Cable89/tesla-driver/01_Documentation/Forenklet skjema/Spolerigg3_r.pdf

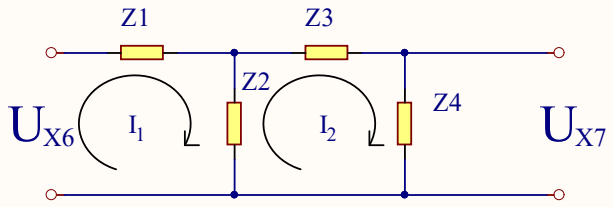
[picture p2: figure]
