Cable89/tesla-driver/01_Documentation/Figurer/IMG_20141220_205741.jpg

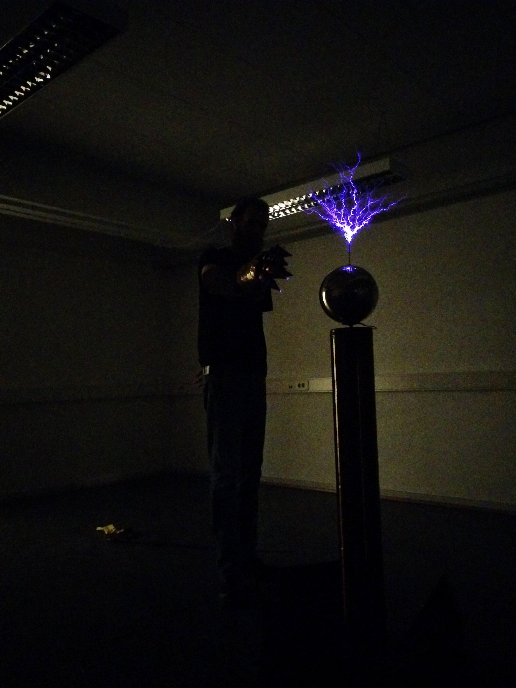
01_Documentation/Figurer/IMG_20141220_205741.jpg
