Cable89/tesla-driver/01_Documentation/Figurer/IMG_20170201_172204.jpg

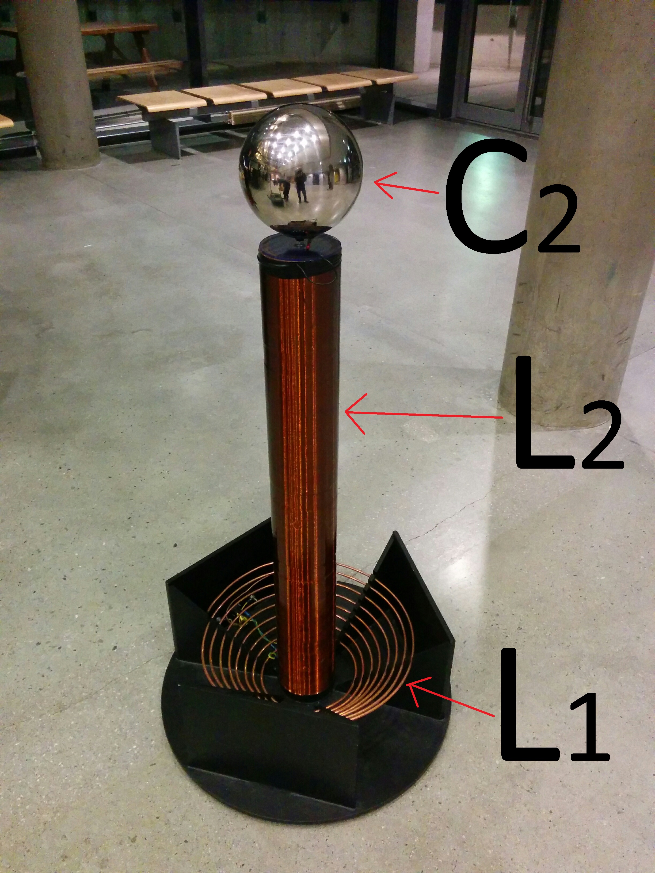
01_Documentation/Figurer/IMG_20170201_172204.jpg
