Cable89/tesla-driver/01_Documentation/Figurer/TK514_Interrupter.png

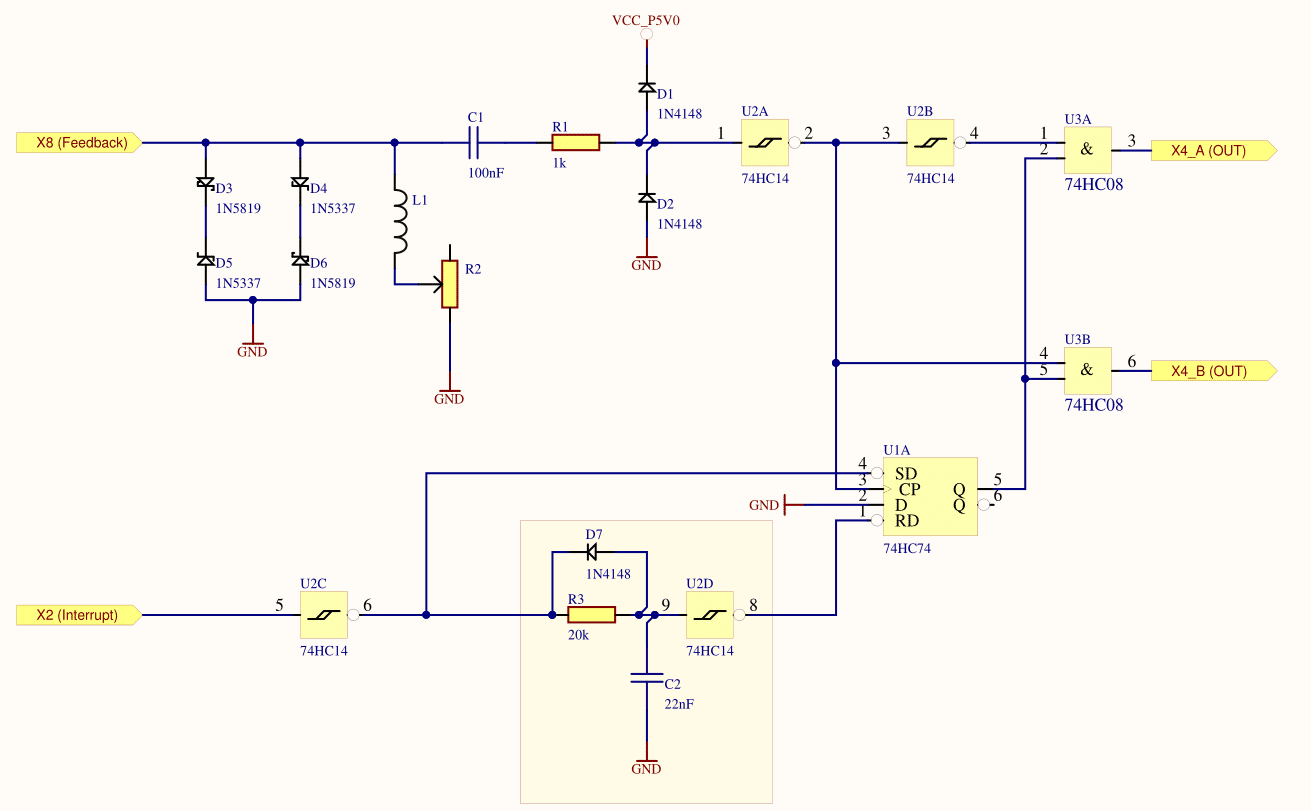
01_Documentation/Figurer/TK514_Interrupter.png
