Cable89/tesla-driver/01_Documentation/Målinger/IMG_20160618_142037.jpg

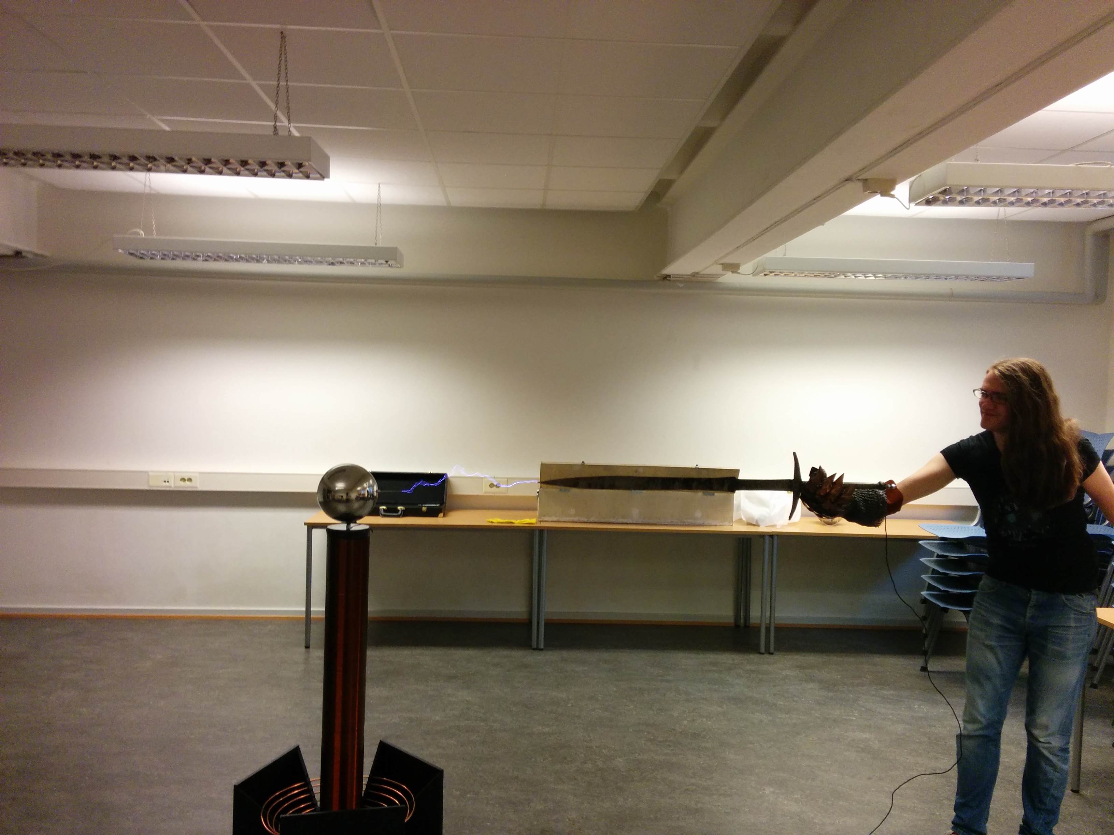
01_Documentation/Målinger/IMG_20160618_142037.jpg
