Cable89/tesla-driver/01_Documentation/Målinger/IMG_20160618_151454.jpg

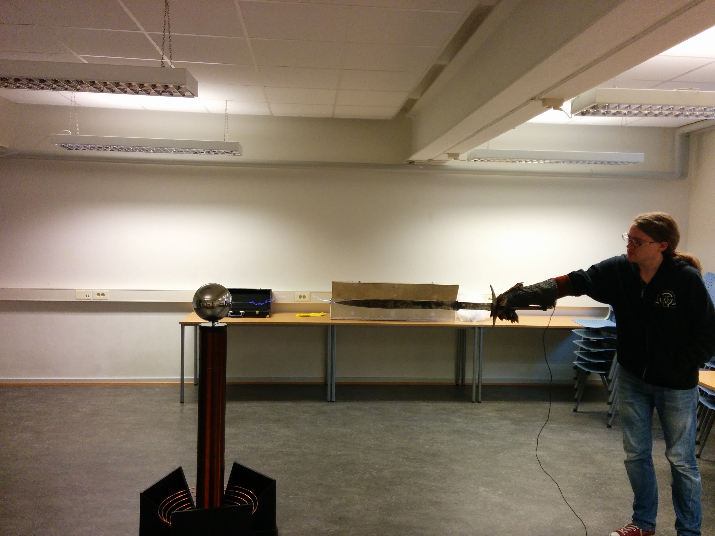
01_Documentation/Målinger/IMG_20160618_151454.jpg
