Cable89/tesla-driver/05_Hardware/TK500_Driver/TK500_Driver/Project Outputs/TK500_BOM.PDF

Line # | id | navn | Description | Designator | ModuleAssembly | Quantity | produsent | leverandor | leverandor_varenr | Manufacturer 1 | Manufacturer Part Number 1 | Manufacturer Lifecycle 1 | Supplier 1 | Supplier Part Number 1 | Supplier Unit Price 1 | Supplier Subtotal 1
| 4153 | 100nF | 2kV(kanskje) polypropylene film
| | | capacitor, D22, L50 | C1, C2, C3, C4 | TK532_Kondensatorkort.P
| | | | | cbDoc | | 4 Cornell
| | | | | | | Dubilier | Farnell | 2347676
5152 | 100nF | X7R 50V 5% | C1, C2, C3, C4, C5, C6, C7, C8, C9, C10, C11, C12, C53000 | TK513_Limiter.PcbDoc, TK514_Interrupter.PcbDoc , TK516_LINREG-PSU.PcbDoc, TK512_Optisk_Mottaker.P cbDoc, TK530_Kraftbakplan.PcbD oc | 22 Multicomp | Farnell | 1759122
3290 | 330uF | 25V elektrolytt | C1, C6 | TK516_LINREG-PSU.PcbDoc | 6 Rubycon | Farnell | 2346202
3687 | 1nF | X7R 50V 5% | C2, C3, C4 | TK513_Limiter.PcbDoc, TK512_Optisk_Mottaker.P cbDoc | 3 Multicomp | Farnell | 2310598
3316 | 220nF | X7R 25V 10% | C2, C8 | TK516_LINREG-PSU.PcbDoc | 6 Samsung | Farnell | 3013426
5154 | 1uF | X7R 50V | C2, C10, C11 | TK512_Optisk_Mottaker.P cbDoc, TK514_Interrupter.PcbDoc | 3 Multicomp | Farnell | 1759454
5155 | 47pF | NP0 50V 5% | C3 | TK512_Optisk_Mottaker.P cbDoc | 1 WALSIN | Farnell | 2496905
4164 | 4.7uF | X5R 10V 10% | C4 | TK516_LINREG-PSU.PcbDoc | 3 Samsung | Farnell | 3013462
3114 | 10uF | X5R 6.3V 10% | C5 | TK516_LINREG-PSU.PcbDoc | 3 | Farnell | 2320852
5303 | 1uF | X7R 50V 10% | C5 | TK512_Optisk_Mottaker.P cbDoc | 1 Murata | Farnell | 1735541
4858 | 100uF | 25V 2.5mm pitch | C6 | TK512_Optisk_Mottaker.P cbDoc, TK513_Limiter.PcbDoc | 2 Panasonic | Farnell | 1848439
4844 | 2200uF | 6.3V, Elektrolytt, 5mm lead spacing | C7 | TK516_LINREG-PSU.PcbDoc | 3 Multicomp | Farnell | 2627680
5192 | 22uF | 10V 10% Tantalum | C7 | TK512_Optisk_Mottaker.P cbDoc, TK513_Limiter.PcbDoc | 2 Kemet | Farnell | 1457420
5059 | 10uF | X5R 50V 10% | C13, C14 | TK514_Interrupter.PcbDoc | 2 Murata | Farnell | 2672214
3491 | 22nF | X7R 50V | C15 | TK514_Interrupter.PcbDoc | 1 Multicomp | Farnell | 1414682
3076 | MAL209636222E3 | CAP, ALUELEC, 2200UF, 400V | C52500 | dummy.PcbDoc | 1 Vishay | Farnell | 2342176 | Vishay BCcomponents | MAL209636222E3 | Volume Production | Farnell | 2342176 | 59.86 | 59.86
4891 | 15ETX06 | DIODE, HYPERFAST, 15A, 600V | D1, D2 | TK531_Utgangstrinn.PcbD oc | 4 Vishay | Farnell | 8656991 | Vishay Semiconductors | 15ETX06 | Obsolete
5238 | 1N5819 | Schottkydiode, 1A, 40V | D1, D2, D3, D4, D6 | TK513_Limiter.PcbDoc, TK514_Interrupter.PcbDoc | 6 Multicomp | Farnell | 7429304, 1336533 | Multicomp | 1N5819 | Volume Production
4485 | 1N4148 SMD | SMD signaldiode | D1, D2, D7 | TK514_Interrupter.PcbDoc , TK512_Optisk_Mottaker.P cbDoc | 4 Taiwan Semiconduct or | Farnell | 8150206
5138 | Grønn LED 5mm | LED, Green, 5mm, 572 nm, 2.1 V, 20mA, 150mcd | D1, D3, D4, D6, D7, D9, D10, D12, D13, D15, D16, D18 | TK502_Frontpanel_LEDs.Pc bDoc | 12 Multicomp | Farnell | 2112108
5143 | SMD LED Red | SMD | D1, D3, D51000, D51001, D51002, D51003, D51004, D51005, D51006, D51007, D51008, D51009, D51010, D53000, D53001, D53002 | TK512_Optisk_Mottaker.P cbDoc, TK516_LINREG-PSU.PcbDoc, TK510_Signalbakplan.PcbD oc, TK530_Kraftbakplan.PcbD oc | 19 Avago | Farnell | 8554641
5305 | Rød LED 5mm | LED, Red, 5mm, 643 nm, 1.8 V, 20mA, 400 mcd | D2, D5, D8, D11, D14, D17 | TK502_Frontpanel_LEDs.Pc bDoc | 6 Multicomp | Farnell | 2112111
3261 | 1V5KE400A | TVS diode, 400V, 1500W | D3, D4 | TK531_Utgangstrinn.PcbD oc | 4 Fairchild | Farnell | 1017630 | ON Semiconductor / Fairchild | 1V5KE400A | Volume Production
3264 | 1N5337 | Zenerdiode 4.7V 5W | D4, D5 | TK514_Interrupter.PcbDoc | ON 2 Semiconduct or | Farnell | 9557946
4876 | 1N4744A | Zenerdiode 15V 1.3W | D5, D6, D7, D8 | TK531_Utgangstrinn.PcbD oc | 8 Vishay | Farnell | 1612369 | Vishay Semiconductors | 1N4744A | Volume Production | Farnell | 1612368 | 0.12722 | 1.02
3322 3117 5314 | GBJ2504 LED Rød SMBJ5.0A-TR | diodebro/Likeretterbro 400V 25A Farget LED, 5mm Transient Voltage Suppressor, TVS, Transil SMBJ Series, Unidirectional, 5 V, SMD, 2, 6.4 V | D52500 D52501 D53003 | dummy.PcbDoc dummy.PcbDoc TK530_Kraftbakplan.PcbD oc | 1 1 -1 ST Microelectron ics | Farnell Farnell | 1651042 9886311 | STMicroelectronic s | SMBJ5.0A-TR | Volume Production | Farnell | 9886311 | 0.52175 | 2.61
5311 2977 | MC36214 Automatsikring | FUSE, PTC RESET, SMD, 16V, 500MA 2-Pol | F53000, F53001 F1 | TK530_Kraftbakplan.PcbD dummy.PcbDoc oc | 1 ABB 2 Multicomp | Farnell Farnell | 2492800 1861181 | Multicomp | MC36214 | Volume Production
3037 | PCIeX1-GF-2D-1000-1K-O36 | PCI express PCB kortkankonnektor | J1 | TK511_Blindkort.PcbDoc, TK512_Optisk_Mottaker.P cbDoc, TK513_Limiter.PcbDoc, TK514_Interrupter.PcbDoc , TK516_LINREG-PSU.PcbDoc | 8 PCB feature
3221 | MPTC-02-16-02-01-03-L-RA-SD | SAMTEC Connector | J1 | TK531_Utgangstrinn.PcbD oc, TK532_Kondensatorkort.P cbDoc | 3 SAMTEC | Mouser | MPTC-02-16-02-01-03-L-RA-SD | Samtec | MPTC-02-16-02-01-03-L-RA-SD | | Mouser | 200-MPTC0216213LRASD | 8.62 | 25.86
4473 | B3B-XH-A (LF)(SN) | JST 3pin (pris pr. stk.) | J1, J2, J3, J4, J5, J6 | TK502_Frontpanel_LEDs.Pc bDoc | 6 JST | Farnell | 1516277 | JST | B3B-XH-A(LF)(SN) | Volume Production | RSCompone nts | 8201557 | 0.388 | 2.33
3259 | Header 2X17 Shrouded | Header | J2, J7, J51027 | TK511_Blindkort.PcbDoc, TK502_Frontpanel_LEDs.Pc bDoc, TK510_Signalbakplan.PcbD oc | 4 Amphenol | Farnell | 2215313
5095 3222 | Header 1x3 PCI_Express-36P | 2,54mm pitch PCI_Express-36P | J3, J4, J5, J6, J7 J51000, J51001, J51002, J51003, J51004, J51005, J51007, J51008, J51028 | TK511_Blindkort.PcbDoc TK510_Signalbakplan.PcbD oc | 10 SAMTEC 9 FCI | Farnell Farnell | 3690124 1144435
4043 | B2B-XH-A (LF)(SN) | JST 2pin (pris pr. stk.) | J51006, J51012, J51013, J51014, J51015, J51016, J51017, J51021, J51022, J51023, J51024, J51025, J51026, J51029, J51030, J51031, J51032, J51033, J51034, J51035, J51036, J51037, J51038, J51039, J51040, J51041, J51042, J51043, J51044, J51045, J51046, J51047, J51048, J51049, J51050, J52001, J53006, J53008 | TK510_Signalbakplan.PcbD oc, TK520_GDT-Trafo.PcbDoc, TK530_Kraftbakplan.PcbD oc | 38 JST | Farnell | 1516276 | JST | B2B-XH-A(LF)(SN) | Volume Production | RSCompone nts | 8201554 | 0.204 | 7.75
3224 | Header 2X5 Shrouded | Header | J51009, J51010, J51011, J51018, J51019, J51020, J53007 | TK510_Signalbakplan.PcbD oc, TK530_Kraftbakplan.PcbD oc | 7 Amphenol | Farnell | 2215304
3046 | B4B-XH-A (LF)(SN) | JST 4pin (pris pr. stk.) | J52000, J52002, J53003, J53004, J53005 | TK520_GDT-Trafo.PcbDoc, TK530_Kraftbakplan.PcbD oc | 5 JST | Farnell | 1516278 | JST | B4B-XH-A -LF-SN
3220 | MPSC-02-16-02-7.70-03-L-V-LC | SAMTEC Connector | J53000, J53001, J53002 | TK530_Kraftbakplan.PcbD oc | 3 SAMTEC | Mouser | MPSC-02-16-02-7.70-03-L-V-LC | Samtec | MPSC-02-16-02-7.70-03-L-V-LC | | Mouser | 200-C02160277003LVLC | 9.91 | 29.73
3646 | 0R | 0.1W 1% Thick film resistor, Jumper | JP1, R3, R4, R13, R14, R23, R24 | TK516_LINREG-PSU.PcbDoc, TK502_Frontpanel_LEDs.Pc bDoc, TK512_Optisk_Mottaker.P cbDoc | 10 multicomp | Farnell | 2447060
3272 | DIN-Rele 5V | Coil: 5VDC, Contact: 250VAC 6A, DIN mount | K1, K52501 | dummy.PcbDoc | 2 ABB | Farnell | 1895933
2948 6201 | Kontaktor Spole 15H | Industriellt rele Wirewound Inductor, 15 µH, 2.8 ohm, 20 MHz, 130mA | K2 L1 | dummy.PcbDoc TK512_Optisk_Mottaker.P cbDoc, TK514_Interrupter.PcbDoc | 1 IMO 2 TDK | Farnell Farnell | 9940480 2747875
3842 4718 | Skilletrafo 2:1 SK-454-75-SA | Skilletrafo Ringkjerne Heatsink | L52501 M1 | dummy.PcbDoc TK531_Utgangstrinn.PcbD oc | 1 Hammond 2 FischerElektr onik | Farnell Farnell | 2546942 1850030
3273 | Lask til 2.5mm2 Rekkeklemme 10way | Jumper (Busbar), Cross Jumper, DIN Rail Screw Clamp Terminal Blocks, 10 Ways | M1, M2 | dummy.PcbDoc | 2 Multicomp | Farnell | 2061384
6258 | Automasjonsbryter holder | Assembly Hardware, Siemens 3-Way Modules, Holder, SIRIUS ACT 3SU Series | M3, M4, M5, M6, M7 | dummy.PcbDoc | 5 Siemens | Farnell | 2695729
3242 | KortStøtte 84mm | Støtter kort i bakplan | M51000, M51001, M51002, M51003, M51004, M51005, M51006, M51007, M51008, M51009, M51010, M51011, M51012, M51013, M51014, M51015, M51016, M51017 | TK510_Signalbakplan.PcbD oc | 18
4028 | KortStøtte 50mm | Støtter kort i bakplan | M53000, M53001, M53002, M53003, M53004, M53005 | TK530_Kraftbakplan.PcbD oc | 6
4877 | G4PC50W | IGBT, 600V, 55A | Q1, Q2 | TK531_Utgangstrinn.PcbD oc | 4 International Rectifier | Farnell | 8650632 | International Rectifier | G4PC50W
3085 | BSH201 | P-Channel MOSFET 300mA | Q1, Q2, Q3, Q5, Q51003, Q51004, Q51005, Q51009, Q51010, Q51011, Q51016, Q51017, Q51018, Q51020, Q51021, Q53003, Q53004, Q53005 | TK514_Interrupter.PcbDoc , TK513_Limiter.PcbDoc, TK512_Optisk_Mottaker.P cbDoc, TK510_Signalbakplan.PcbD oc, TK530_Kraftbakplan.PcbD oc | NXP 19 Semiconduct ors | Farnell | 1758073 | NXP Semiconductors | BSH201
3075 | 2N7002 | N-Channel MOSFET 300mA | Q1, Q4, Q51000, Q51001, Q51002, Q51006, Q51007, Q51008, Q51012, Q51013, Q51014, Q51015, Q51019, Q53000, Q53001, Q53002 | TK513_Limiter.PcbDoc, TK512_Optisk_Mottaker.P cbDoc, TK510_Signalbakplan.PcbD oc, TK530_Kraftbakplan.PcbD oc | 16 Nexperia, [NoParam] | Farnell | 1829184 | NXP Semiconductors | 2N7002
5228 | 560R | 0.1W 1% Thick film resistor | R1 | TK516_LINREG-PSU.PcbDoc | 3 Multicomp | Farnell | 2447397
3890 | 10 | 0.25W 1% Generic resistor | R1, R2 | TK531_Utgangstrinn.PcbD oc | 4 Multicomp | Farnell | 9341145
6251 | 100R | 100Ohm, 100W Resistor, Solder Lug, Wirewound +-5% 1.9kV | R1, R2 | dummy.PcbDoc | 2 TT electronics | Farnell | 1768214
5264 | 10k | 0.1W 1% Thick film resistor | R1, R2, R11, R12, R21, R22, R51000, R51001, R51002, R51003, R51004, R51005, R51006, R51010, R51011, R51012, R51013, R51014, R51015, R51016, R51017, R51021, R51022, R51023, R51024, R51025, R51026, R51027, R51028, R51029, R51030, R51031, R51032, R51033, R51034, R51035, R51036, R51037, R51038, R51039, R51040, R51041, R51042, R51043, R53000, R53001, R53002, R53006 | TK502_Frontpanel_LEDs.Pc bDoc, TK512_Optisk_Mottaker.P cbDoc, TK510_Signalbakplan.PcbD oc, TK530_Kraftbakplan.PcbD oc | 49 Multicomp | Farnell | 2447230
5339 | 1k | 0.1W 1% Thick film resistor | R1, R3 | TK513_Limiter.PcbDoc, TK514_Interrupter.PcbDoc | 3 Multicomp | Farnell | 2447272
5040 | 10R | 0.1W 1% Thick film resistor | R2 | TK514_Interrupter.PcbDoc | 1 Multicomp | Farnell | 2447556
5657 5343 | 10R 330R | 0.1W 1% Thick film resistor 0.1W 1% Thick film resistor | R2 R2, R5, R6, R7, R8, R9, R10, R15, R16, R17, R18, R19, R20, R25, R26, R27, R28, R29, R30, R51007, R51008, R51009, R51018, R51019, R51020, R51044, R51045, R51046, R51047, R51048, R51049 | TK513_Limiter.PcbDoc TK512_Optisk_Mottaker.P cbDoc, TK502_Frontpanel_LEDs.Pc bDoc, TK510_Signalbakplan.PcbD oc | 1 Multicomp 32 Multicomp | Farnell Farnell | 2447233 2447339
5336 | 910R | 0.1W 1% Thick film resistor | R3 | TK512_Optisk_Mottaker.P cbDoc | 1 Multicomp | Farnell | 2447448
5340 | 1M | 0.1W 1% Thick film resistor | R3, R4, R6, R7, R8, R9 | TK531_Utgangstrinn.PcbD oc, TK514_Interrupter.PcbDoc | 8 Multicomp | Farnell | 2073358
5357 | 20k | 0.1W 1% Thick film resistor | R3, R6 | TK514_Interrupter.PcbDoc , TK512_Optisk_Mottaker.P cbDoc | 2 Multicomp | Farnell | 2447293
3823 3778 | Trimmepot 100ohm 100k | 15 turn, horizontal 0.1W 1% Thick film resistor | R4, R5 R4 | TK514_Interrupter.PcbDoc TK513_Limiter.PcbDoc , TK513_Limiter.PcbDoc | 1 Multicomp 2 Bourns | Farnell Farnell | 2447226 9352279
5347 | 15k | 0.1W 1% Thick film resistor | R5 | TK512_Optisk_Mottaker.P cbDoc | 1 Multicomp | Farnell | 2447226
3759 4889 | 16k 47R | 0.25W 1% Generic resistor 0.1W 1% Thick film resistor | R52502 R53003, R53004, R53005 | dummy.PcbDoc TK530_Kraftbakplan.PcbD oc | 1 3 Multicomp | Farnell | 2447378
6252 | Automasjonsvelger Grønn | Switch Actuator, Siemens 22mm Pushbutton Switches | S1, S3 | dummy.PcbDoc | 2 Siemens | Farnell | 2695623
6257 | Automasjonsbryter NO | Contact Block, SPST-NO, 10 A, 500 V, 1 Pole, 3SU Series, Screw | S1, S3, S3B, S3C | dummy.PcbDoc | 4 Siemens | Farnell | 2695771
6253 | Automasjonsvelger Rød | Switch Actuator, Siemens 22mm Pushbutton Switches | S2 | dummy.PcbDoc | 1 Siemens | Farnell | 2695622
6256 | Automasjonsbryter NC | Contact Block, SPST-NC, 10 A, 500 V, 1 Pole, 3SU Series, Screw | S2, S3B, S4, S4B, S5, S5B | dummy.PcbDoc | 6 Siemens | Farnell | 2695772
6255 | Automasjonsvelger Nødstopp | Switch Actuator, Siemens 22mm Emergency Stop Mushroom Pushbutton Switches | S4 | dummy.PcbDoc | 1 Siemens | Farnell | 2695631
6254 | Automasjonsvelger Vrider bistabil | Switch Actuator, Siemens 22mm Selector Switches | S5 | dummy.PcbDoc | 1 Siemens | Farnell | 2695653
3215 5093 | SD250-3 Header 1x1 | Dual gate drive transformer 2,54mm pitch | T52000, T52001 TP1, TP2, TP3, TP4, TP5, TP6, TP7, TP8 | TK520_GDT-Trafo.PcbDoc TK512_Optisk_Mottaker.P cbDoc, TK513_Limiter.PcbDoc, TK514_Interrupter.PcbDoc | 2 Coilcraft 19 | | | Coilcraft | SD250-3
3211 | 74HC74 | Dual D flip flop | U1 | TK513_Limiter.PcbDoc, TK514_Interrupter.PcbDoc | 2 Texas Instruments | Farnell | 9591680 | Texas Instruments | 74HC74
4338 | LM7812 | Voltage Regulator | U1 | TK516_LINREG-PSU.PcbDoc | 3 Fairchild | Farnell | 1467365
4400 | 74HC14 | Hex Schmitt trigger | U1, U2, U7 | TK512_Optisk_Mottaker.P cbDoc, TK514_Interrupter.PcbDoc | ON 3 Semiconduct or | Farnell | 1607772
3241 | LM311 | Comparator, High Speed | U2 | TK513_Limiter.PcbDoc | 1 Texas Instruments | Farnell | 2293183 | Texas Instruments | LM311 | Volume Production
3342 | LM78L05 | Voltage Regulator | U2 | TK516_LINREG-PSU.PcbDoc | 3 Onsemi | Farnell | 9666095
3665 | 74HCT1G125GW-Q100H | Buffer/ Line Driver, 74HCT1G125, 4.5 V to 5.5 V, TSSOP-5 | U2, U3 | TK512_Optisk_Mottaker.P cbDoc | NXP 2 Semiconduct ors | Farnell | 1105927 | Nexperia | 74HCT1G125GW-Q100H | | Mouser | 77174HCT1G125GWQ100 H | 0.47 | 0.94
6202 | DBLS207G RDG | Bridge Rectifier, Dual-In-Line, Single Phase, 1 kV, 2 A | U3 | TK516_LINREG-PSU.PcbDoc | Taiwan 3 Semiconduct or | Farnell | 3519283 | Taiwan Semiconductor | DBLS207G RDG | | Farnell | 3519283 | 1.09 | 3.27
3238 | 74HC08 | Quad And Gate | U3, U4 | TK514_Interrupter.PcbDoc | 2 Toshiba | Farnell | 9590986 | Toshiba | 74HC08
3223 | MIC4422YM | Mosfet Driver | U5, U6 | TK514_Interrupter.PcbDoc | 2 Microchip | Farnell | 2510119 | Microchip | MIC4422YM | Volume Production | RSCompone nts | 1770411 | 1.96 | 186.58
3444 | MOCD207R2M | Dual Optocoupler | U51000 | TK510_Signalbakplan.PcbD oc | 1 Fairchild | Farnell | 1086672 | ON Semiconductor / Fairchild | MOCD207R2M | Volume Production
3304 | Rekkeklemme 2.5mm2 | DIN Rail mount terminal block | X1.1, X1.10, X1.11, X1.12, X1.13, X1.14, X1.15, X1.16, X1.17, X1.18, X1.19, X1.2, X1.20, X1.21, X1.22, X1.26, X1.27, X1.3, X1.4, X1.5, X1.6, X1.7, X1.8, X1.9 | dummy.PcbDoc | 24 Multicomp | Farnell | 2061376
