Cable89/tesla-driver/05_Hardware/TK500_Driver/TK500_Driver/Project Outputs/BOM/Bill of Materials-TK500_Driver_annotated_oysm.xlsx

Sheet: Bill of Materials-TK500_Driver
Line # | id | navn | Description | Designator | ModuleAssembly | Quantity | produsent | leverandor | leverandor_varenr | Manufacturer 1 | Manufacturer Part Number 1 | Manufacturer Lifecycle 1 | Supplier 1 | Supplier Part Number 1 | Supplier Unit Price 1 | Supplier Subtotal 1 | Lagt i bestillingsliste | Plukket fra OV
 | 4153 | 100nF | 2kV(kanskje) polypropylene film capacitor, D22, L50 | C1, C2, C3, C4 | TK532_Kondensatorkort.PcbDoc | 4 | Cornell Dubilier | Farnell | 2347676 |  |  |  |  |  |  |  | plukke fra Teslakom
 | 5152 | 100nF | X7R 50V 5% | C1, C2, C3, C4, C5, C6, C7, C8, C9, C12, C53000 | TK513_Limiter.PcbDoc, TK514_Interrupter.PcbDoc, TK516_LINREG-PSU.PcbDoc, TK530_Kraftbakplan.PcbDoc | 18 | Multicomp, Multikomp | Farnell | 1759122 |  |  |  |  |  |  |  | 100
 | 3290 | 330uF | 25V elektrolytt | C1, C6 | TK516_LINREG-PSU.PcbDoc | 6 | Rubycon | Farnell | 2346202 |  |  |  |  |  |  |  | 10
 | 5154 | 1uF |  | C2 | TK512_Optisk_Mottaker.PcbDoc | 3 | Multicomp | Farnell | 1759454 |  |  |  |  |  |  |  | 5
 | 3687 | 1nF | X7R 50V 5% | C2, C3 | TK513_Limiter.PcbDoc | 2 | Multicomp | Farnell | 2310598 |  |  |  |  |  |  |  | 10
 | 3316 | 220nF | X7R 25V 10% | C2, C8 | TK516_LINREG-PSU.PcbDoc | 6 | Samsung | Farnell | 3013426 |  |  |  |  |  |  |  | 10
 | 5155 | 47pF |  | C3 | TK512_Optisk_Mottaker.PcbDoc | 1 | WALSIN | Farnell | 2496905 |  |  |  |  |  |  |  | 10
 | 3687 | 1nF |  | C4 | TK512_Optisk_Mottaker.PcbDoc | 1 | Multicomp | Farnell | 2310598 |  |  |  |  |  |  |  | dupe
 | 4164 | 4.7uF | X5R 10V 10% | C4 | TK516_LINREG-PSU.PcbDoc | 3 | Samsung | Farnell | 3013462 |  |  |  |  |  |  |  | 5
 | 3114 | 10uF | X5R 6.3V 10% | C5 | TK516_LINREG-PSU.PcbDoc | 3 |  | Farnell | 3013454 |  |  |  |  |  |  |  | 10
 | 5303 | 1uF |  | C5 | TK512_Optisk_Mottaker.PcbDoc | 1 | Murata | Farnell | 2688485 |  |  |  |  |  |  |  | 10
 | 4858 | 100uF |  | C6 | TK512_Optisk_Mottaker.PcbDoc | 1 | Panasonic | Farnell | 1848439 |  |  |  |  |  |  |  | 5
 | 4858 | 100uF | 25V 2.5mm pitch | C6 | TK513_Limiter.PcbDoc | 1 | Panasonic | Farnell | 1848439 |  |  |  |  |  |  |  | dupe
 | 4844 | 2200uF | 6.3V, Elektrolytt, 5mm lead spacing | C7 | TK516_LINREG-PSU.PcbDoc | 3 | Multicomp | Farnell | 2627680 |  |  |  |  |  |  |  | 10
 | 5192 | 22uF |  | C7 | TK512_Optisk_Mottaker.PcbDoc | 1 | Kemet | Farnell | 1457420 |  |  |  |  |  |  |  | 5
 | 5192 | 22uF | 10V 10% Tantalum | C7 | TK513_Limiter.PcbDoc | 1 | Kemet | Farnell | 1457420 |  |  |  |  |  |  |  | plukke fra Teslakom
 | 5152 | 100nF |  | C8, C9, C10, C11 | TK512_Optisk_Mottaker.PcbDoc | 4 | Multicomp | Farnell | 1759122 |  |  |  |  |  |  |  | dupe
 | 5154 | 1uF | X7R 50V | C10, C11 | TK514_Interrupter.PcbDoc | 0 | Multikomp | Farnell | 1759454 |  |  |  |  |  |  |  | dupe
 | 5059 | 10uF | X5R 50V 10% | C13, C14 | TK514_Interrupter.PcbDoc | 2 | Murata | Farnell | 2672214 |  |  |  |  |  |  |  | 10
 | 3491 | 22nF | X7R 50V | C15 | TK514_Interrupter.PcbDoc | 1 | Multicomp | Farnell | 1414682 |  |  |  |  |  |  |  | 10
 | 4891 | 15ETX06 | DIODE, HYPERFAST, 15A, 600V | D1, D2 | TK531_Utgangstrinn.PcbDoc | 4 | Vishay | Farnell | 8656991 | Vishay Semiconductors | 15ETX06 | Obsolete |  |  |  |  | 4
 | 5238 | 1N5819 | Schottkydiode, 1A, 40V | D1, D2, D3, D4, D6 | TK513_Limiter.PcbDoc, TK514_Interrupter.PcbDoc | 6 | Multicomp, Multikomp | Farnell | 7429304 | Multicomp | 1N5819 | Volume Production |  |  |  |  | 6
 | 4485 | 1N4148 SMD | SMD signaldiode | D1, D2, D7 | TK514_Interrupter.PcbDoc | 4 | Taiwan Semiconductor | Farnell | 8150206 |  |  |  |  |  |  |  | 5
 | 5138 | Grønn LED 5mm | LED, Green, 5mm, 572 nm, 2.1 V, 20 mA, 150 mcd | D1, D3, D4, D6, D7, D9, D10, D12, D13, D15, D16, D18 | TK502_Frontpanel_LEDs.PcbDoc | 12 | Multicomp | Farnell | 2112108 |  |  |  |  |  |  |  | Plukke fra OV
 | 5143 | SMD LED Red |  | D1, D3, D51000, D51001, D51002, D51003, D51004, D51005, D51006, D51007, D51008, D51009, D51010 | TK512_Optisk_Mottaker.PcbDoc, TK510_Signalbakplan.PcbDoc | 19 | Avago | Farnell | 8554641 |  |  |  |  |  |  |  | 30
 | 5143 | SMD LED Red | SMD | D1, D53000, D53001, D53002 | TK516_LINREG-PSU.PcbDoc, TK530_Kraftbakplan.PcbDoc | 0 | Avago | Farnell | 8554641 |  |  |  |  |  |  |  | dupe
 | 4485 | 1N4148 SMD |  | D2 | TK512_Optisk_Mottaker.PcbDoc | 0 | Taiwan Semiconductor | Farnell | 8150206 |  |  |  |  |  |  |  | dupe
 | 5305 | Rød LED 5mm | LED, Red, 5mm, 643 nm, 1.8 V, 20 mA, 400 mcd | D2, D5, D8, D11, D14, D17 | TK502_Frontpanel_LEDs.PcbDoc | 6 | Multicomp | Farnell | 2112111 |  |  |  |  |  |  |  | Plukke fra OV
 | 3261 | 1V5KE400A | TVS diode, 400V, 1500W | D3, D4 | TK531_Utgangstrinn.PcbDoc | 4 | Fairchild | Farnell | 1017630 | ON Semiconductor / Fairchild | 1V5KE400A | Volume Production |  |  |  |  | 8
 | 3264 | 1N5337 | Zenerdiode 4.7V 5W | D4, D5 | TK514_Interrupter.PcbDoc | 2 | ON Semiconductor | Farnell | 9557946 |  |  |  |  |  |  |  | plukke fra Teslakom
 | 4876 | 1N4744A | Zenerdiode 15V 1.3W | D5, D6, D7, D8 | TK531_Utgangstrinn.PcbDoc | 8 | Vishay | Farnell | 1612369 | Vishay Semiconductors | 1N4744A | Volume Production | Farnell | 1612368 | 0.12722 | 1.02 | 20
 | 5314 | SMBJ5.0A-TR | Transient Voltage Suppressor, TVS, Transil SMBJ Series, Unidirectional, 5 V, SMD, 2, 6.4 V | D53003 | TK530_Kraftbakplan.PcbDoc | 1 | ST Microelectronics | Farnell | 9886311 | STMicroelectronics | SMBJ5.0A-TR | Volume Production | Farnell | 9886311 | 0.52175 | 2.61 | 5
 | 5311 | MC36214 | FUSE, PTC RESET, SMD, 16V, 500MA | F53000, F53001 | TK530_Kraftbakplan.PcbDoc | 2 | Multicomp | Farnell | 1861181 | Multicomp | MC36214 | Volume Production |  |  |  |  | plukke fra Teslakom
 | 3037 | PCIeX1-GF-2D-1000-1K-O36 |  | J1 | TK512_Optisk_Mottaker.PcbDoc | 1 | PCB feature |  |  |  |  |  |  |  |  |  | -
 | 3037 | PCIeX1-GF-2D-1000-1K-O36 | PCI express PCB kortkankonnektor | J1 | TK511_Blindkort.PcbDoc, TK513_Limiter.PcbDoc, TK514_Interrupter.PcbDoc, TK516_LINREG-PSU.PcbDoc | 7 | PCB feature, [NoParam] |  |  |  |  |  |  |  |  |  | -
 | 3221 | MPTC-02-16-02-01-03-L-RA-SD | SAMTEC Connector | J1 | TK531_Utgangstrinn.PcbDoc, TK532_Kondensatorkort.PcbDoc | 3 | SAMTEC | Mouser | MPTC-02-16-02-01-03-L-RA-SD | Samtec | MPTC-02-16-02-01-03-L-RA-SD |  | Mouser | 200-MPTC0216213LRASD | 8.62 | 25.86 | 2 | 1
 | 4473 | B3B-XH-A (LF)(SN) | JST 3pin (pris pr. stk.) | J1, J2, J3, J4, J5, J6 | TK502_Frontpanel_LEDs.PcbDoc | 6 | JST | Farnell | 1516277 | JST | B3B-XH-A(LF)(SN) | Volume Production | RSComponents | 8201557P | 0.541 | 3.25 | Plukke fra OV
 | 3259 | Header 2X17 Shrouded | Header | J2, J7 | TK511_Blindkort.PcbDoc, TK502_Frontpanel_LEDs.PcbDoc | 4 | Amphenol | Farnell | 2215313 |  |  |  |  |  |  |  | plukke fra Teslakom
 | 5095 | Header 1x3 | 2,54mm pitch | J3, J4, J5, J6, J7 | TK511_Blindkort.PcbDoc | 10 | SAMTEC | Farnell | 3690124 |  |  |  |  |  |  |  | Har
 | 3222 | PCI_Express-36P |  | J51000, J51001, J51002, J51003, J51004, J51005, J51007, J51008, J51028 | TK510_Signalbakplan.PcbDoc | 9 | FCI | Farnell | 1144435 |  |  |  |  |  |  |  | plukke fra Teslakom | 10
 | 4043 | B2B-XH-A (LF)(SN) |  | J51006, J51012, J51013, J51014, J51015, J51016, J51017, J51021, J51022, J51023, J51024, J51025, J51026, J51029, J51030, J51031, J51032, J51033, J51034, J51035, J51036, J51037, J51038, J51039, J51040, J51041, J51042, J51043, J51044, J51045, J51046, J51047, J51048, J51049, J51050 | TK510_Signalbakplan.PcbDoc | 35 | JST | Farnell | 1516276 | JST | B2B-XH-A(LF)(SN) | Volume Production | RSComponents | 8201554 | 0.204 | 7.14 | Plukke fra OV
 | 3224 | Header 2X5 Shrouded |  | J51009, J51010, J51011, J51018, J51019, J51020 | TK510_Signalbakplan.PcbDoc | 7 | Amphenol | Farnell | 2215304 |  |  |  |  |  |  |  | plukke fra Teslakom | 6
 | 3259 | Header 2X17 Shrouded |  | J51027 | TK510_Signalbakplan.PcbDoc | 0 | Amphenol | Farnell | 2215313 |  |  |  |  |  |  |  | dupe
 | 3046 | B4B-XH-A (LF)(SN) | JST 4pin (pris pr. stk.) | J52000, J52002, J53003, J53004, J53005 | TK520_GDT-Trafo.PcbDoc, TK530_Kraftbakplan.PcbDoc | 5 | JST | Farnell | 1516278 | JST | B4B-XH-A -LF-SN |  |  |  |  |  | Plukke fra OV
 | 4043 | B2B-XH-A (LF)(SN) | JST 2pin (pris pr. stk.) | J52001, J53006, J53008 | TK520_GDT-Trafo.PcbDoc, TK530_Kraftbakplan.PcbDoc | 3 | JST | Farnell | 1516276 | JST | B2B-XH-A(LF)(SN) | Volume Production | RSComponents | 8201554 | 0.284 | 1.42 | Plukke fra OV
 | 3220 | MPSC-02-16-02-7.70-03-L-V-LC | SAMTEC Connector | J53000, J53001, J53002 | TK530_Kraftbakplan.PcbDoc | 3 | SAMTEC | Mouser | MPSC-02-16-02-7.70-03-L-V-LC | Samtec | MPSC-02-16-02-7.70-03-L-V-LC |  | Mouser | 200-C02160277003LVLC | 9.91 | 29.73 | plukke fra Teslakom | 3
 | 3224 | Header 2X5 Shrouded | Header | J53007 | TK530_Kraftbakplan.PcbDoc | 0 | Amphenol | Farnell | 2215304 |  |  |  |  |  |  |  | dupe
 | 3646 | 0R | 0.1W 1% Thick film resistor, Jumper | JP1, R3, R4, R13, R14, R23, R24 | TK516_LINREG-PSU.PcbDoc, TK502_Frontpanel_LEDs.PcbDoc | 9 | multicomp | Farnell | 2447060 |  |  |  |  |  |  |  | 40
 | 6201 | Spole 15H |  | L1 | TK512_Optisk_Mottaker.PcbDoc | 2 | TDK | Farnell | 2747875 |  |  |  |  |  |  |  | 5
 | 6201 | Spole 15H | Wirewound Inductor, 15 µH, 2.8 ohm, 20 MHz, 130 mA | L1 | TK514_Interrupter.PcbDoc | 0 | TDK | Farnell | 2747875 |  |  |  |  |  |  |  | dupe
 | 4718 | SK-454-75-SA | Heatsink | M1 | TK531_Utgangstrinn.PcbDoc | 2 | FischerElektronik | Farnell | 1850030 |  |  |  |  |  |  |  | 2
 | 3242 | KortStøtte 84mm |  | M51000, M51001, M51002, M51003, M51004, M51005, M51006, M51007, M51008, M51009, M51010, M51011, M51012, M51013, M51014, M51015, M51016, M51017 | TK510_Signalbakplan.PcbDoc | 18 |  |  |  |  |  |  |  |  |  |  | plukke fra Teslakom | 18
 | 4028 | KortStøtte 50mm | Støtter kort i bakplan | M53000, M53001, M53002, M53003, M53004, M53005 | TK530_Kraftbakplan.PcbDoc | 6 |  |  |  |  |  |  |  |  |  |  | plukke fra Teslakom | 6
 | 4877 | G4PC50W | IGBT, 600V, 55A | Q1, Q2 | TK531_Utgangstrinn.PcbDoc | 4 | International Rectifier | Farnell | 8650632 | International Rectifier | G4PC50W |  |  |  |  |  | 4
 | 3085 | BSH201 | P-Channel MOSFET 300mA | Q1, Q2, Q3, Q53003, Q53004, Q53005 | TK514_Interrupter.PcbDoc, TK513_Limiter.PcbDoc, TK530_Kraftbakplan.PcbDoc | 19 | NXP Semiconductors | Farnell | 1758073 | NXP Semiconductors | BSH201 |  |  |  |  |  | Plukke fra OV (30)
 | 3075 | 2N7002 | N-Channel MOSFET 300mA | Q1, Q53000, Q53001, Q53002 | TK513_Limiter.PcbDoc, TK530_Kraftbakplan.PcbDoc | 16 | Nexperia, [NoParam] | Farnell | 3226401 | NXP Semiconductors | 2N7002 |  |  |  |  |  | 20
 | 3085 | BSH201 |  | Q3, Q5, Q51003, Q51004, Q51005, Q51009, Q51010, Q51011, Q51016, Q51017, Q51018, Q51020, Q51021 | TK512_Optisk_Mottaker.PcbDoc, TK510_Signalbakplan.PcbDoc | 0 | NXP Semiconductors | Farnell | 1758073 | NXP Semiconductors | BSH201 |  |  |  |  |  | dupe
 | 3075 | 2N7002 |  | Q4, Q51000, Q51001, Q51002, Q51006, Q51007, Q51008, Q51012, Q51013, Q51014, Q51015, Q51019 | TK512_Optisk_Mottaker.PcbDoc, TK510_Signalbakplan.PcbDoc | 0 | Nexperia, [NoParam] | Farnell | 1829184 | NXP Semiconductors | 2N7002 |  |  |  |  |  | dupe
 | 5228 | 560R | 0.1W 1% Thick film resistor | R1 | TK516_LINREG-PSU.PcbDoc | 3 | Multicomp | Farnell | 2447397 |  |  |  |  |  |  |  | 10
 | 3890 | 10 | 0.25W 1% Generic resistor | R1, R2 | TK531_Utgangstrinn.PcbDoc | 4 | Multicomp | Farnell | 9341145 |  |  |  |  |  |  |  | har
 | 5264 | 10k | 0.1W 1% Thick film resistor | R1, R2, R11, R12, R21, R22, R53000, R53001, R53002, R53006 | TK502_Frontpanel_LEDs.PcbDoc, TK530_Kraftbakplan.PcbDoc | 10 | Multicomp | Farnell | 2447230 |  |  |  |  |  |  |  | 30
 | 5339 | 1k | 0.1W 1% Thick film resistor | R1, R3 | TK513_Limiter.PcbDoc, TK514_Interrupter.PcbDoc | 3 | Multicomp, Multikomp | Farnell | 2447272 |  |  |  |  |  |  |  | 100
 | 5264 | 10k |  | R1, R51000, R51002, R51003, R51004, R51005, R51010, R51011, R51012, R51013, R51014, R51015, R51016, R51017, R51021, R51022, R51023, R51024, R51025, R51026, R51027, R51028, R51029, R51030, R51031, R51032, R51033, R51034, R51035, R51036, R51037, R51038, R51039, R51040, R51041, R51042, R51043 | TK512_Optisk_Mottaker.PcbDoc, TK510_Signalbakplan.PcbDoc | 37 | Multicomp | Farnell | 2447230 |  |  |  |  |  |  |  | 500
 | 5040 | 10R | 0.1W 1% Thick film resistor | R2 | TK514_Interrupter.PcbDoc | 1 | Multikomp |  |  |  |  |  |  |  |  |  | 10
 | 5657 | 10R | 0.1W 1% Thick film resistor | R2 | TK513_Limiter.PcbDoc | 1 | Multicomp | Farnell | 2447233 |  |  |  |  |  |  |  | 10
 | 5343 | 330R |  | R2, R7, R51007, R51008, R51009, R51018, R51019, R51020, R51044, R51045, R51046, R51047, R51048, R51049 | TK512_Optisk_Mottaker.PcbDoc, TK510_Signalbakplan.PcbDoc | 14 | Multicomp | Farnell | 2447339 |  |  |  |  |  |  |  | 500
 | 5336 | 910R |  | R3 | TK512_Optisk_Mottaker.PcbDoc | 1 | Multicomp | Farnell | 2447448 |  |  |  |  |  |  |  | 10
 | 5357 | 20k | 0.1W 1% Thick film resistor | R3 | TK514_Interrupter.PcbDoc | 2 |  |  |  |  |  |  |  |  |  |  | 10
 | 5340 | 1M | 0.1W 1% Thick film resistor | R3, R4, R6, R7, R8, R9 | TK531_Utgangstrinn.PcbDoc, TK514_Interrupter.PcbDoc | 8 | Multicomp, [NoParam] | Farnell, [NoParam] | 2073358, [NoParam] |  |  |  |  |  |  |  | 100
 | 3646 | 0R |  | R4 | TK512_Optisk_Mottaker.PcbDoc | 1 | multicomp | Farnell | 2447060 |  |  |  |  |  |  |  | dupe
 | 3778 | 100k | 0.1W 1% Thick film resistor | R4 | TK513_Limiter.PcbDoc | 1 | Multicomp | Farnell | 2447226 |  |  |  |  |  |  |  | 500
 | 3823 | Trimmepot 100ohm | 15 turn, horizontal | R4, R5 | TK514_Interrupter.PcbDoc, TK513_Limiter.PcbDoc | 2 | Bourns | Farnell | 9352279 |  |  |  |  |  |  |  | Plukke fra OV
 | 5347 | 15k |  | R5 | TK512_Optisk_Mottaker.PcbDoc | 1 | Multicomp | Farnell | 2447256 |  |  |  |  |  |  |  | 500
 | 5343 | 330R | 0.1W 1% Thick film resistor | R5, R6, R7, R8, R9, R10, R15, R16, R17, R18, R19, R20, R25, R26, R27, R28, R29, R30 | TK502_Frontpanel_LEDs.PcbDoc | 18 | Multicomp | Farnell | 2447339 |  |  |  |  |  |  |  | 500
 | 5357 | 20k |  | R6 | TK512_Optisk_Mottaker.PcbDoc | 0 | Multicomp | Farnell | 2447293 |  |  |  |  |  |  |  | dupe
 | 4889 | 47R | 0.1W 1% Thick film resistor | R53003, R53004, R53005 | TK530_Kraftbakplan.PcbDoc | 3 | Multicomp | Farnell | 2447378 |  |  |  |  |  |  |  | 10
 | 3215 | SD250-3 | Dual gate drive transformer | T52000, T52001 | TK520_GDT-Trafo.PcbDoc | 2 | Coilcraft |  |  | Coilcraft | SD250-3 |  |  |  |  |  | plukke fra Teslakom | 2
 | 5093 | Header 1x1 |  | TP1, TP2, TP3, TP4, TP5, TP6, TP7, TP8 | TK512_Optisk_Mottaker.PcbDoc | 8 |  |  |  |  |  |  |  |  |  |  | har
 | 5093 | Header 1x1 | 2,54mm pitch | TP1, TP2, TP3, TP4, TP5, TP6, TP7, TP8 | TK513_Limiter.PcbDoc, TK514_Interrupter.PcbDoc | 11 |  |  |  |  |  |  |  |  |  |  | har
 | 3211 | 74HC74 | Dual D flip flop | U1 | TK513_Limiter.PcbDoc, TK514_Interrupter.PcbDoc | 2 | Texas Instruments | Farnell | 9591680 | Texas Instruments | 74HC74 |  |  |  |  |  | 5
 | 4338 | LM7812 | Voltage Regulator | U1 | TK516_LINREG-PSU.PcbDoc | 3 | Fairchild | Farnell | 1467365 |  |  |  |  |  |  |  | 3
 | 4400 | 74HC14 |  | U1 | TK512_Optisk_Mottaker.PcbDoc | 3 | ON Semiconductor | Farnell | 1607772 |  |  |  |  |  |  |  | 4
 | 3241 | LM311 | Comparator, High Speed | U2 | TK513_Limiter.PcbDoc | 1 | Texas Instruments | Farnell | 2293183 | Texas Instruments | LM311 | Volume Production |  |  |  |  | 5
 | 3342 | LM78L05 | Voltage Regulator | U2 | TK516_LINREG-PSU.PcbDoc | 3 | Onsemi | Farnell | 9666095 |  |  |  |  |  |  |  | Plukke fra OV
 | 3665 | 74HCT1G125GW-Q100H |  | U2, U3 | TK512_Optisk_Mottaker.PcbDoc | 2 | NXP Semiconductors | Farnell | 3119389 | Nexperia | 74HCT1G125GW-Q100H |  | Mouser | 77174HCT1G125GWQ100H | 0.47 | 0.94 | 5
 | 4400 | 74HC14 | Hex Schmitt trigger | U2, U7 | TK514_Interrupter.PcbDoc | 0 | ON Semiconductor | Farnell | 1607772 |  |  |  |  |  |  |  | dupe
 | 6202 | DBLS207G RDG | Bridge Rectifier, Dual-In-Line, Single Phase, 1 kV, 2 A | U3 | TK516_LINREG-PSU.PcbDoc | 3 | Taiwan Semiconductor | Farnell | 3519283 | Taiwan Semiconductor | DBLS207G RDG |  | Farnell | 3519283 | 1.09 | 3.27 | 4
 | 3238 | 74HC08 | Quad And Gate | U3, U4 | TK514_Interrupter.PcbDoc | 2 | Toshiba | Farnell | 9590986 | Toshiba | 74HC08 |  |  |  |  |  | 3
 | 3223 | MIC4422YM | Mosfet Driver | U5, U6 | TK514_Interrupter.PcbDoc | 2 | Microchip | Farnell | 2510119 | Microchip | MIC4422YM | Volume Production |  |  |  |  | plukke fra Teslakom
 | 3444 | MOCD207R2M |  | U51000 | TK510_Signalbakplan.PcbDoc | 1 | Fairchild | Farnell | 1086672 | ON Semiconductor / Fairchild | MOCD207R2M | Volume Production | Farnell | 1086672 | 1.75 | 8.76 | 5
 |  |  | JST kabler |  |  |  |  |  |  |  |  |  |  |  |  |  | plukke fra Teslakom
 |  |  | Toslink receiver |  |  | 1 |  |  |  |  |  |  |  |  |  |  | plukke fra Teslakom
 |  |  | Toslink sender |  |  | 4 |  |  |  |  |  |  |  |  |  |  | plukke fra Teslakom

Sheet: BOM_TK525_Kraftforsyning
id | navn | Description | Designator | Quantity | produsent | leverandor | leverandor_varenr | Lagt i bestillingsliste | Plukket fra OV
3181 | Kontaktor | Industriellt rele | K2 | 1
3183 | Automatsikring | 2-Pol | F1 | 1
3184 | Lampe | Lampe | L52500, L52501 | 2
4058 | DIN-Rele 5V | Coil: 5VDC, Contact: 250VAC 6A, DIN mount | K1, K52501 | 2 | ABB | Farnell | 1895933 | 2
4060 | Lask til 2.5mm2 Rekkeklemme 10way | Jumper (Busbar), Cross Jumper, DIN Rail Screw Clamp Terminal Blocks, 10 Ways | M? | 2 | Multicomp | Farnell | 2061384 |  | 2
3182 | Automasjonsbryter | Kraftig | S1, S2, S3, S4, S5 | 5
4059 | Rekkeklemme 2.5mm2 | DIN Rail mount terminal block | X1.1, X1.11, X1.12, X1.13, X1.14, X1.15, X1.16, X1.17, X1.18, X1.2, X1.3, X1.4, X1.5, X1.6, X1.7, X1.8 | 16 | Multicomp | Farnell | 2061376 | Plukke fra OV

Sheet: BOM_TK525_Hovedstrom
id | navn | Description | Designator | Quantity | produsent | leverandor | leverandor_varenr | Lagt i bestillingsliste | Plukket fra OV
2783 | 100 | 0.25W 1% Generic resistor | R1 | 1
3181 | Kontaktor | Industriellt rele | K2 | 1 |  |  |  | har
3182 | Automasjonsbryter | Kraftig | S3 | 1
4059 | Rekkeklemme 2.5mm2 | DIN Rail mount terminal block | X1.10, X1.19, X1.20, X1.21, X1.22, X1.26, X1.27, X1.9 | 8 | Multicomp | Farnell | 2061376

Sheet: BOM_TK525_HVDC
id | navn | Description | Designator | Quantity | produsent | leverandor | leverandor_varenr | Lagt i bestillingsliste | Plukket fra OV
1629 | GBJ2504 | Likeretterbro | D52500 | 1 |  |  |  | Plukke fra OV
2209 | SMD LED Red |  | D52501 | 1 | Avago | Farnell | 8554641 | har
2783 | 100 | 0.25W 1% Generic resistor | R2 | 1
2836 | 16k | 0.25W 1% Generic resistor | R52502 | 1
3181 | Kontaktor | Industriellt rele | K2 | 1 |  |  |  | har
3182 | Automasjonsbryter | Kraftig | S3 | 1
3185 | MAL209636222E3 | CAP, ALU ELEC, 2200UF, 400V | C52500 | 1 | Vishay | Farnell | 2342176 | 1x 2729186
3643 | Skilletrafo 2:1 | Skilletrafo Ringkjerne | L52501 | 1 | Radiocrafts | Farnell | 2546942 | 1
