Cable89/tesla-driver/05_Hardware/TK100_Tonegenerator/TK104_Pulsbegrenser_Eurorack/TK104_Pulsbegrenser_Eurorack_frontpanel.DXF

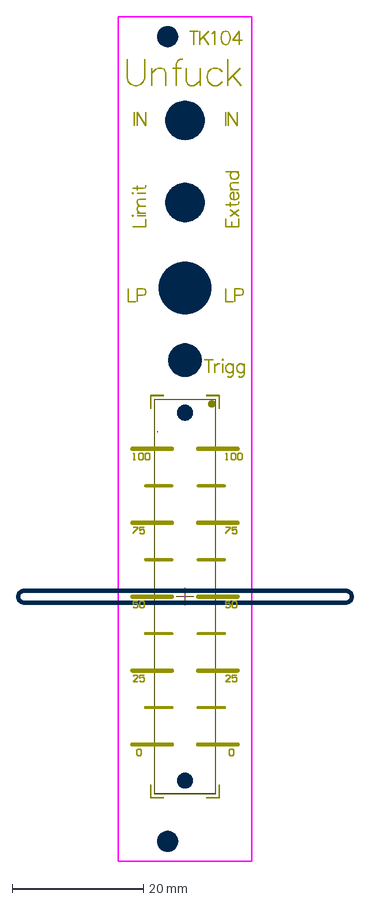
[picture p26: CAD file, 2019-02-26]
05_Hardware/TK100_Tonegenerator/TK104_Pulsbegrenser_Eurorack/TK104_Pulsbegrenser_Eurorack_frontpanel.DXF
51.4 x 128.6 mm
