Cable89/tesla-driver/06_Mechanical/TK500_Driver/ABB Circuit Breaker.SLDPRT

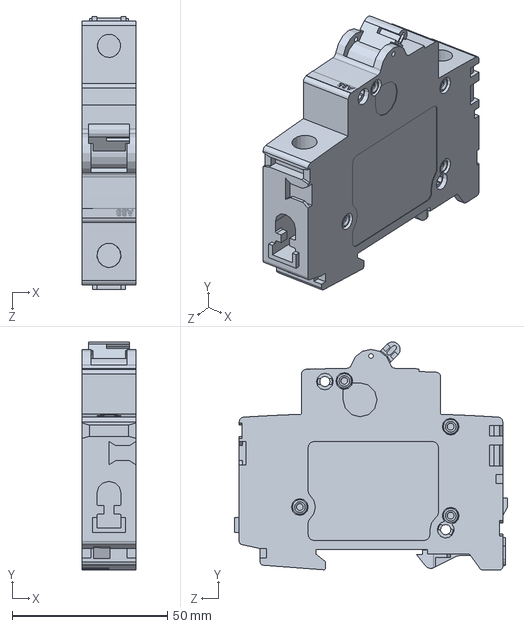
[picture p27: CAD file, 2022-05-03]
06_Mechanical/TK500_Driver/ABB Circuit Breaker.SLDPRT
17.4 x 73.4 x 87.9 mm
