Cable89/tesla-driver/06_Mechanical/TK500_Driver/Siemens/3SU1002-2BF60-0AA0.SLDPRT

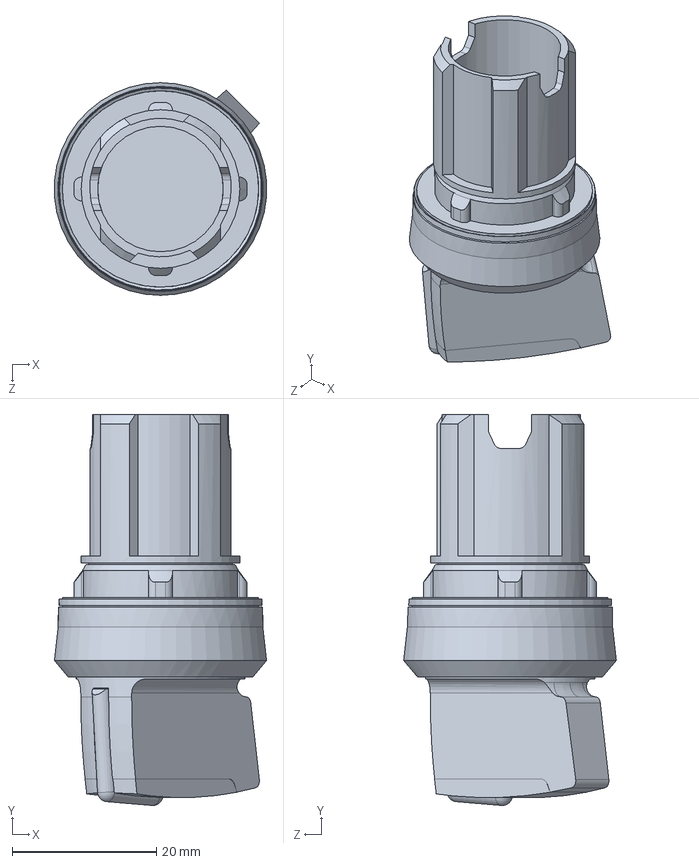
[picture p28: CAD file, 2022-05-03]
06_Mechanical/TK500_Driver/Siemens/3SU1002-2BF60-0AA0.SLDPRT
29.4 x 54.2 x 29.5 mm
