Cable89/tesla-driver/05_Hardware/TK100_Tonegenerator/TK104_Pulsbegrenser_Eurorack/PTA4543-PANEL.DXF

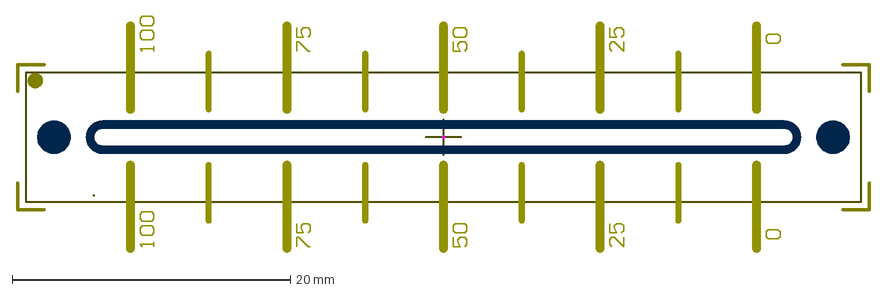
[picture p29: CAD file, 2019-02-26]
05_Hardware/TK100_Tonegenerator/TK104_Pulsbegrenser_Eurorack/PTA4543-PANEL.DXF
61.4 x 17.0 mm
