Cable89/tesla-driver/06_Mechanical/TK500_Driver/Siemens/G_NSB0_XX_90459V.stp

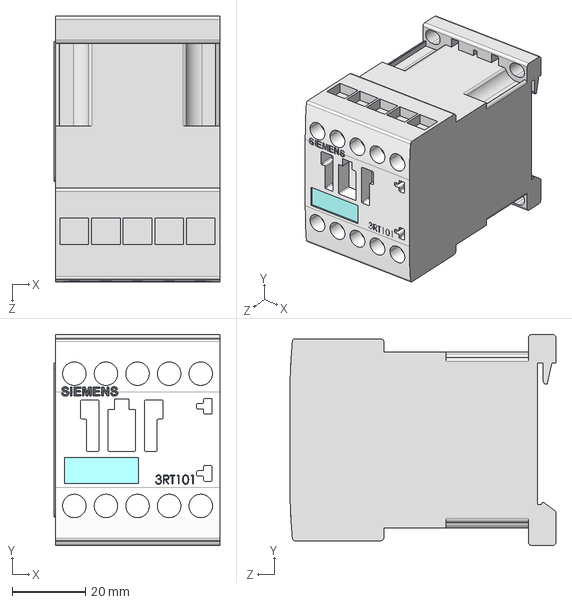
[picture p30: CAD file, 2018-04-08]
06_Mechanical/TK500_Driver/Siemens/G_NSB0_XX_90459V.stp
45.1 x 57.5 x 72.4 mm
