Cable89/tesla-driver/06_Mechanical/TK500_Driver/TK513_Limiter.SLDPRT

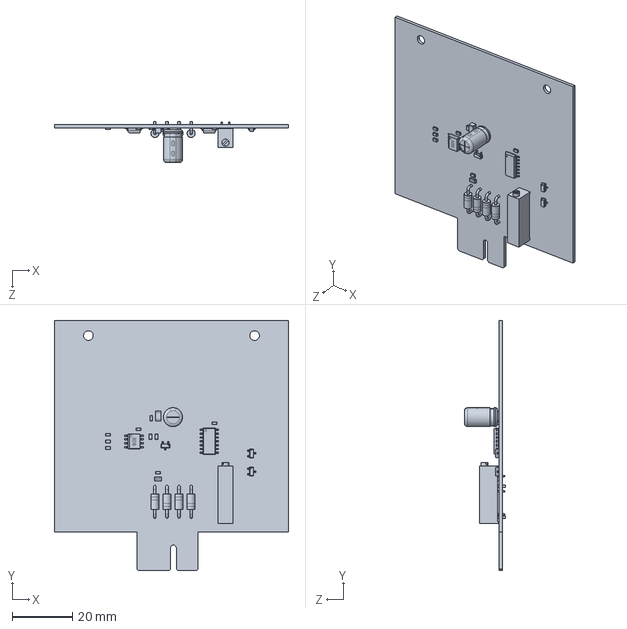
[picture p31: CAD file, 2022-05-03]
06_Mechanical/TK500_Driver/TK513_Limiter.SLDPRT
77.5 x 82.8 x 13.6 mm
