Cable89/tesla-driver/06_Mechanical/TK500_Driver/Innerbunn.SLDPRT

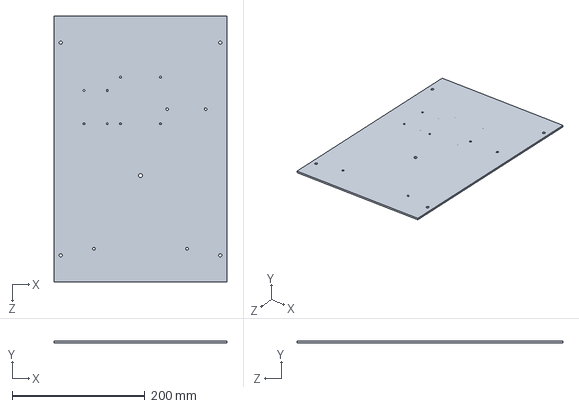
[picture p32: CAD file, 2022-05-03]
06_Mechanical/TK500_Driver/Innerbunn.SLDPRT
260.0 x 3.00 x 400.0 mm
