Cable89/tesla-driver/06_Mechanical/TK500_Driver/HFS5-2020-60.sldprt

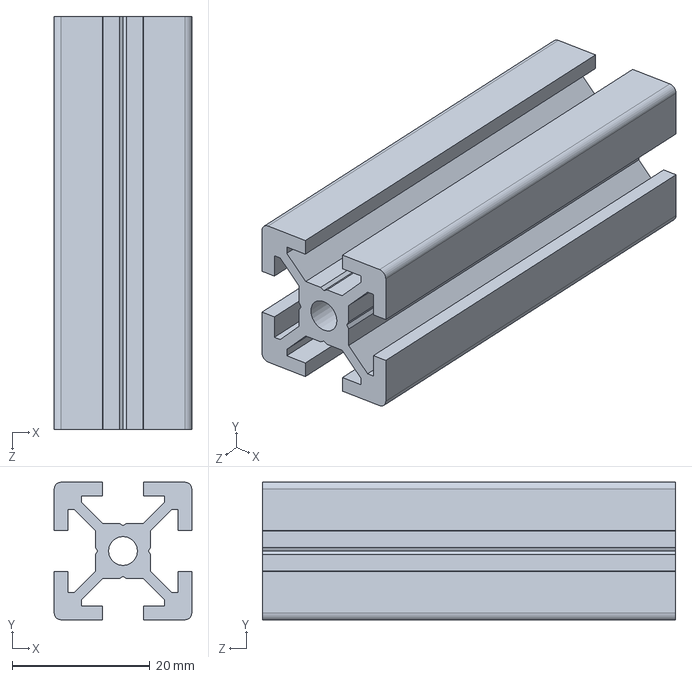
[picture p33: CAD file, 2022-05-03]
06_Mechanical/TK500_Driver/HFS5-2020-60.sldprt
20.0 x 20.0 x 60.0 mm
