Cable89/tesla-driver/06_Mechanical/TK500_Driver/HFS5-2020-400.sldprt

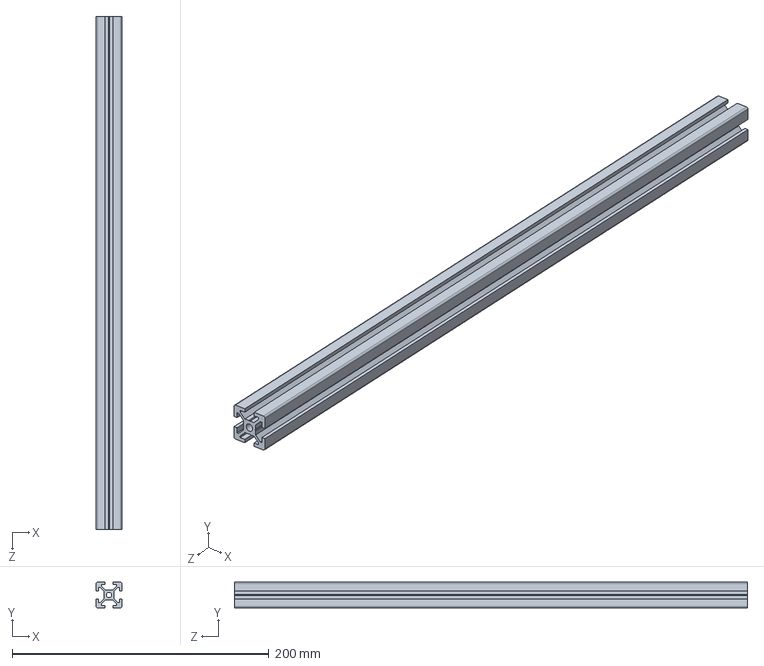
[picture p34: CAD file, 2022-05-03]
06_Mechanical/TK500_Driver/HFS5-2020-400.sldprt
20.0 x 20.0 x 400.0 mm
