Cable89/tesla-driver/06_Mechanical/TK500_Driver/Siemens/3SU1400-1AA10-1BA0.SLDPRT

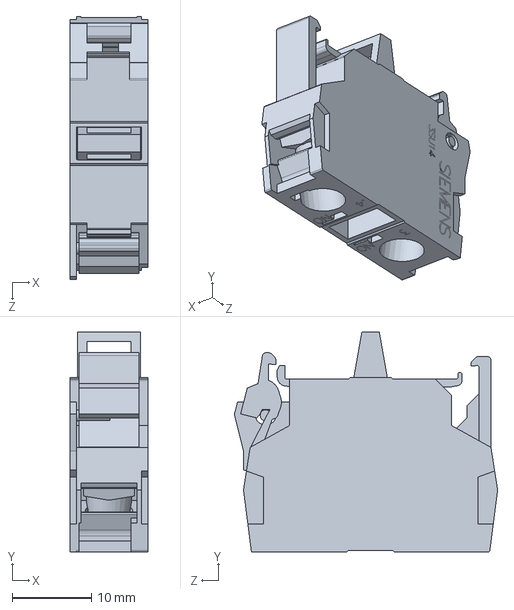
[picture p35: CAD file, 2017-03-23]
06_Mechanical/TK500_Driver/Siemens/3SU1400-1AA10-1BA0.SLDPRT
9.80 x 27.7 x 33.2 mm
