Cable89/tesla-driver/06_Mechanical/TK500_Driver/DIN-Rail_180mm.SLDPRT

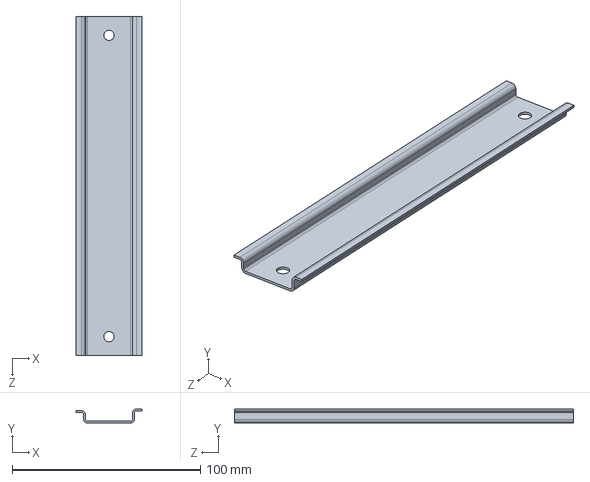
[picture p36: CAD file, 2022-05-03]
06_Mechanical/TK500_Driver/DIN-Rail_180mm.SLDPRT
35.0 x 7.50 x 180.0 mm
