Cable89/tesla-driver/06_Mechanical/TK500_Driver/Siemens/3SU1500-0AA10-0AA0.SLDPRT

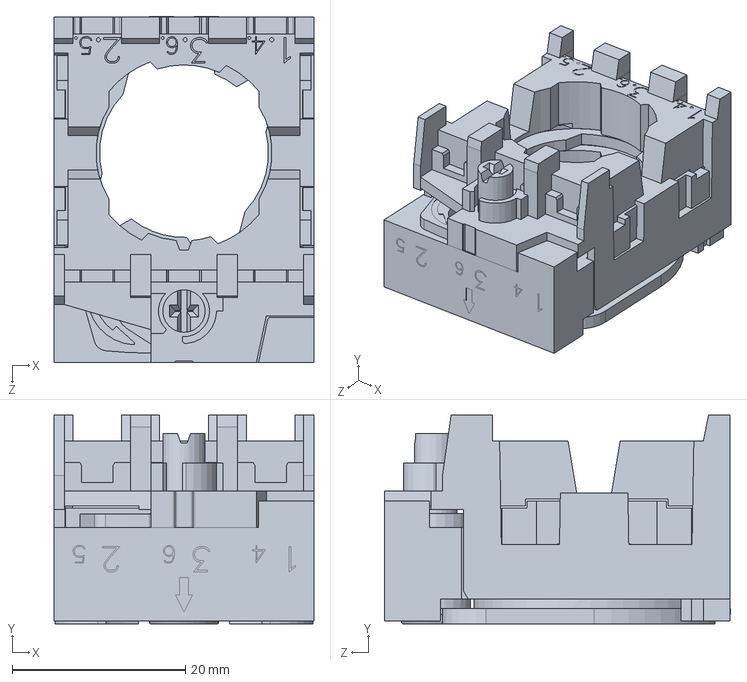
[picture p37: CAD file, 2017-03-23]
06_Mechanical/TK500_Driver/Siemens/3SU1500-0AA10-0AA0.SLDPRT
30.0 x 24.1 x 40.0 mm
