Cable89/tesla-driver/06_Mechanical/TK500_Driver/TK531_Utgangstrinn.SLDPRT

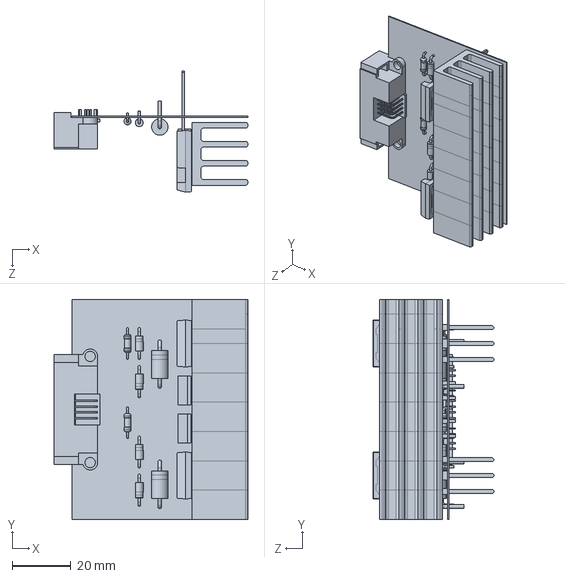
[picture p38: CAD file, 2022-05-03]
06_Mechanical/TK500_Driver/TK531_Utgangstrinn.SLDPRT
66.0 x 75.0 x 41.4 mm
