Cable89/tesla-driver/06_Mechanical/TK500_Driver/TK514_Interrupter.SLDPRT

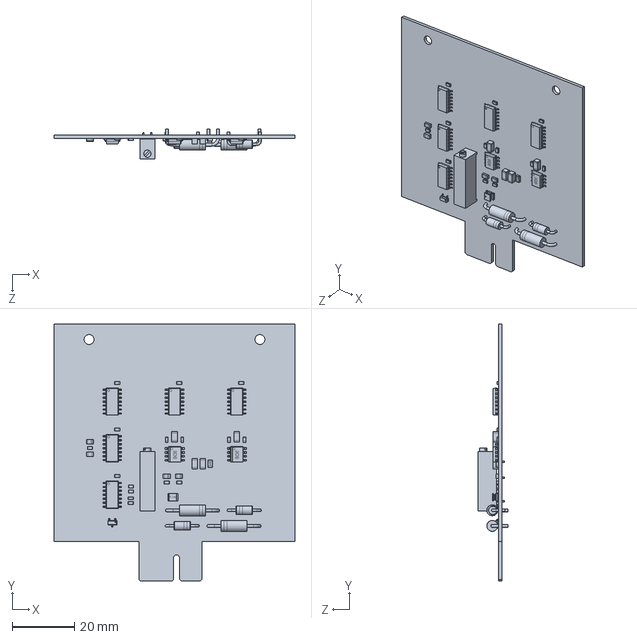
[picture p39: CAD file, 2022-05-03]
06_Mechanical/TK500_Driver/TK514_Interrupter.SLDPRT
77.5 x 82.8 x 9.55 mm
