Cable89/tesla-driver/06_Mechanical/TK100_Tonegenerator/Unfuckcase_flat_3_1.dxf

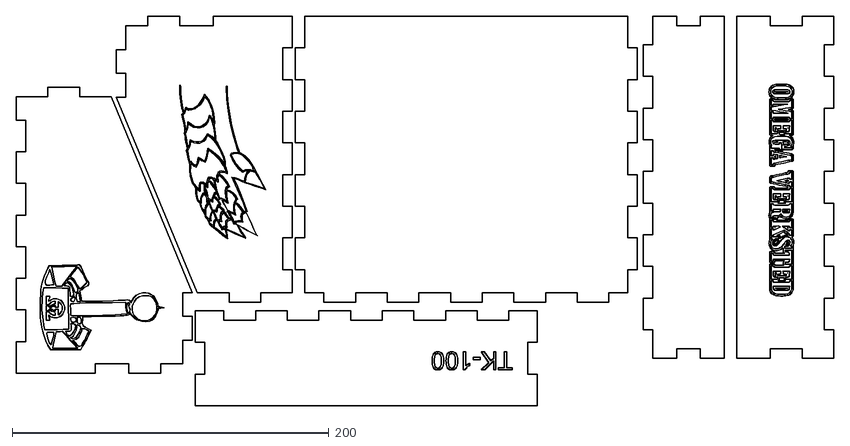
[picture p40: CAD file, 2019-02-26]
06_Mechanical/TK100_Tonegenerator/Unfuckcase_flat_3_1.dxf
516.5 x 246.0
