Cable89/tesla-driver/06_Mechanical/TK500_Driver/TK532_Kondensatorkort.SLDPRT

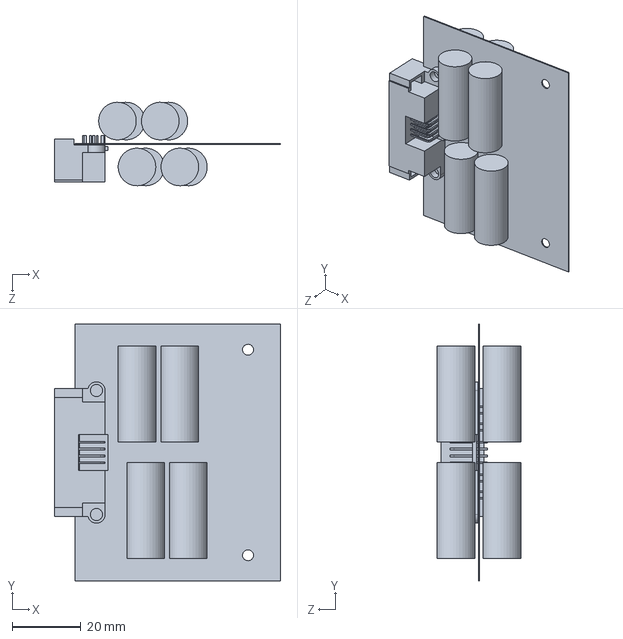
[picture p41: CAD file, 2022-05-03]
06_Mechanical/TK500_Driver/TK532_Kondensatorkort.SLDPRT
66.0 x 75.0 x 24.4 mm
