Cable89/tesla-driver/06_Mechanical/TK500_Driver/DIN-Rail_220mm.SLDPRT

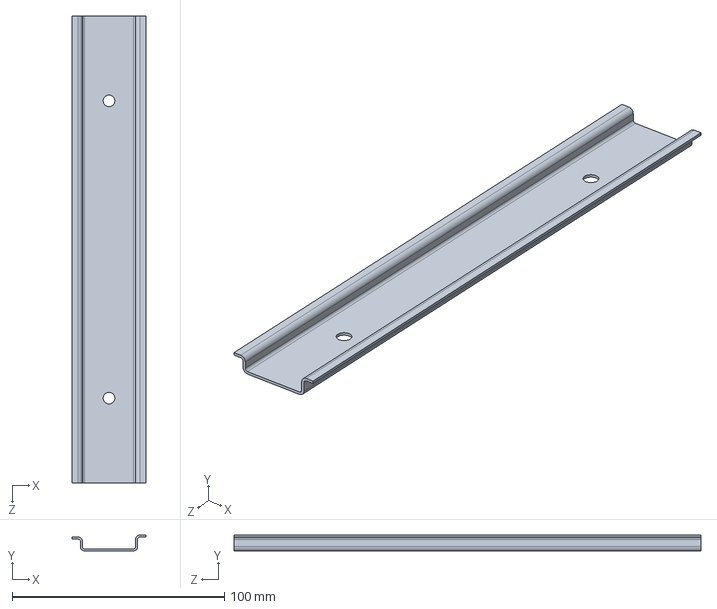
[picture p42: CAD file, 2022-05-03]
06_Mechanical/TK500_Driver/DIN-Rail_220mm.SLDPRT
35.0 x 7.50 x 220.0 mm
