Cable89/tesla-driver/06_Mechanical/TK500_Driver/WH100-100RJI.SLDPRT

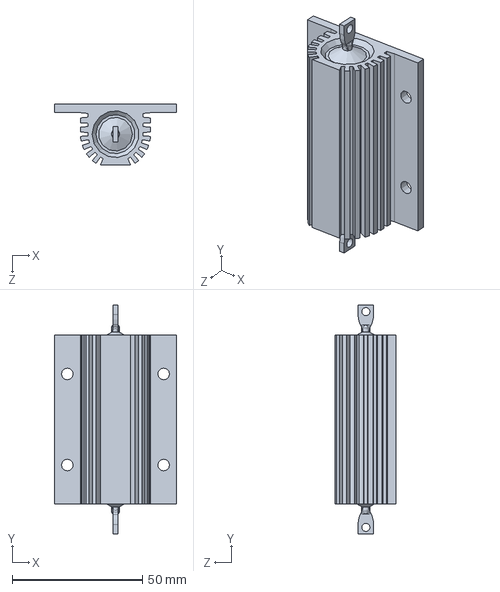
[picture p43: CAD file, 2022-05-03]
06_Mechanical/TK500_Driver/WH100-100RJI.SLDPRT
47.0 x 88.0 x 23.2 mm
