Cable89/tesla-driver/06_Mechanical/TK500_Driver/TK521_Optisk-plugg.SLDPRT

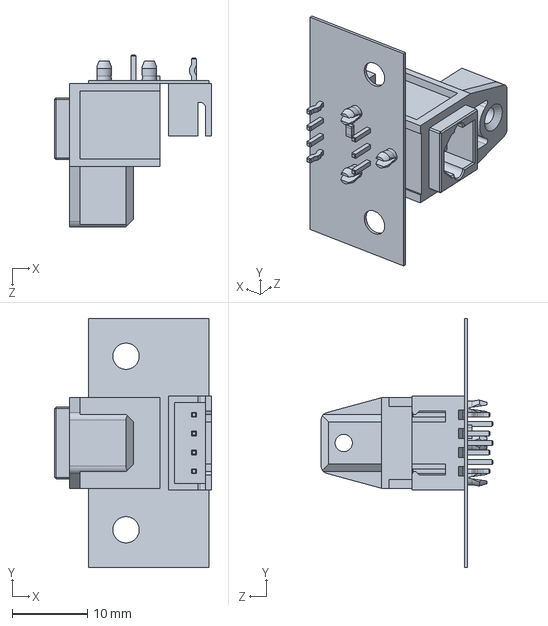
[picture p44: CAD file, 2022-05-03]
06_Mechanical/TK500_Driver/TK521_Optisk-plugg.SLDPRT
20.8 x 33.0 x 22.8 mm
