Cable89/tesla-driver/06_Mechanical/TK500_Driver/DIN-Rele.SLDPRT

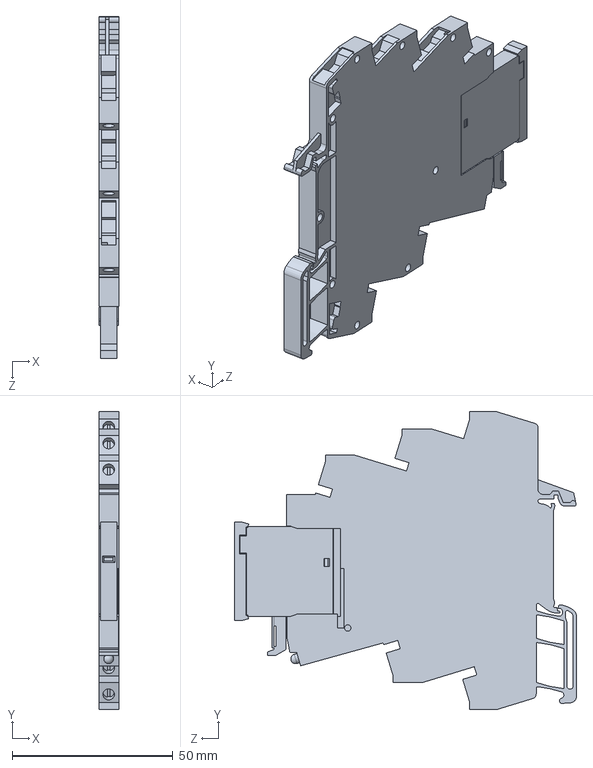
[picture p45: CAD file, 2022-05-03]
06_Mechanical/TK500_Driver/DIN-Rele.SLDPRT
6.20 x 92.7 x 106.3 mm
