Cable89/tesla-driver/06_Mechanical/TK500_Driver/TK530_Kraftbakplan.SLDPRT

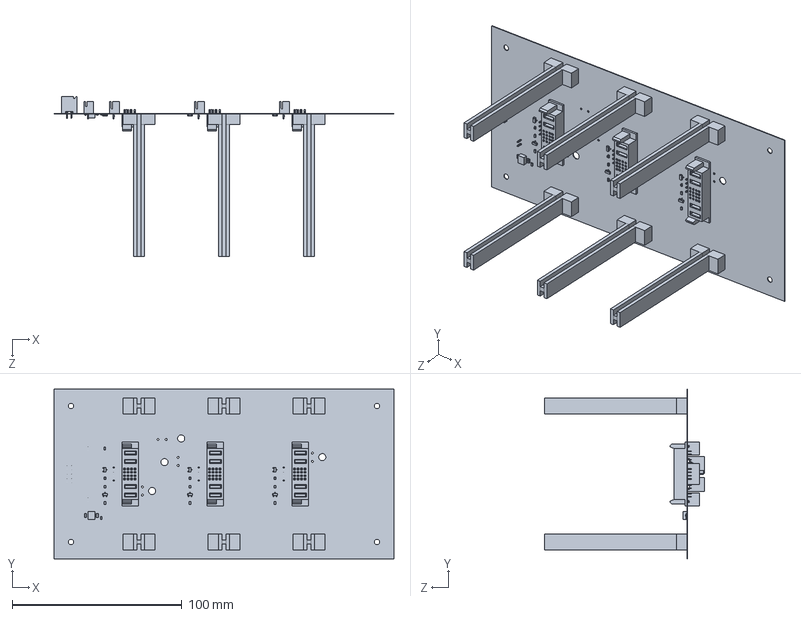
[picture p46: CAD file, 2022-05-03]
06_Mechanical/TK500_Driver/TK530_Kraftbakplan.SLDPRT
200.0 x 100.0 x 94.1 mm
