Cable89/tesla-driver/06_Mechanical/TK500_Driver/IEC-C14.SLDPRT

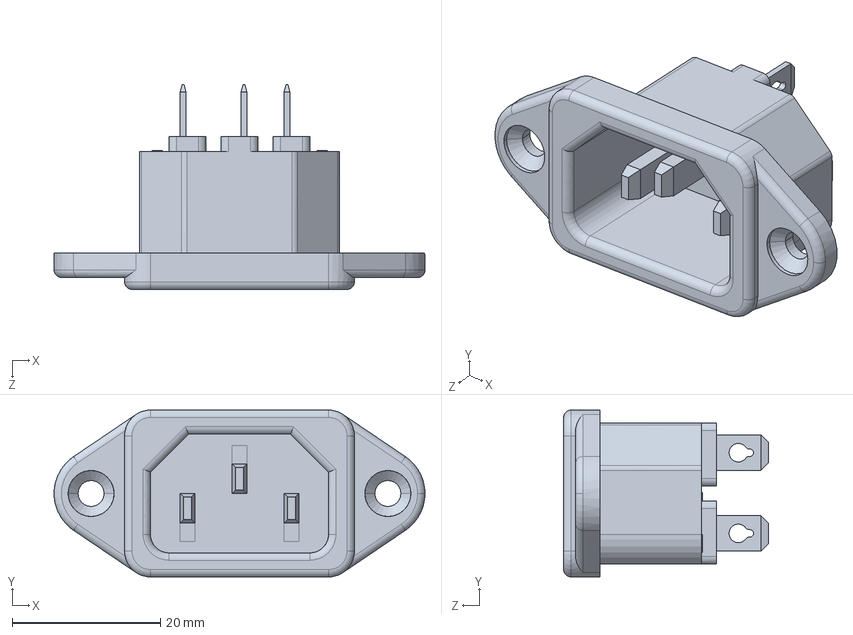
[picture p47: CAD file, 2022-05-03]
06_Mechanical/TK500_Driver/IEC-C14.SLDPRT
50.0 x 22.5 x 27.6 mm
