Cable89/tesla-driver/06_Mechanical/TK500_Driver/HFS5-2020-135.sldprt

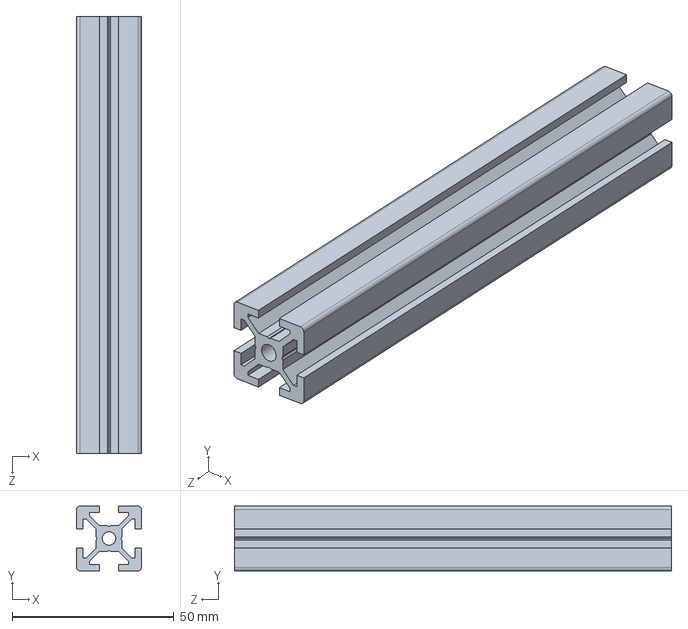
[picture p48: CAD file, 2022-05-03]
06_Mechanical/TK500_Driver/HFS5-2020-135.sldprt
20.0 x 20.0 x 135.0 mm
