Cable89/tesla-driver/06_Mechanical/TK100_Tonegenerator/Unfuckcase_flat_3.stl

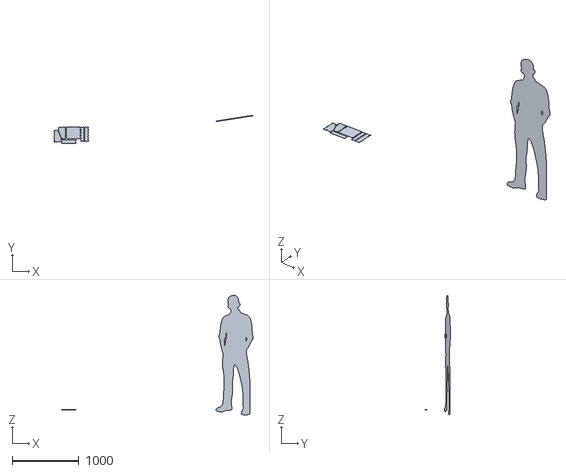
[picture p49: CAD file, 2019-02-26]
06_Mechanical/TK100_Tonegenerator/Unfuckcase_flat_3.stl
2984.6 x 418.2 x 1796.4
