Cable89/tesla-driver/06_Mechanical/TK500_Driver/TK511_Blindkort.SLDPRT

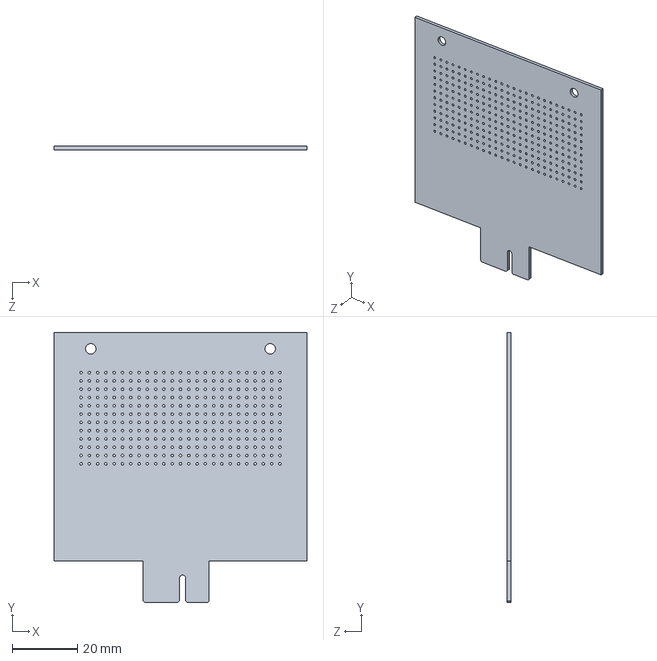
[picture p50: CAD file, 2022-05-03]
06_Mechanical/TK500_Driver/TK511_Blindkort.SLDPRT
77.5 x 82.8 x 1.09 mm
