Cable89/tesla-driver/06_Mechanical/TK500_Driver/HBLFSNF5_b.sldprt

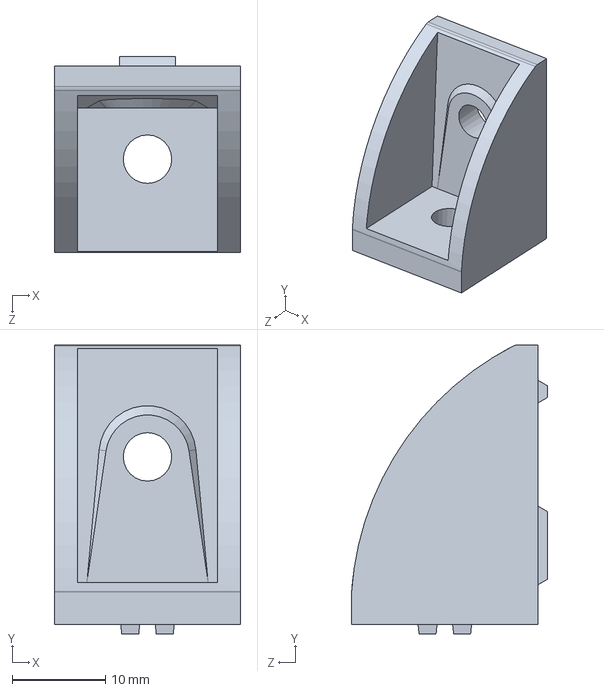
[picture p51: CAD file, 2022-05-03]
06_Mechanical/TK500_Driver/HBLFSNF5_b.sldprt
20.0 x 31.0 x 21.0 mm
