Cable89/tesla-driver/06_Mechanical/TK500_Driver/NAC3MPB-1.SLDPRT

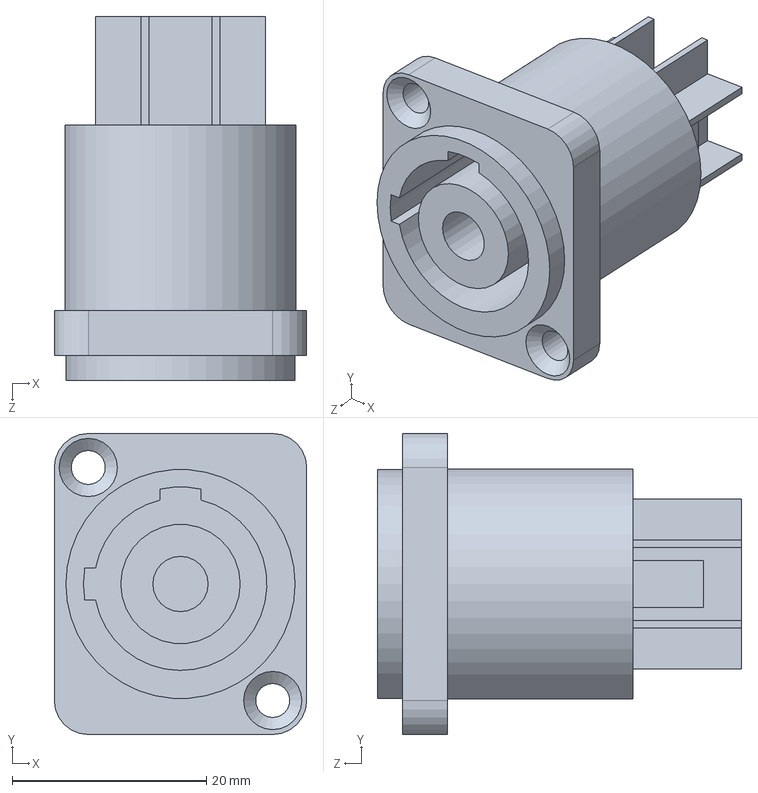
[picture p52: CAD file, 2022-05-03]
06_Mechanical/TK500_Driver/NAC3MPB-1.SLDPRT
26.0 x 31.0 x 37.5 mm
