Cable89/tesla-driver/06_Mechanical/TK500_Driver/TK520_GDT-Trafo.SLDPRT

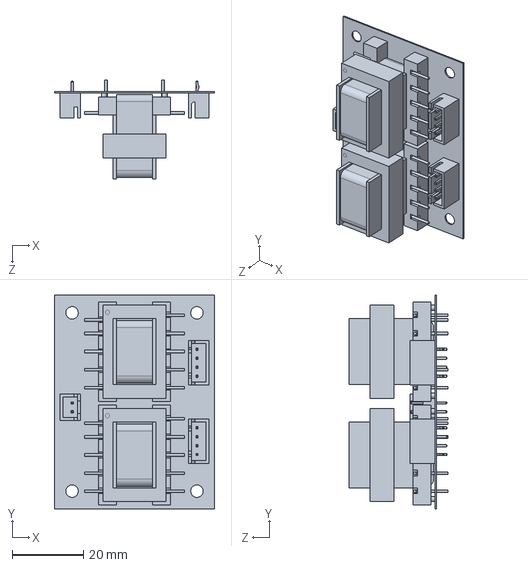
[picture p53: CAD file, 2022-05-03]
06_Mechanical/TK500_Driver/TK520_GDT-Trafo.SLDPRT
45.0 x 60.0 x 27.9 mm
