Cable89/tesla-driver/06_Mechanical/TK500_Driver/3590P-1-103L.SLDPRT

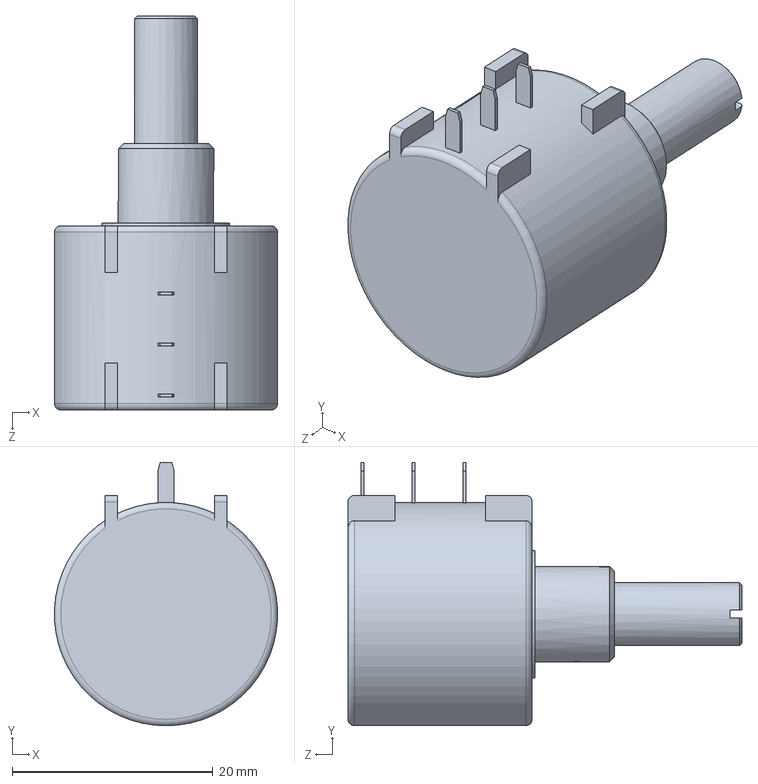
[picture p54: CAD file, 2022-05-03]
06_Mechanical/TK500_Driver/3590P-1-103L.SLDPRT
22.2 x 26.2 x 39.2 mm
