Cable89/tesla-driver/06_Mechanical/TK500_Driver/22S-2D.SLDPRT

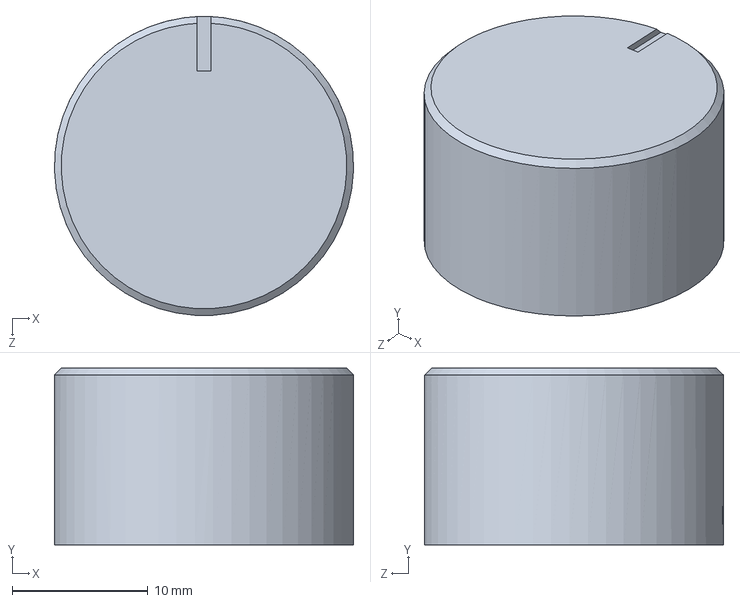
[picture p55: CAD file, 2022-05-03]
06_Mechanical/TK500_Driver/22S-2D.SLDPRT
22.0 x 13.0 x 22.0 mm
