Cable89/tesla-driver/06_Mechanical/TK500_Driver/Bakside.SLDPRT

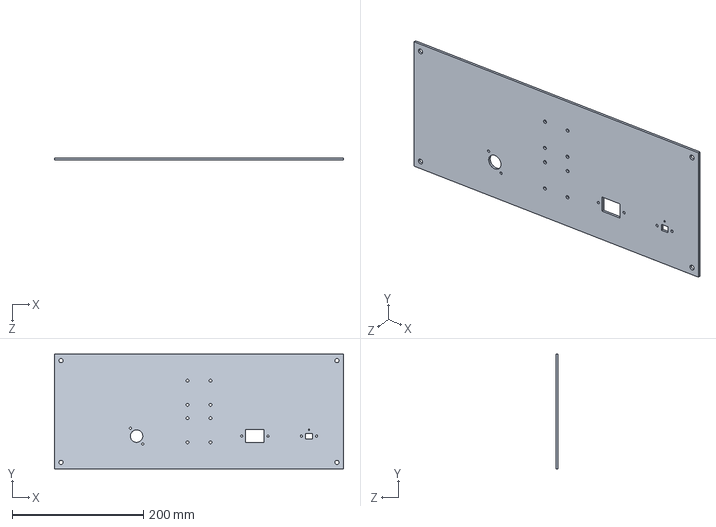
[picture p56: CAD file, 2022-05-03]
06_Mechanical/TK500_Driver/Bakside.SLDPRT
440.0 x 175.0 x 3.00 mm
