Cable89/tesla-driver/06_Mechanical/TK500_Driver/19mm_vandal_alu.SLDPRT

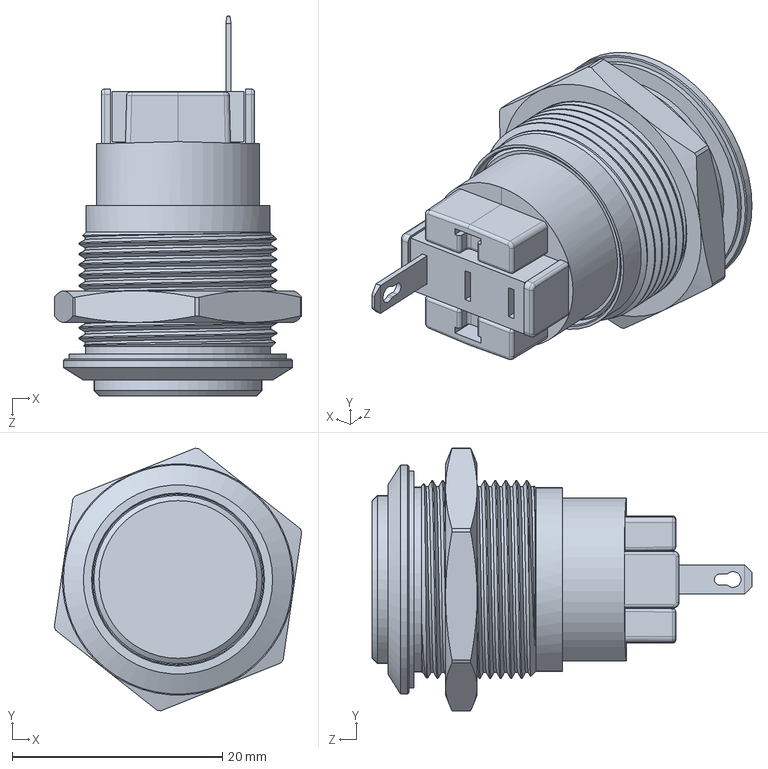
[picture p57: CAD file, 2022-05-03]
06_Mechanical/TK500_Driver/19mm_vandal_alu.SLDPRT
23.5 x 25.0 x 36.2 mm
