Cable89/tesla-driver/06_Mechanical/TK500_Driver/TK512_Optisk_Mottaker.SLDPRT

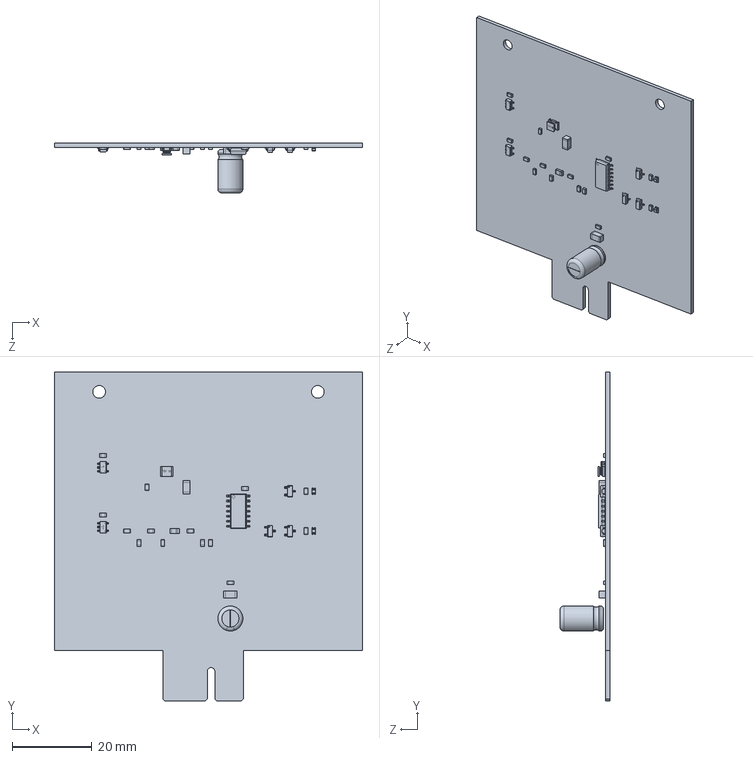
[picture p58: CAD file, 2022-05-03]
06_Mechanical/TK500_Driver/TK512_Optisk_Mottaker.SLDPRT
77.5 x 82.8 x 12.6 mm
