Cable89/tesla-driver/06_Mechanical/TK500_Driver/Bottom.SLDPRT

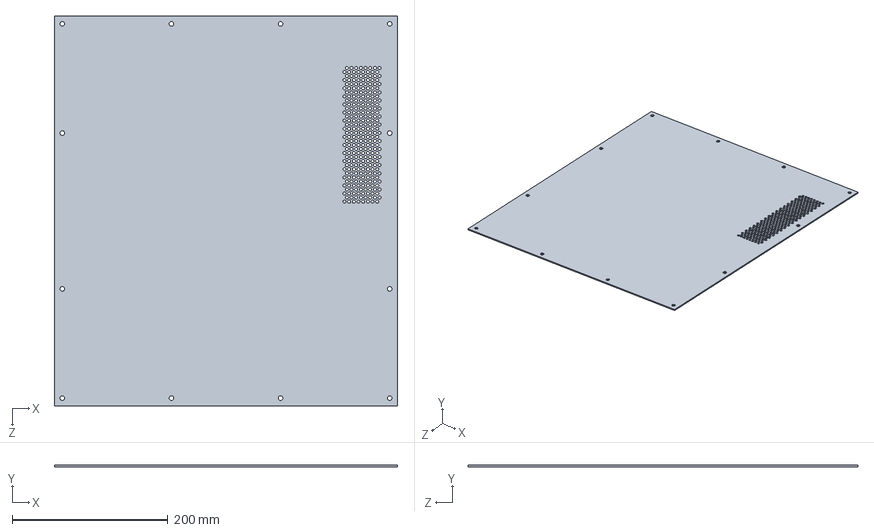
[picture p59: CAD file, 2022-05-03]
06_Mechanical/TK500_Driver/Bottom.SLDPRT
440.0 x 2.00 x 500.0 mm
