Cable89/tesla-driver/06_Mechanical/TK500_Driver/TK502_Frontpanel_LEDs.SLDPRT

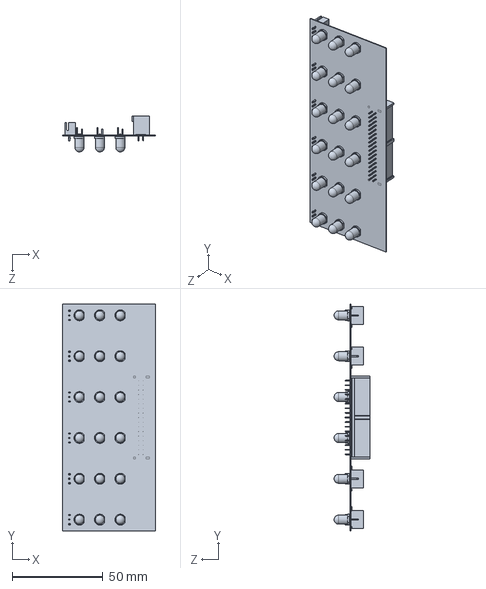
[picture p60: CAD file, 2022-05-03]
06_Mechanical/TK500_Driver/TK502_Frontpanel_LEDs.SLDPRT
51.0 x 125.0 x 19.8 mm
