Cable89/tesla-driver/06_Mechanical/TK500_Driver/Optical_bracket.SLDPRT

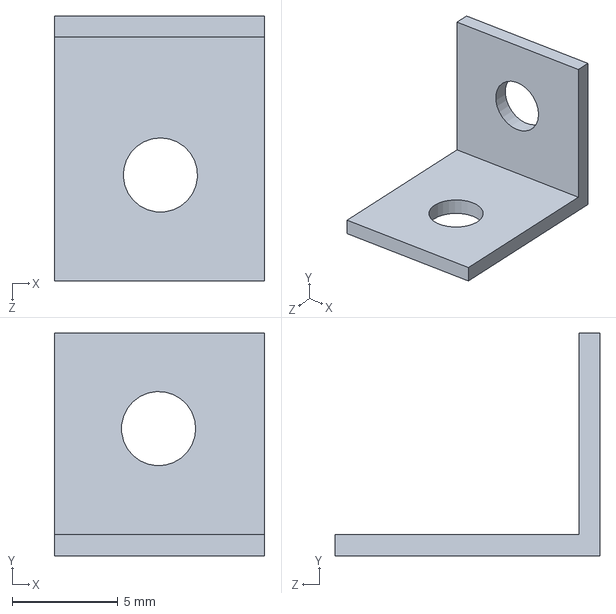
[picture p61: CAD file, 2022-05-03]
06_Mechanical/TK500_Driver/Optical_bracket.SLDPRT
9.91 x 10.5 x 12.5 mm
