Cable89/tesla-driver/06_Mechanical/TK500_Driver/Front.SLDPRT

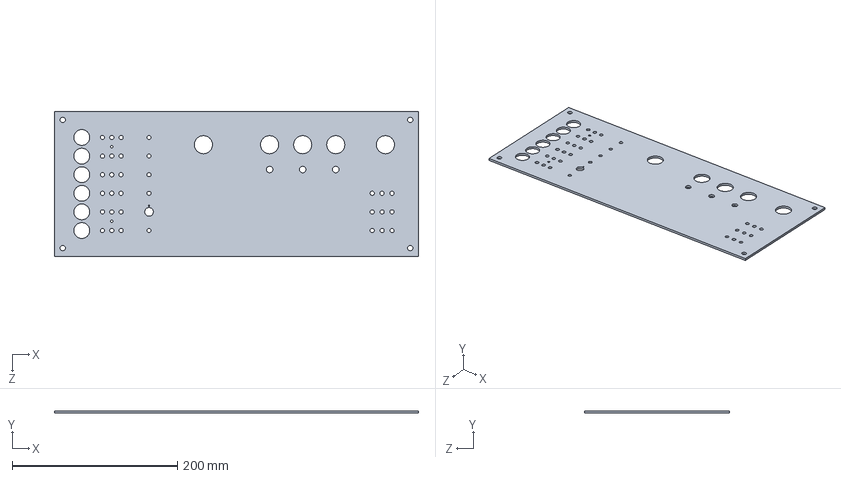
[picture p62: CAD file, 2022-05-03]
06_Mechanical/TK500_Driver/Front.SLDPRT
440.0 x 3.00 x 175.0 mm
