Cable89/tesla-driver/06_Mechanical/TK500_Driver/Kortstotte_84mm.SLDPRT

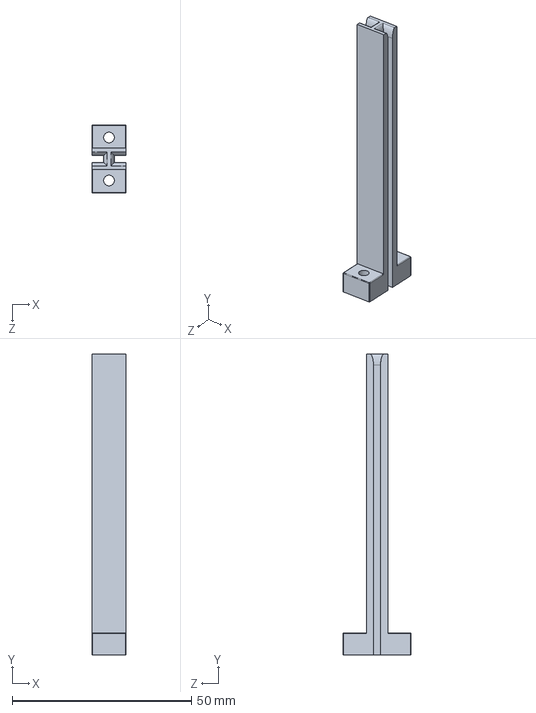
[picture p63: CAD file, 2017-03-25]
06_Mechanical/TK500_Driver/Kortstotte_84mm.SLDPRT
9.50 x 84.0 x 19.0 mm
