Cable89/tesla-driver/06_Mechanical/TK500_Driver/SK-454-75-SA.SLDPRT

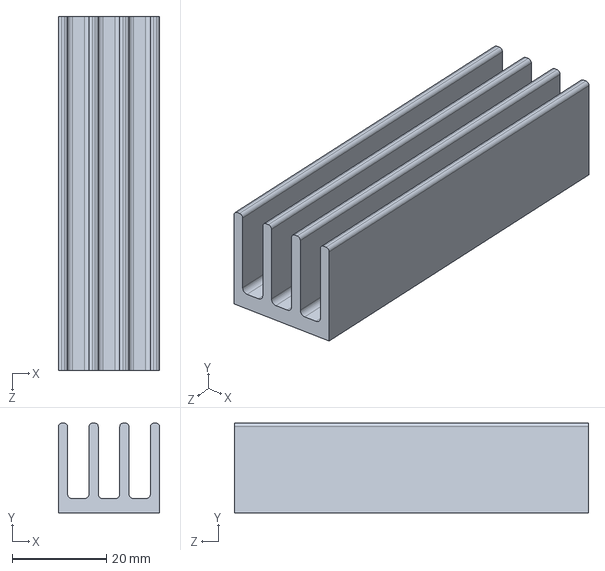
[picture p64: CAD file, 2017-03-25]
06_Mechanical/TK500_Driver/SK-454-75-SA.SLDPRT
21.4 x 19.0 x 75.0 mm
