Cable89/tesla-driver/06_Mechanical/TK500_Driver/Kortstotte_50mm.SLDPRT

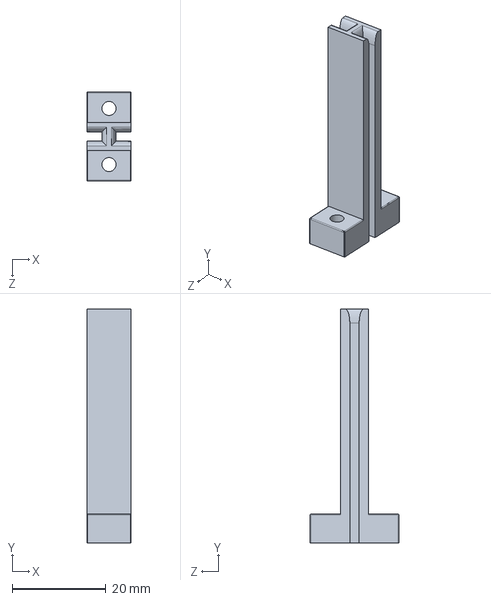
[picture p65: CAD file, 2017-03-25]
06_Mechanical/TK500_Driver/Kortstotte_50mm.SLDPRT
9.50 x 50.0 x 19.0 mm
