Cable89/tesla-driver/05_Hardware/TK100_Tonegenerator/TK192_Optisk_Ut/Project Outputs/Optisk_ut.PDF

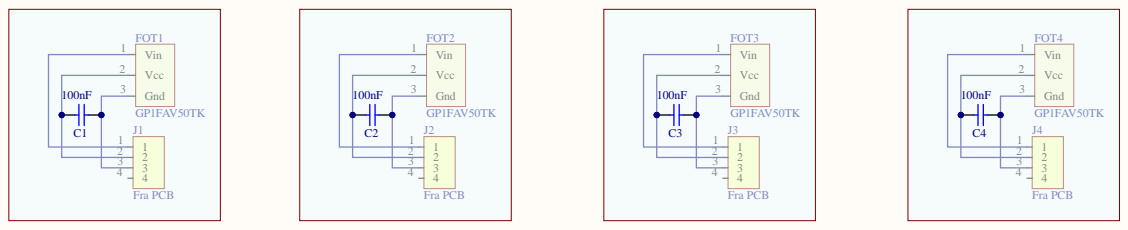
[picture p113: page 1]

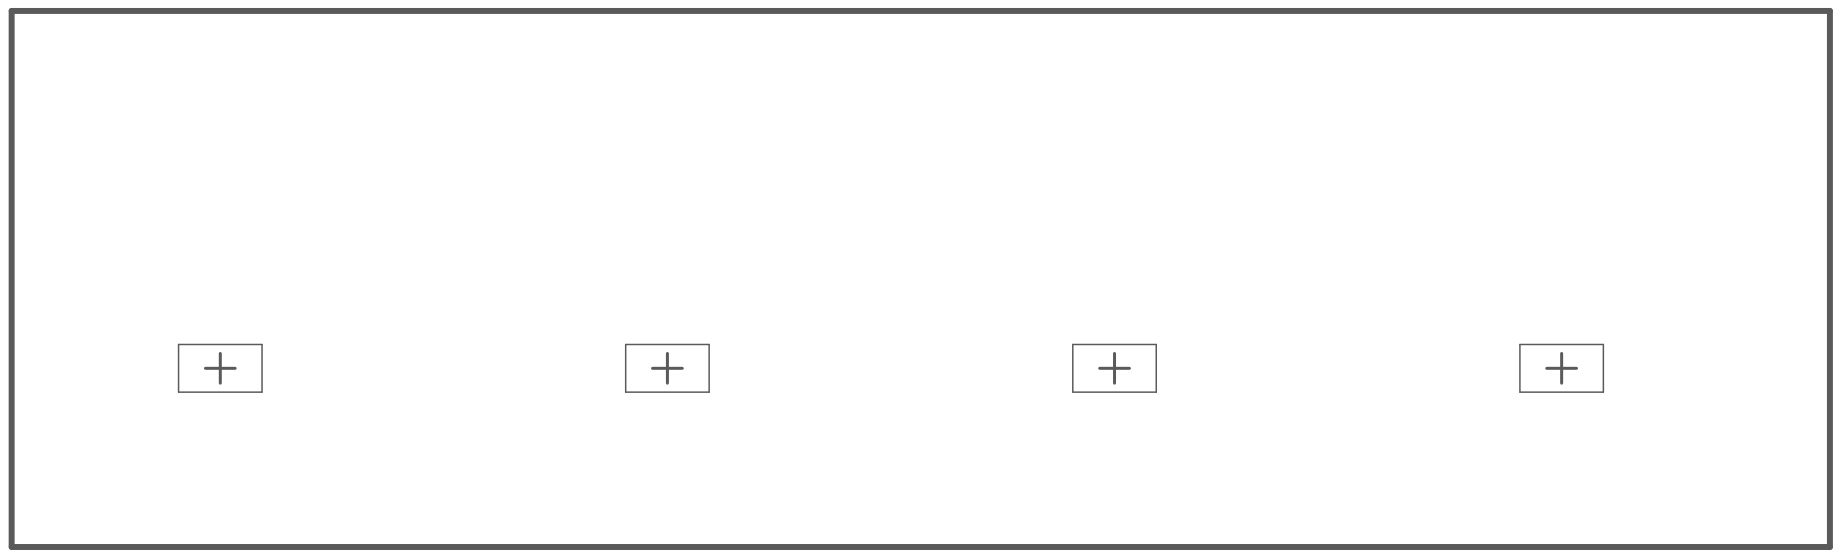
[picture p114: page 2]

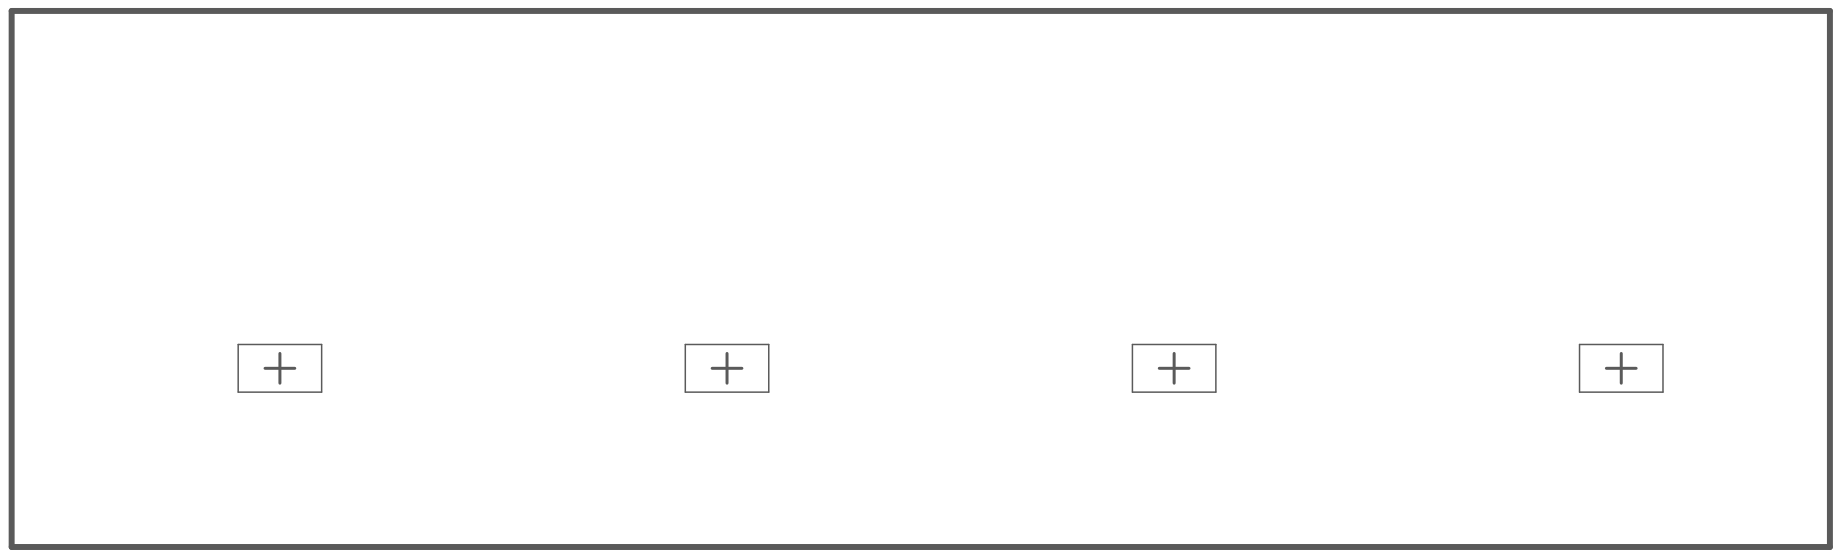
[picture p115: page 3]

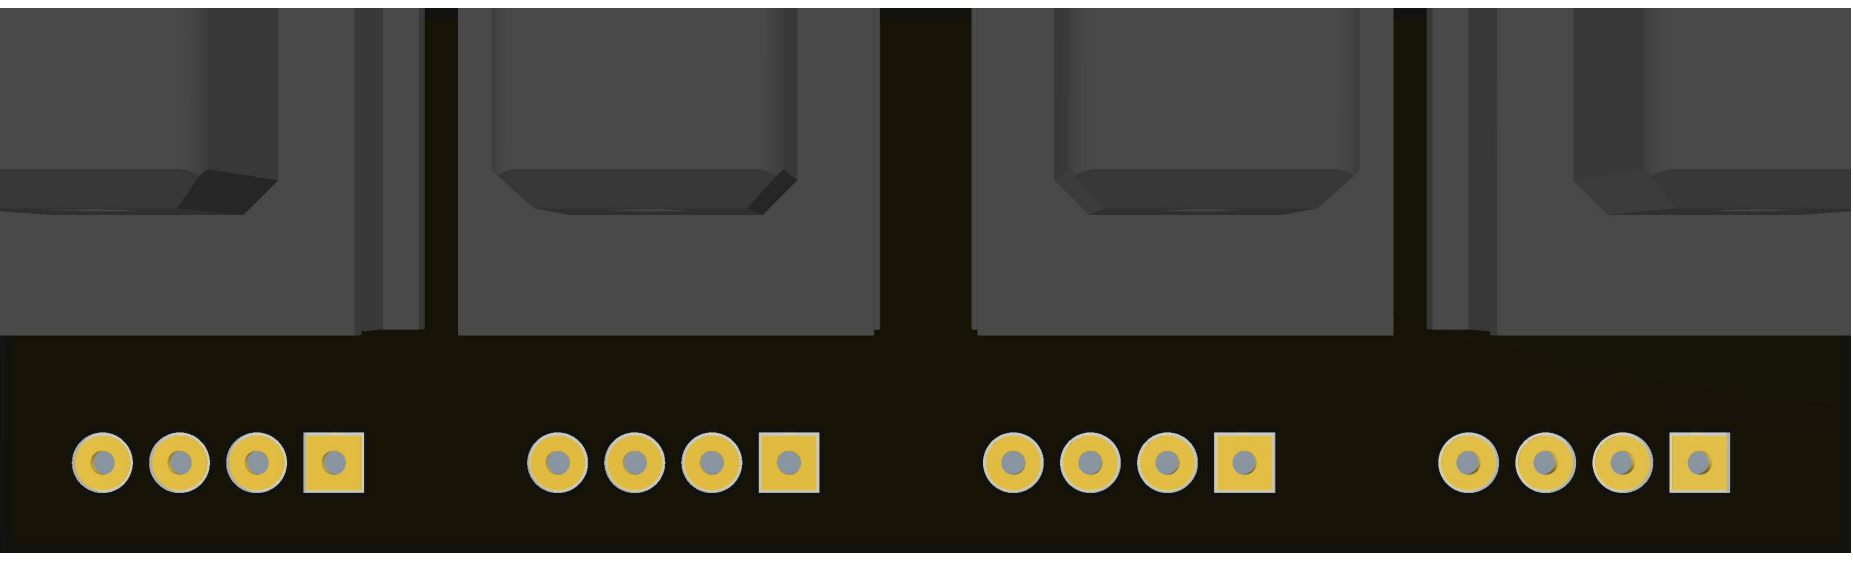
[picture p116: page 4]

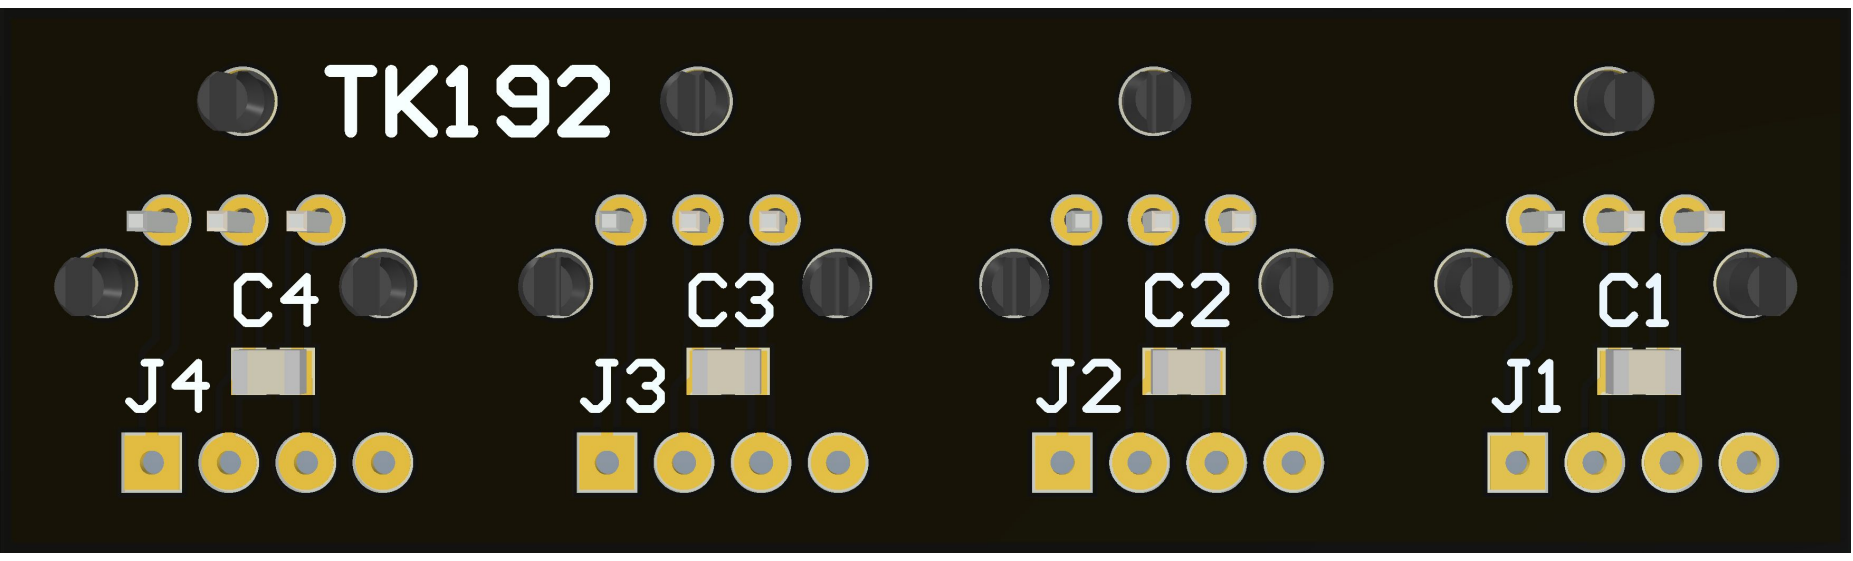
[picture p117: page 5]

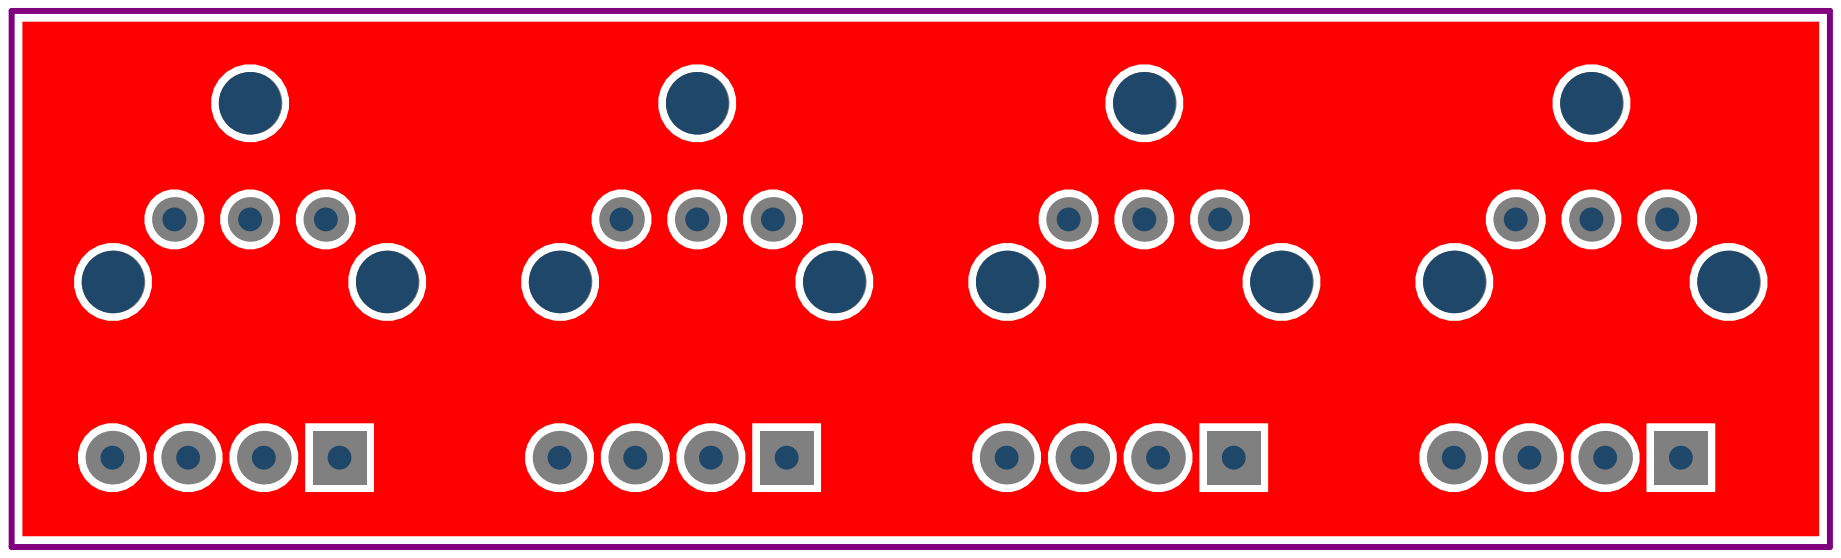
[picture p118: page 6]

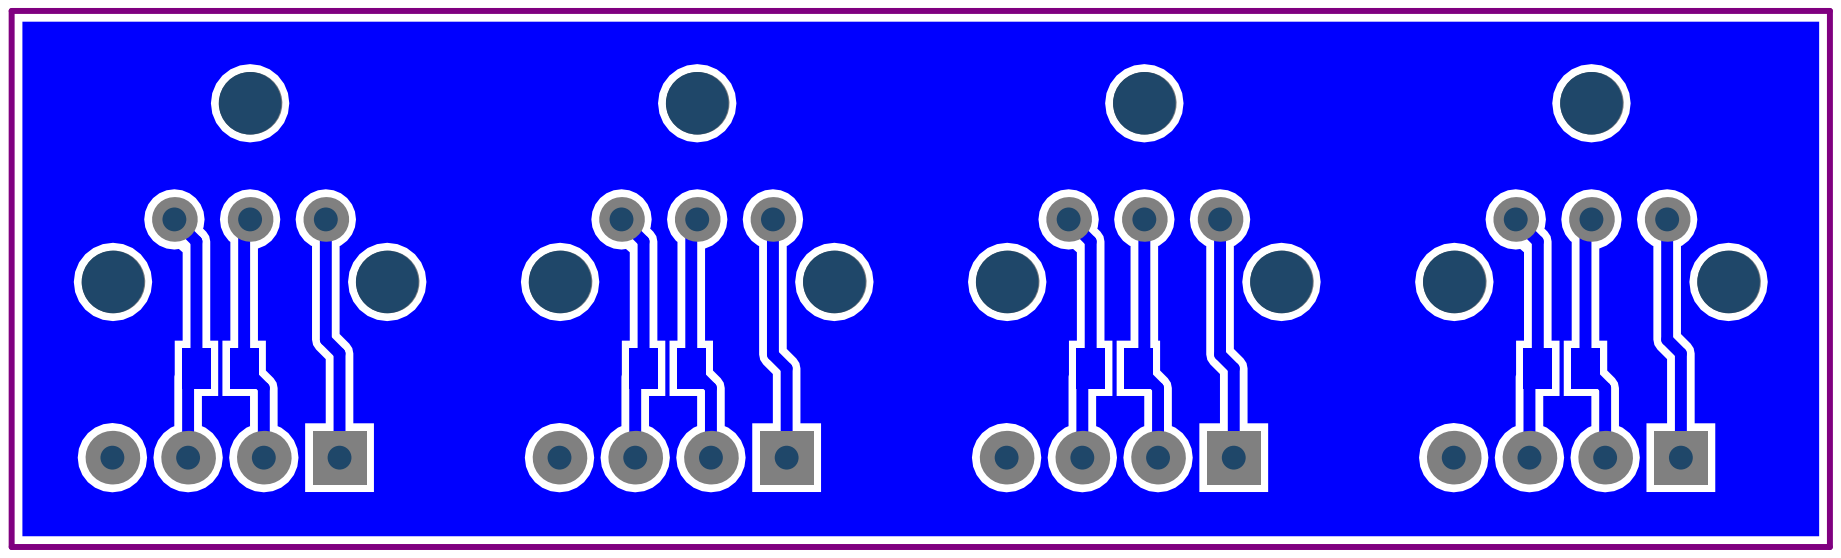
[picture p119: page 7]

Designator | Quantit y | navn | Description | leverandor | leverandor_varenr | antall

C1, C2, C3, C4, FOT1, FOT2, FOT3, FOT4, J1, J2, J3, J4 | 12 | | CAP 100nF 50V ±5% 0805 (2012 Metric) Thickness 1mm SMD, [NoValue]
