Cable89/tesla-driver/05_Hardware/TK500_Driver/TK510_Signalbakplan/Project Outputs/TK510_Signalbakplan.PDF

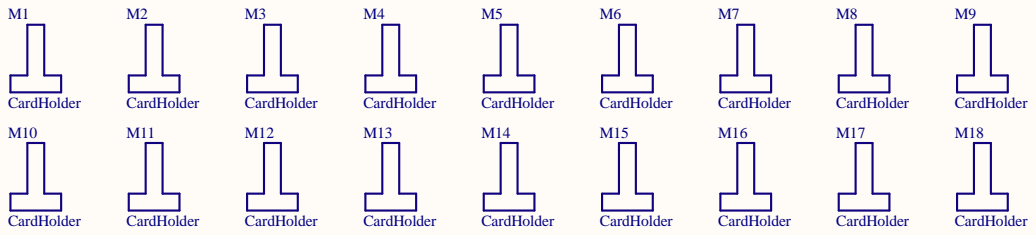
[picture p120: page 1]

C:\Git\tesla-driver\05_Hardware\TK500_Driver\TK510_Signalbakplan\TK510_Mekanisk.SchDoc

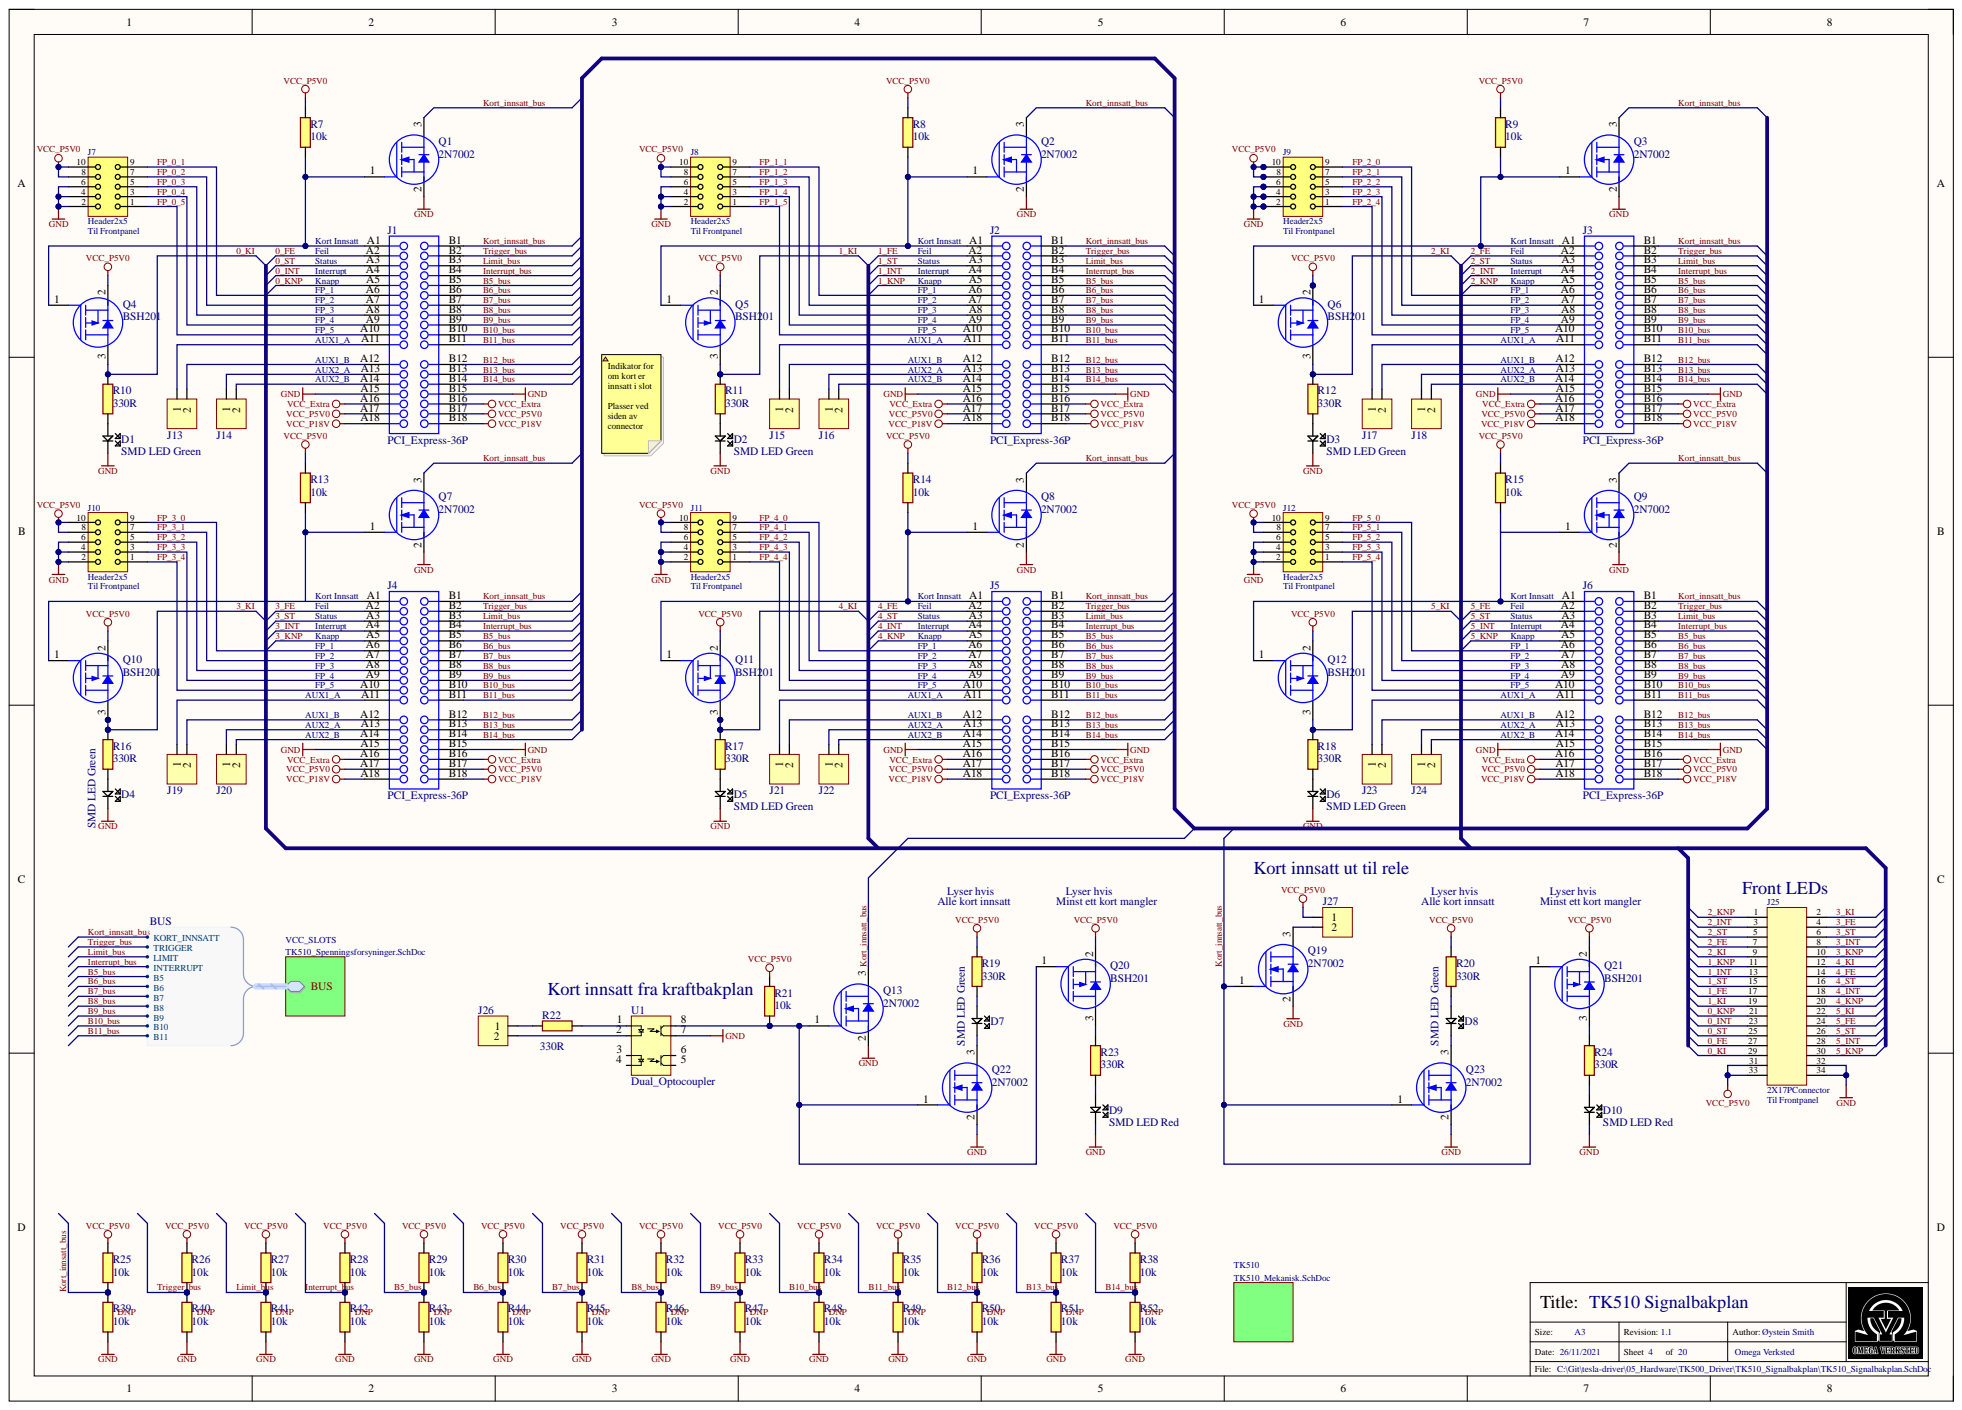
[picture p121: page 2]

Kort innsatt ut til rele

Kort innsatt fra kraftbakplan

C:\Git\tesla-driver\05_Hardware\TK500_Driver\TK510_Signalbakplan\TK510_Signalbakplan.SchDoc

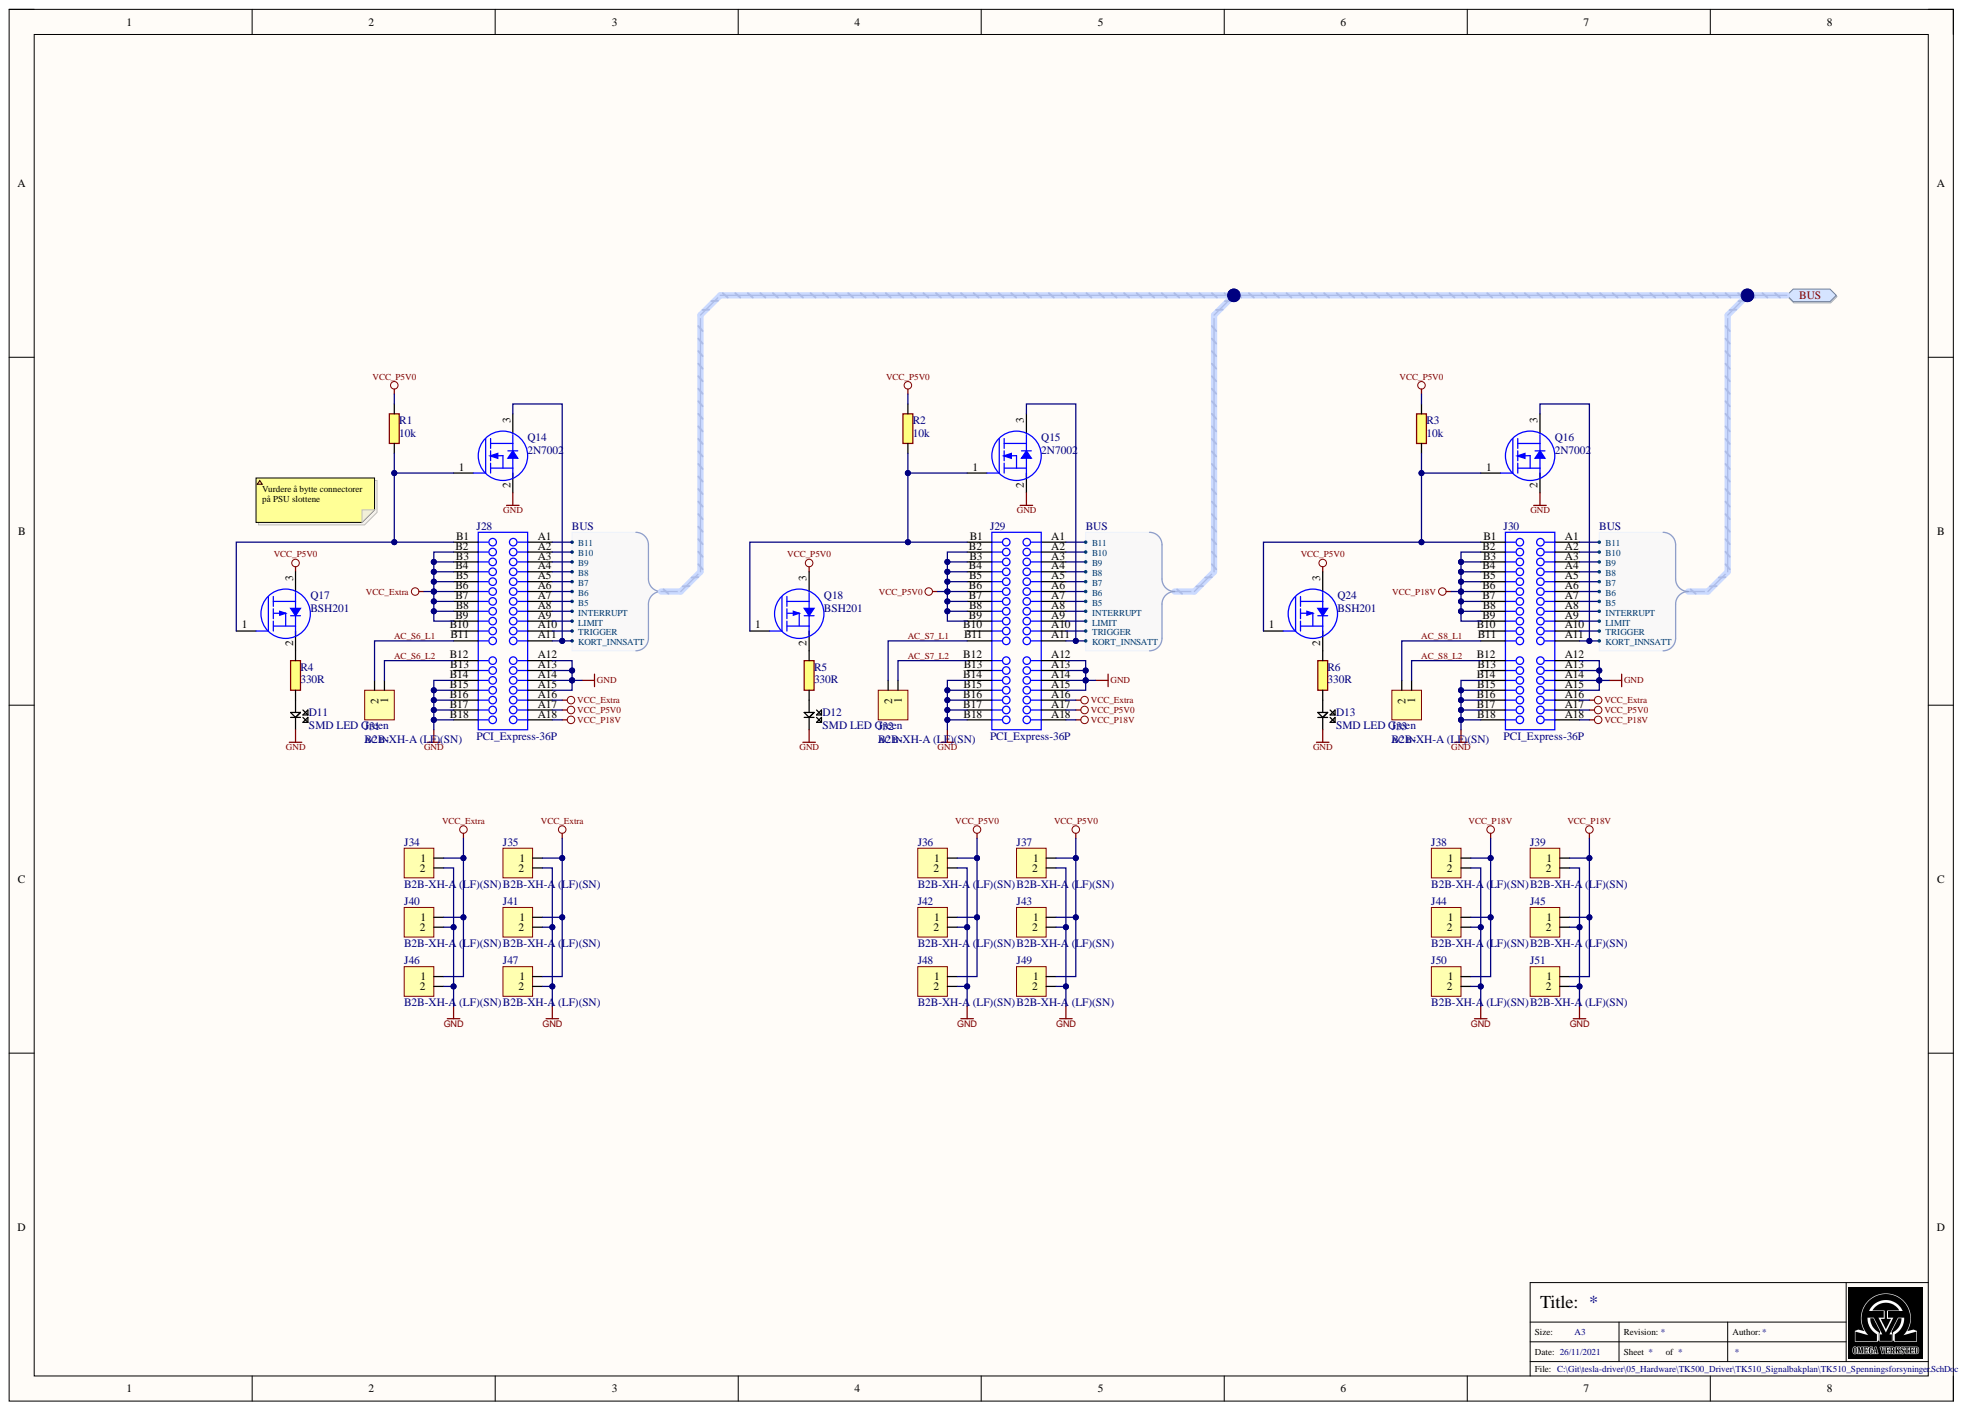
[picture p122: page 3]

C:\Git\tesla-driver\05_Hardware\TK500_Driver\TK510_Signalbakplan\TK510_Spenningsforsyninger.SchDoc

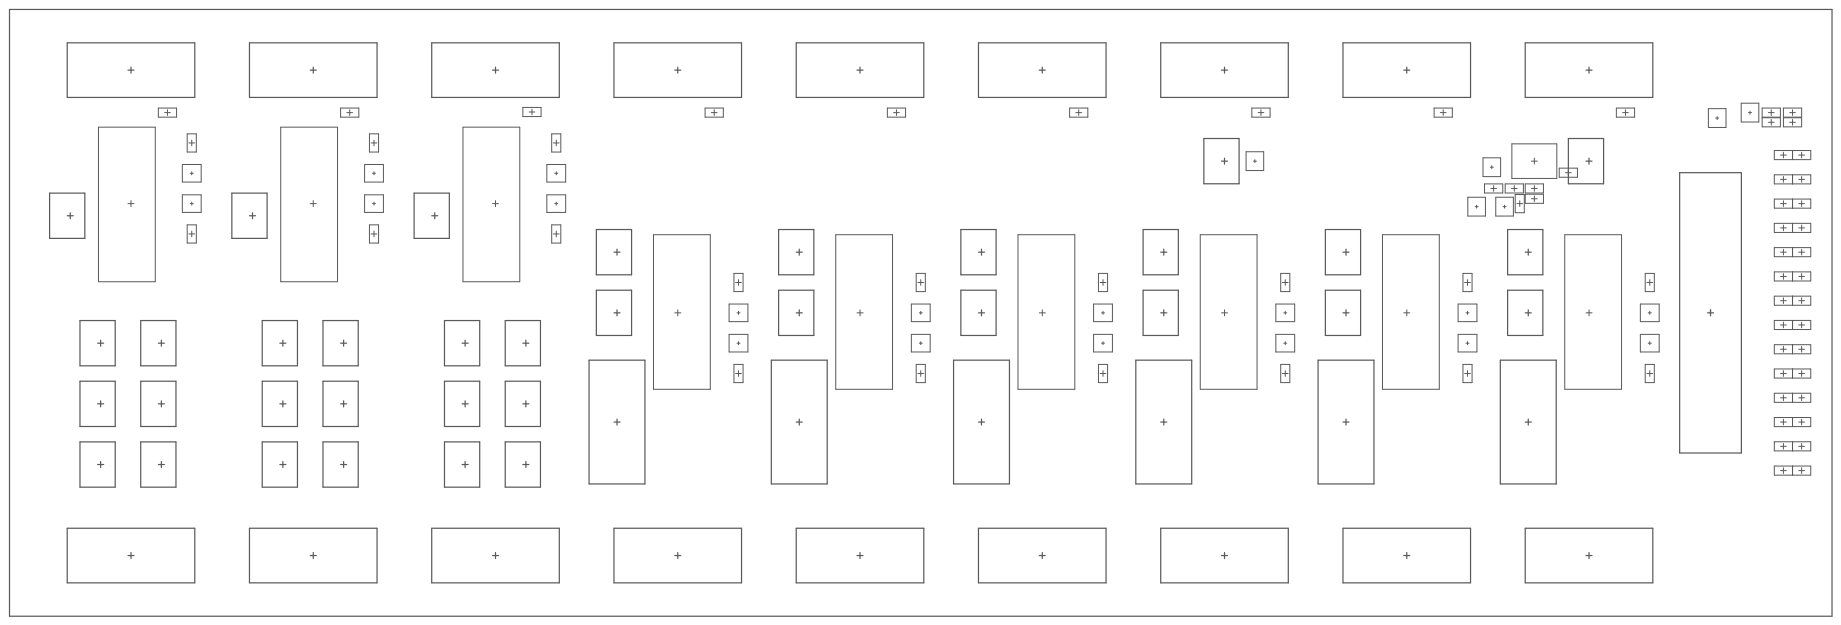
[picture p123: page 4]

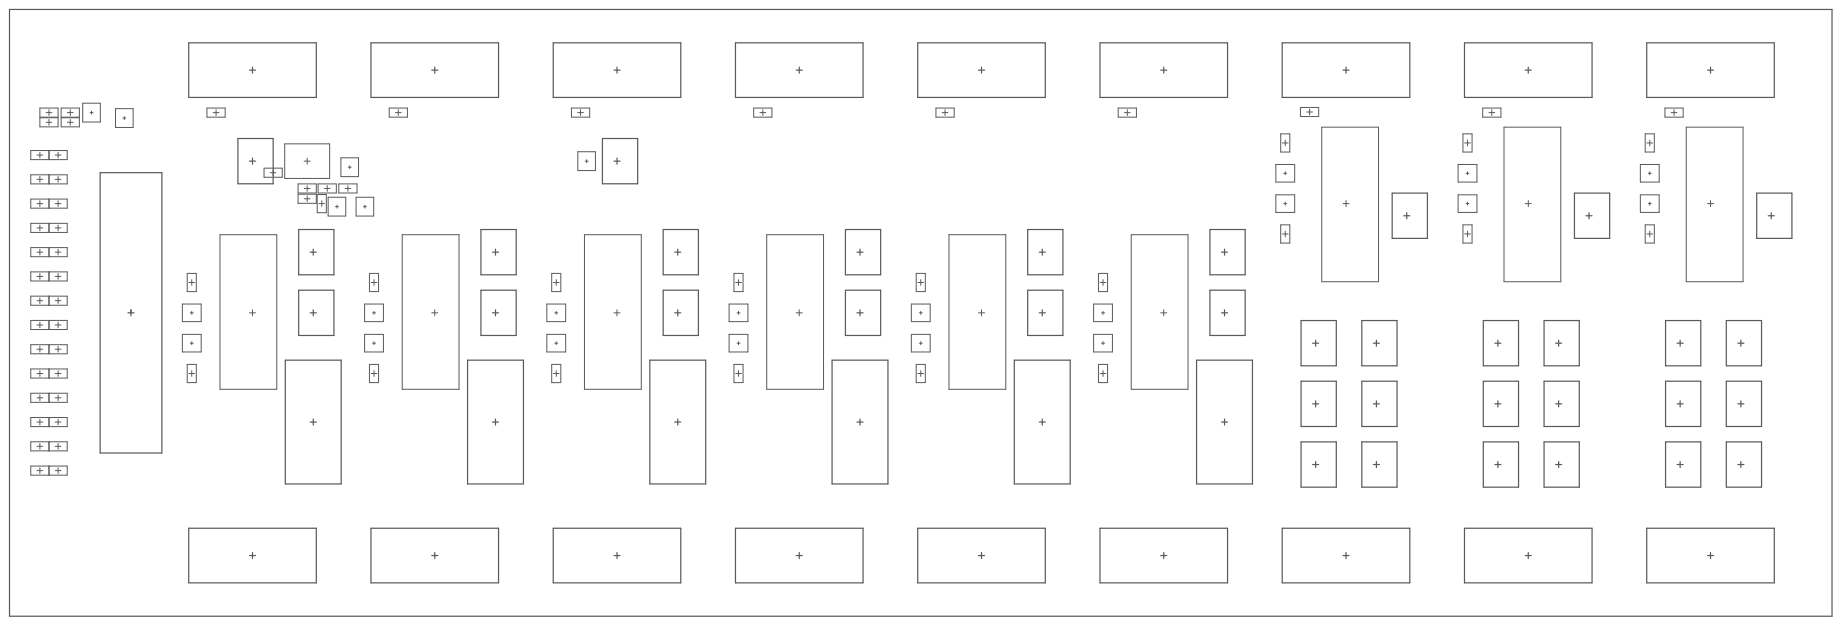
[picture p124: page 5]

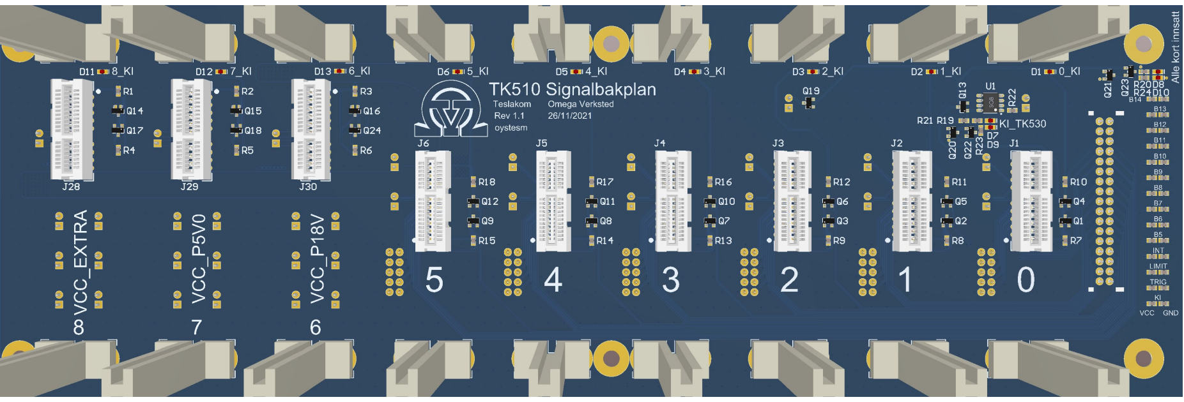
[picture p125: page 6]

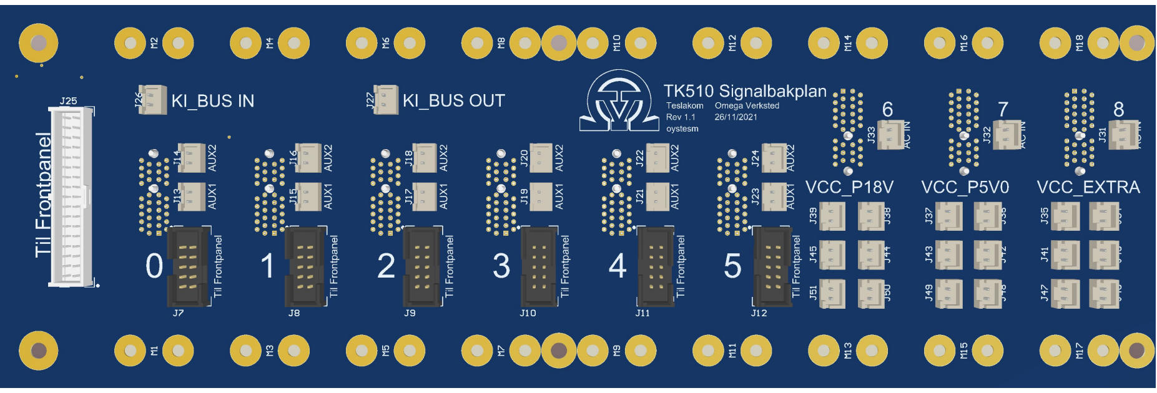
[picture p126: page 7]

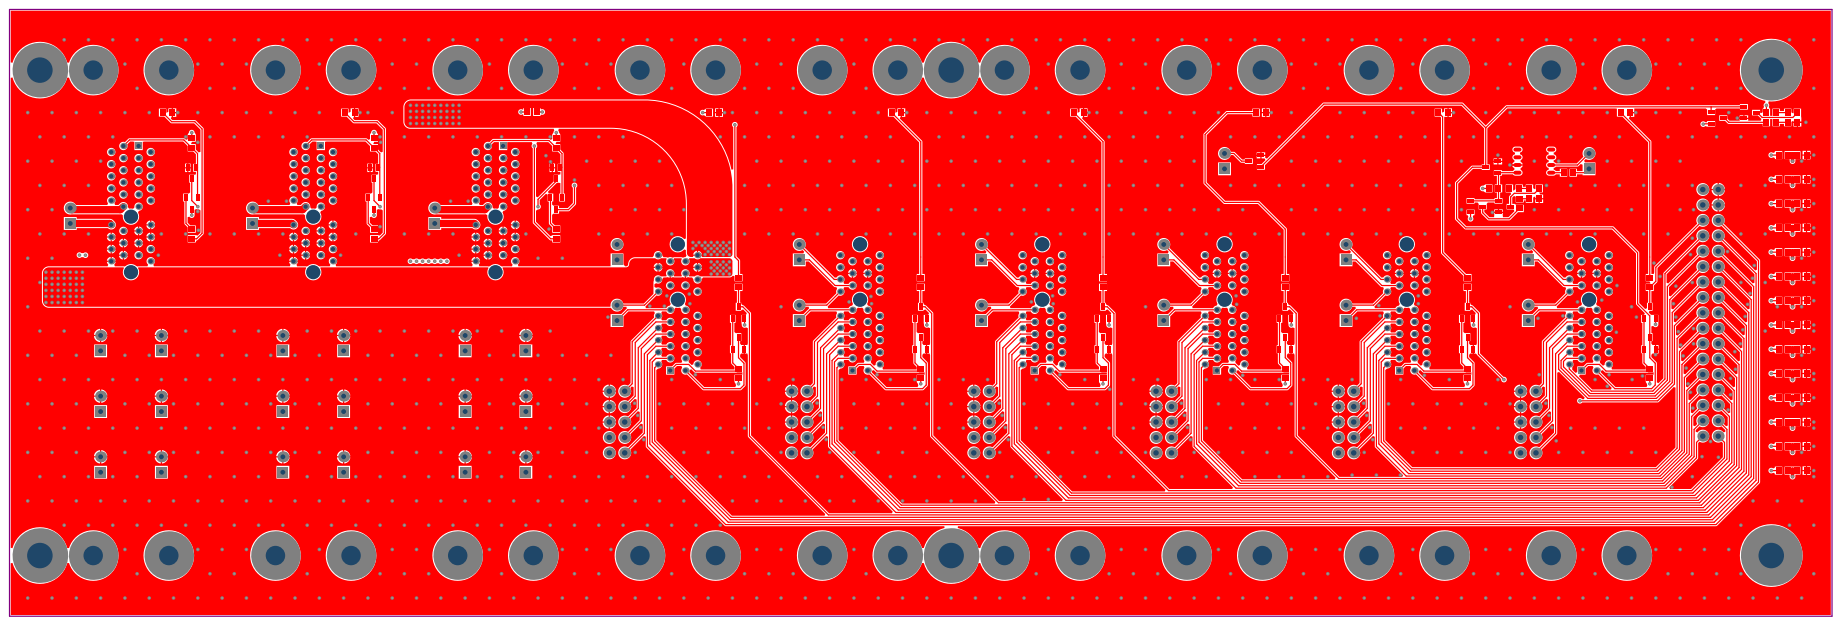
[picture p127: page 8]

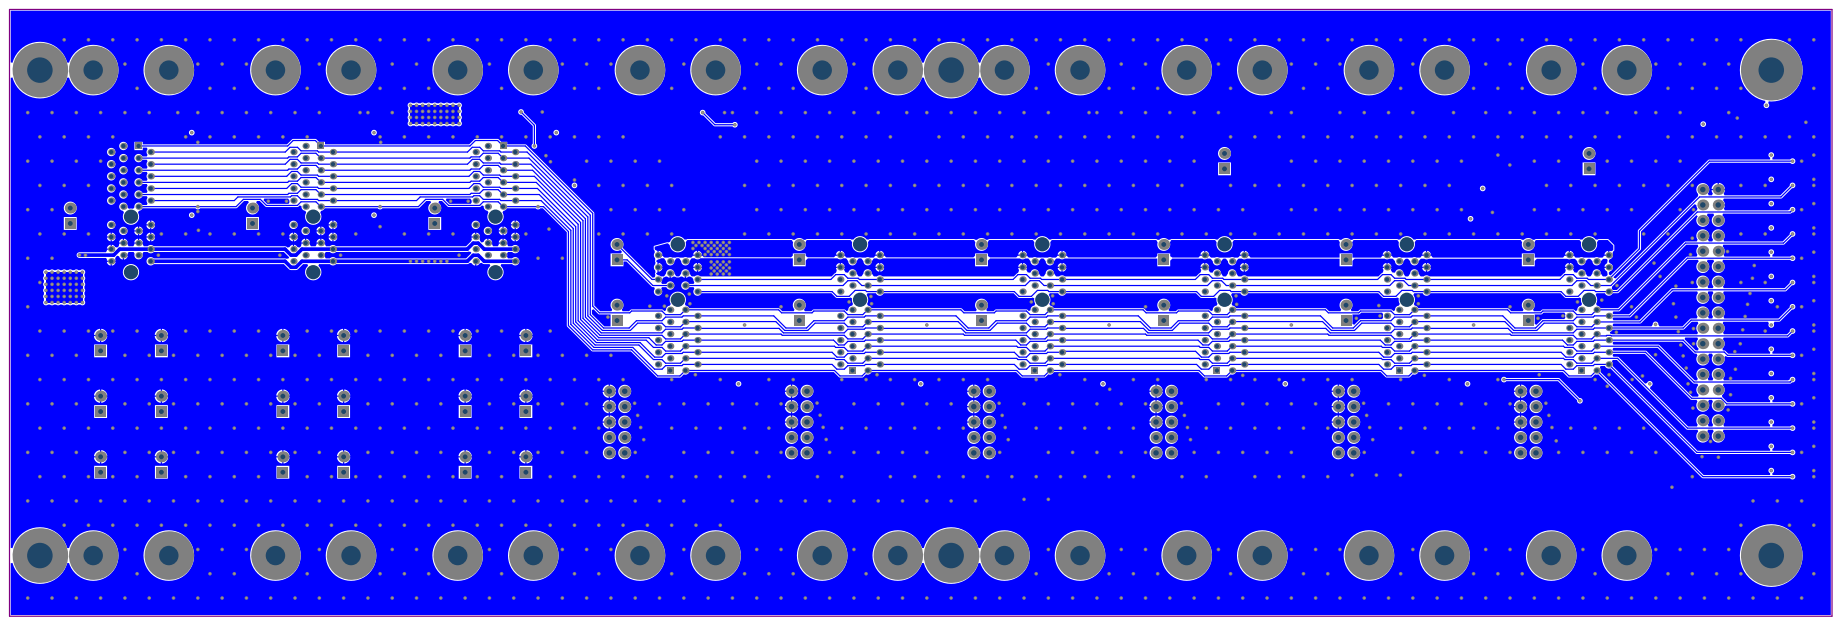
[picture p128: page 9]

Quantity | Designator | navn | pakketype | leverandor | leverandor_varenr | pris | hylle | rad | kolonne | dybde | antall
13 Q1, Q2, Q3, Q7, Q8, Q9, Q13, Q14, Q15, Q16, Q19, | Q22, Q23 | 2N7002 | SOT-323 | Farnell | 3226401, 1829184 | 1 | 3 | 2 | | 0 | 810
11 Q4, Q5, Q6, Q10, Q11, Q12, Q17, Q18, Q20, Q21, Q24 BSH201 | | | SOT | Farnell | 1758073 | 3 | 3 | 3 | | 0 | 51
9 J1, J2, J3, J4, J5, J6, J28, J29, J30 | | PCI_Express-36P | TH | Farnell | 1144435 | 16
6 J7, J8, J9, J10, J11, J12 | | Header 2X5 Shrouded | TH | Farnell | 2215304 | 5
18 M1, M2, M3, M4, M5, M6, M7, M8, M9, M10, M11, | M12, M13, M14, M15, M16, M17, M18 | KortStøtte 84mm | TH | | | 5 | 6 | 5 | | 0 | 20
1 J25 | | Header 2X17 Shrouded | TH | Farnell | 2215313 | 10
1 U1 | | MOCD207R2M | SOIC | Farnell | 1086672 | 4
11 D1, D2, D3, D4, D5, D6, D7, D8, D11, D12, D13 | | SMD LED Green | 0603 | | | 1 | 6 | 0 | | 0 | 1500
35 | J13, J14, J15, J16, J17, J18, J19, J20, J21, J22, J23, J24, J26, J27, J31, J32, J33, J34, J35, J36, J37, J38, J39, J40, J41, J42, J43, J44, J45, J46, J47, J48, J49, J50, J51 | B2B-XH-A (LF)(SN) | TH | Farnell | 1516276 | 2 | 6 | 3 | | 0 | 120
2 D9, D10 | | SMD LED Red | 0603 | Farnell | 8554641 | 1 | 6 | 0 | | 2 | 50
38 | R1, R2, R3, R7, R8, R9, R13, R14, R15, R21, R25, R26, R27, R28, R29, R30, R31, R32, R33, R34, R35, R36, R37, R38, R39, R40, R41, R42, R43, R44, R45, R46, R47, R48, R49, R50, R51, R52 | 10k | 0603 | Farnell | 2447230 | 0 | 2 | 0 | | 72 | 4
14 R4, R5, R6, R10, R11, R12, R16, R17, R18, R19, R20, | R22, R23, R24 | 330R | 0603 | Farnell | 2447339 | 0 | 2 | 0 | | 36 | 45
