Cable89/tesla-driver/05_Hardware/TK100_Tonegenerator/TK106_MIDI/Project Outputs/TK106_MIDI_Konnektorer.PDF

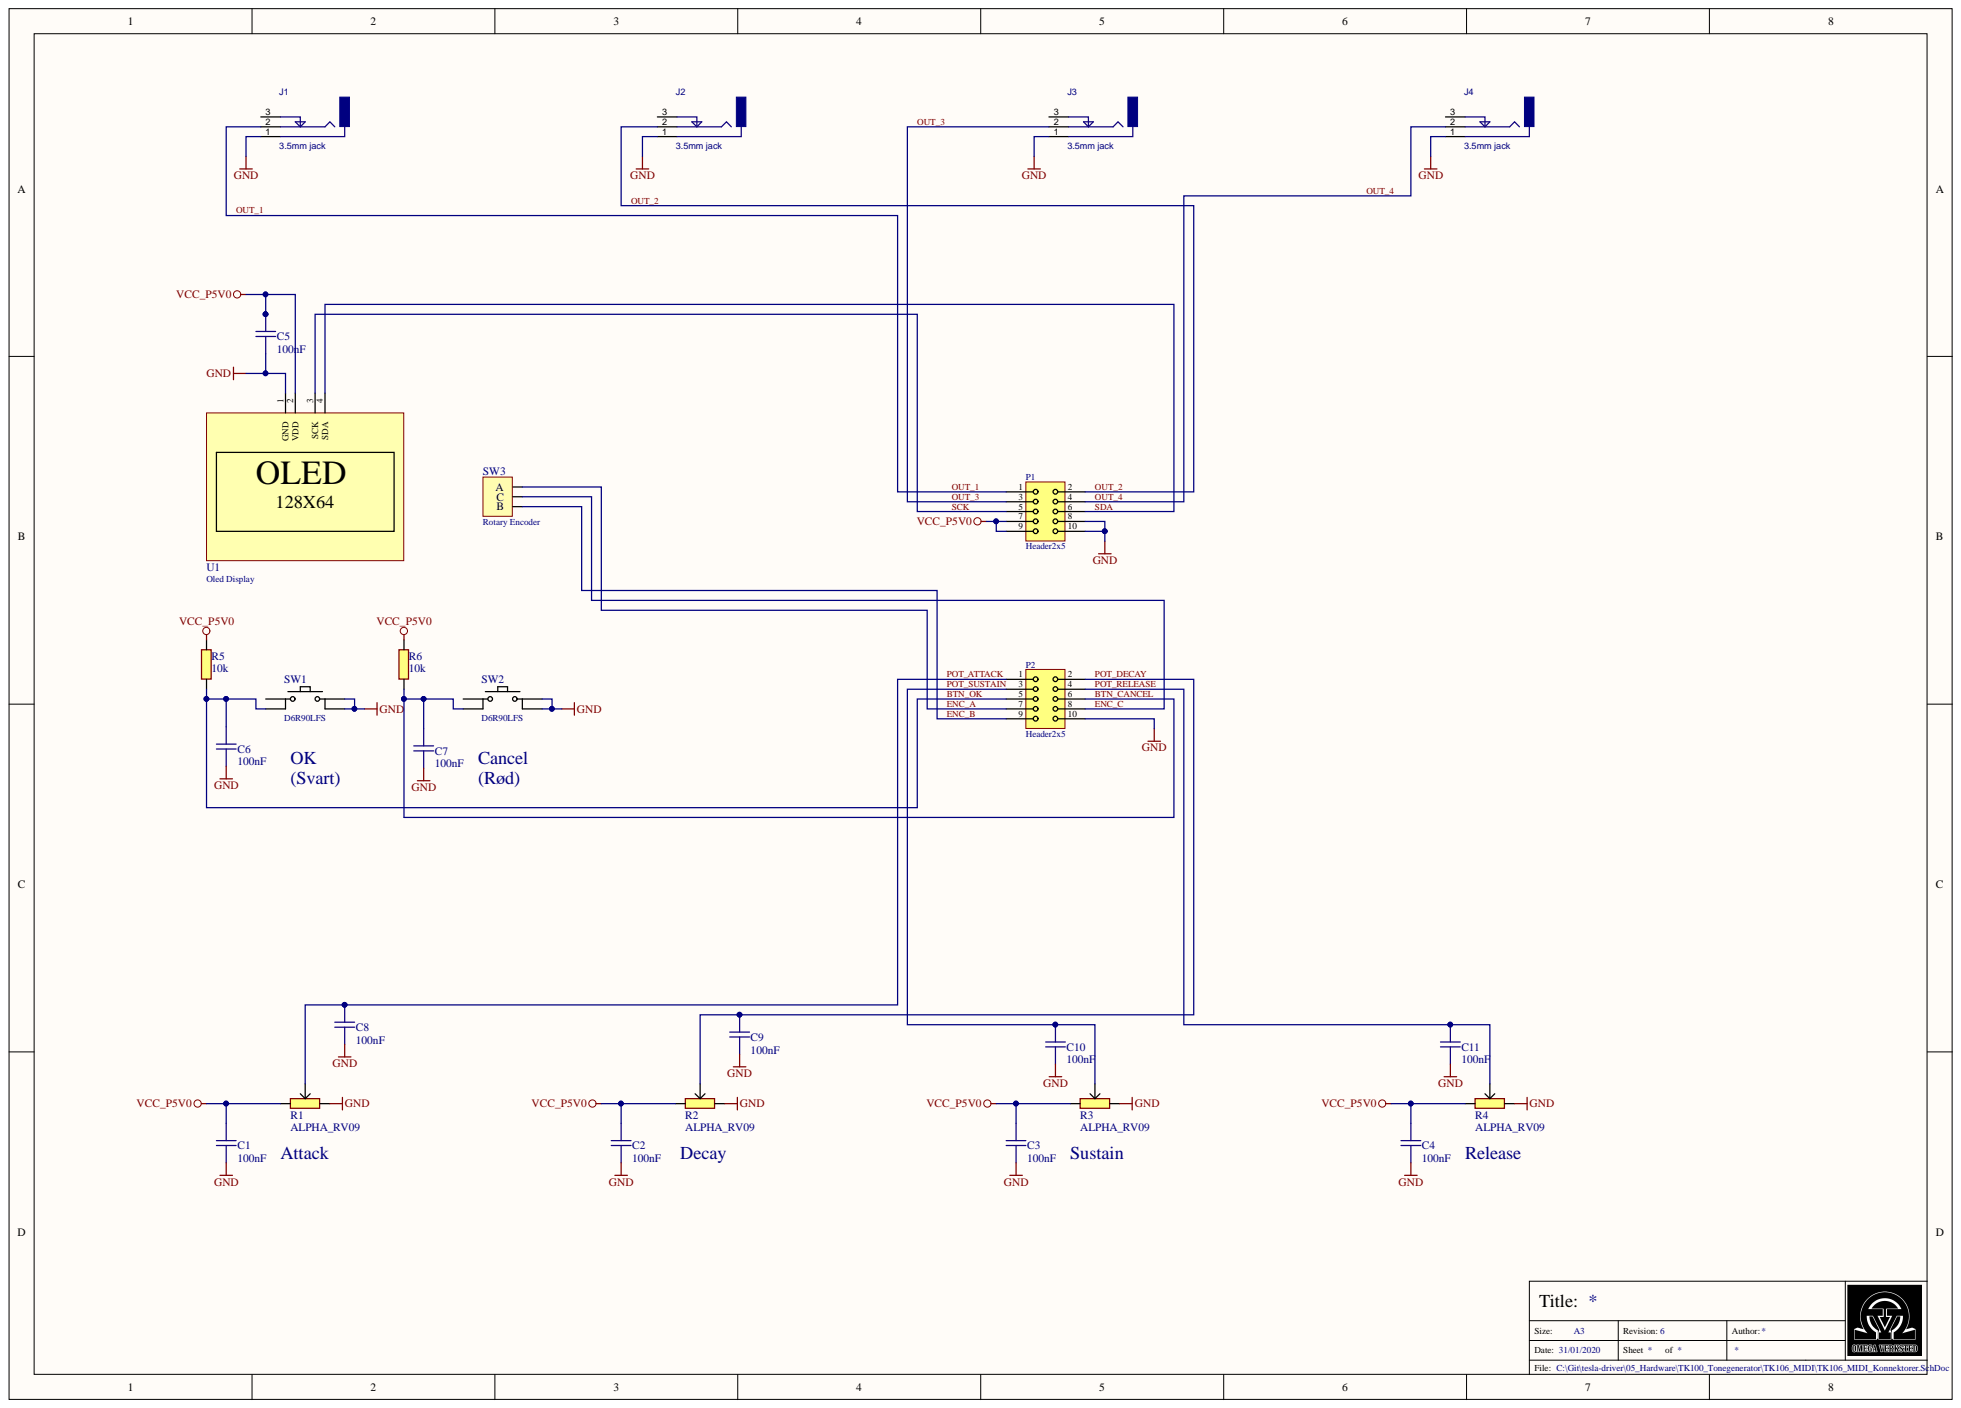
[picture p129: page 1]

OLED 128X64

POT_SUSTAIN | 3 | 4 POT_RELEASE
BTN_OK | 5 | | 6 | BTN_CANCEL
ENC_A | 7 | 8 | ENC_C
ENC_B | 9 | | 10

Title: *

Size: A3 | Revision: 6 | Author: *

Date: 31/01/2020 | Sheet * of * | *

C:\Git\tesla-driver\05_Hardware\TK100_Tonegenerator\TK106_MIDI\TK106_MIDI_Konnektorer.SchDoc

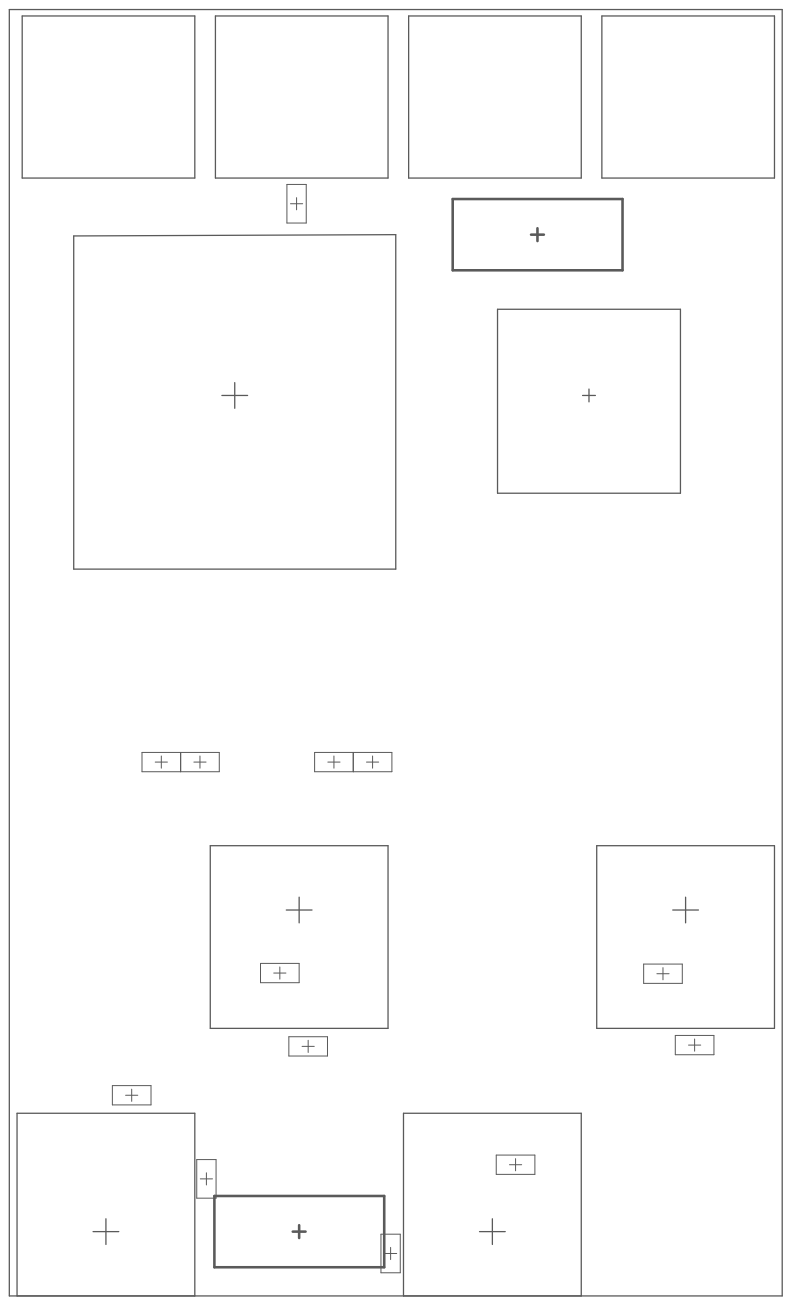
[picture p130: page 2]

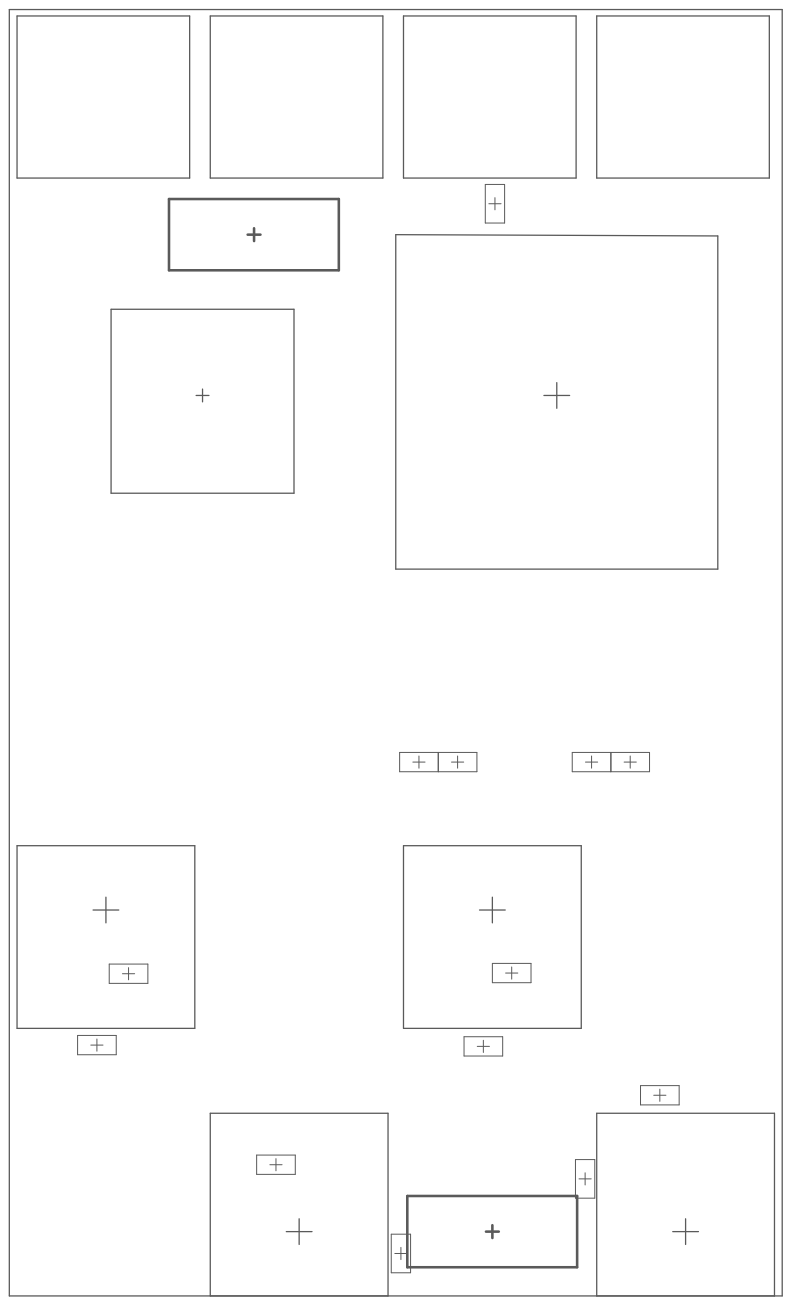
[picture p131: page 3]

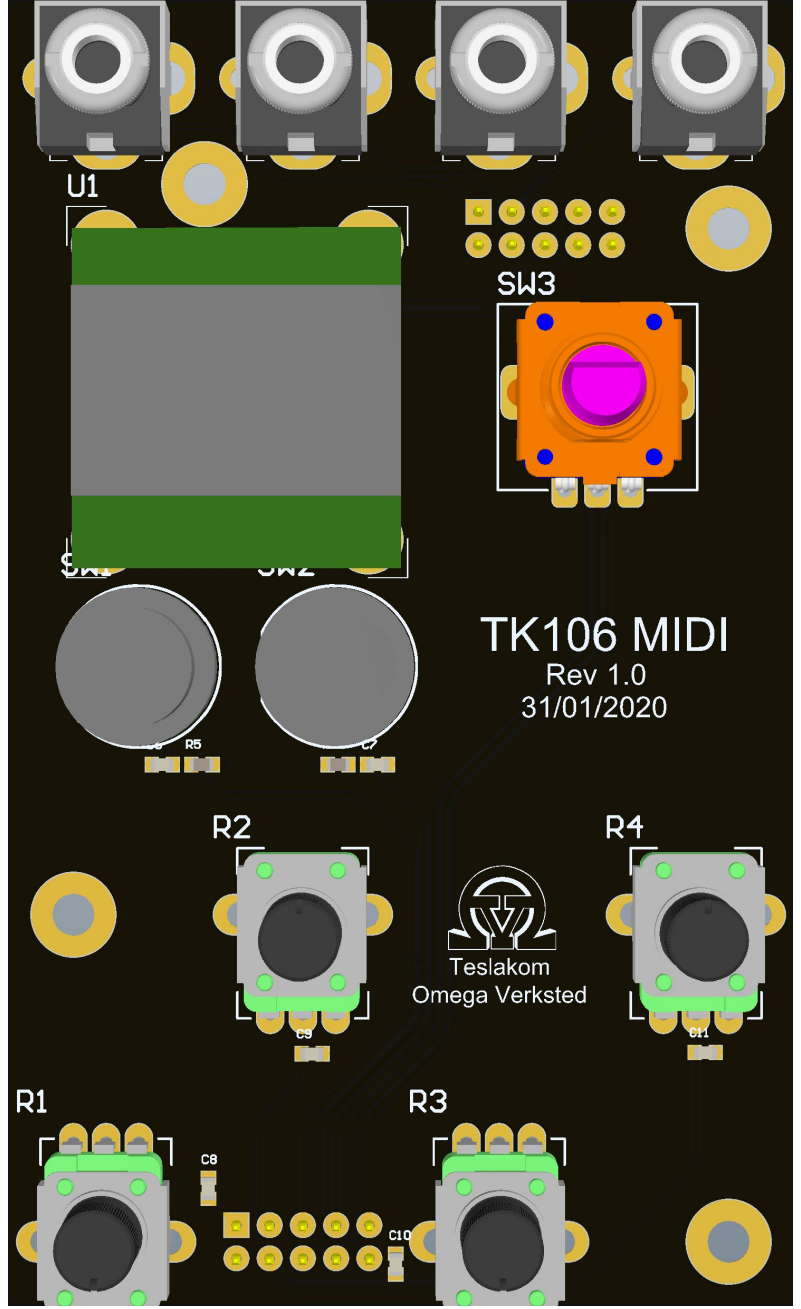
[picture p132: page 4]

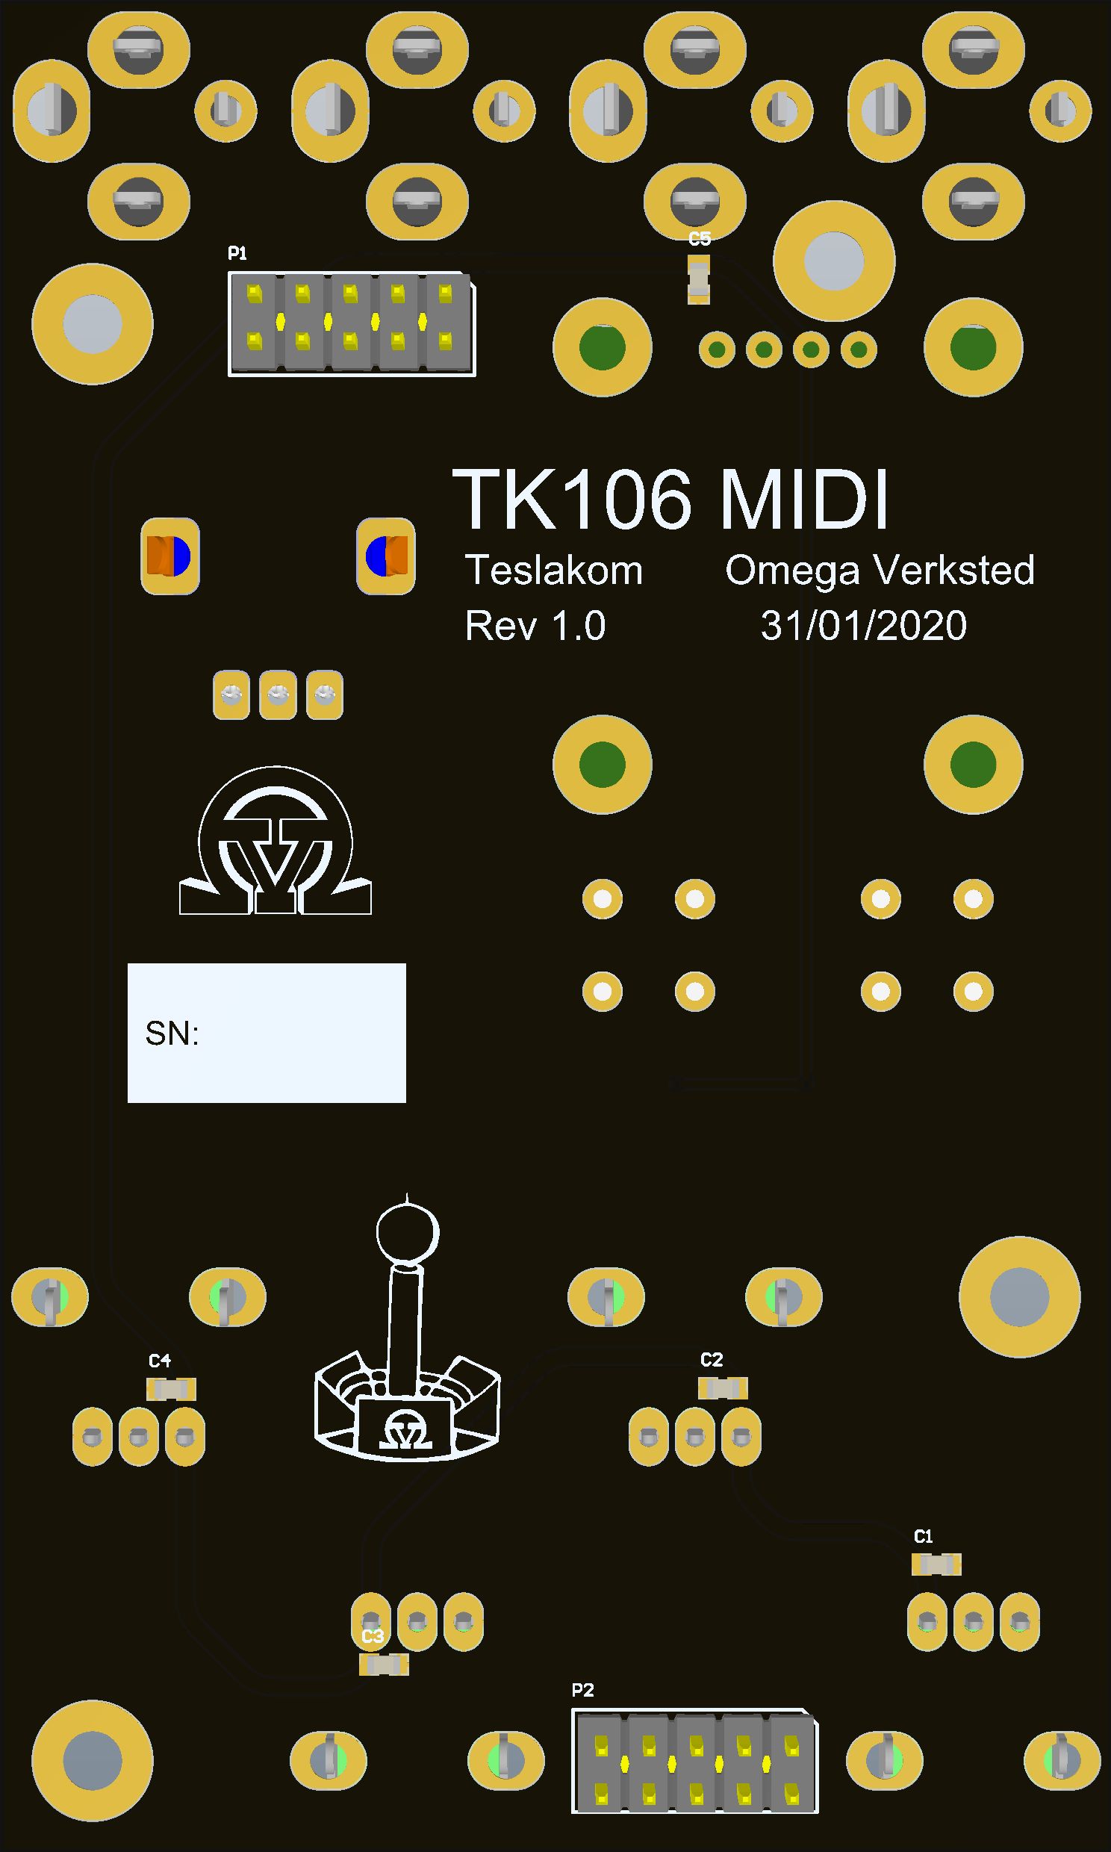
[picture p133: page 5]

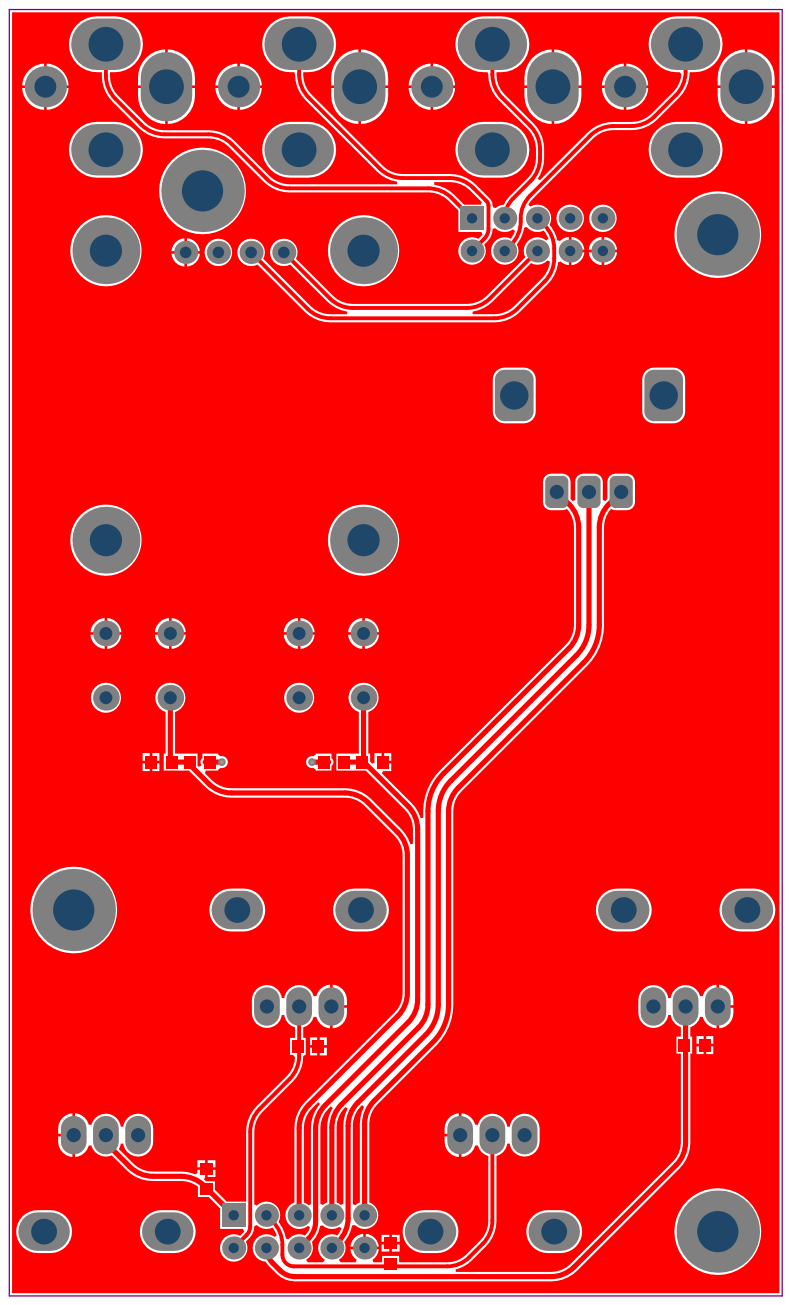
[picture p134: page 6]

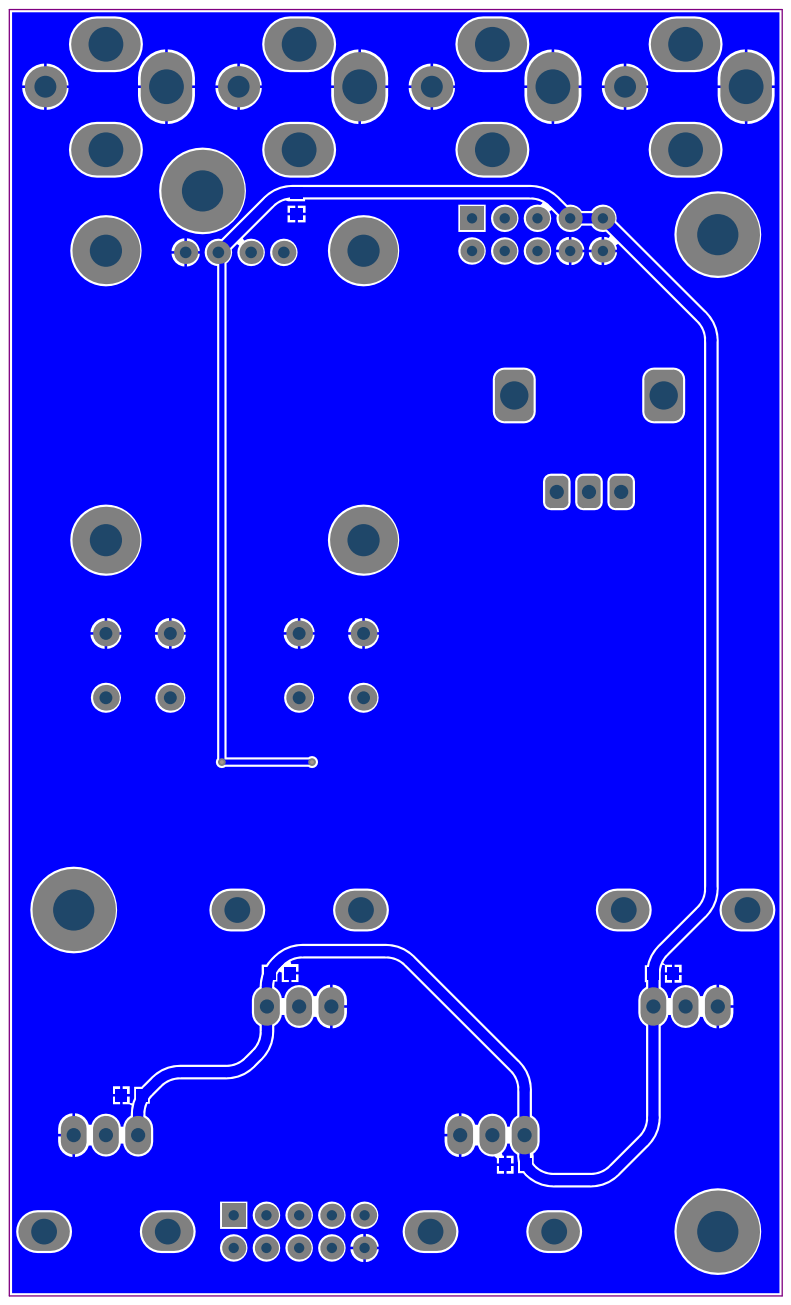
[picture p135: page 7]

Designato r | Qua ntit y | navn | beskrivelse | leverandor | leverandor_vare nr | antall
R5, R6 | 2 | 10k | | Farnell | 2447230 | 1200
C1, C2, C3, C4, C5, C6, C7, C8, C9, C10, C11 | 11 | 100nF | | Farnell | 1759122 | 1000
R1, R2, R3, R4 | 4 | ALPHA_RV09
SW1, SW2 | 2 | D6R90LFS | | Farnell | 1201375
P1, P2 | 2 | Header 2X5 | Header
U1 | 1 | Oled Display | | | | 16
J1, J2, J3, J4 | 4 | PJ301BM | 3.5mm Mono jack
SW3 | 1 | Rotary Encoder | | Farnell | 2065070
