Cable89/tesla-driver/05_Hardware/TK100_Tonegenerator/TK106_MIDI/Project Outputs/TK106_Frontpanel.PDF

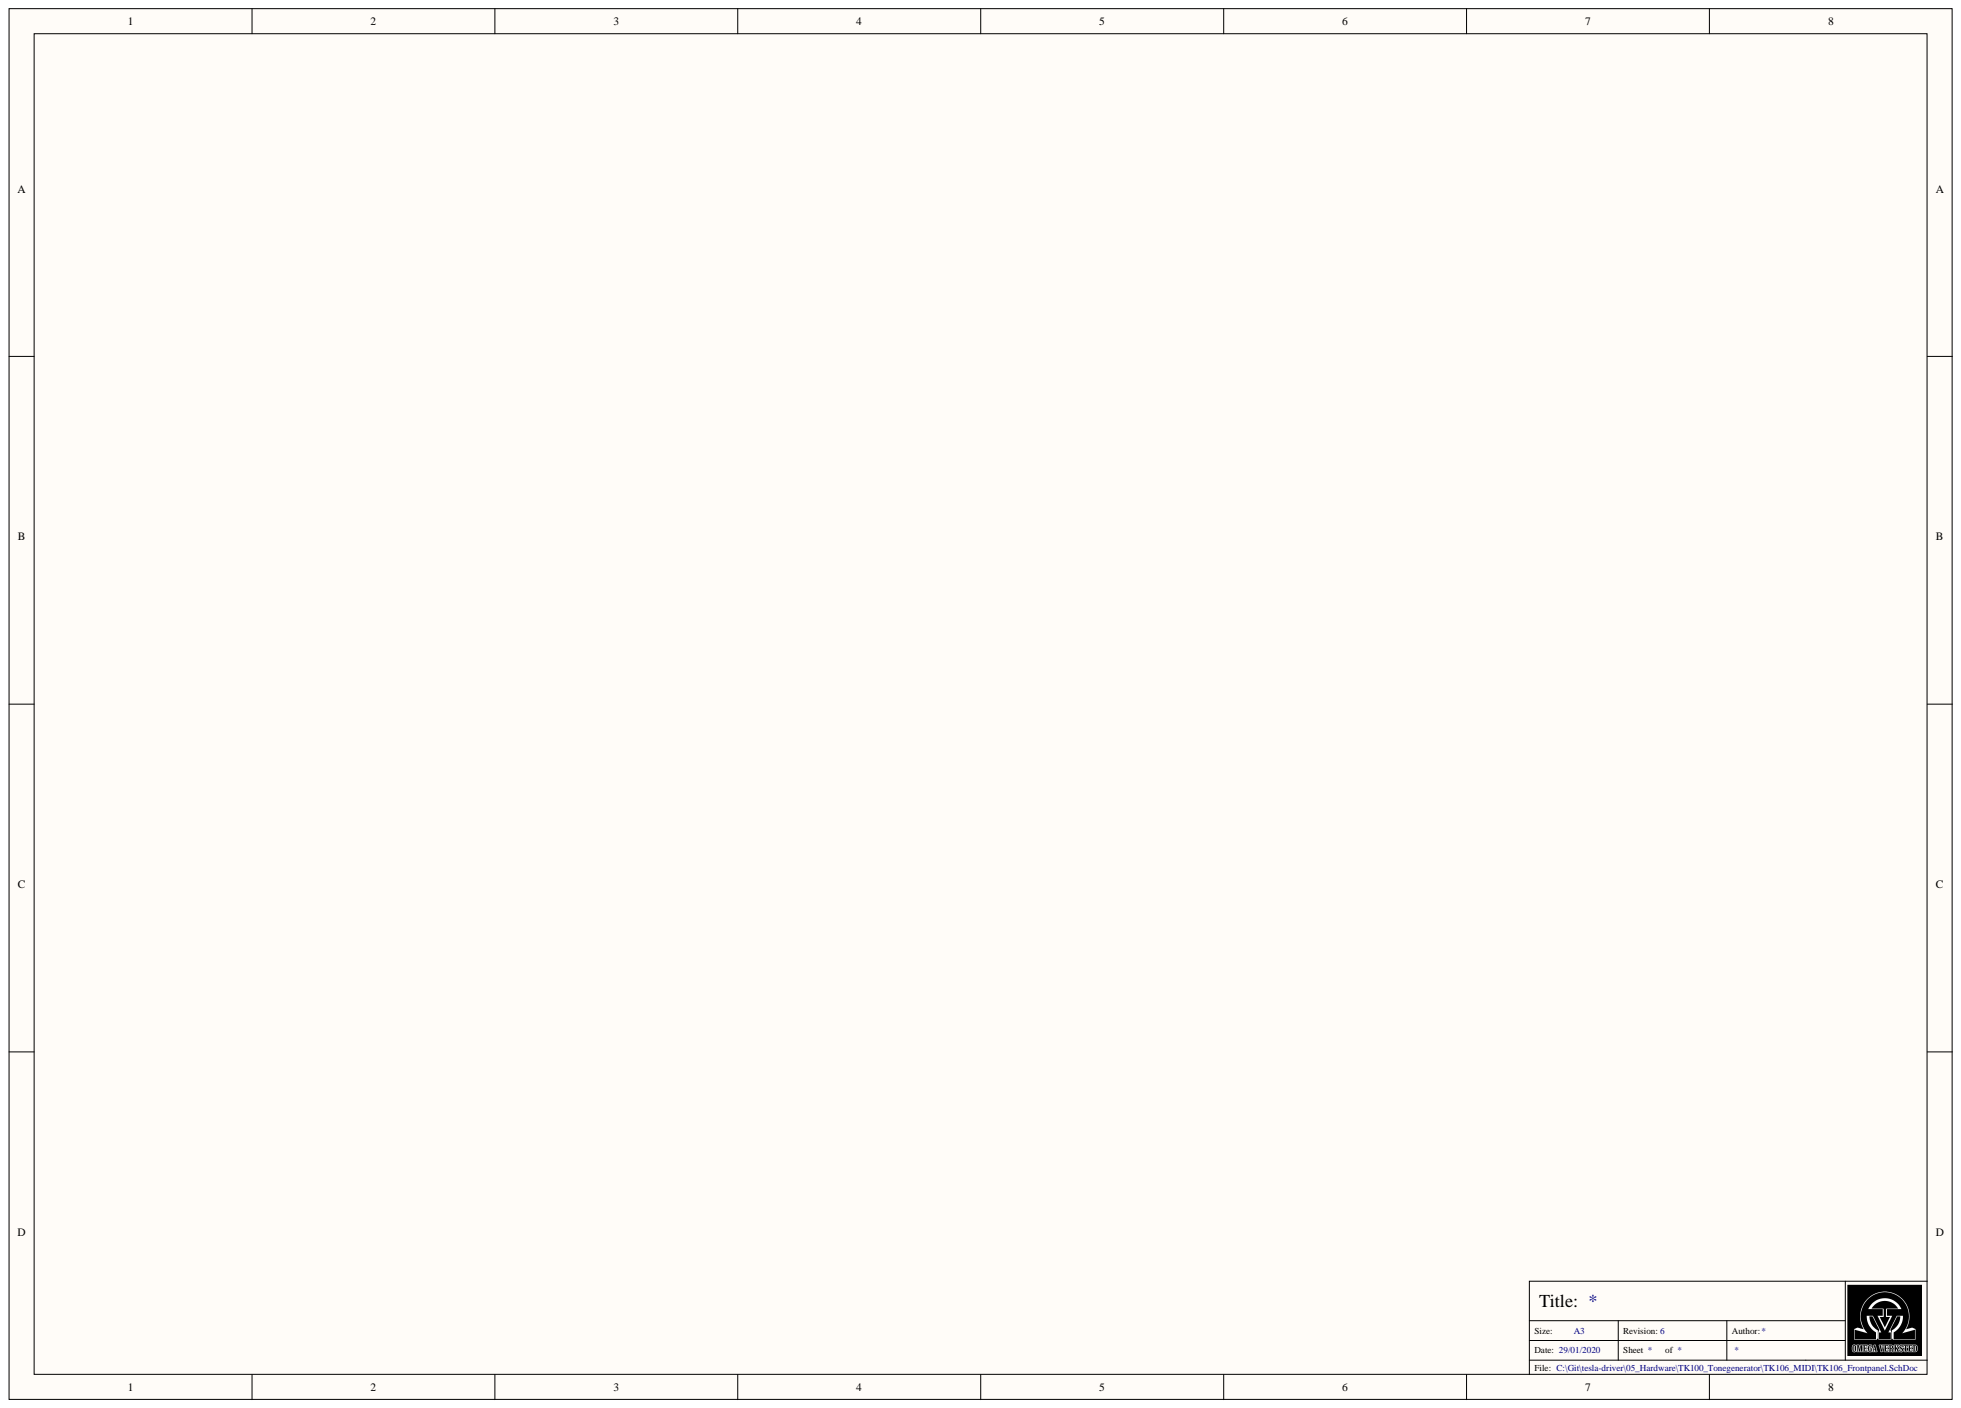
[picture p136: page 1]

Title: *

Size: A3 | Revision: 6 | Author: *

Date: 29/01/2020 | Sheet * of * | *

C:\Git\tesla-driver\05_Hardware\TK100_Tonegenerator\TK106_MIDI\TK106_Frontpanel.SchDoc

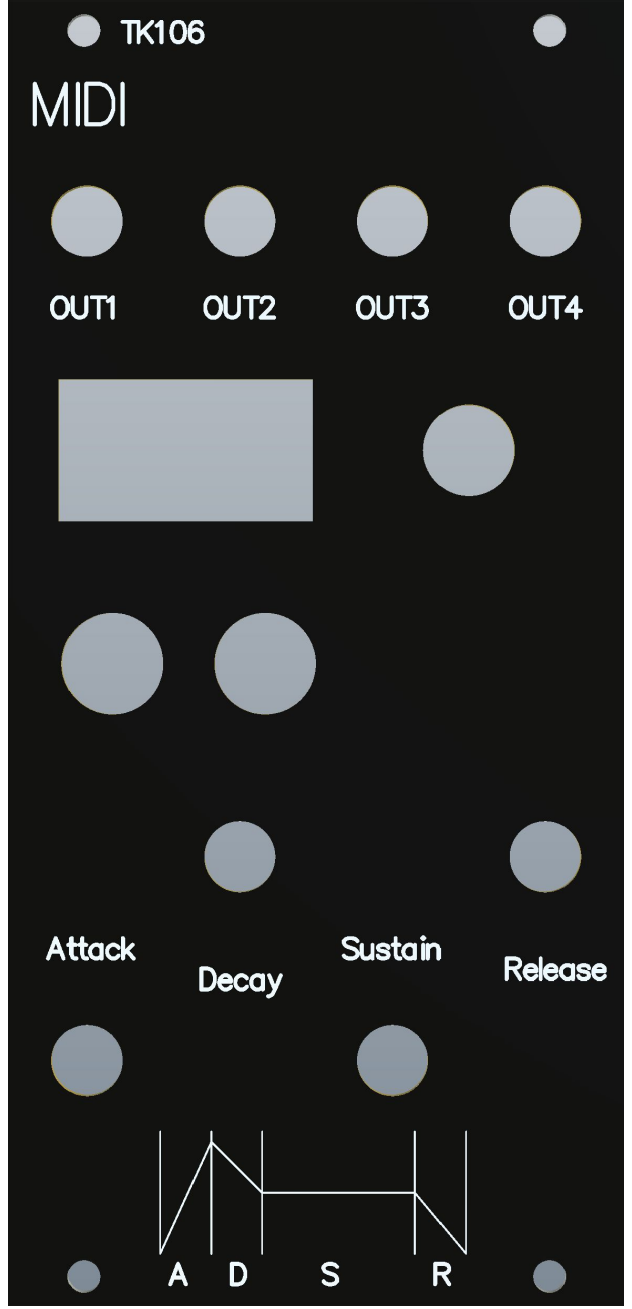
[picture p137: page 4]

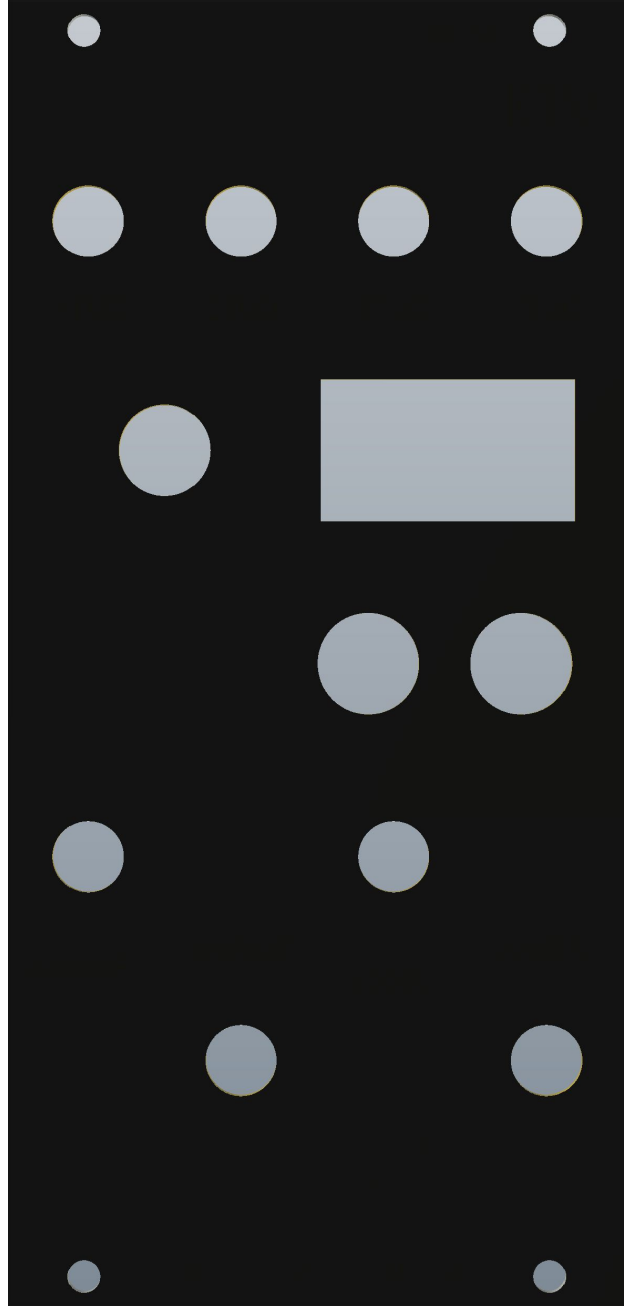
[picture p138: page 5]
