Cable89/tesla-driver/05_Hardware/TK100_Tonegenerator/TK106_MIDI/Project Outputs/TK106_MIDI.PDF

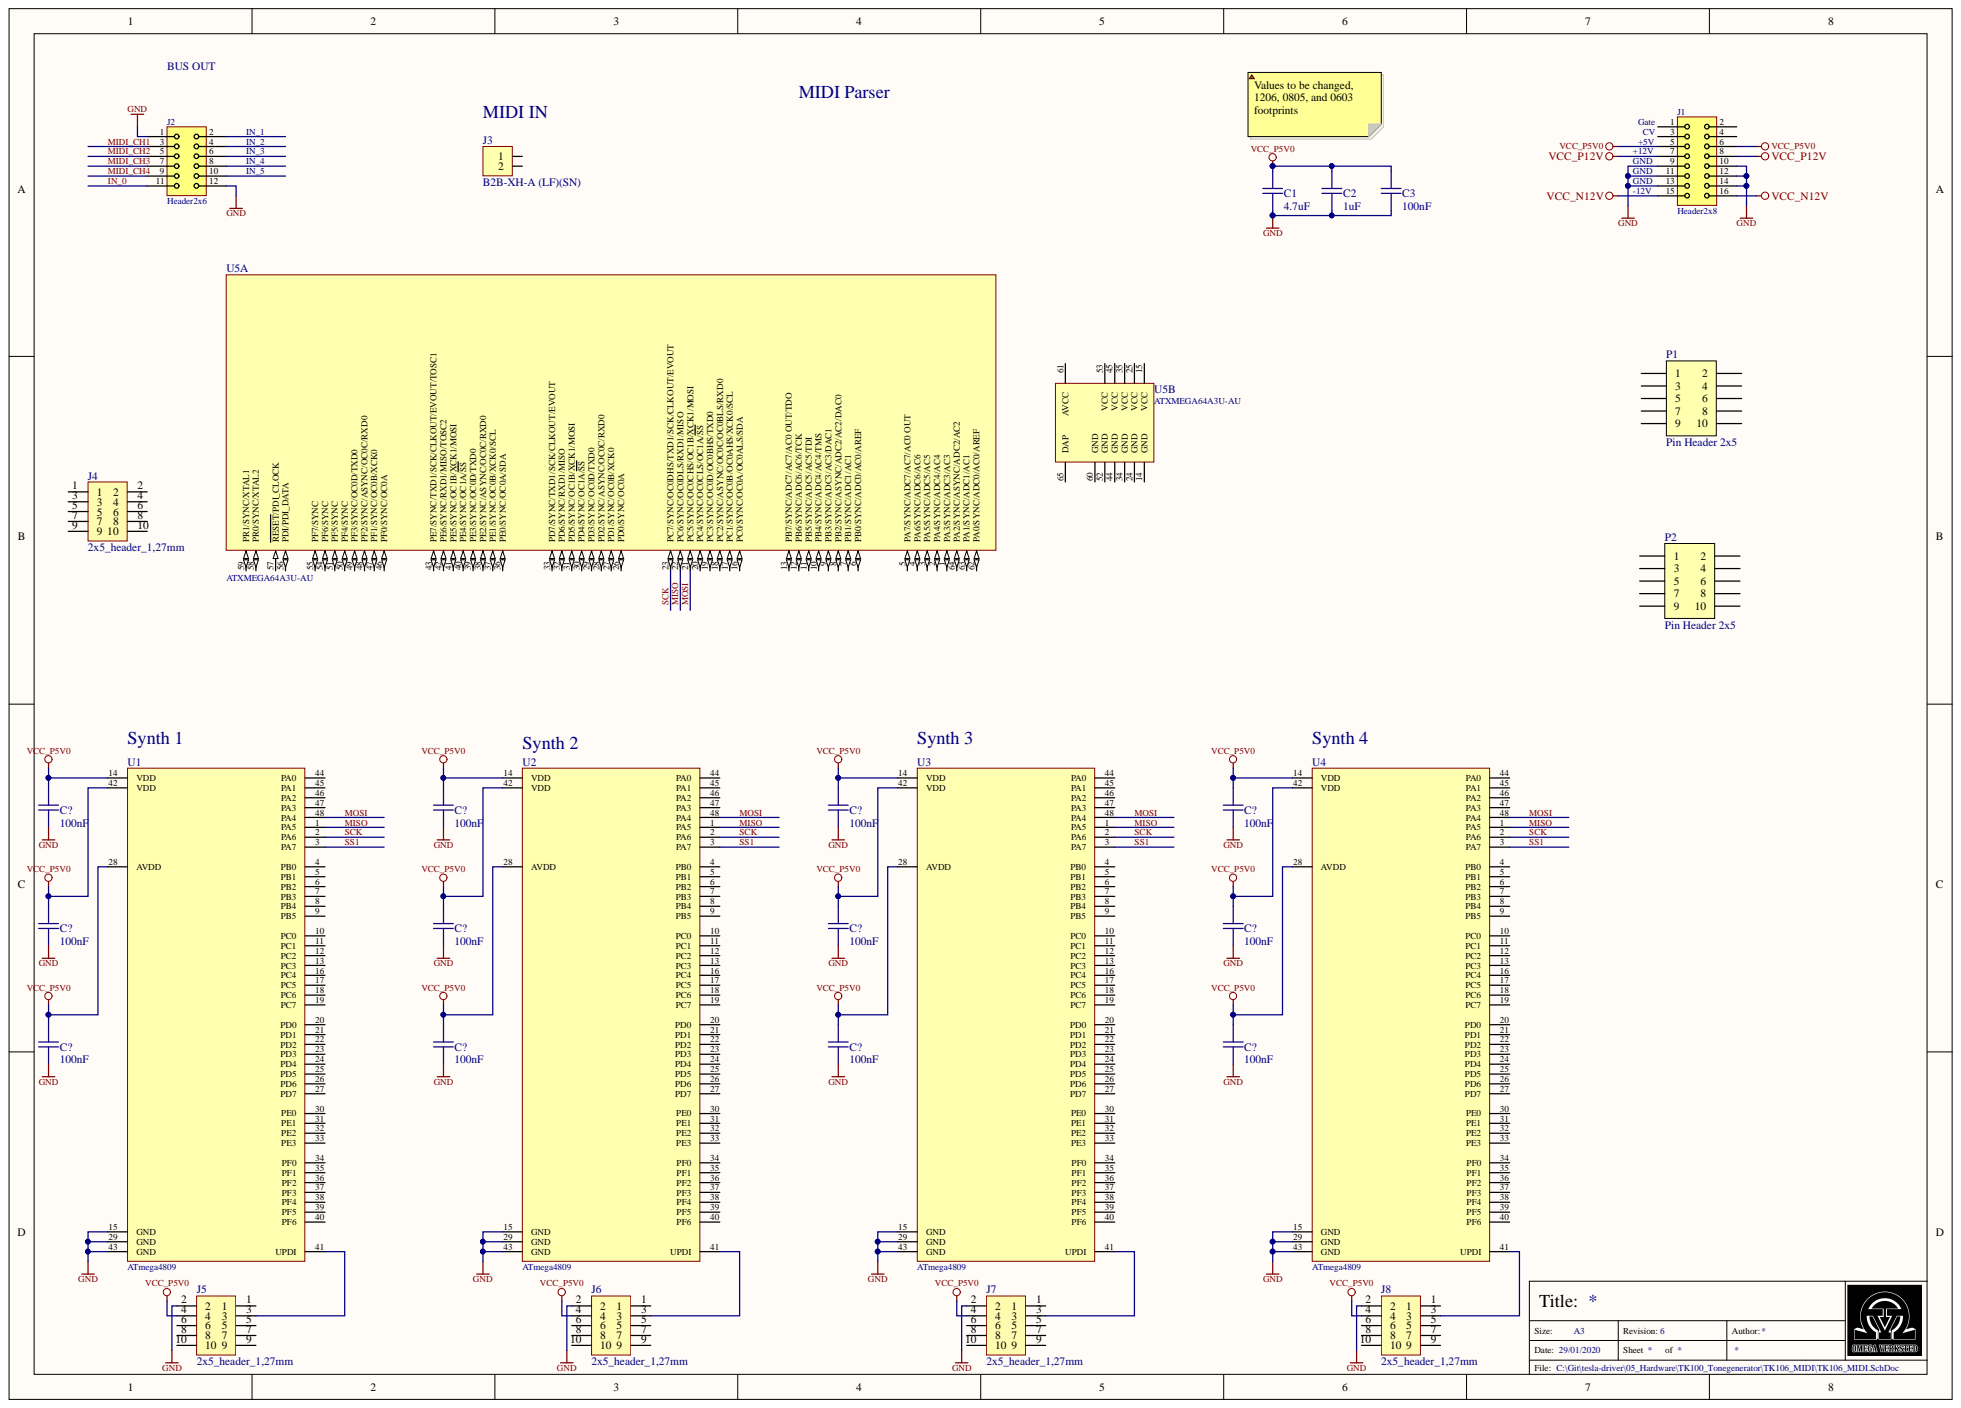
[picture p139: page 1]

Values to be changed,
1206, 0805, and 0603
footprints

GND | 13 | 14
-12V

PC7/SYNC/OC0DHS/TXD1/SCK/CLKOUT/EVOUT 23

PE7/SYNC/TXD1/SCK/CLKOUT/EVOUT/TOSC1 43

PD6/SYNC/RXD1/MISO 32 PD7/SYNC/TXD1/SCK/CLKOUT/EVOUT 33

PC3/SYNC/OC0D/OC0BHS/TXD0 19 PC4/SYNC/OC0CLS/OC1A/SS 20 PC5/SYNC/OC0CHS/OC1B/XCK1/MOSI 21 PC6/SYNC/OC0DLS/RXD1/MISO 22

PC0/SYNC/OC0A/OC0ALS/SDA 16 PC1/SYNC/OC0B/OC0AHS/XCK0/SCL 17 PC2/SYNC/ASYNC/OC0C/OC0BLS/RXD0 18

PE2/SYNC/ASYNC/OC0C/RXD0 38 PE3/SYNC/OC0D/TXD0 39 PE4/SYNC/OC1A/SS 40 PE5/SYNC/OC1B/XCK1/MOSI 41

PD0/SYNC/OC0A 26 PD1/SYNC/OC0B/XCK0 27 PD2/SYNC/ASYNC/OC0C/RXD0 28 PD3/SYNC/OC0D/TXD0 29 PD4/SYNC/OC1A/SS 30

PA0/SYNC/ADC0/AC0/AREF 62 PA1/SYNC/ADC1/AC1 63 PA2/SYNC/ASYNC/ADC2/AC2 64 PA3/SYNC/ADC3/AC3 1 PA4/SYNC/ADC4/AC4 2 PA5/SYNC/ADC5/AC5 3

Title: *

Size: A3 | Revision: 6 | Author: *

Date: 29/01/2020 | Sheet * of * | *

C:\Git\tesla-driver\05_Hardware\TK100_Tonegenerator\TK106_MIDI\TK106_MIDI.SchDoc

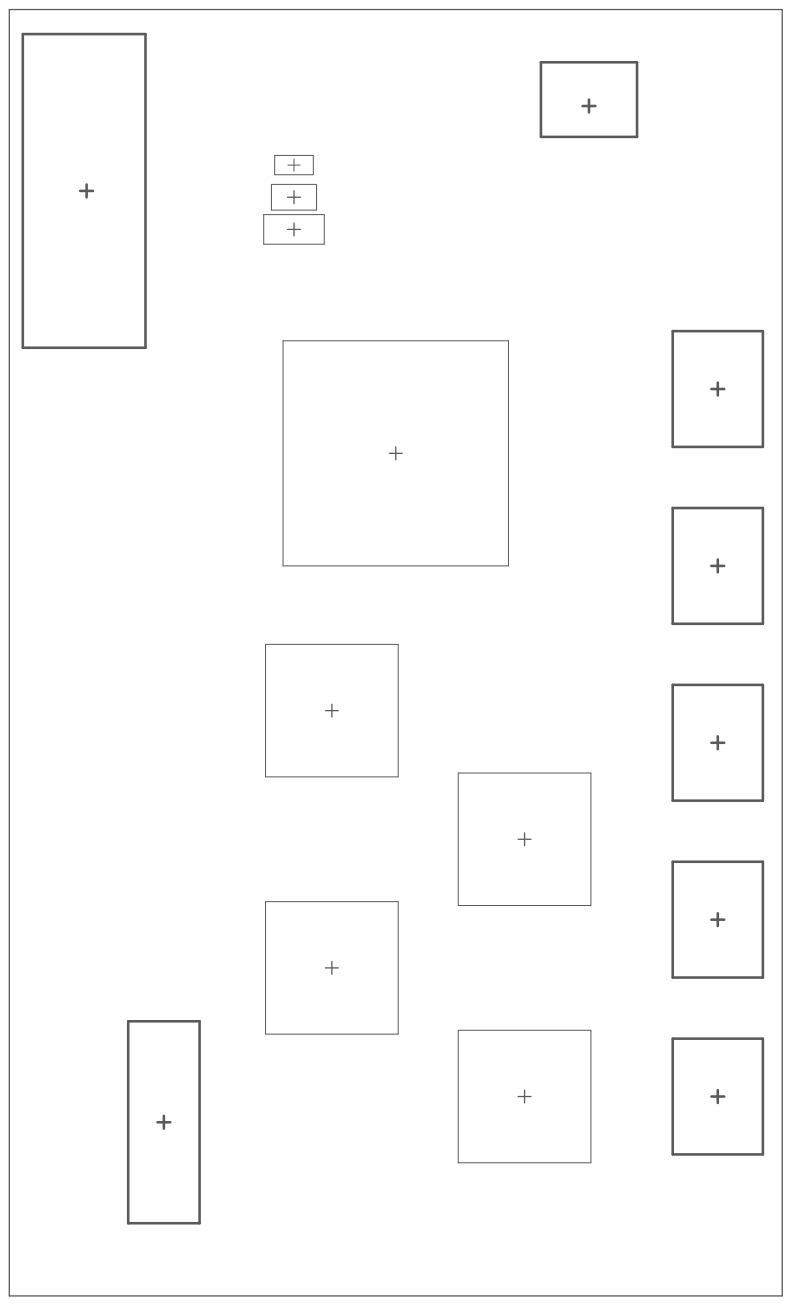
[picture p140: page 2]

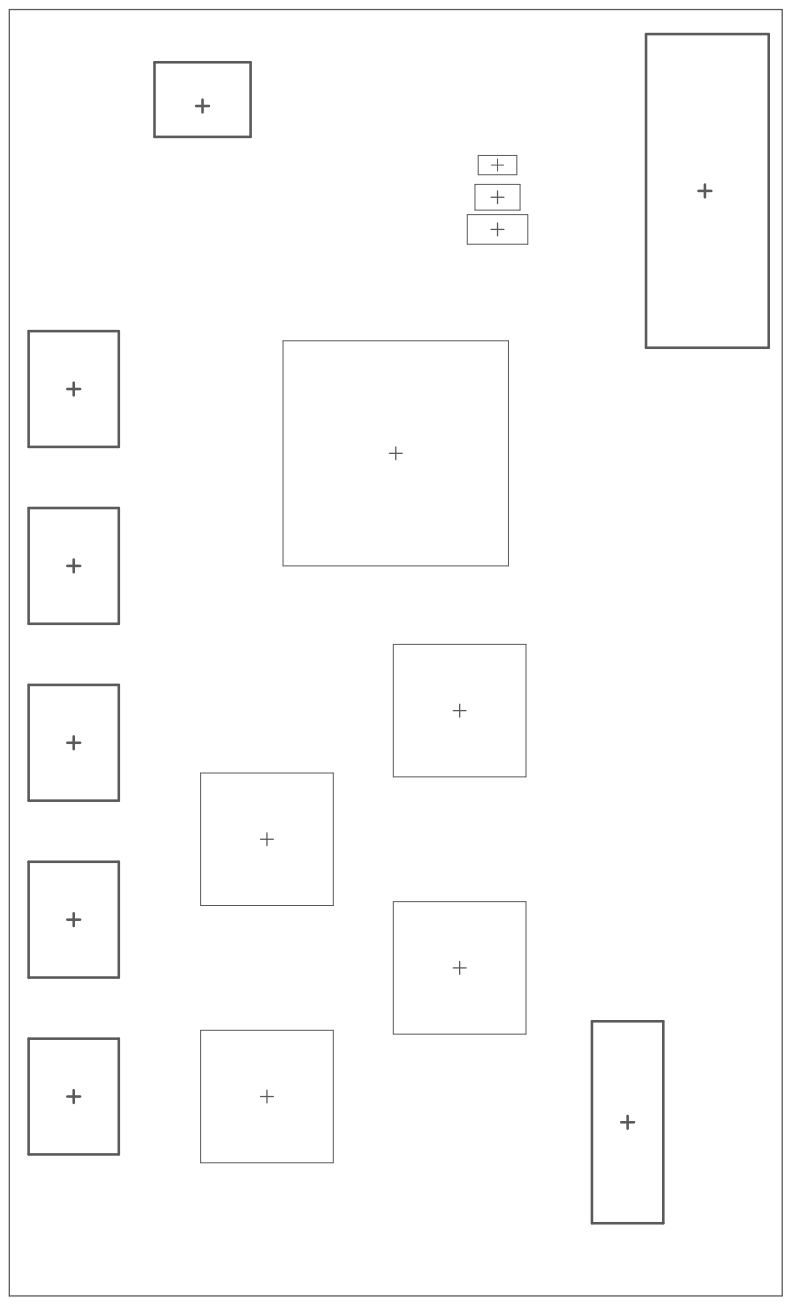
[picture p141: page 3]

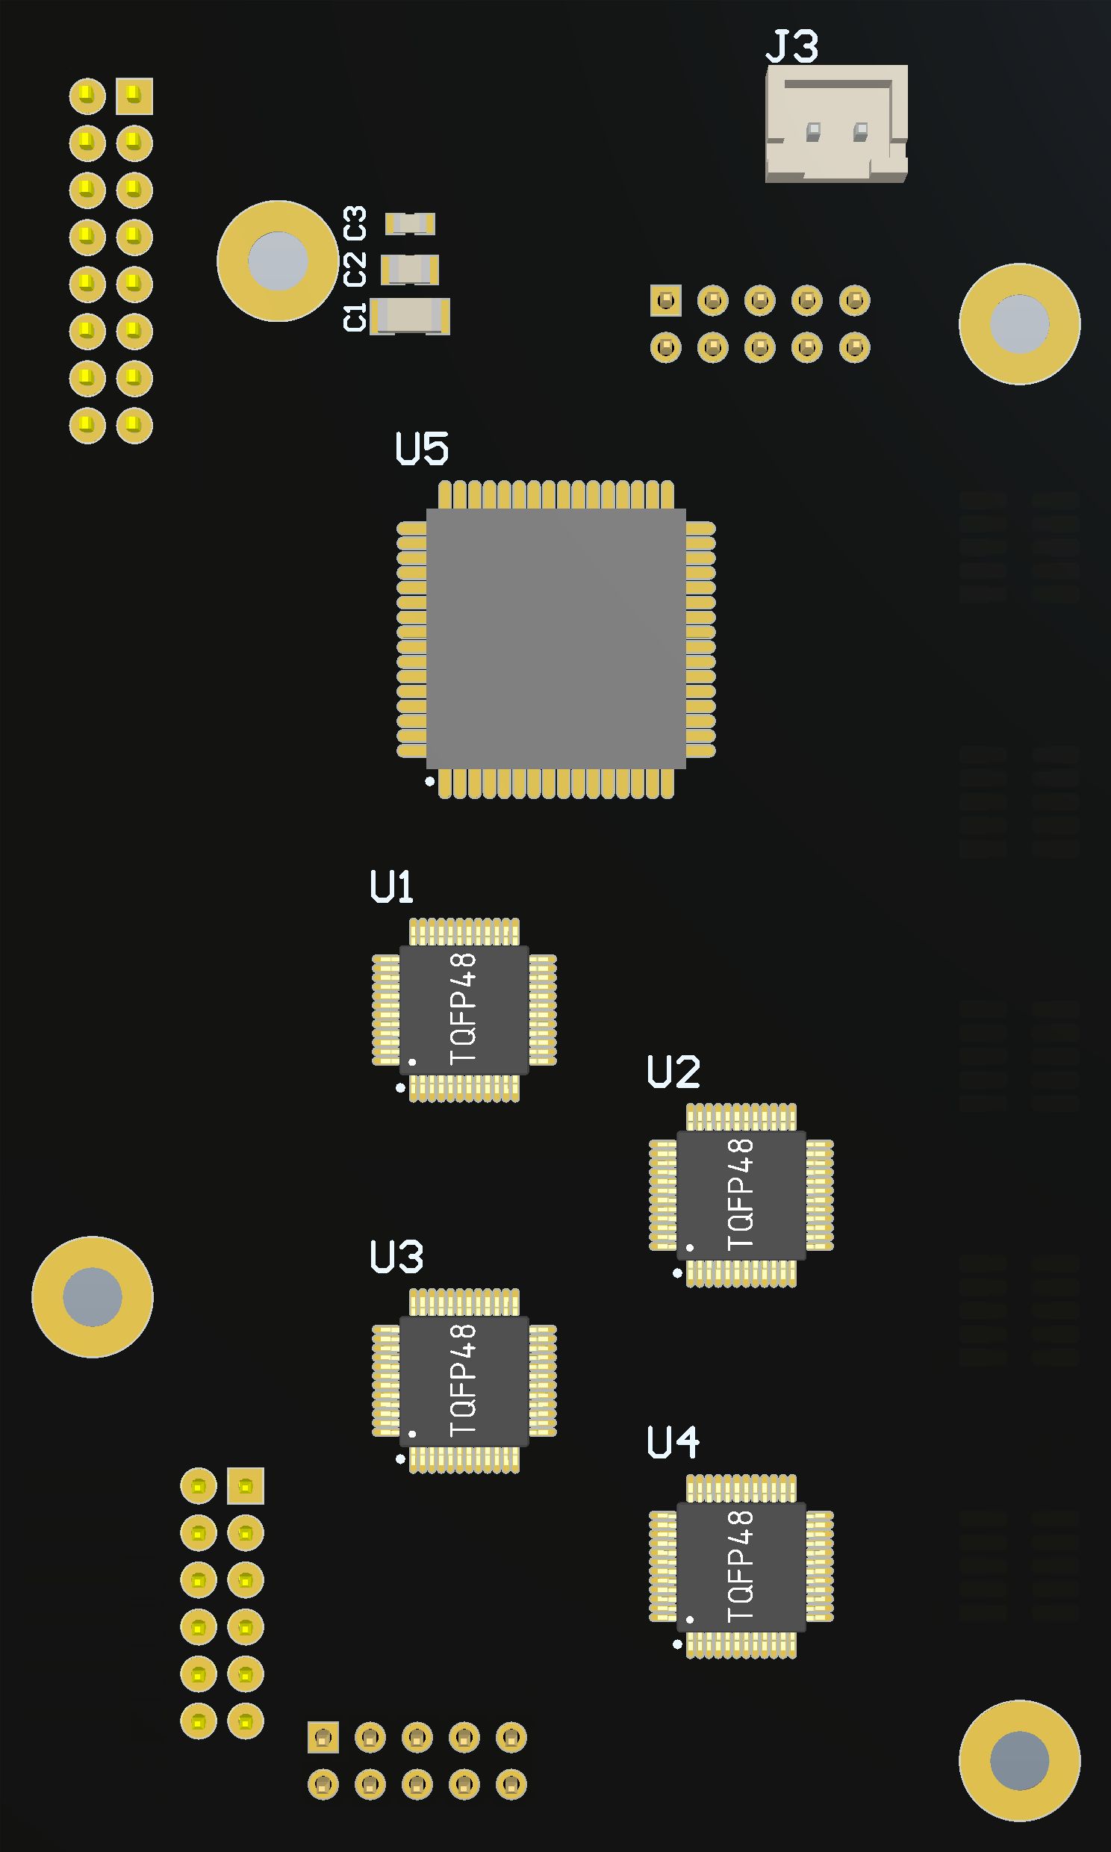
[picture p142: page 4]

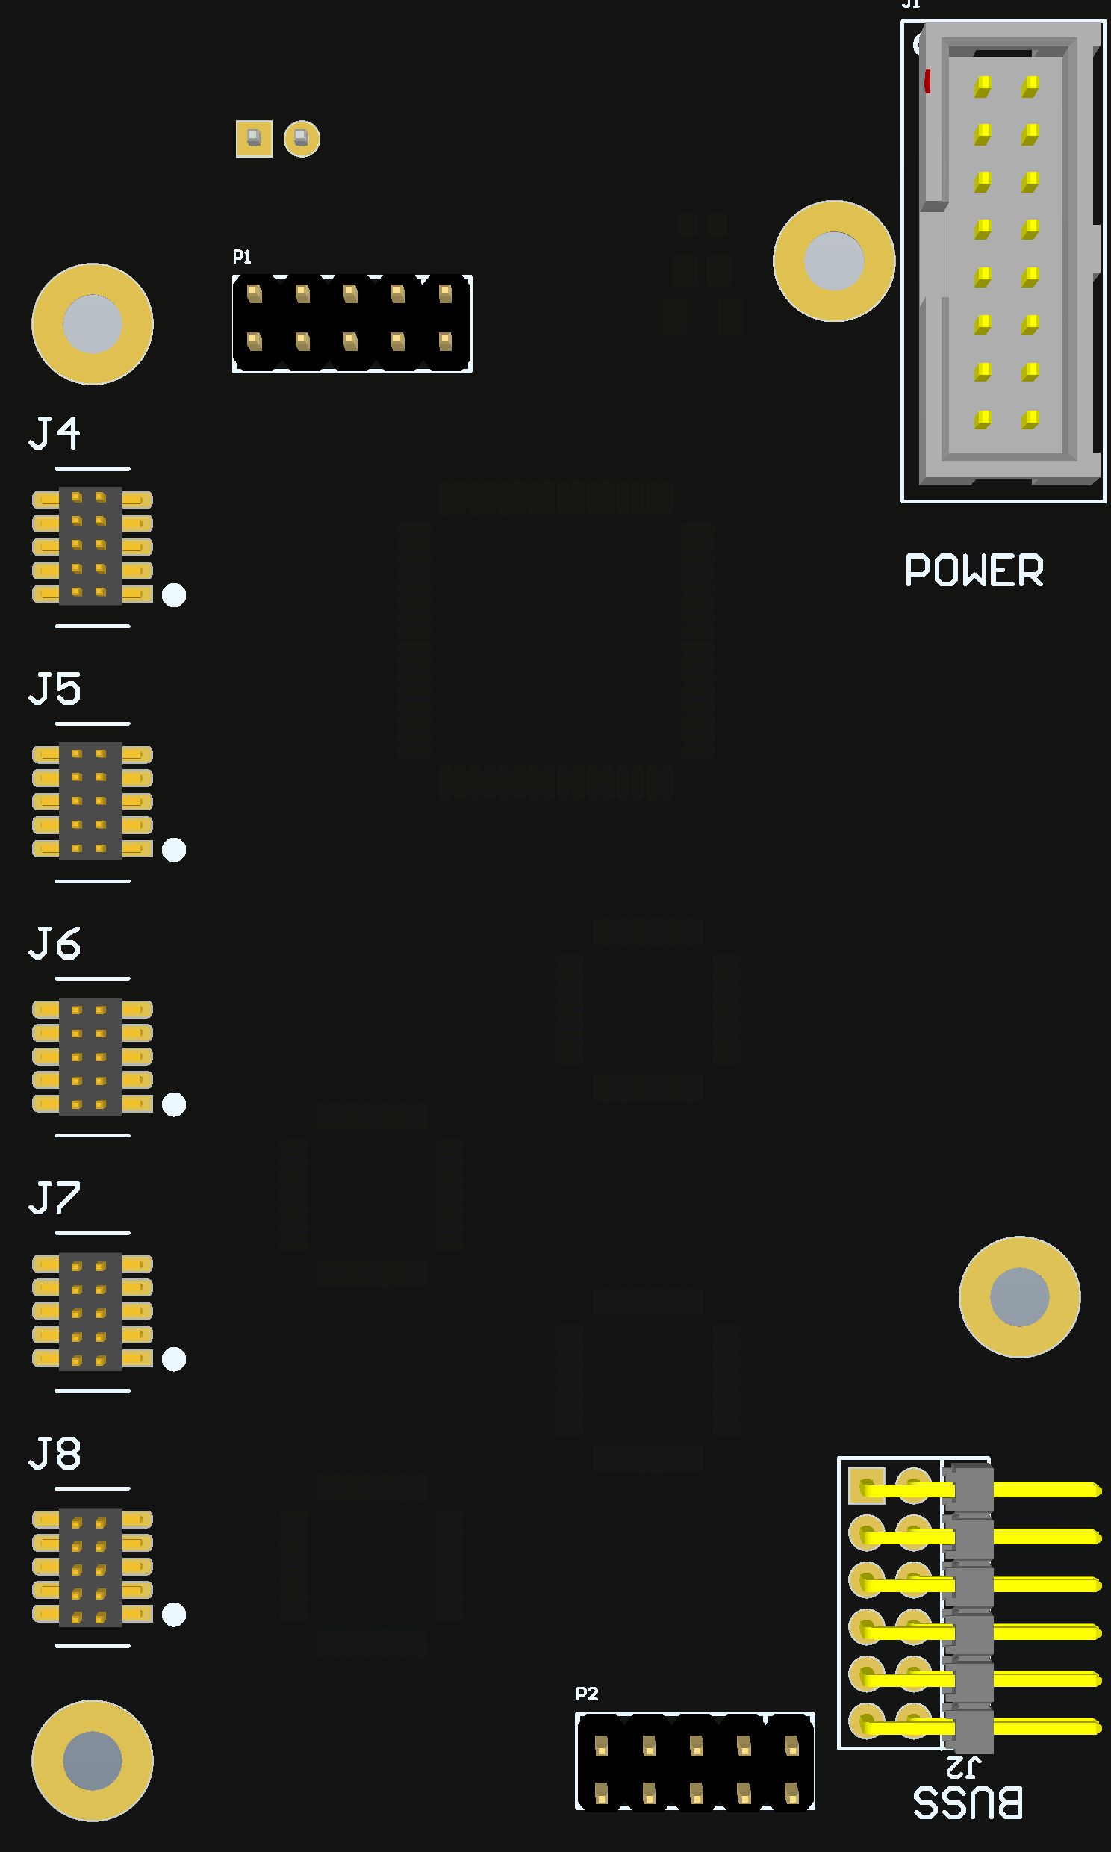
[picture p143: page 5]

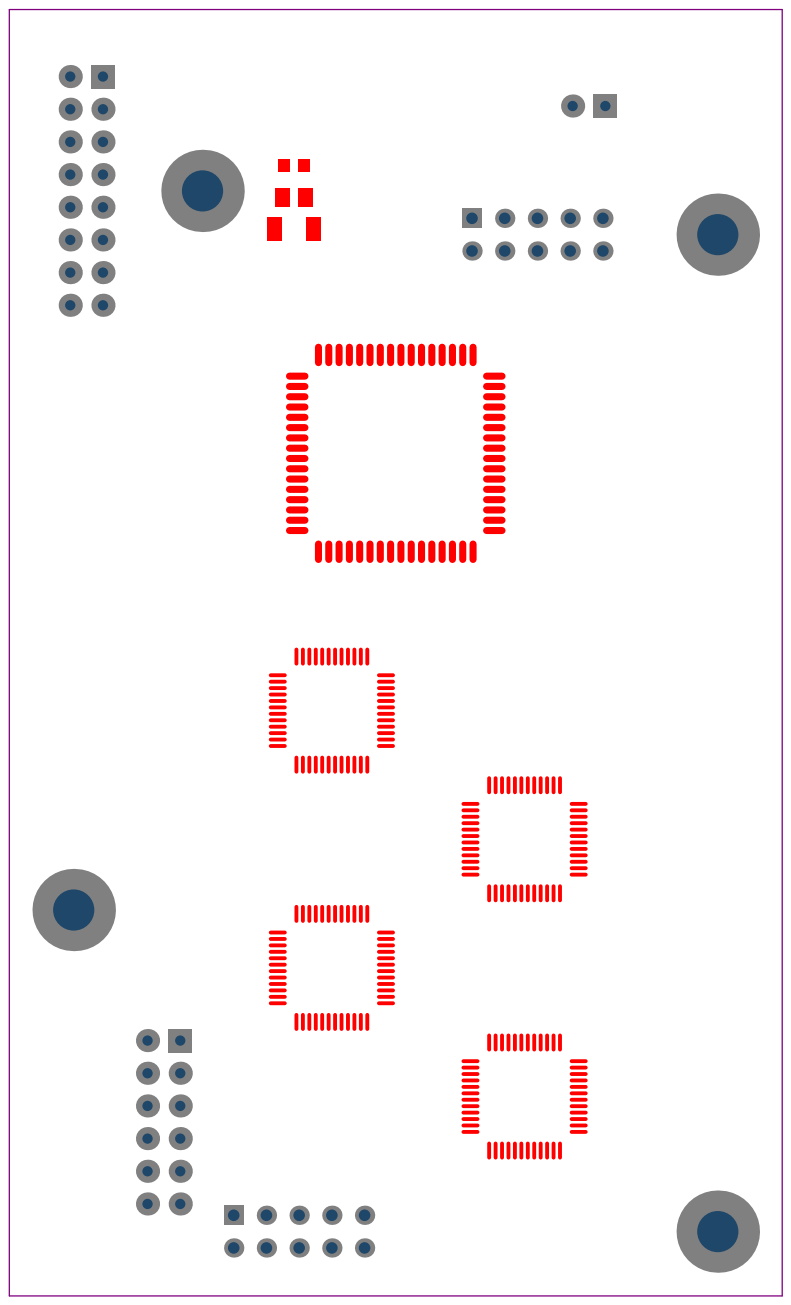
[picture p144: page 6]

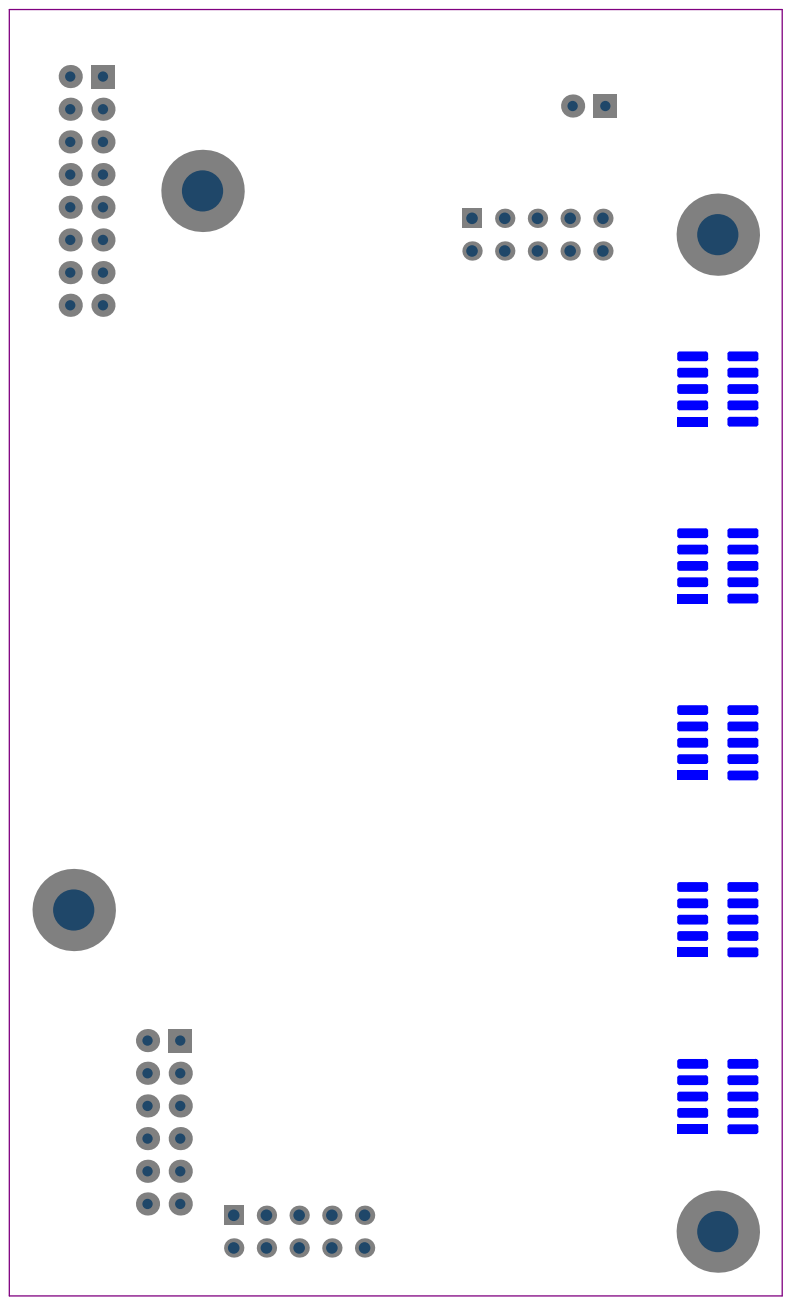
[picture p145: page 7]

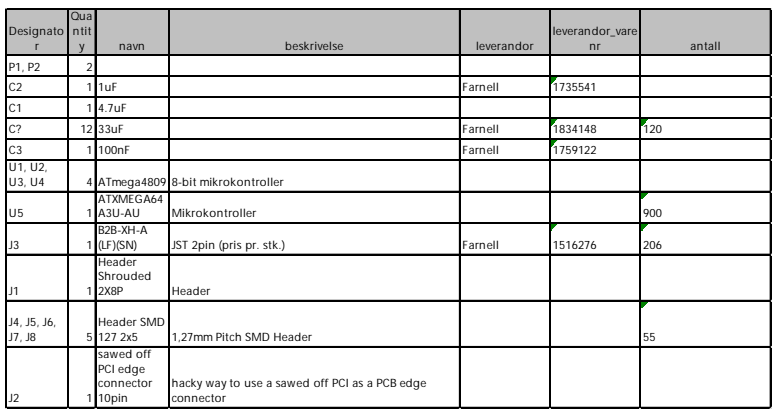
[picture p146: page 8]

Designato r | Qua ntit y | navn | beskrivelse | leverandor | leverandor_vare nr | antall

P1, P2 | 2
C2 | 1 | 1uF | | Farnell | 1735541
C1 | 1 | 4.7uF
C? | 12 | 33uF | | Farnell | 1834148 | 120
C3 | 1 | 100nF | | Farnell | 1759122
U1, U2, U3, U4 | 4 | ATmega4809 | 8-bit mikrokontroller

U5 | 1 | ATXMEGA64 A3U-AU | Mikrokontroller | | | 900

J3 | 1 | B2B-XH-A (LF)(SN) | JST 2pin (pris pr. stk.) | Farnell | 1516276 | 206

J1 | 1 | Header Shrouded 2X8P | Header

J4, J5, J6, J7, J8 | 5 | Header SMD 127 2x5 | 1,27mm Pitch SMD Header | | | 55

J2 | 1 | sawed off PCI edge connector 10pin | hacky way to use a sawed off PCI as a PCB edge connector
