Cable89/tesla-driver/05_Hardware/TK100_Tonegenerator/TK103_Multiplexer/Project Outputs/TK103_Multiplexer_frontpanel.PDF

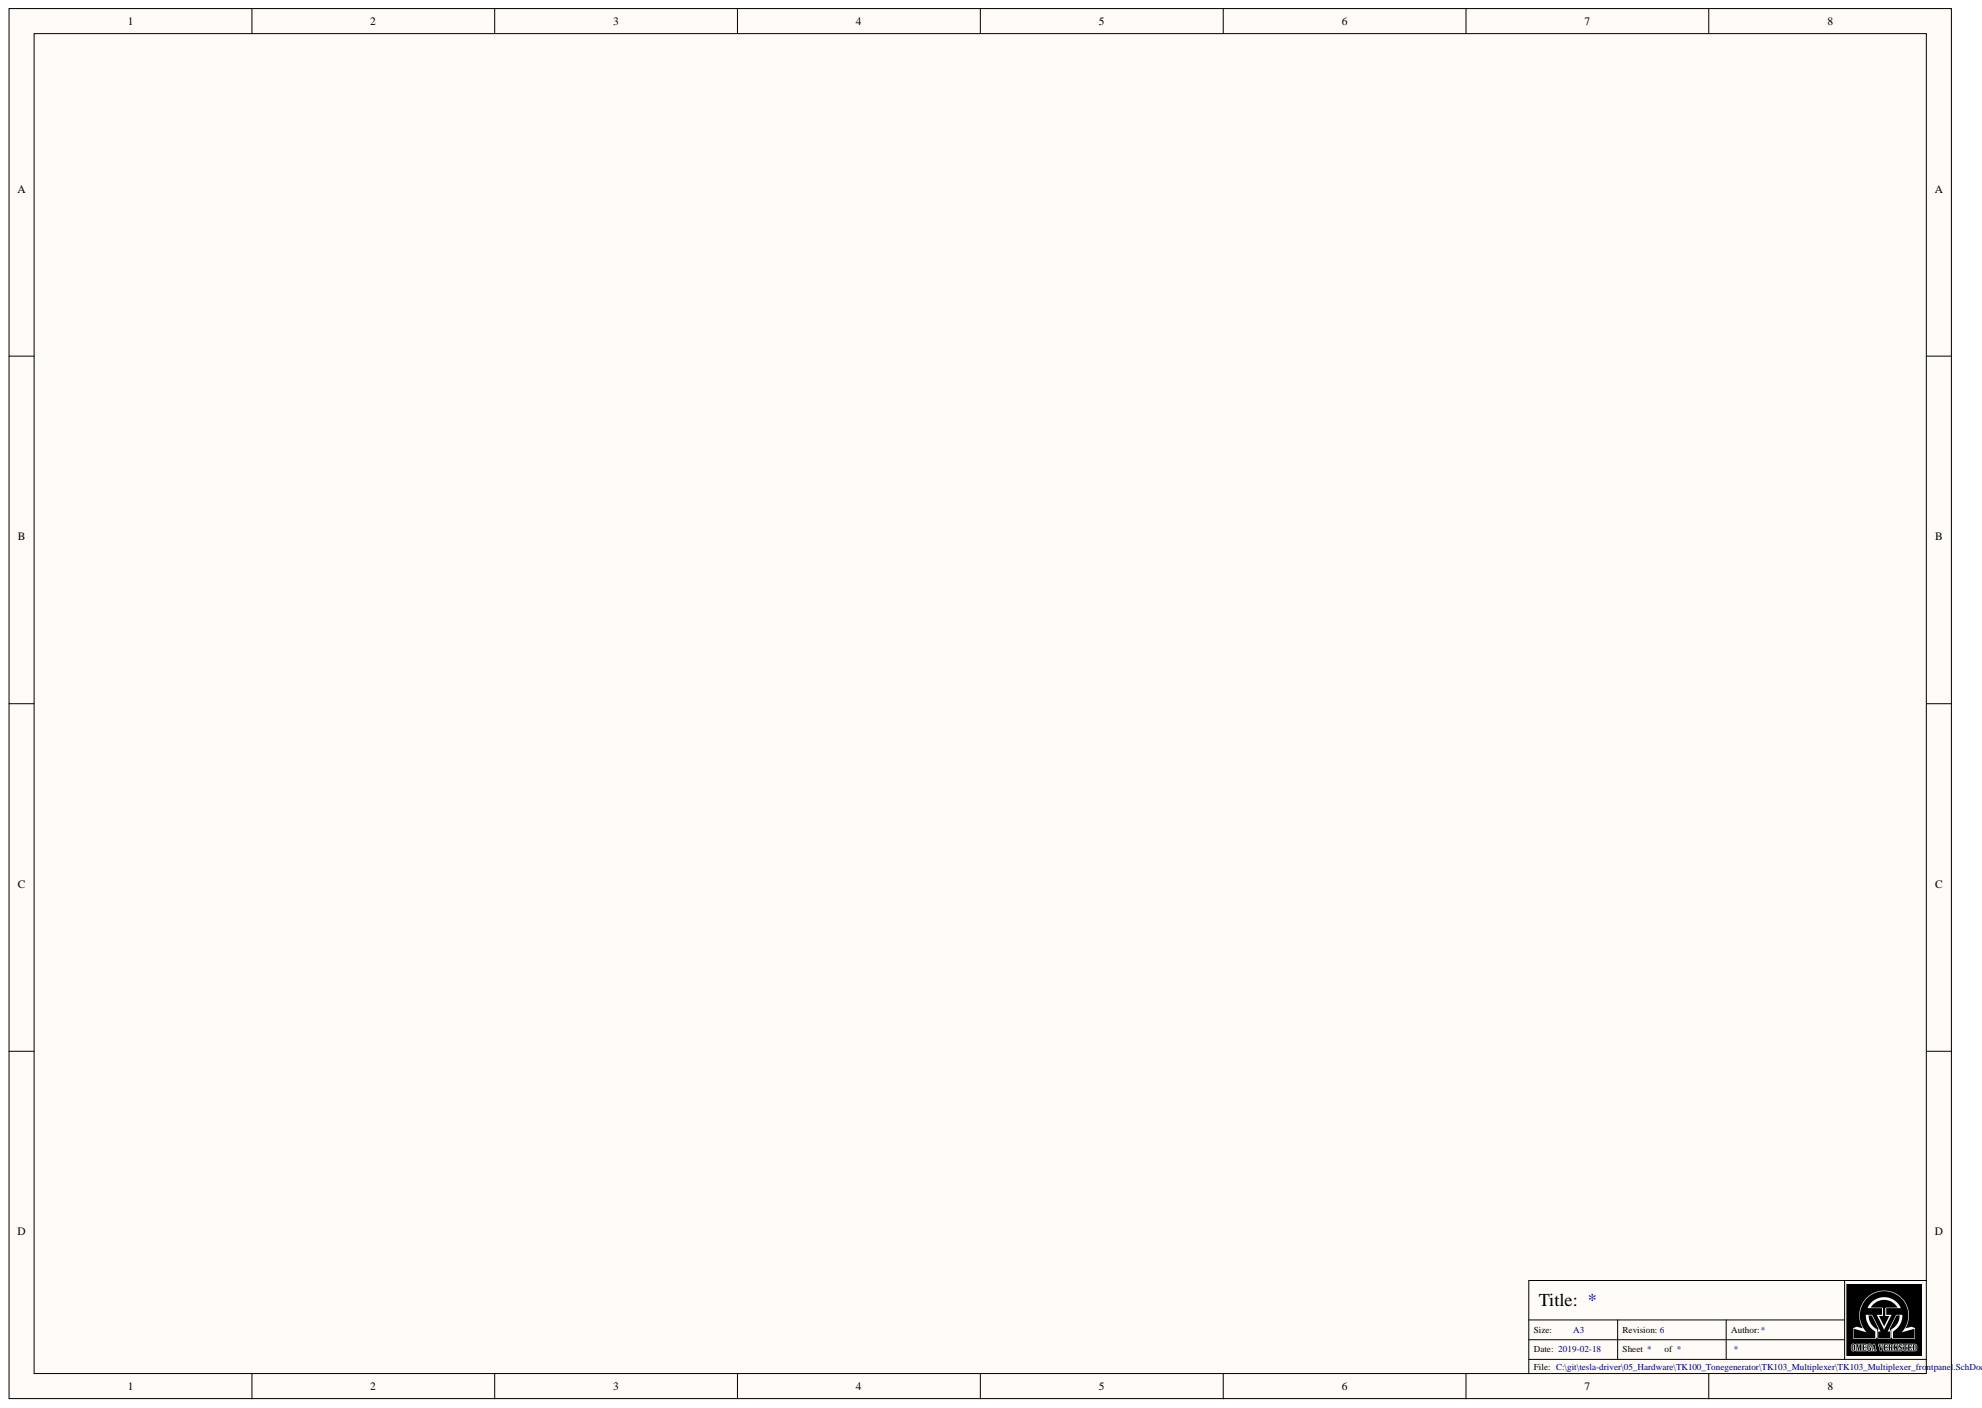
[picture p147: page 1]

Title: *

Size: A3 | Revision: 6 | Author: *

Date: 2019-02-18 | Sheet * of * | *

C:\git\tesla-driver\05_Hardware\TK100_Tonegenerator\TK103_Multiplexer\TK103_Multiplexer_frontpanel.SchDoc

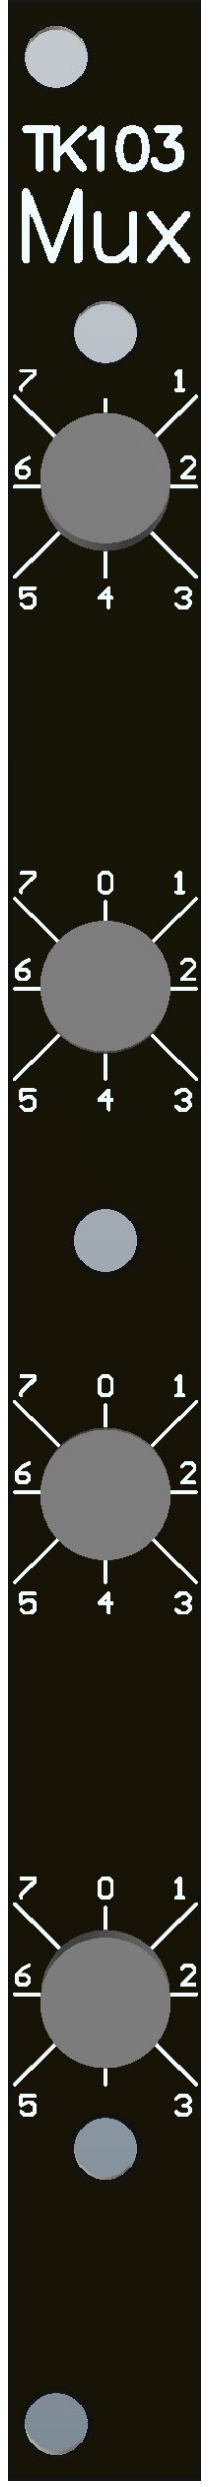
[picture p148: figure]

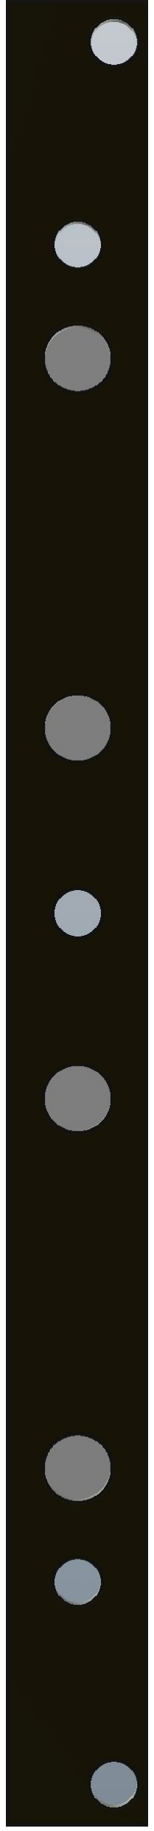
[picture p149: figure]
