Cable89/tesla-driver/05_Hardware/TK100_Tonegenerator/TK104_Pulsbegrenser_Eurorack/Project Outputs/TK104_Pulsbegrenser_Eurorack_faderboard.PDF

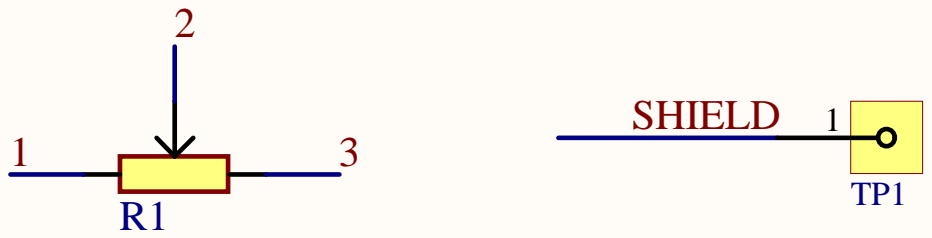
[picture p157: page 1]

Title: *

Size: A3 | Revision: 6 | Author : *

Date: | Sheet * of * | *

2019-02-17 C:\git\tesla-driver\05_Hardware\TK100_Tonegenerator\TK104_Pulsbegrenser_Eurorack\TK104_Pulsbegrenser_Eurorack_faderboard.SchDoc

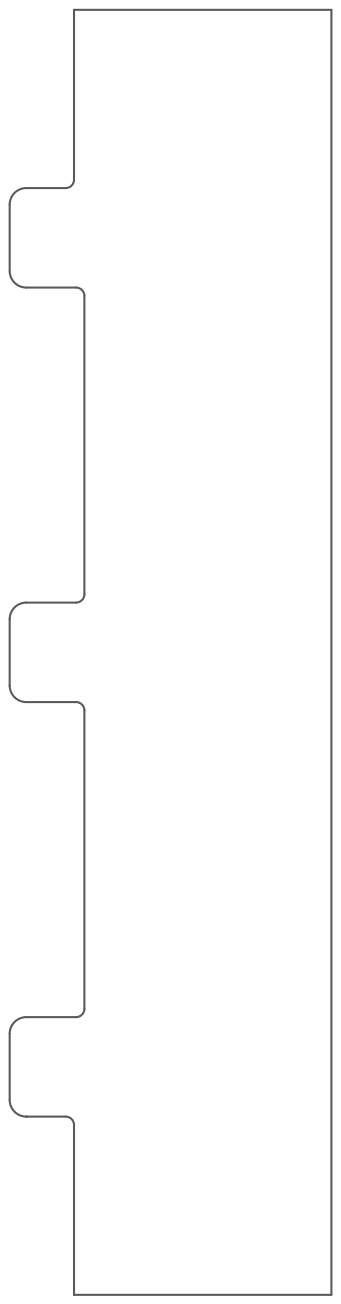
[picture p158: page 2]

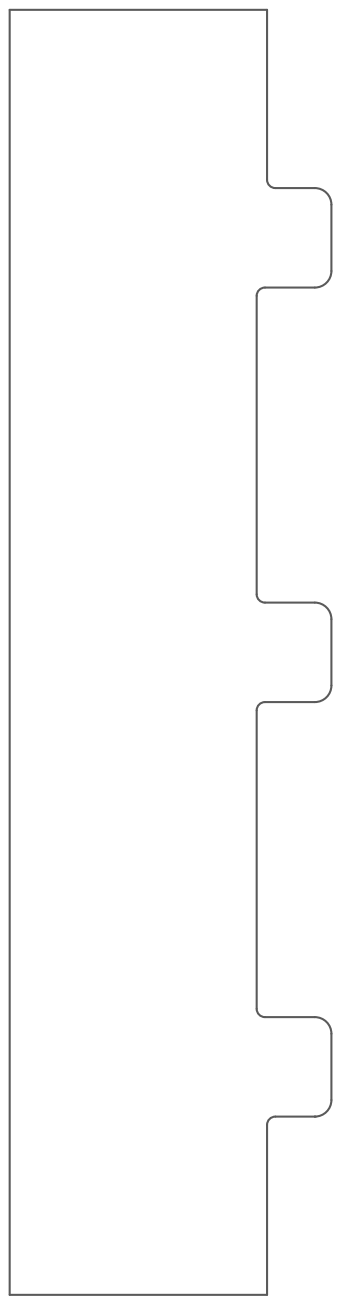
[picture p159: page 3]

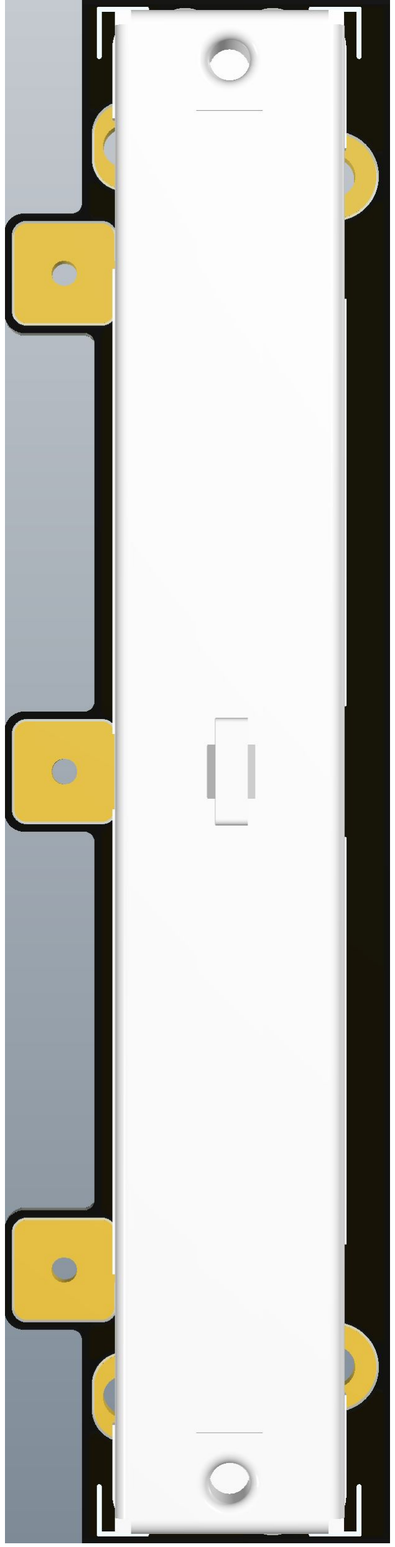
[picture p160: figure]

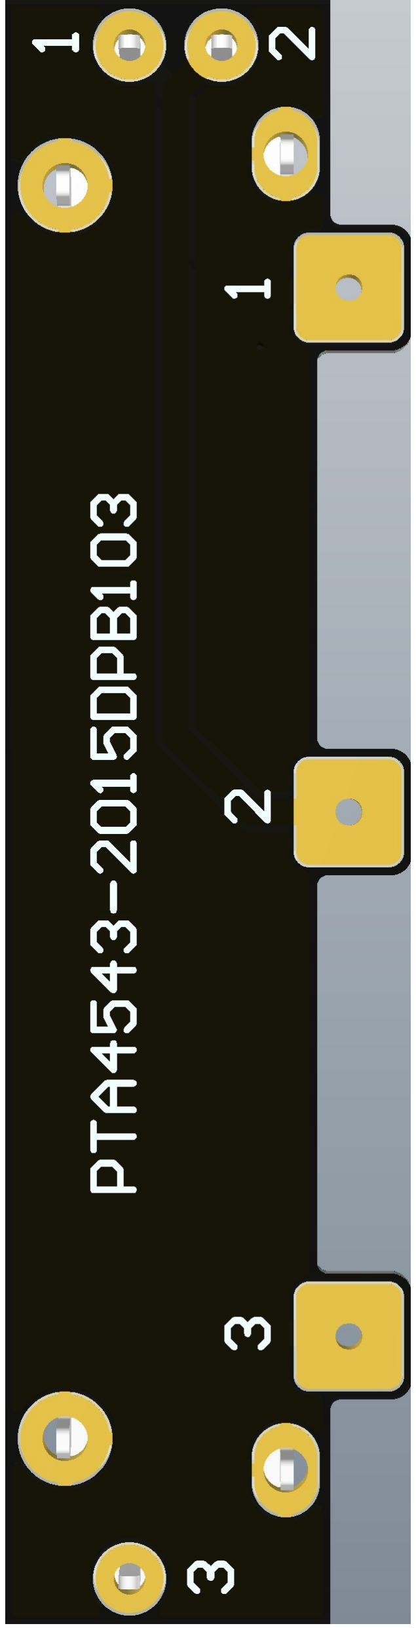
[picture p161: figure]
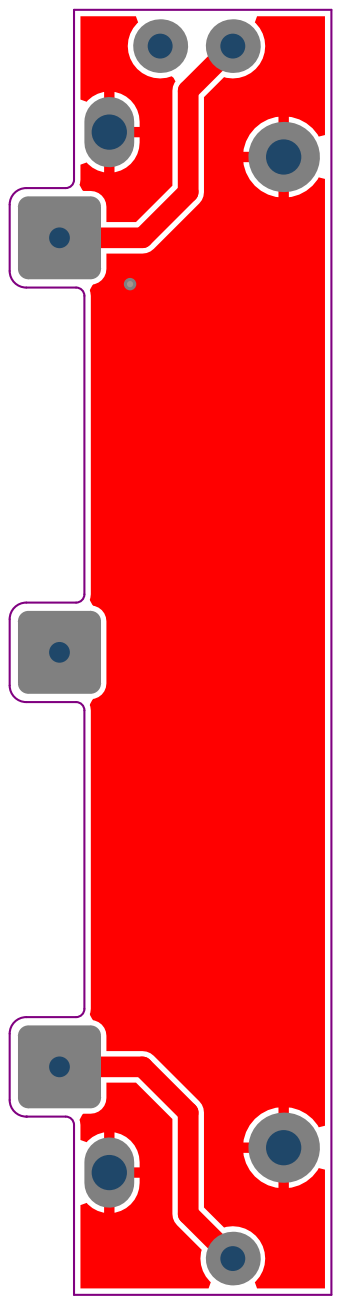
[picture p162: page 6]

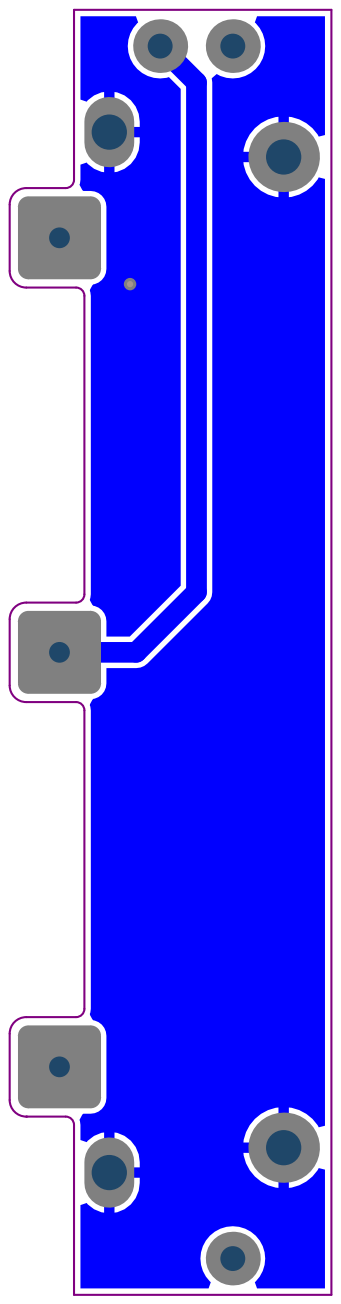
[picture p163: page 7]

Designator | Quantitynavn | | beskrivelse | leverandor | leverandor_varenr | antall
R1 | 1
TP1 | 1 | Header 1x1 | 2,54mm pitch
