Cable89/tesla-driver/05_Hardware/TK500_Driver/TK502_Frontpanel_LEDs/Project Outputs/TK502_Frontpanel_LEDs.PDF

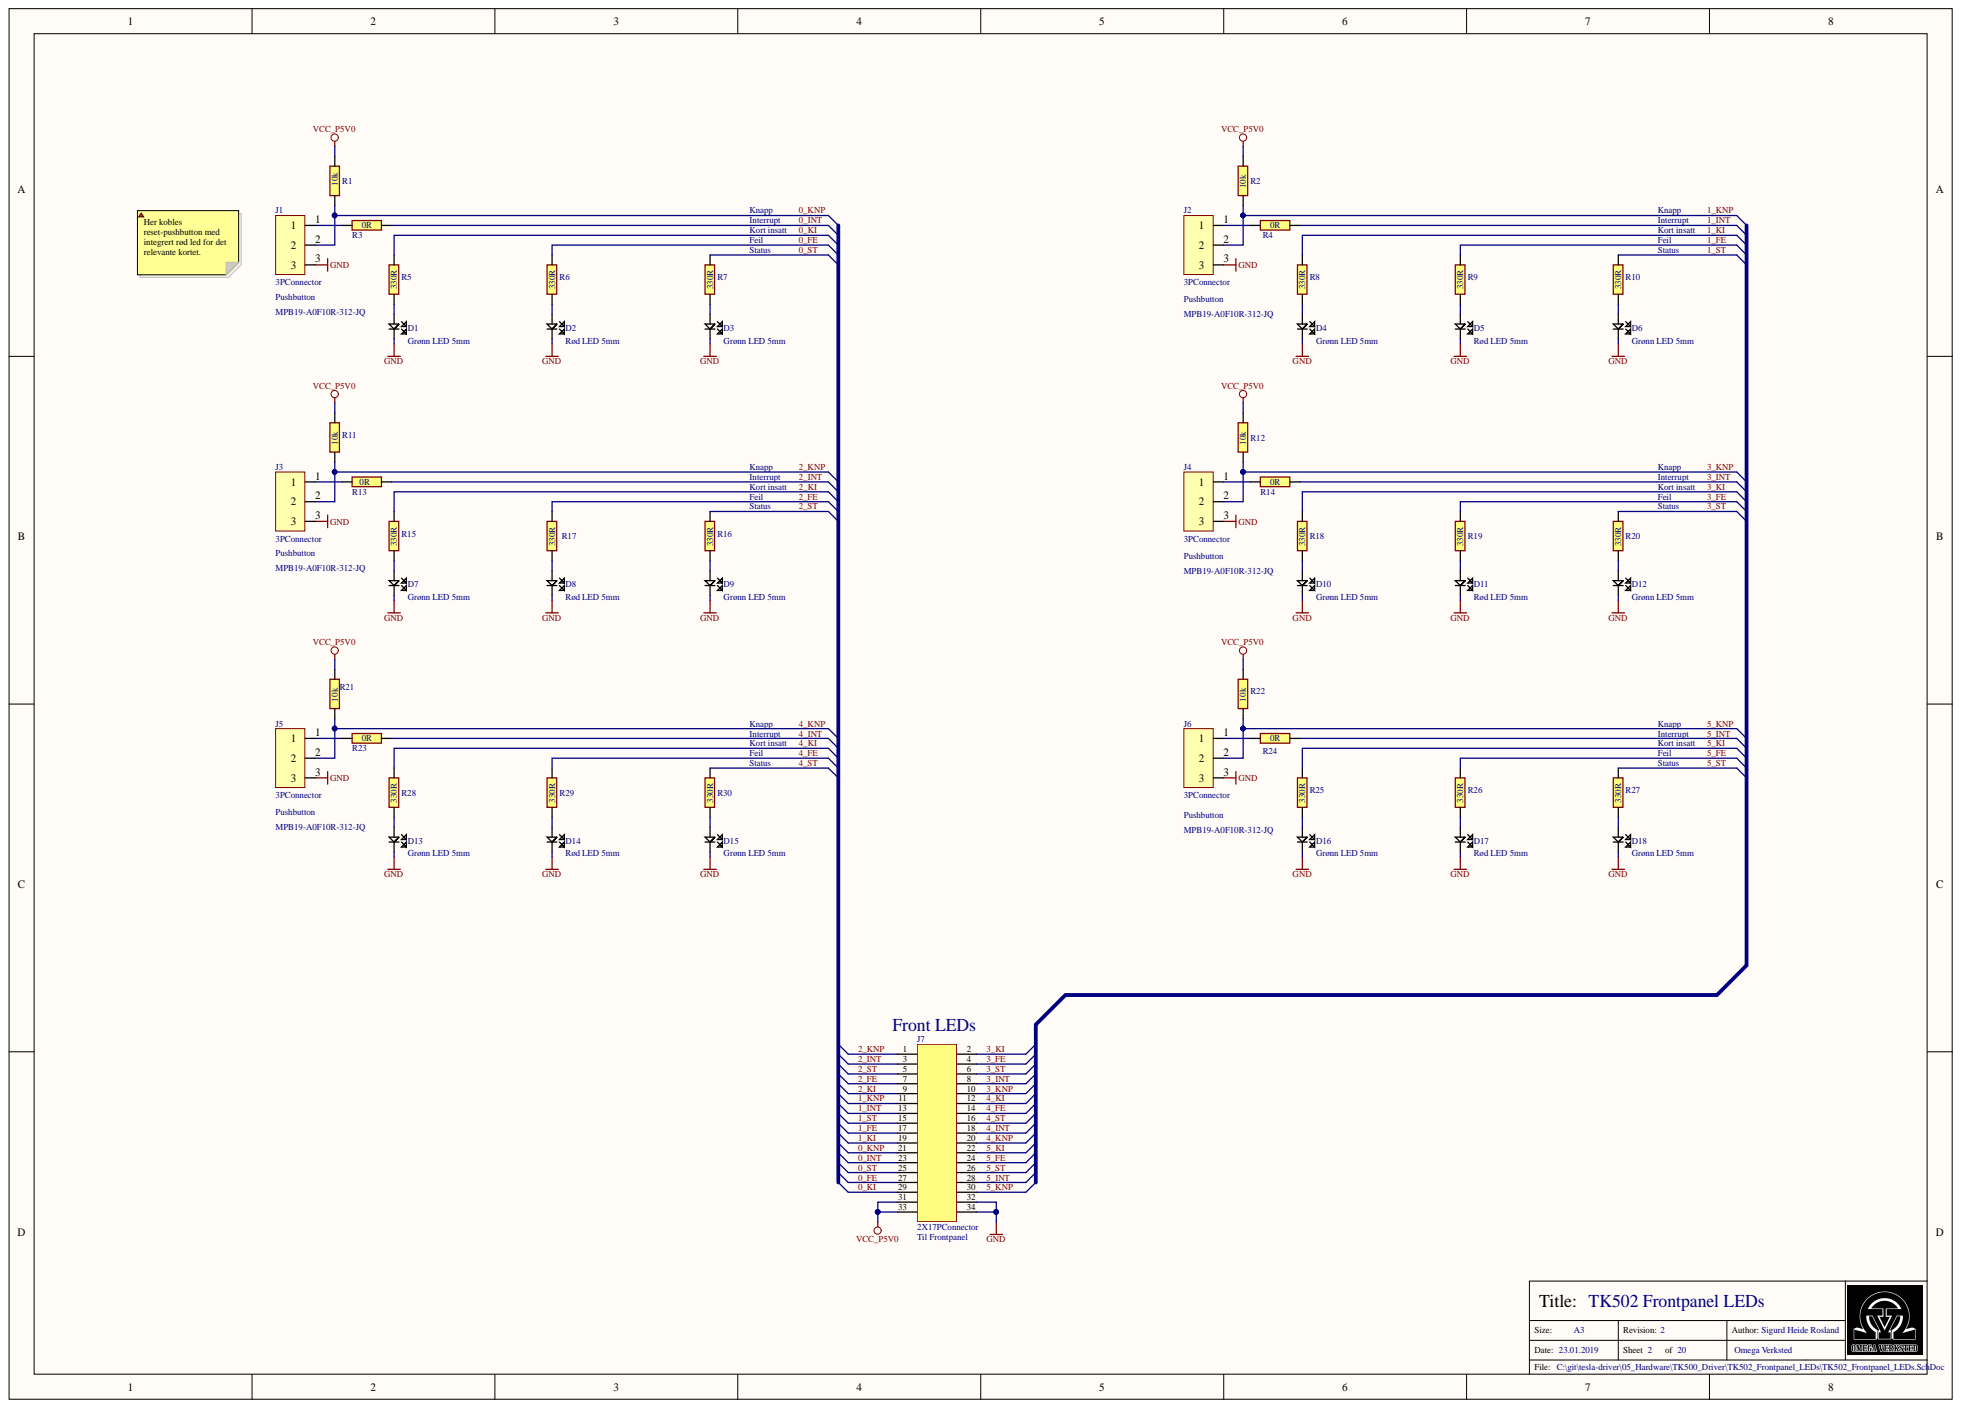
[picture p164: page 1]

Her kobles reset-pushbutton med

ød led for det

Title: TK502 Frontpanel LEDs

Size: A3 | Revision: 2 20 2 | Author : Sigurd Heide Rosland

Date: | Sheet of | Omega Verksted

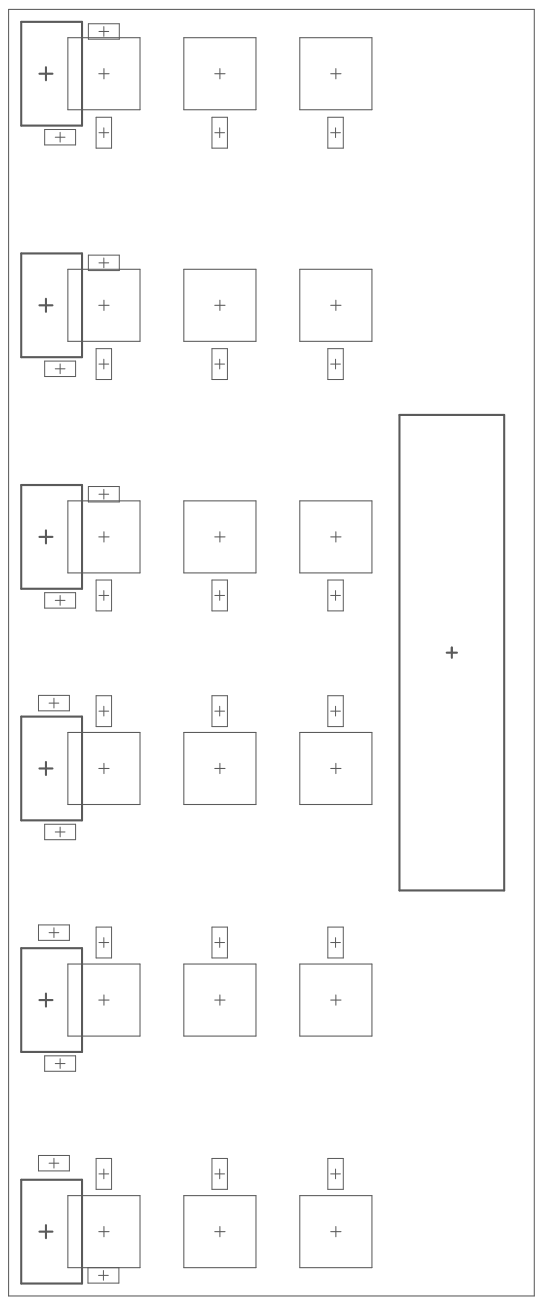
[picture p165: page 2]

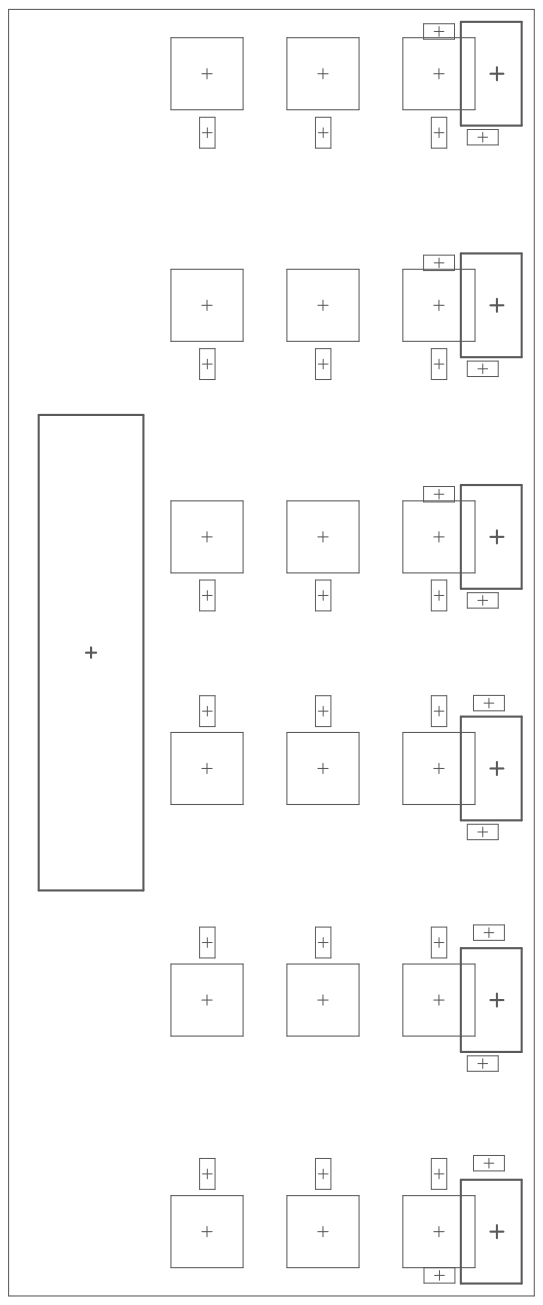
[picture p166: page 3]

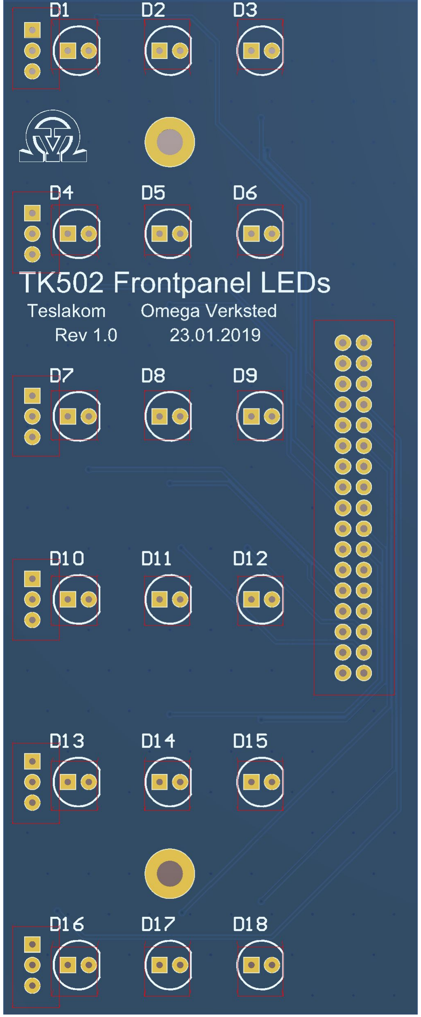
[picture p167: figure]

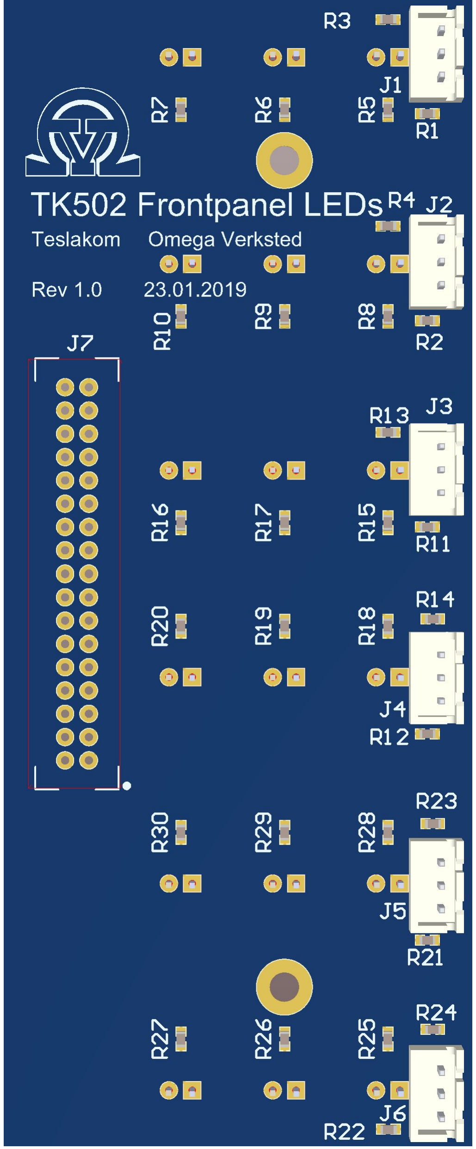
[picture p168: figure]
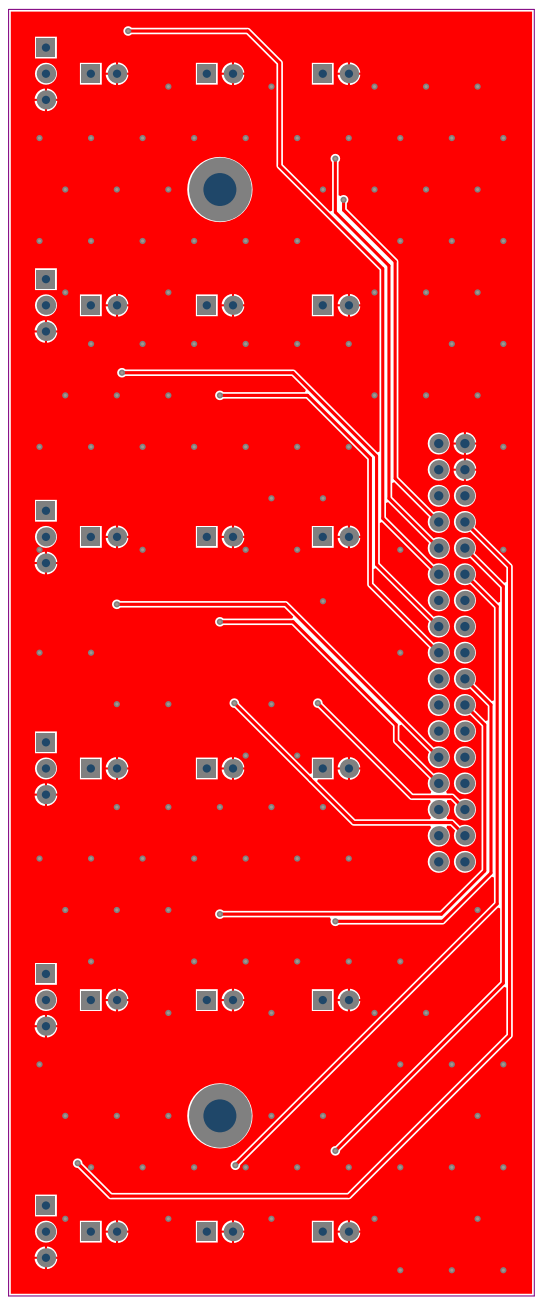
[picture p169: page 6]

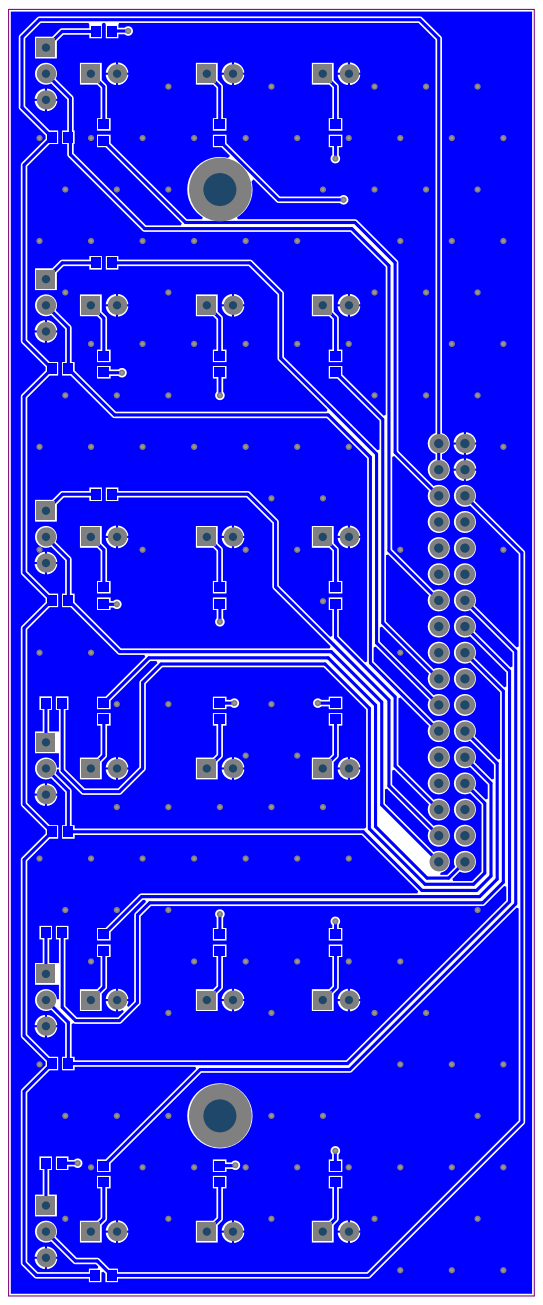
[picture p170: page 7]

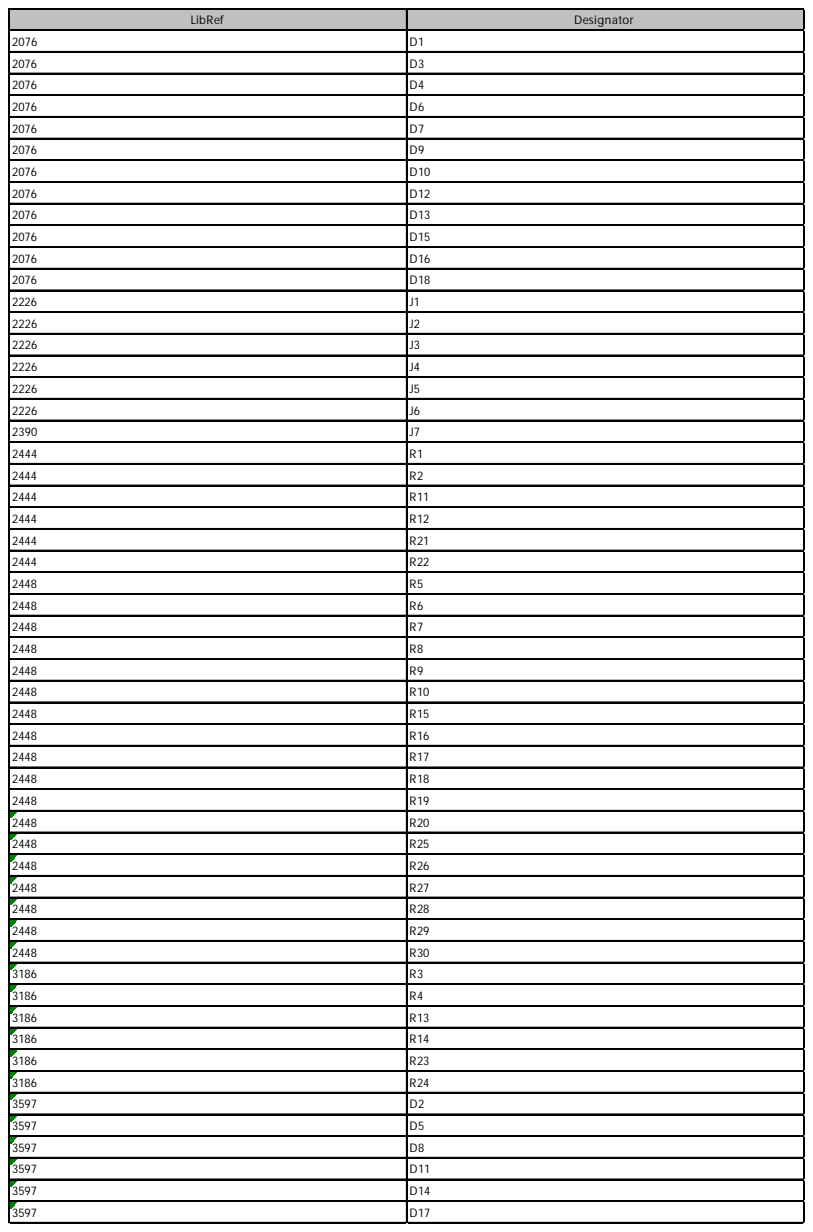
[picture p171: page 8]

LibRef | Designator
