Cable89/tesla-driver/05_Hardware/TK500_Driver/TK513_Limiter/Project Outputs/TK513_Limiter.PDF

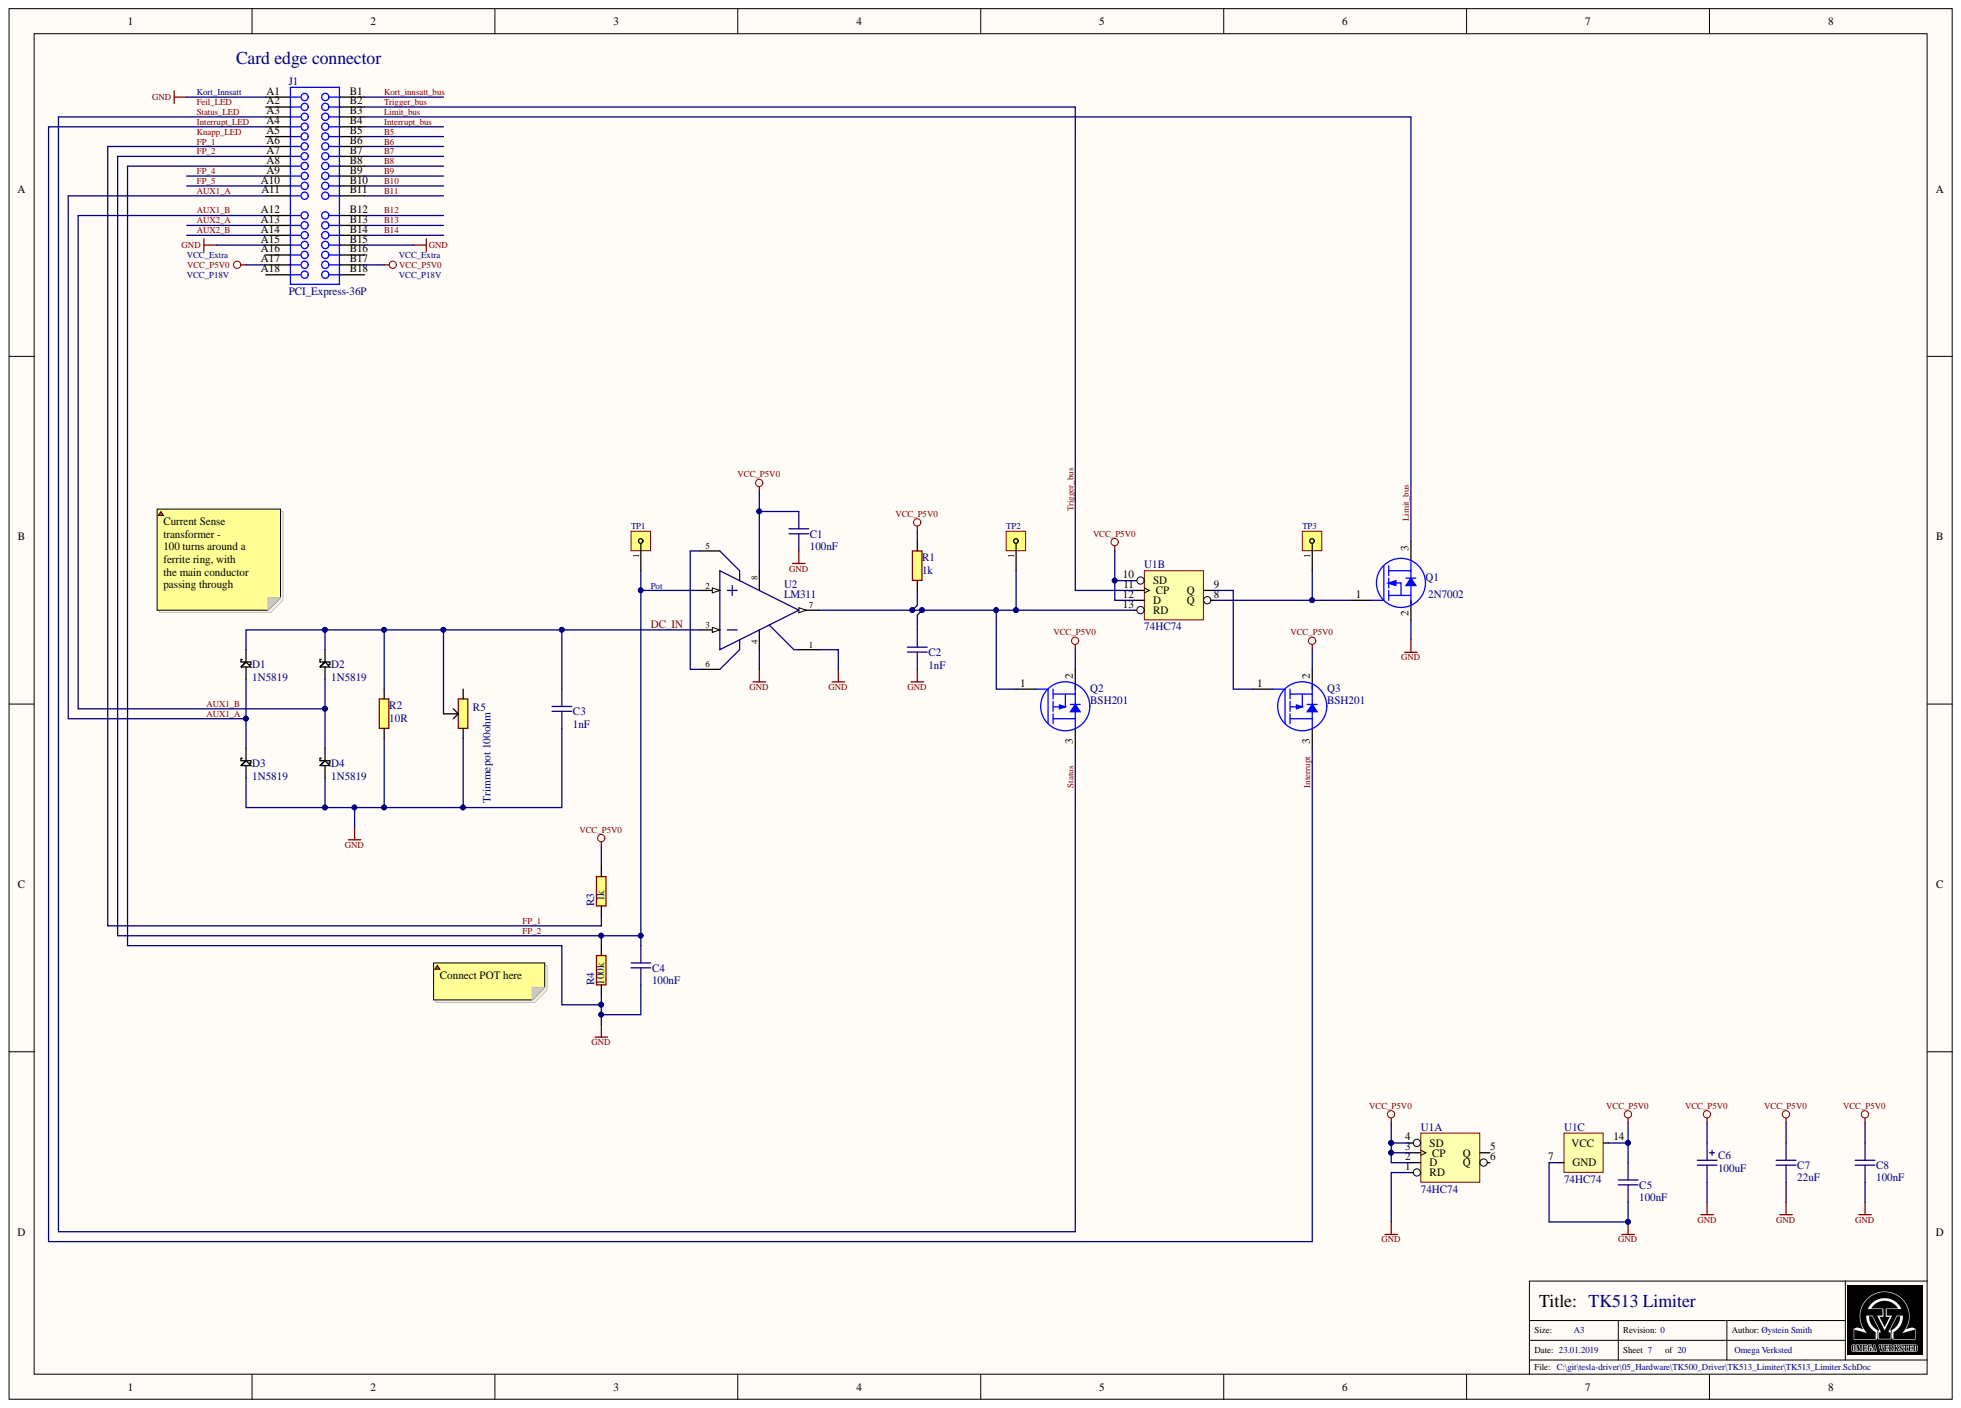
[picture p179: page 1]

B3 | Trigger_bus Interrupt_bus Limit_bus

Inter rupt_L E D A4 | | B4
Knapp_L E D A5 A6 FP_1 | | B5 | VC C_P5V0
FP_2 A7 | B7

B13
B14
B15 | | a
B16 | C_Extr C_P5V0 C_P18V
B17
B18

Title: TK513 Limiter

Size: A3 | Revision: 7 20 0 | Author : Øystein Smith

Date: 23.01.2019 C:\git\tesla-driver\05_Hardware\TK500_Driver\TK513_Limiter\TK513_Limiter.SchDoc | Sheet of | Omega Verksted

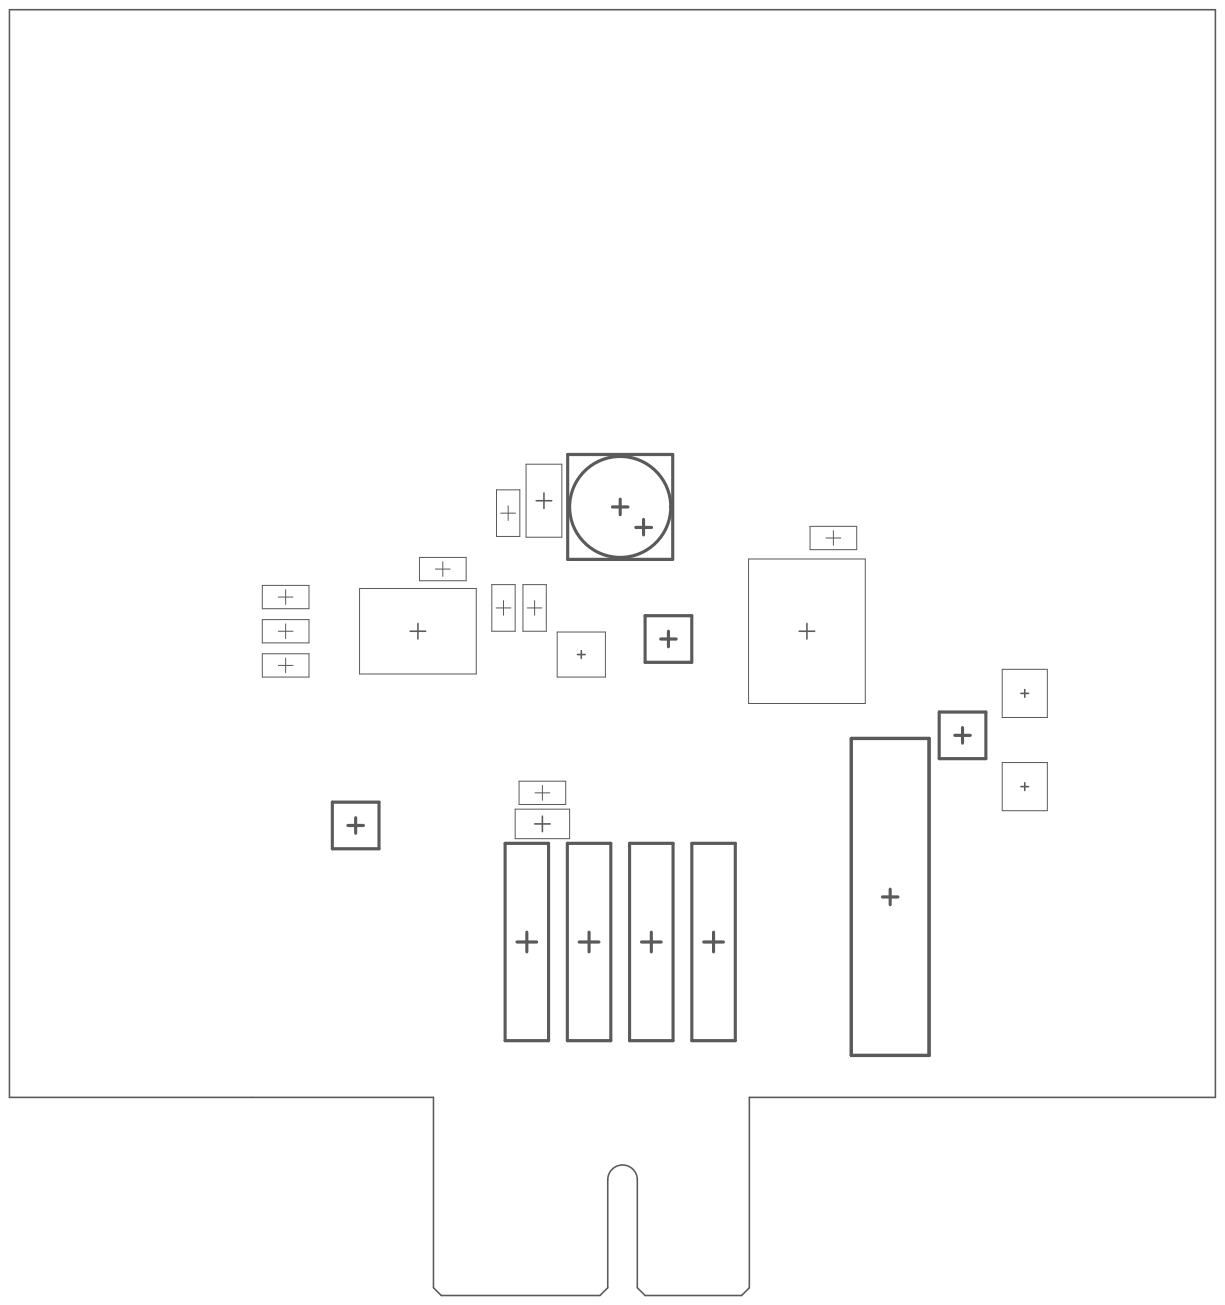
[picture p180: page 2]

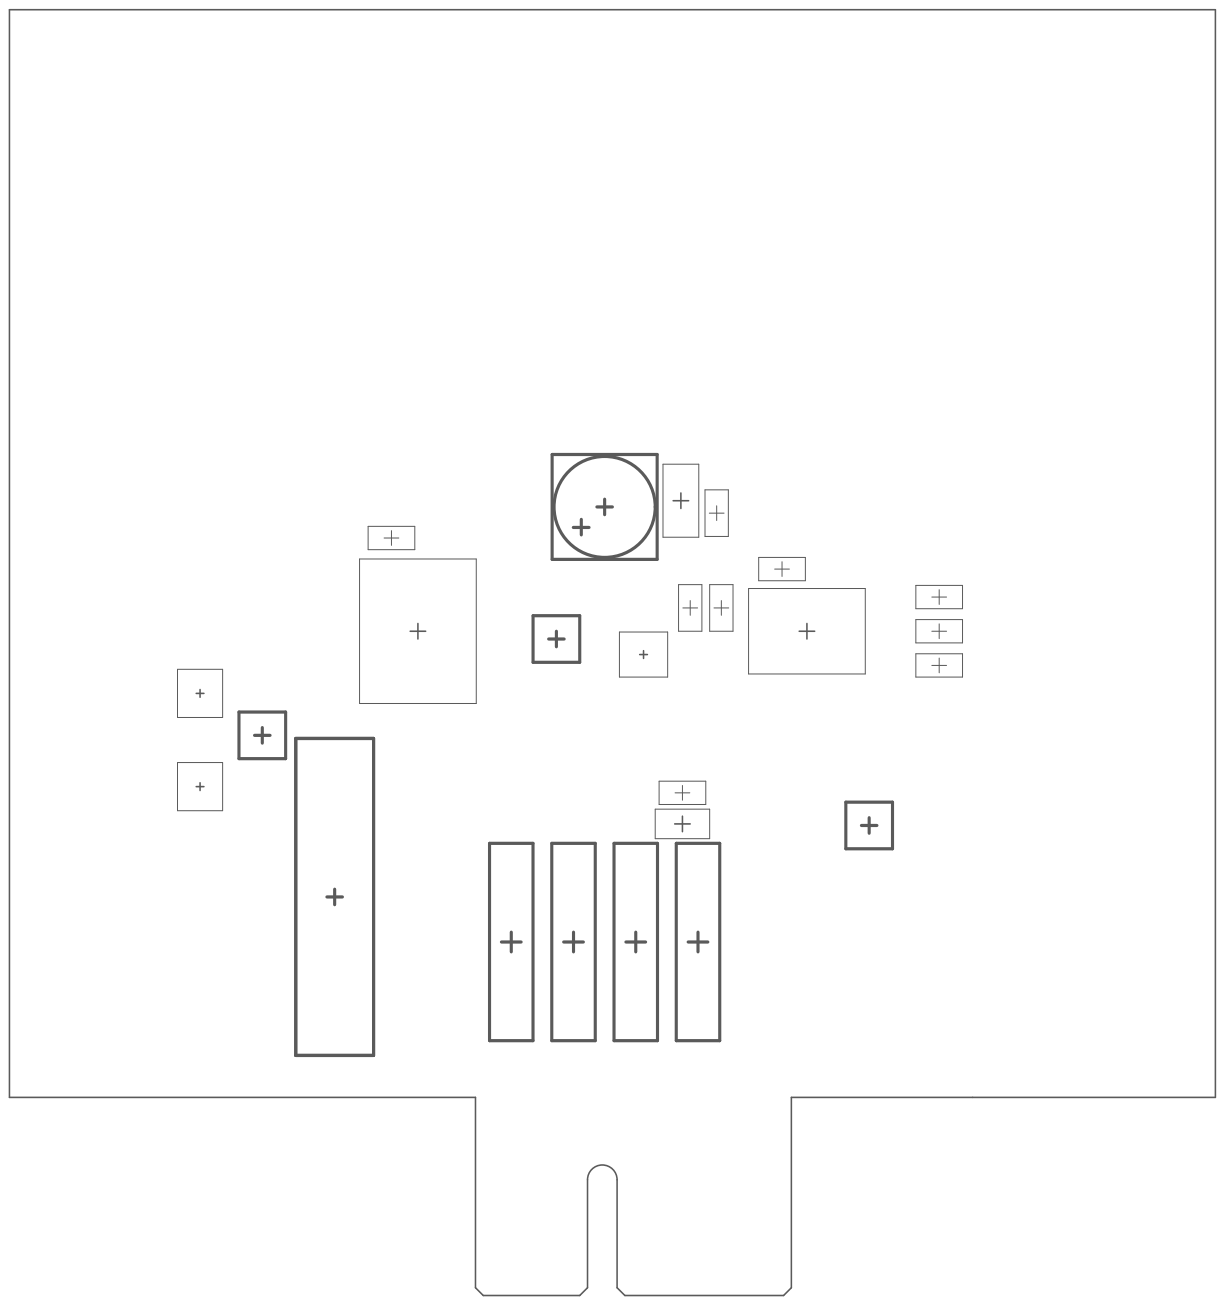
[picture p181: page 3]

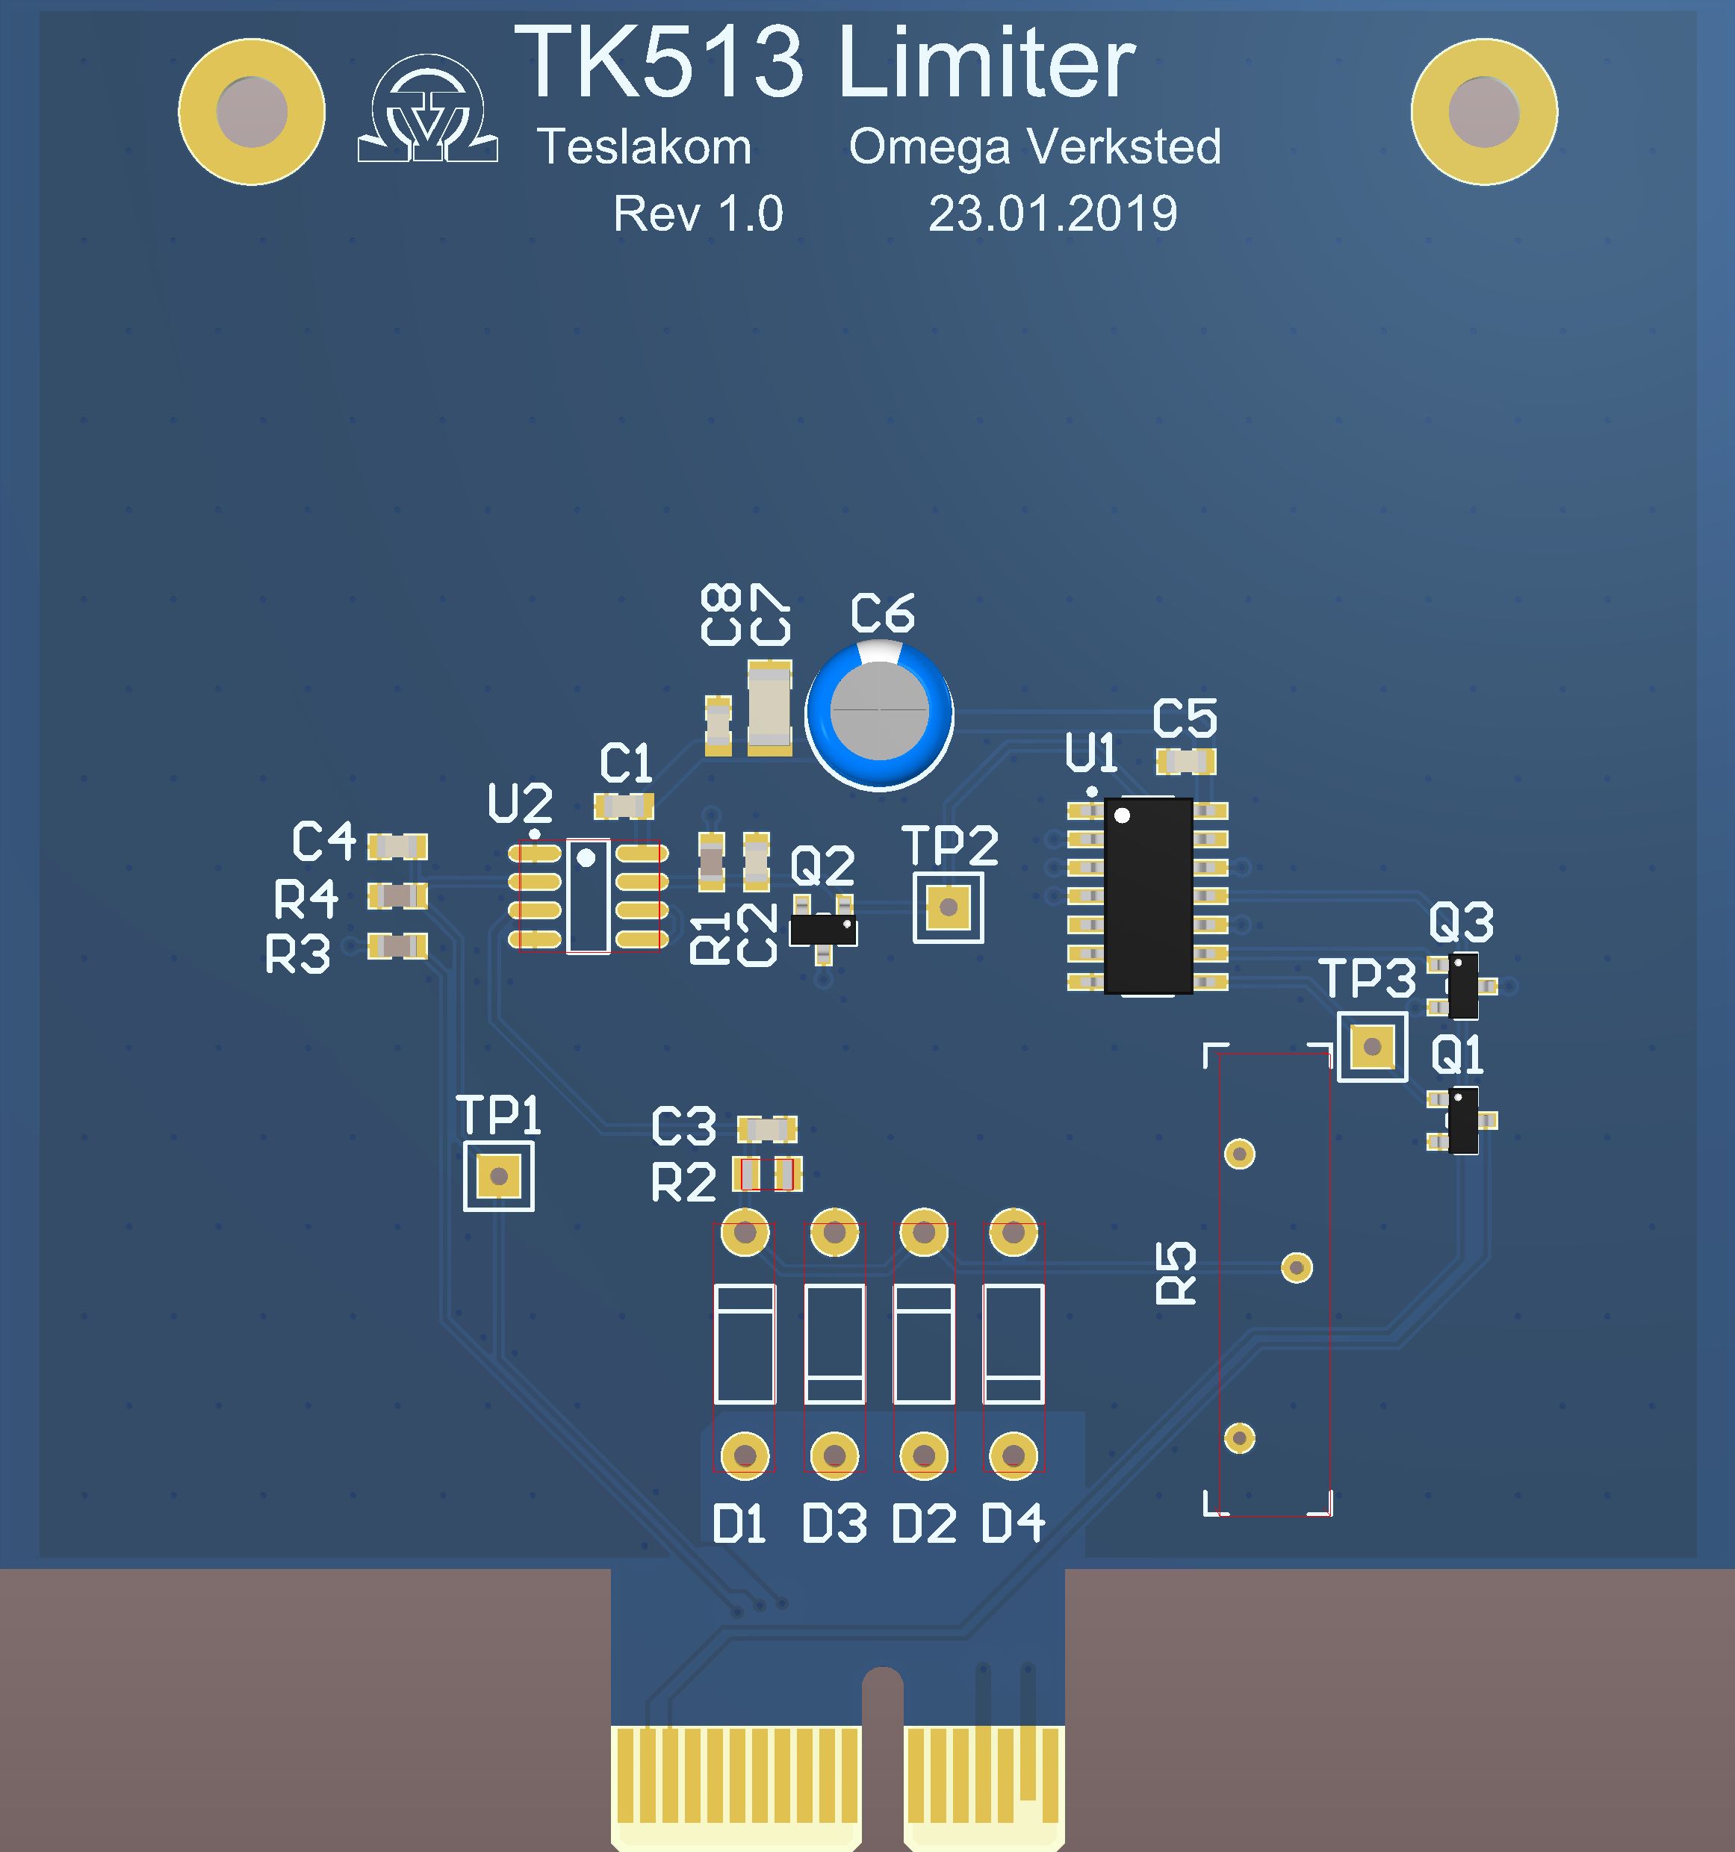
[picture p182: page 4]

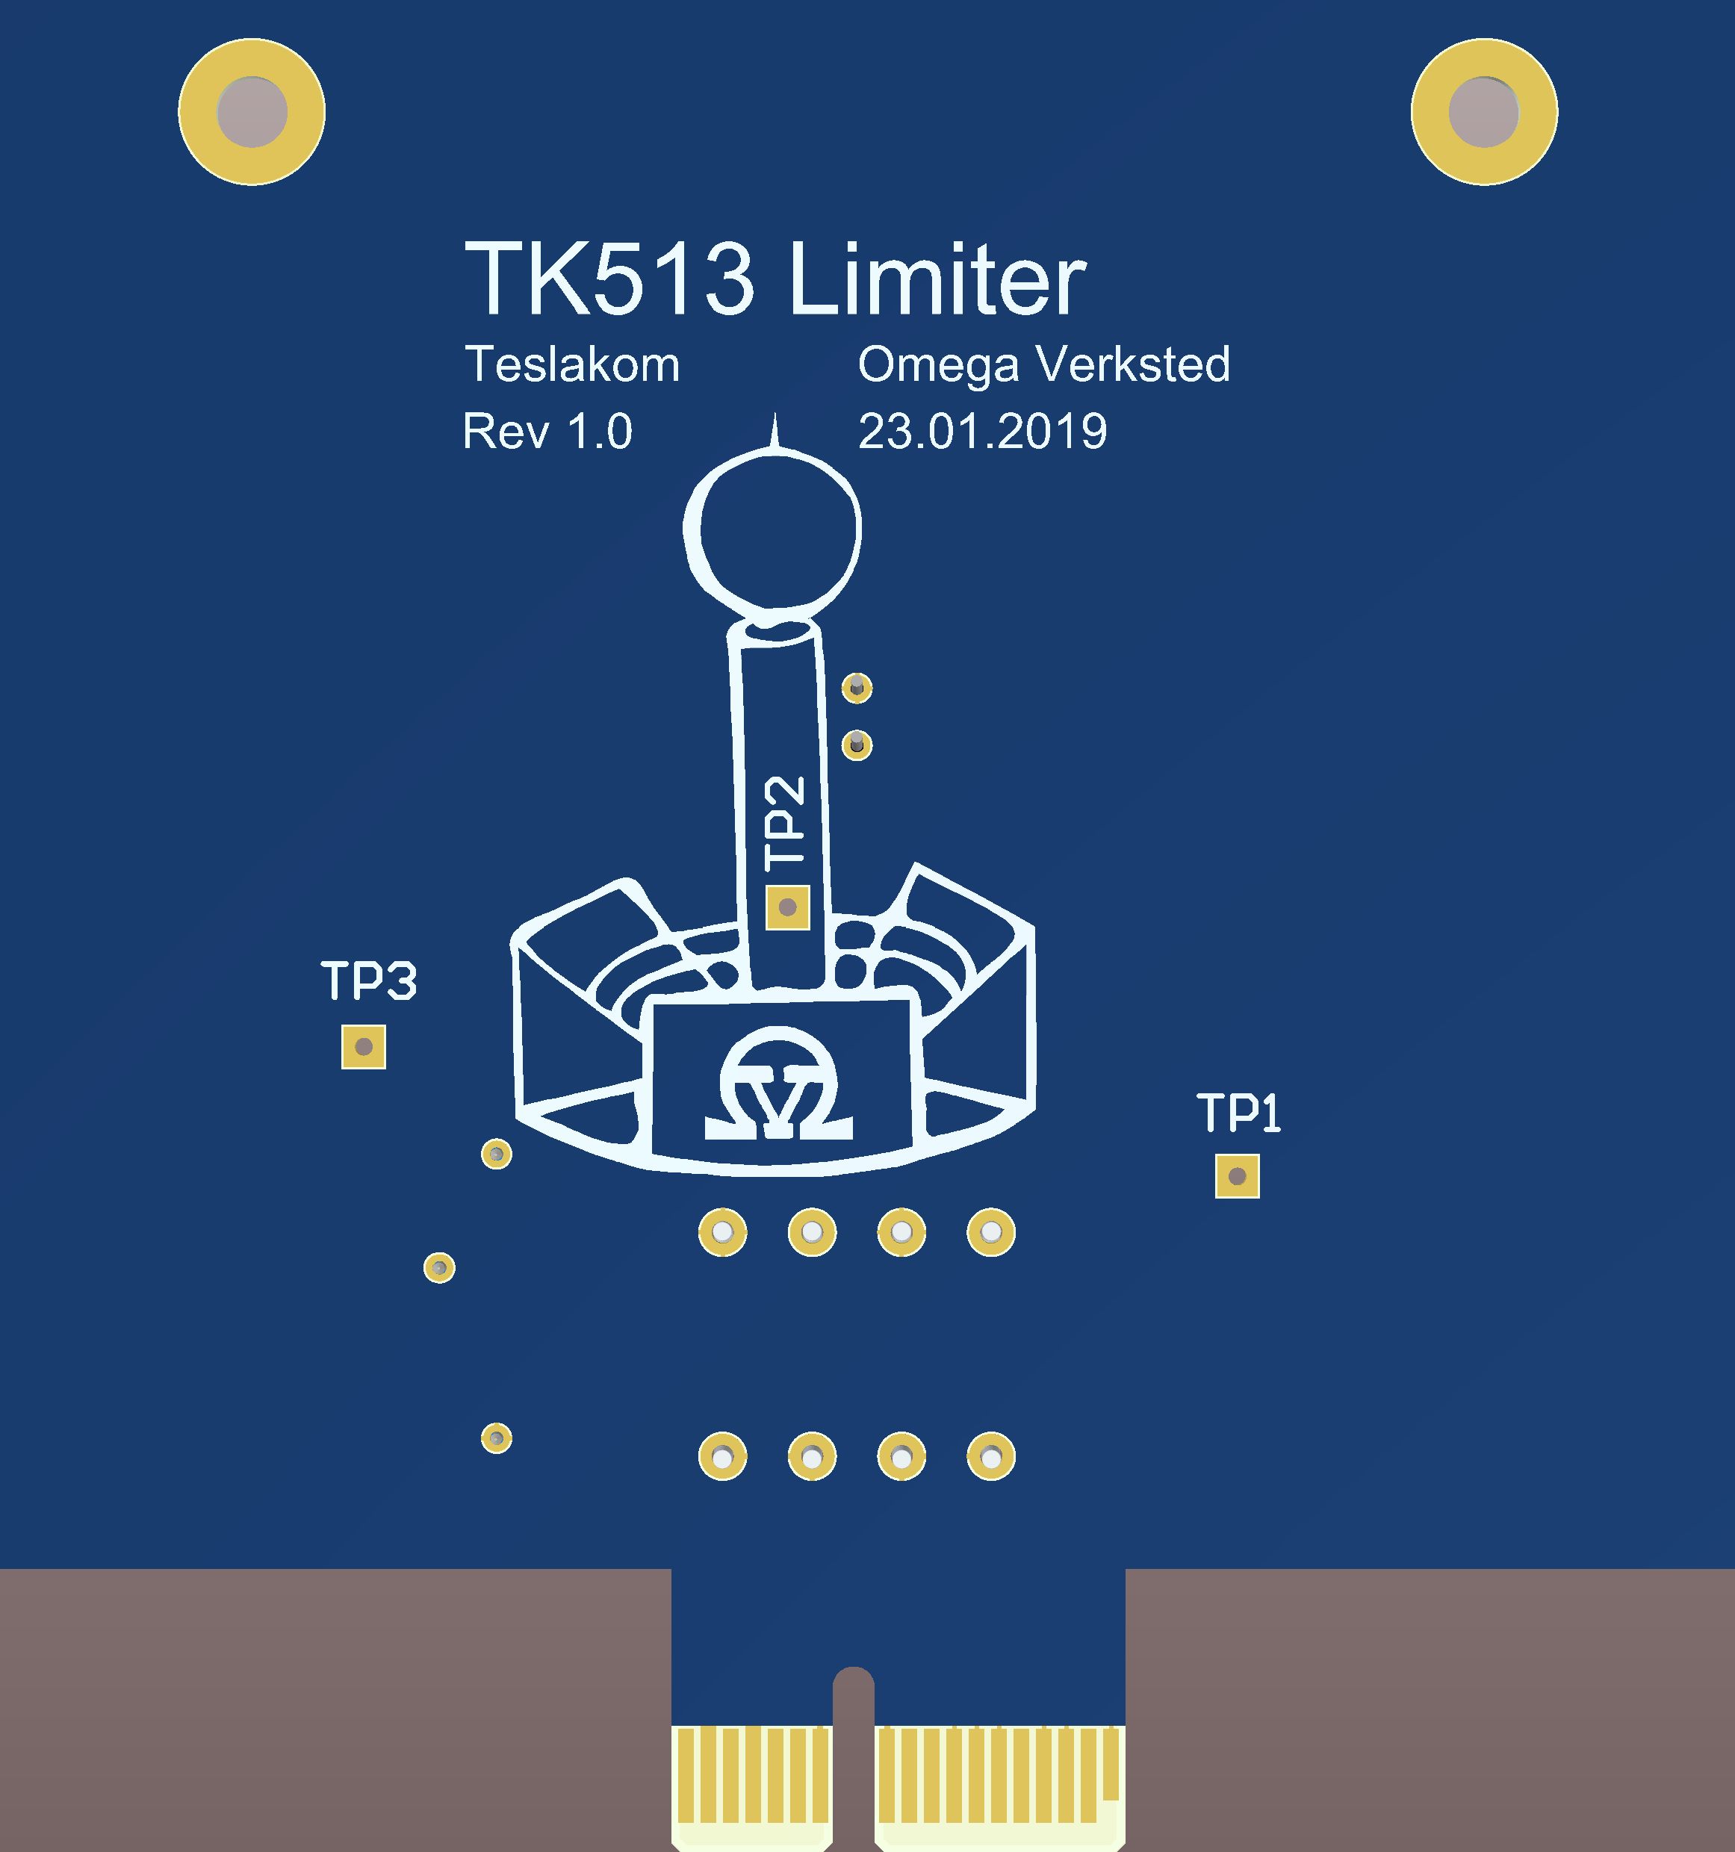
[picture p183: page 5]

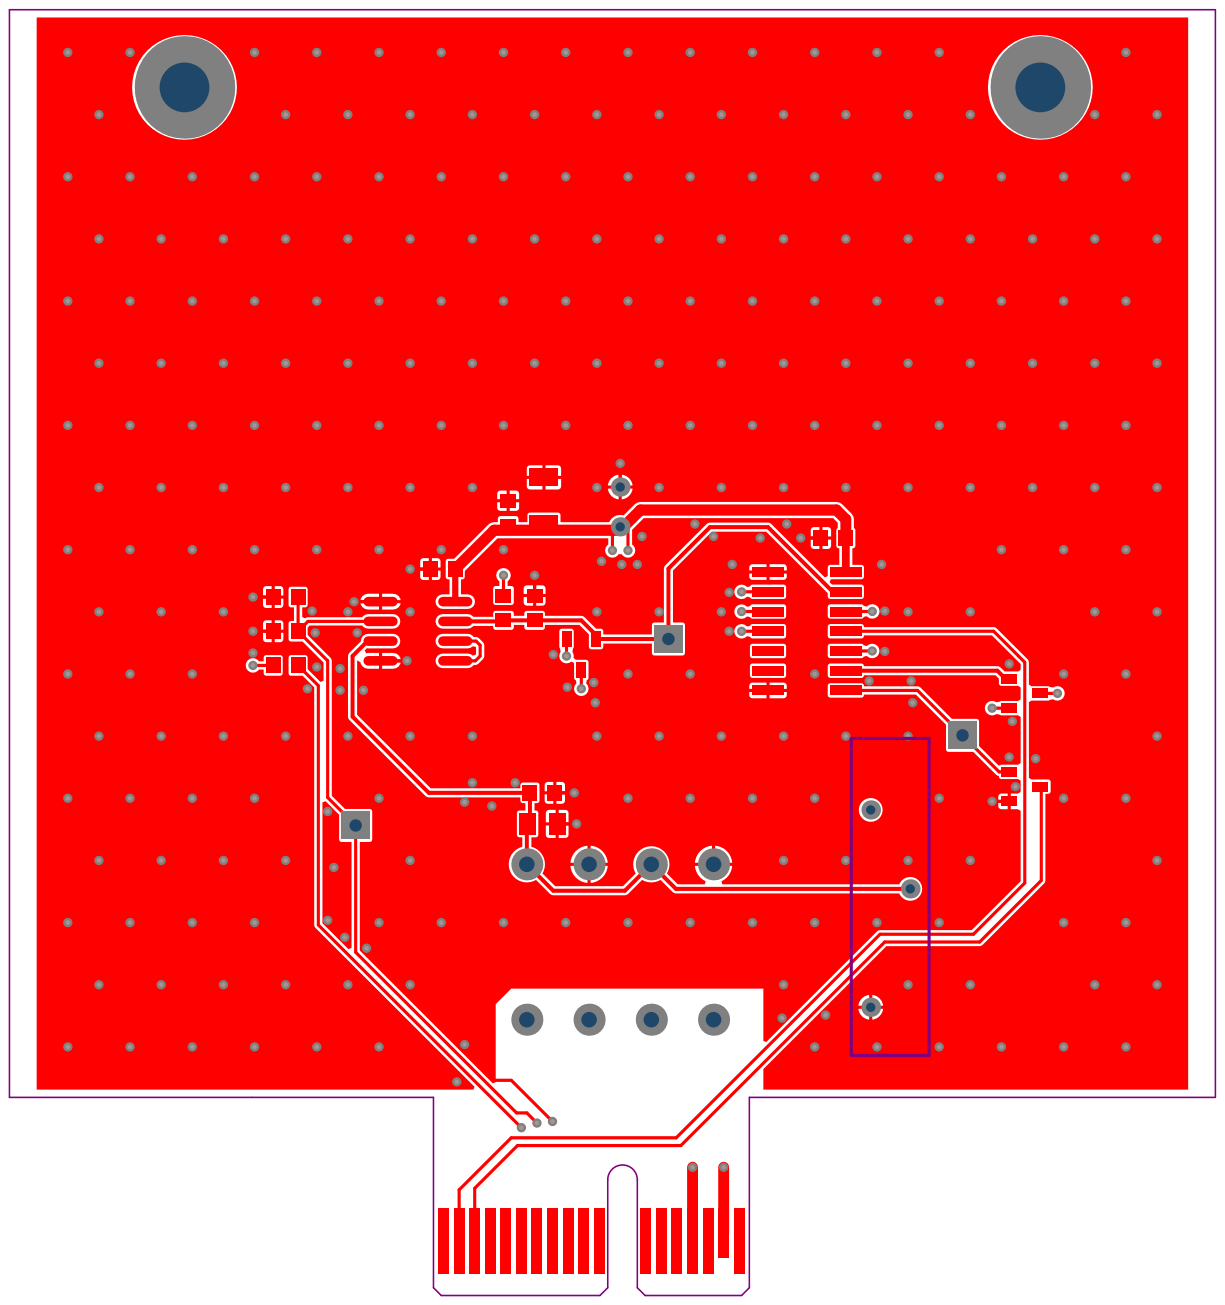
[picture p184: page 6]

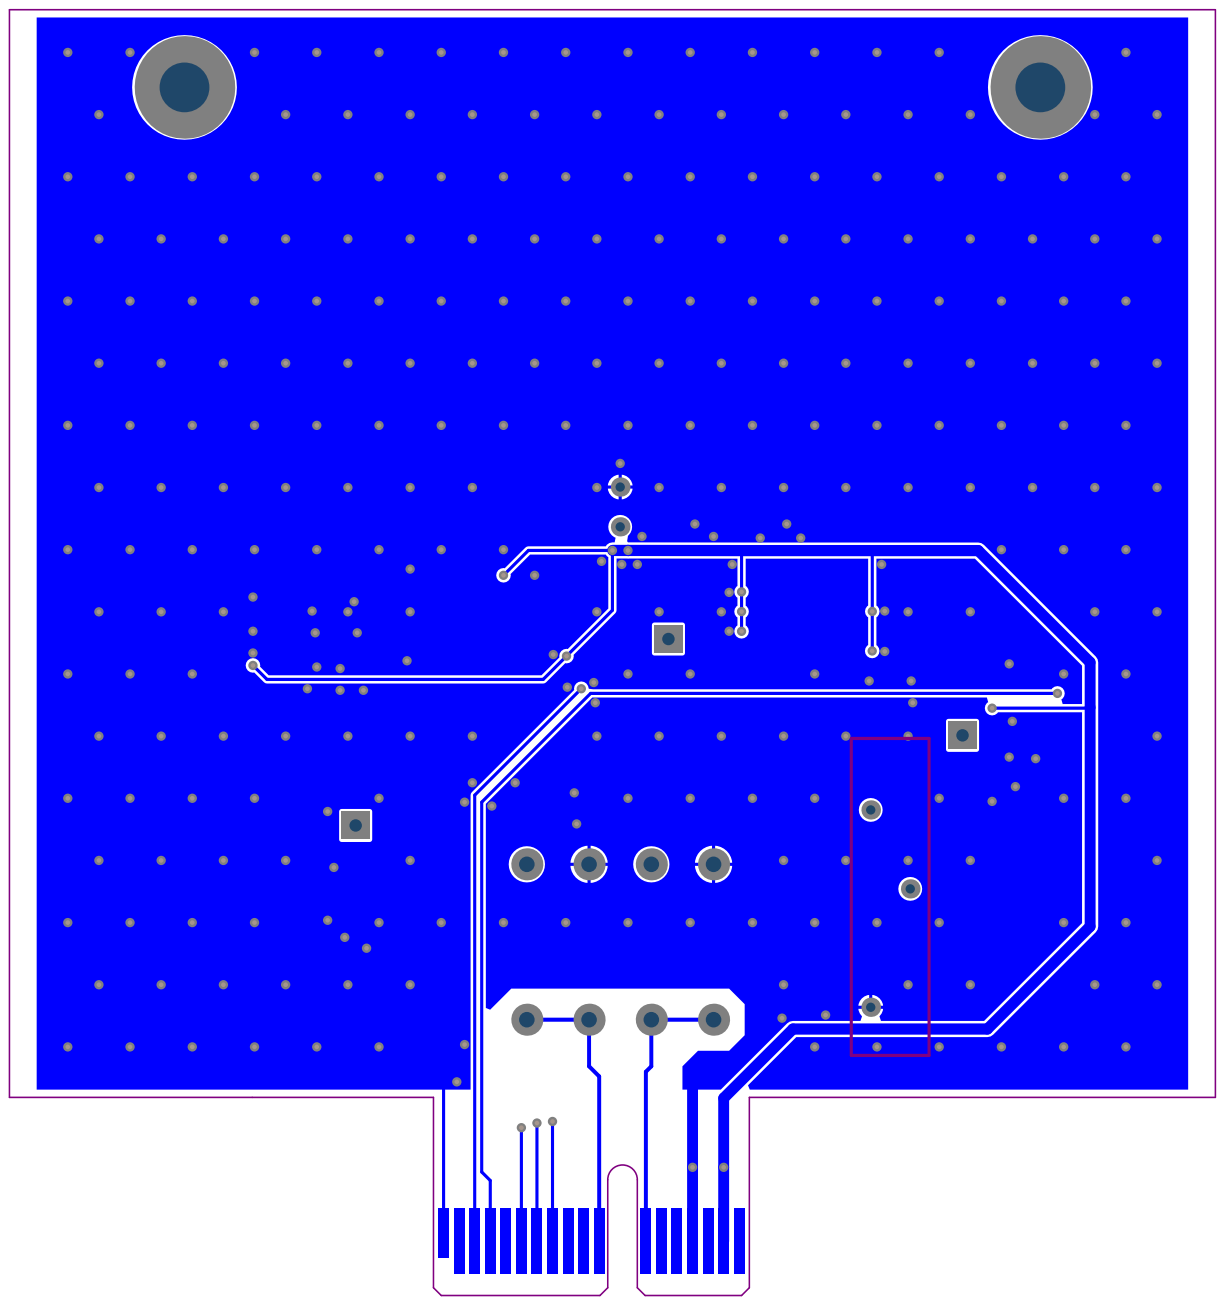
[picture p185: page 7]

Designator | navn | beskrivelse | hyll e | rad | kol on ne | dyb de | pris
C1, C4, C5, C8 | 100nF | | | | | | 1
C2, C3 | 1nF | | | | | | 1
C6 | 100uF | | 3 | 9 | 3 | 0 | 2
C7 | 22uF | | | | | | 3
D1, D2, D3, D4 | 1N5819 | Schottkydiode, 1A, 40V | 6 | 0 | 2 | 0 | 2
J1 | PCIeX1-GF-2D-1000-1K-O36 | | | | | | 0
Q1 | 2N7002 | | 4 | 2 | 3 | 0 | 2
Q2, Q3 | BSH201 | | | | | | 3
R1, R3 | 1k | | 6 | -1 | 0 | 48 | 0
R2 | 10R | | | | | | 0
R4 | 100k | | 6 | -1 | 0 | 96 | 0
R5 | Trimmepot 100ohm | | 7 | 1 | 1 | 0 | 15
TP1, TP2, TP3 | Header 1x1 | 2,54mm pitch | | | | | 1
U1 | 74HC74 | Dual D flip flop | | | | | 4
U2 | LM311 | | | | | | 2
