Cable89/tesla-driver/05_Hardware/TK500_Driver/TK521_Optisk-plugg/Project Outputs/TK521_Optisk-plugg.PDF

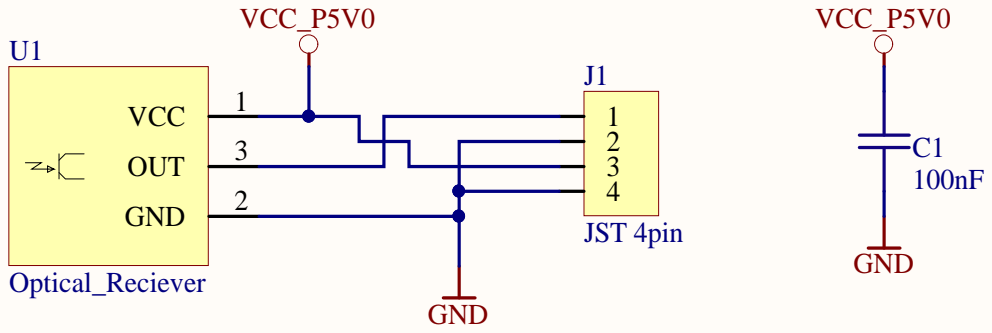
[picture p193: page 1]

Title: TK520 GDT-Trafo

Size: A3 | Revision: 13 20 1 | Author : Øystein Smith

Date: 23.01.2019 C:\git\tesla-driver\05_Hardware\TK500_Driver\TK521_Optisk-plugg\TK521_Optisk-plugg.SchDoc | Sheet of | Omega Verksted

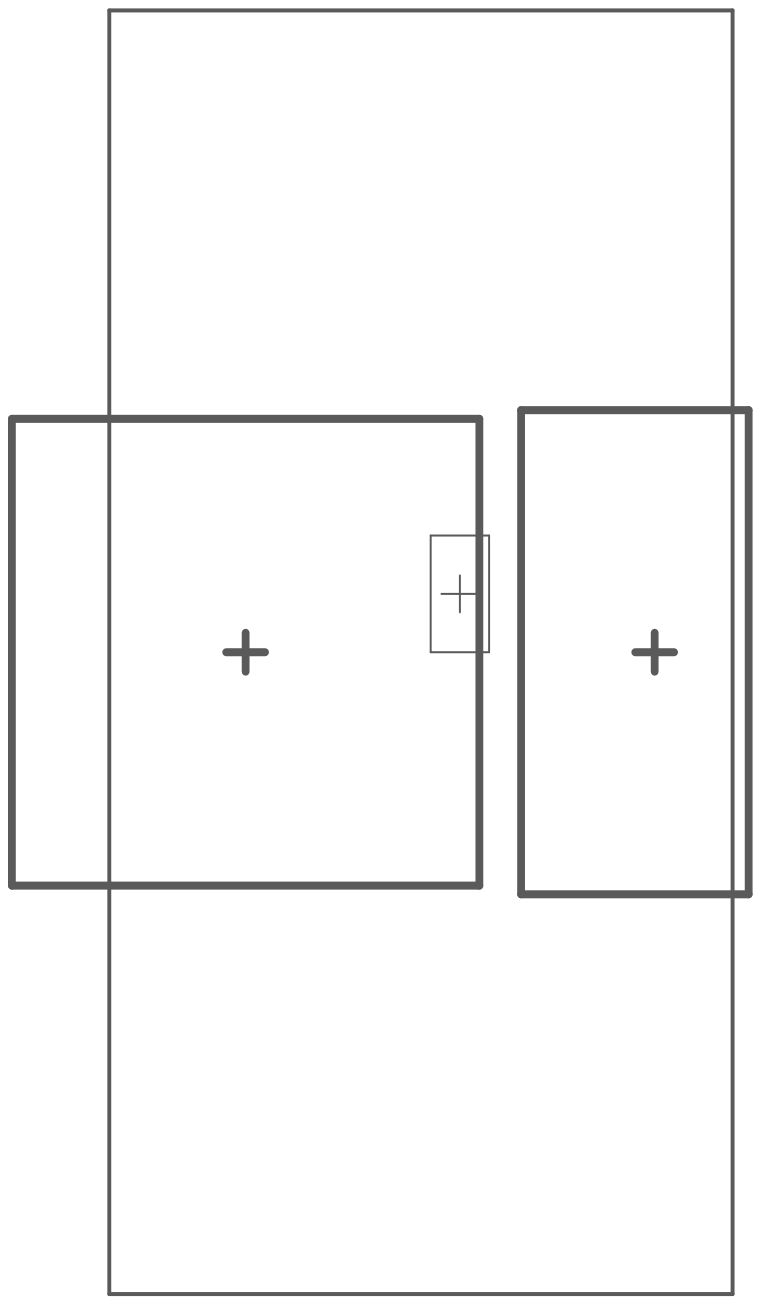
[picture p194: page 2]

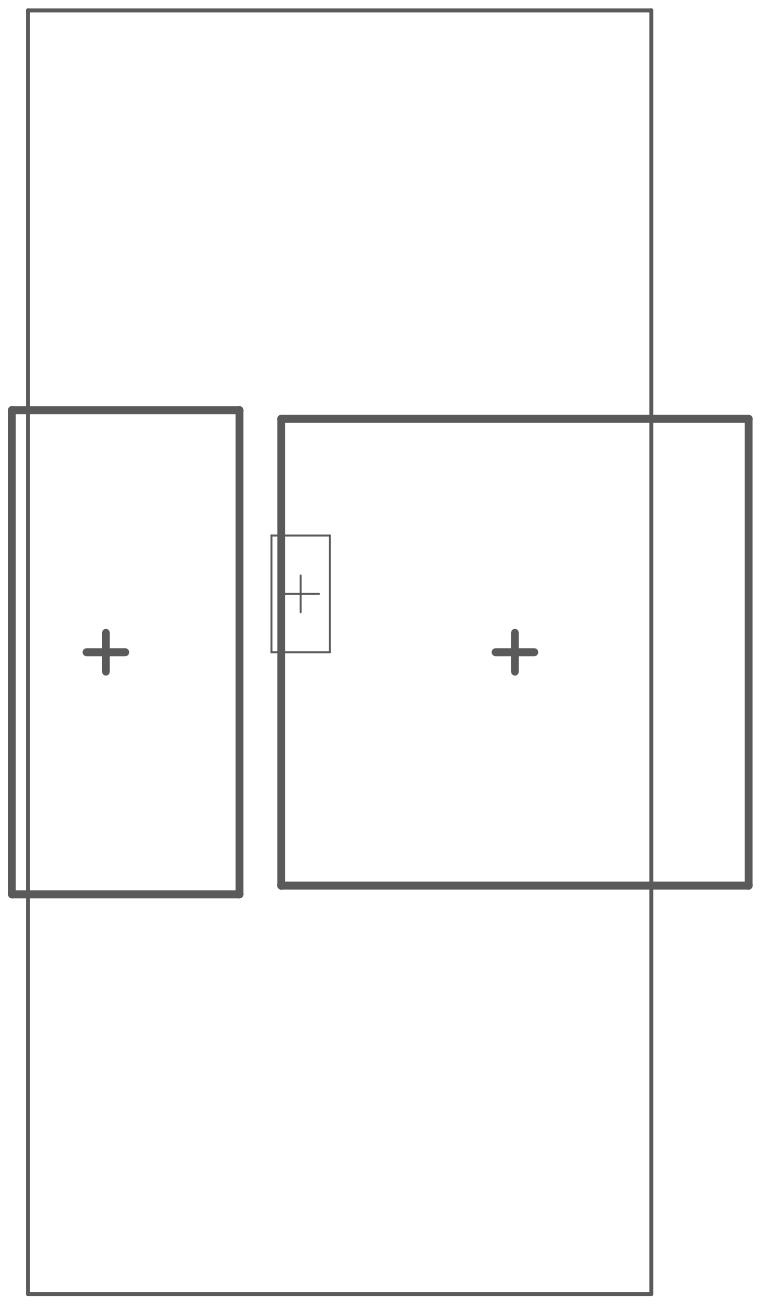
[picture p195: page 3]

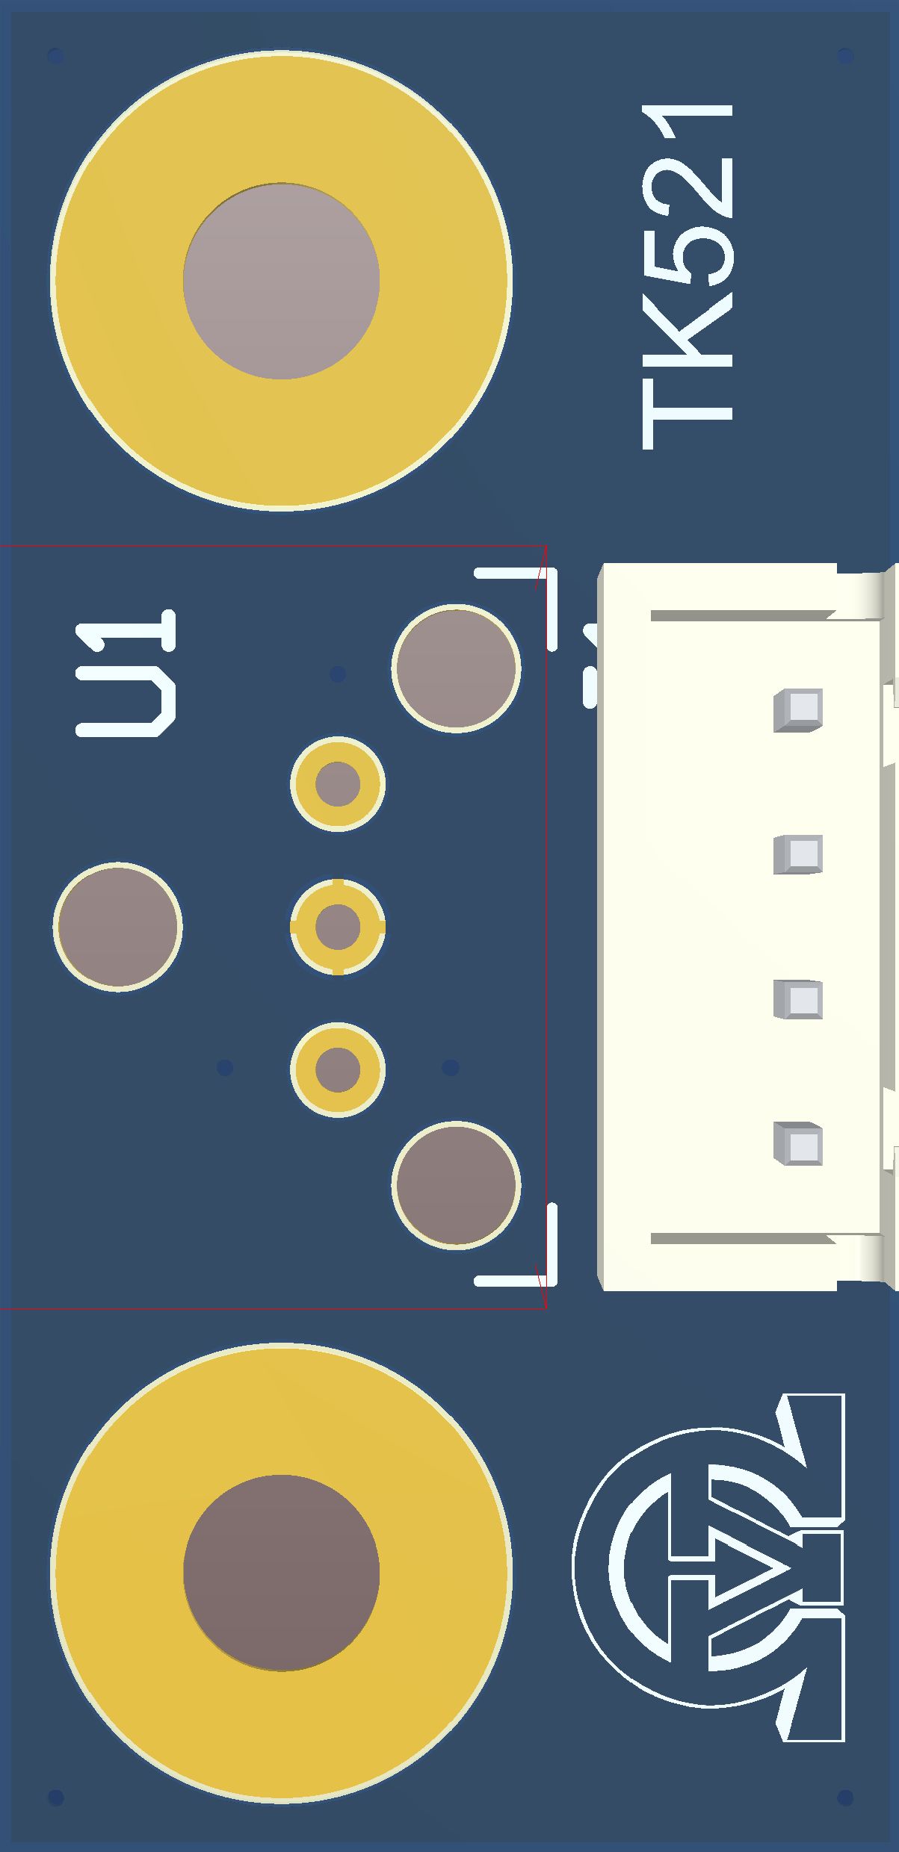
[picture p196: page 4]

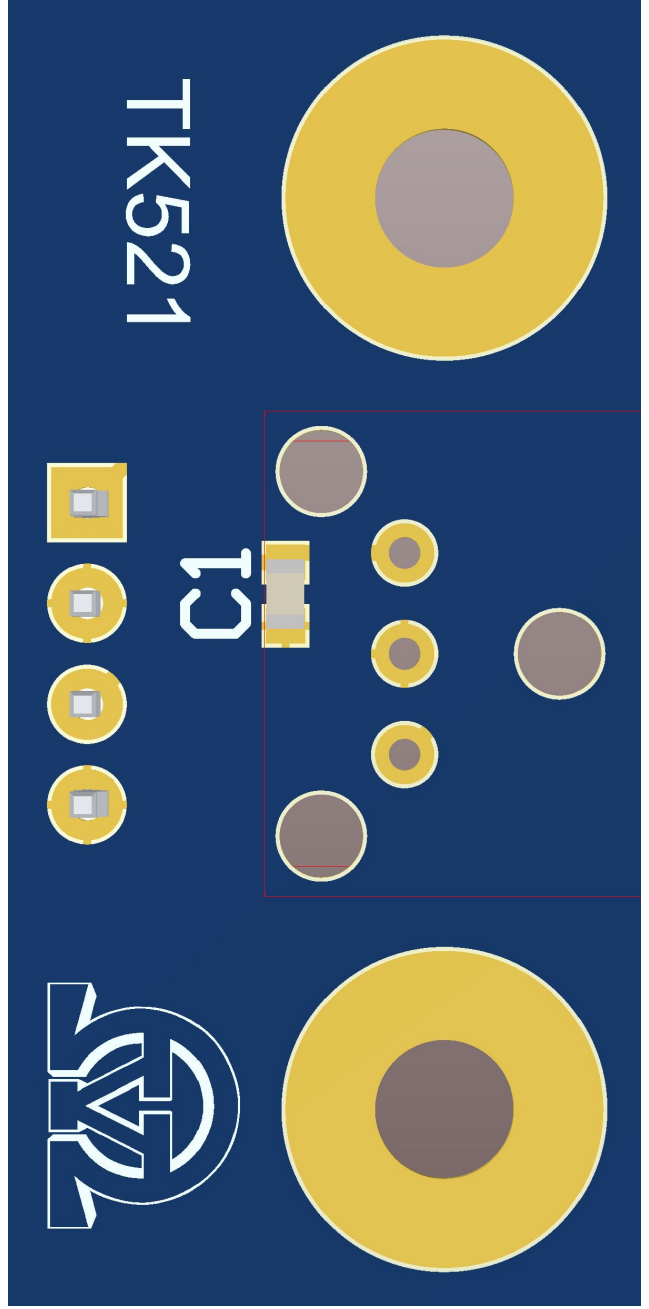
[picture p197: page 5]

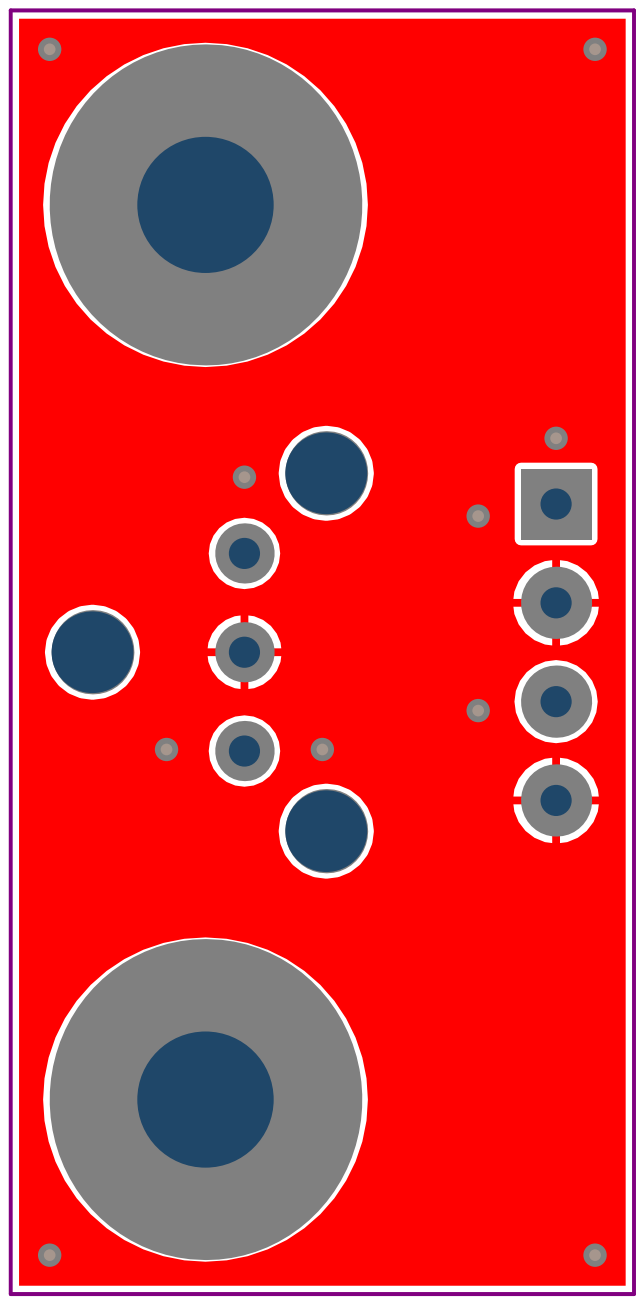
[picture p198: page 6]

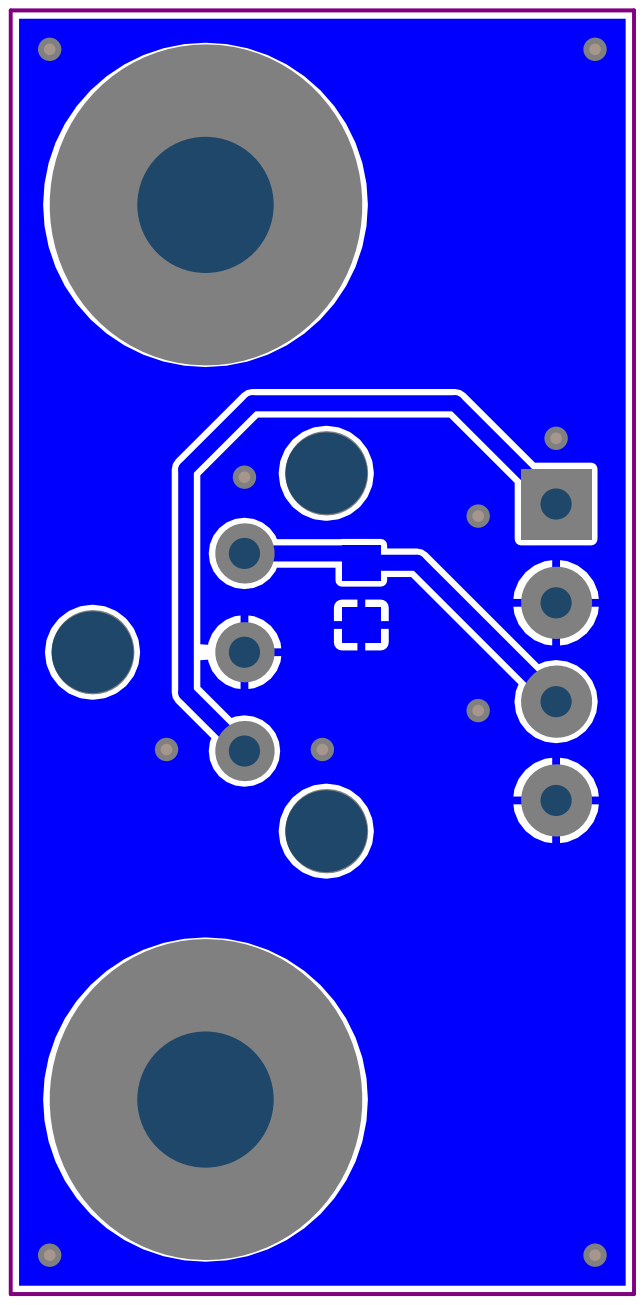
[picture p199: page 7]

LibRef | Designator
