Cable89/tesla-driver/01_Documentation/tesla stage 2.pdf

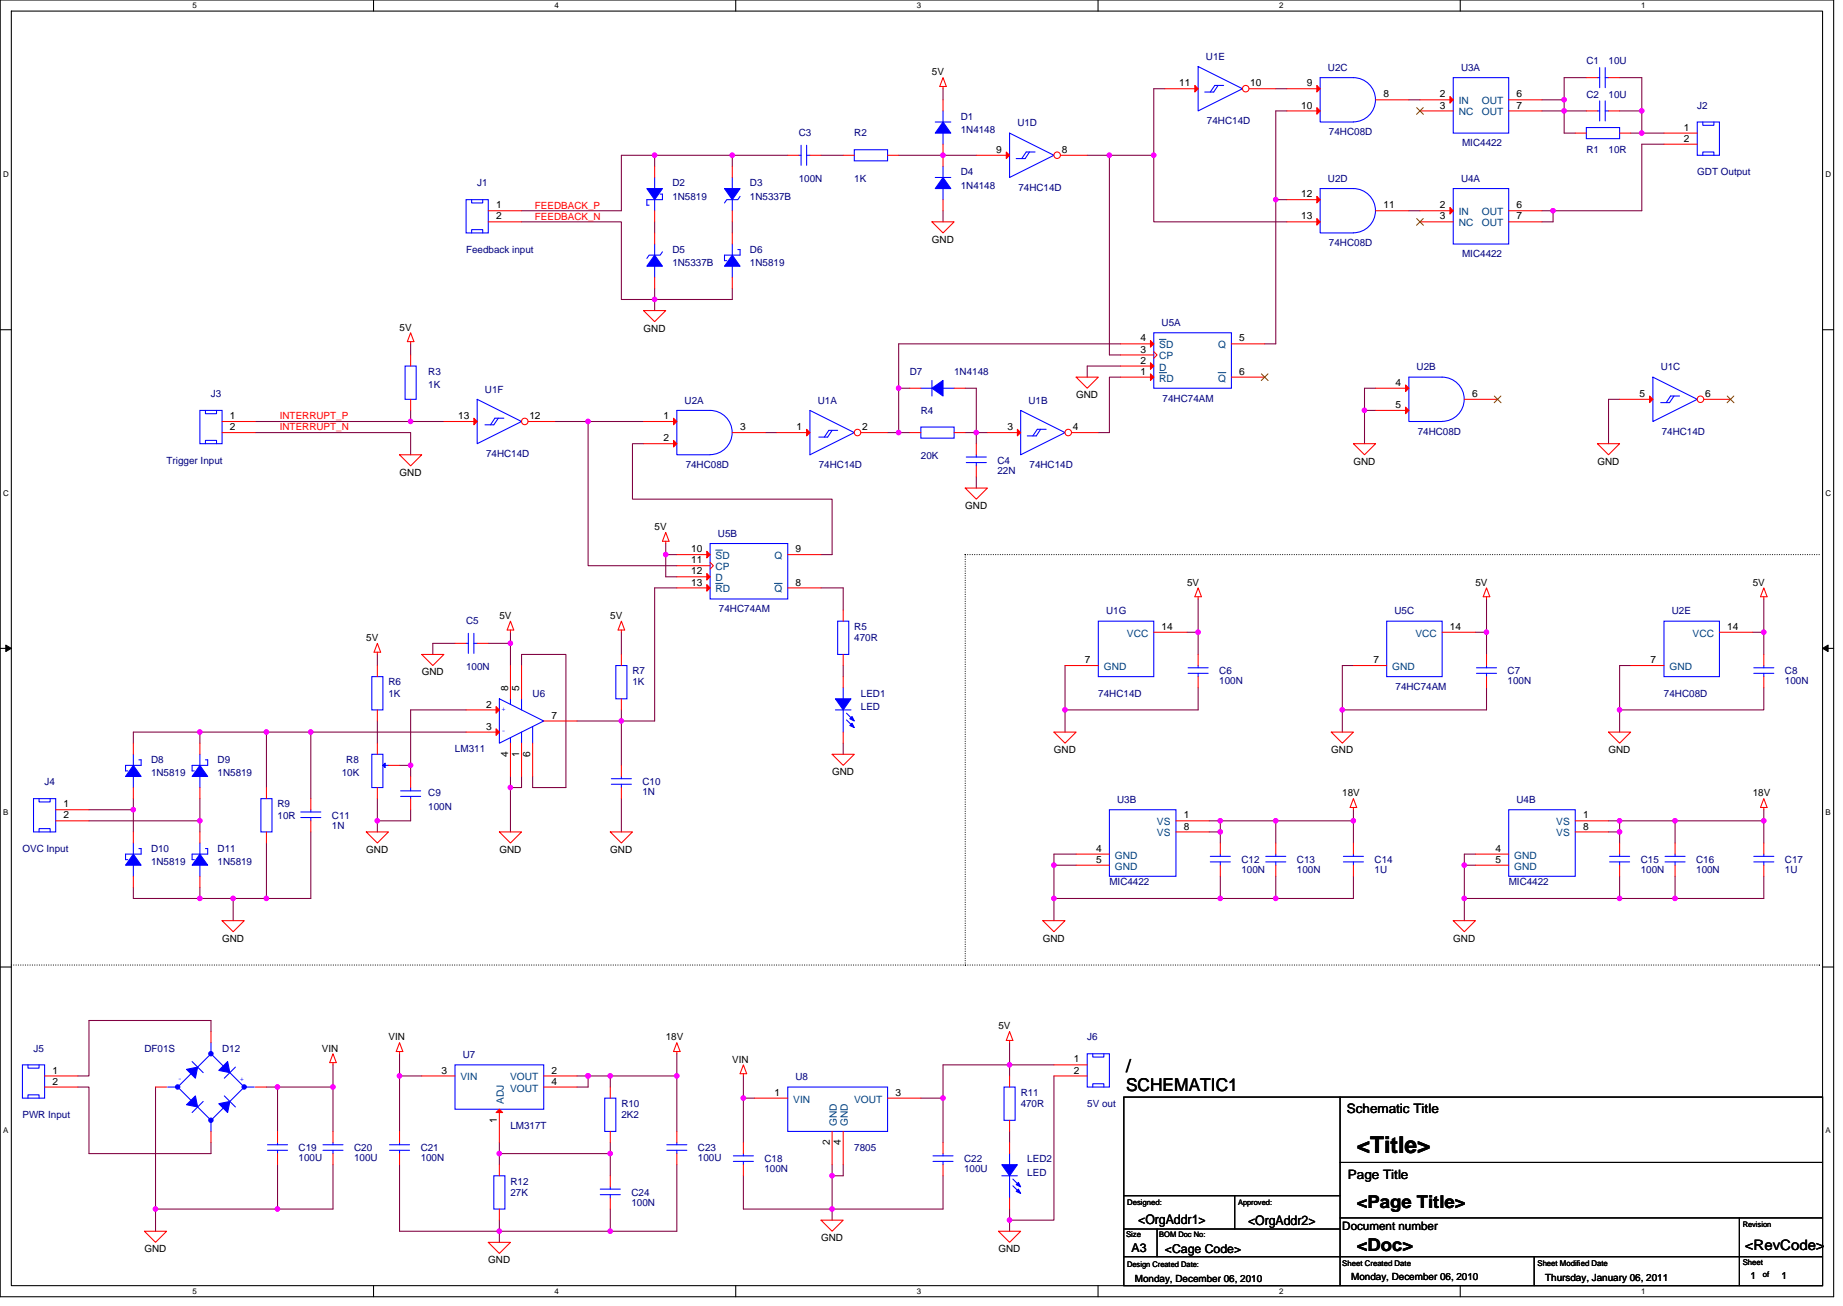
[picture p207: page 1]

Designed: Designed: Designed: <OrgAddr1> <OrgAddr1> <OrgAddr1> | Approved: Approved: Approved: <OrgAddr2> <OrgAddr2> <OrgAddr2>

Document number Document number Document number <Doc> <Doc> <Doc> | Revision Revision Revision <RevCode> <RevCode> <RevCode>

Size Size Size A3 A3 A3 | BOM Doc No: BOM Doc No: BOM Doc No: <Cage Code> <Cage Code> <Cage Code>

Design Created Date: Design Created Date: Design Created Date: Monday, December 06, 2010 Monday, December 06, 2010 Monday, December 06, 2010 | Sheet Created Date Sheet Created Date Sheet Created Date Monday, December 06, 2010 Monday, December 06, 2010 Monday, December 06, 2010 | Sheet Modified Date Sheet Modified Date Sheet Modified Date Thursday, January 06, 2011 Thursday, January 06, 2011 Thursday, January 06, 2011 | Sheet Sheet Sheet 1 1 1 of of of 1 1 1
