Cable89/tesla-driver/01_Documentation/TeslaCom2009.pdf

Modulation input.

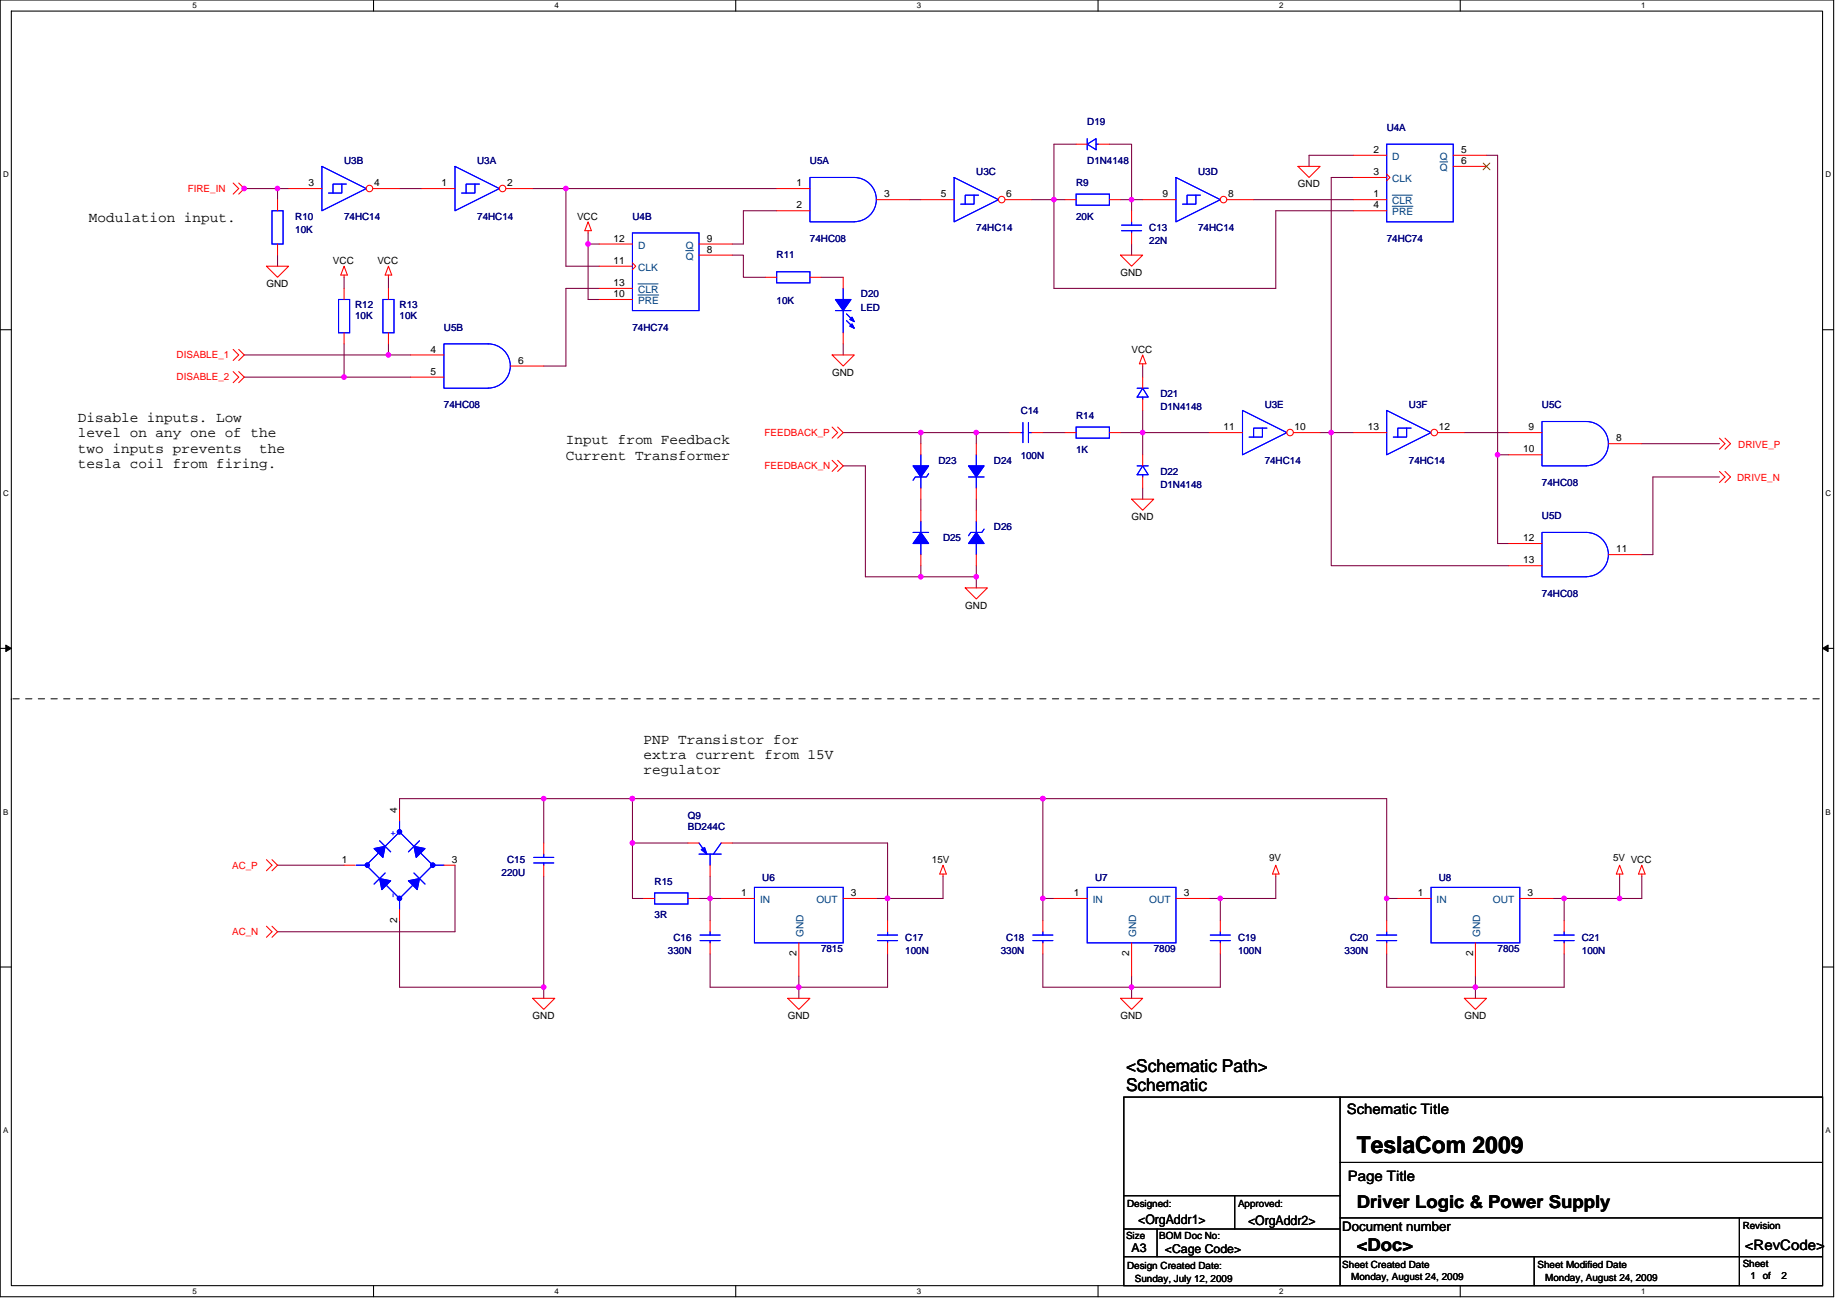
[picture p208: page 1]

Disable inputs. Low
level on any one of the
two inputs prevents the
tesla coil from firing.

Page Title
Driver Logic & Power Supply

Designed: Designed: Designed: <OrgAddr1> <OrgAddr1> <OrgAddr1> | Approved: Approved: Approved: <OrgAddr2> <OrgAddr2> <OrgAddr2>

Document number Document number Document number <Doc> <Doc> <Doc> | Revision Revision Revision <RevCode> <RevCode> <RevCode>

Size Size Size A3 A3 A3 | BOM Doc No: BOM Doc No: BOM Doc No: <Cage Code> <Cage Code> <Cage Code>

Design Created Date: Design Created Date: Design Created Date: Sunday, July 12, 2009 Sunday, July 12, 2009 Sunday, July 12, 2009 | Sheet Created Date Sheet Created Date Sheet Created Date Monday, August 24, 2009 Monday, August 24, 2009 Monday, August 24, 2009 | Sheet Modified Date Sheet Modified Date Sheet Modified Date Monday, August 24, 2009 Monday, August 24, 2009 Monday, August 24, 2009 | Sheet Sheet Sheet 1 1 1 of of of 2 2 2

# IGBT Full Bridge

## HUGE

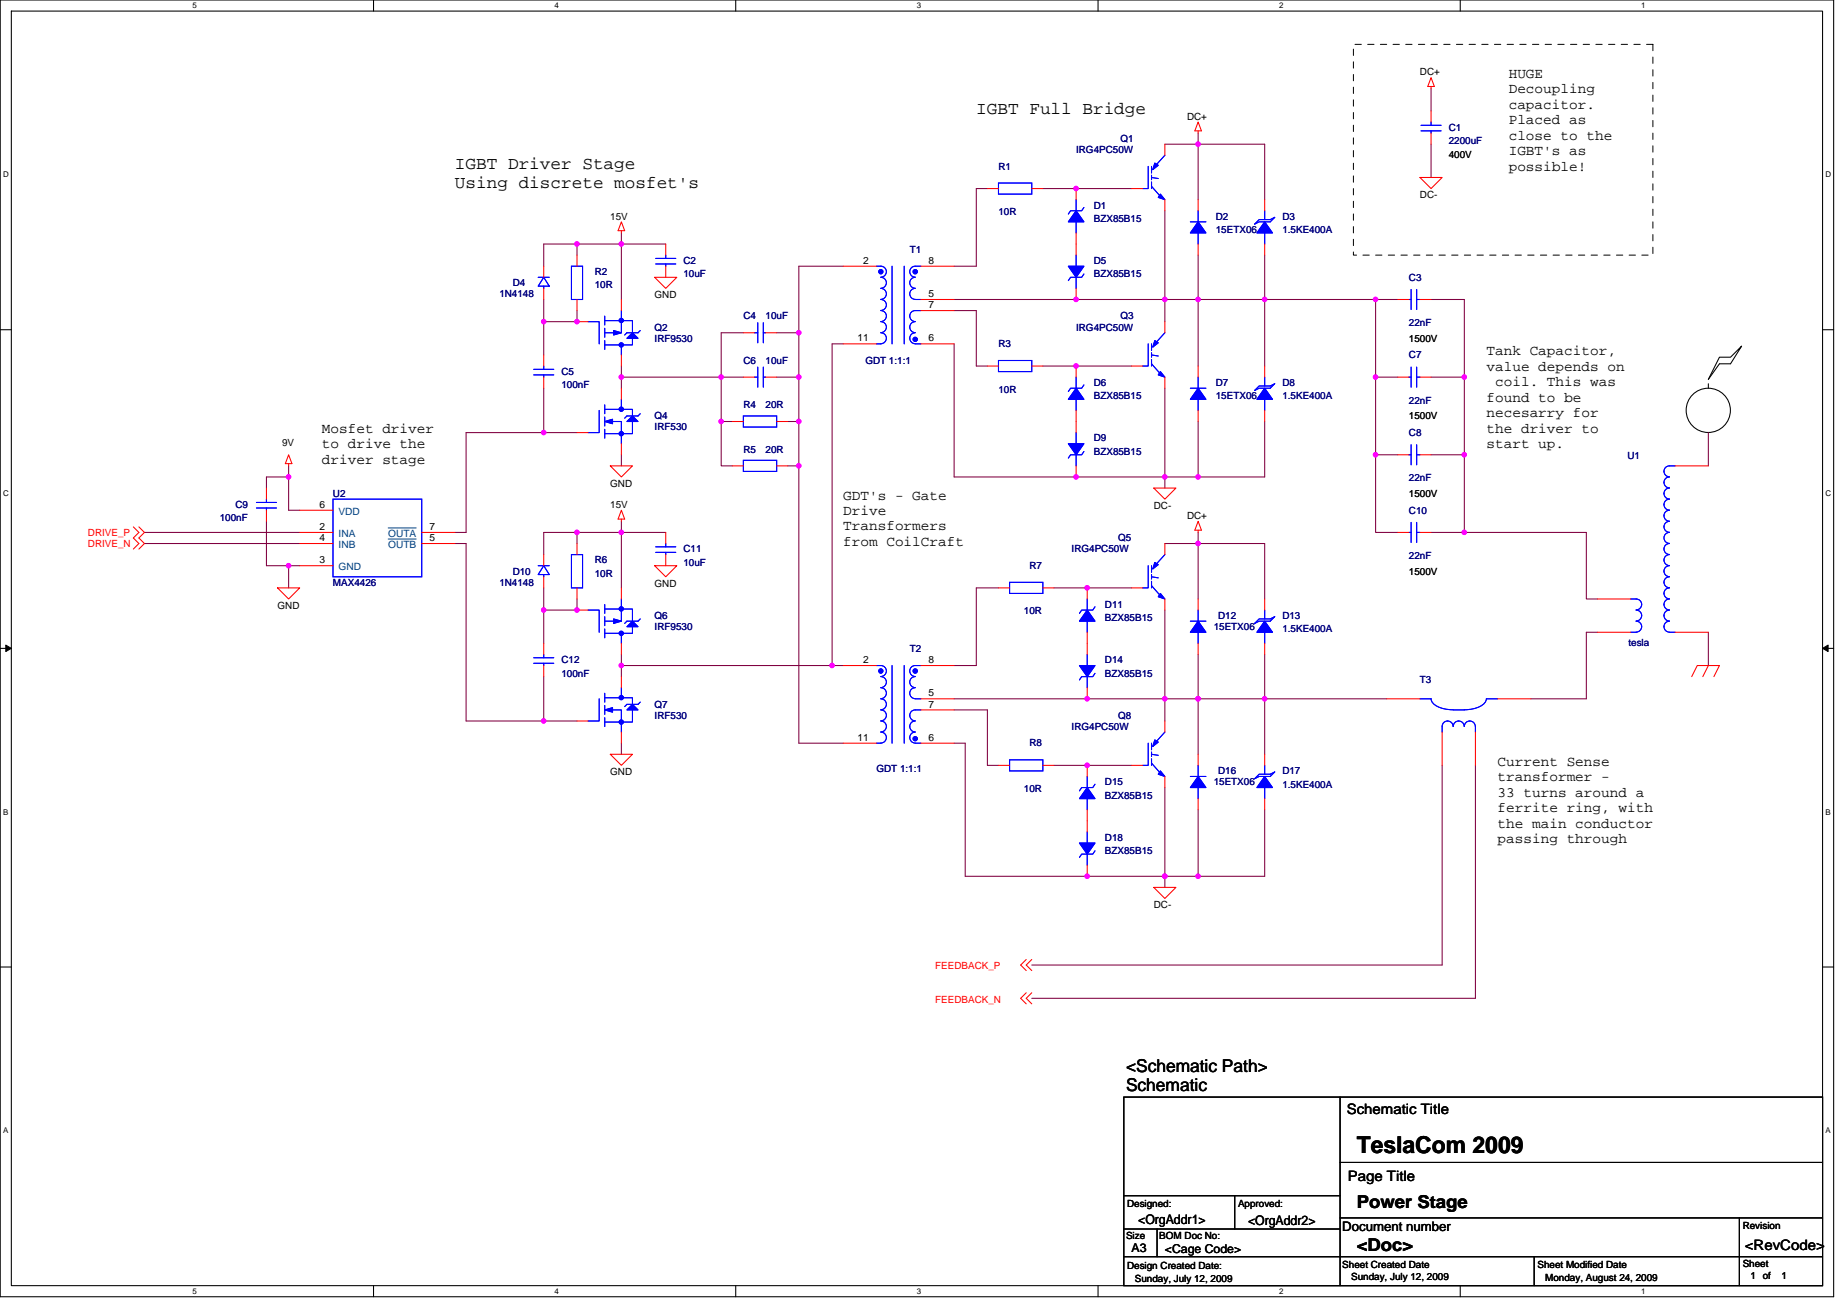
[picture p209: page 2]

Designed: Designed: Designed: <OrgAddr1> <OrgAddr1> <OrgAddr1> | Approved: Approved: Approved: <OrgAddr2> <OrgAddr2> <OrgAddr2>

Document number Document number Document number <Doc> <Doc> <Doc> | Revision Revision Revision <RevCode> <RevCode> <RevCode>

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

Design Created Date: Design Created Date: Design Created Date: Sunday, July 12, 2009 Sunday, July 12, 2009 Sunday, July 12, 2009 | Sheet Created Date Sheet Created Date Sheet Created Date Sunday, July 12, 2009 Sunday, July 12, 2009 Sunday, July 12, 2009 | Sheet Modified Date Sheet Modified Date Sheet Modified Date Monday, August 24, 2009 Monday, August 24, 2009 Monday, August 24, 2009 | Sheet Sheet Sheet 1 1 1 of of of 1 1 1
