Cable89/tesla-driver/01_Documentation/Forenklet skjema/Spolerigg1.pdf

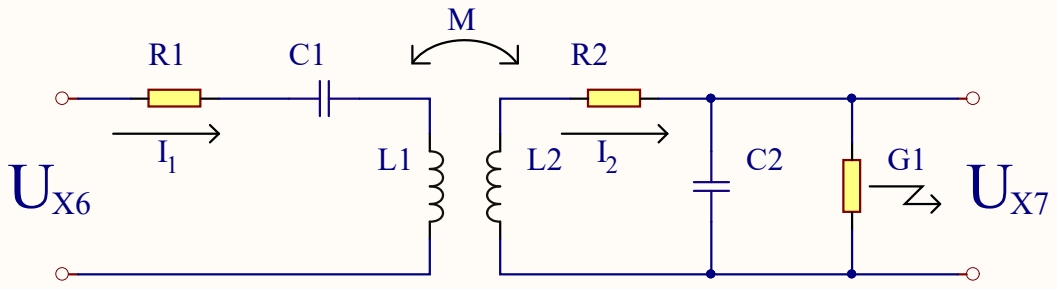
[picture p210: page 1]

Title: TK531 Utgangstrinn

Size: A3 | Revision: 2 | Author: Øystein Smith

Date: 23.06.2017 | Sheet 18 of 20 | Omega Verksted

C:\git\tesla-driver\01_Documentation\Forenklet skjema\Spolerigg1.SchDoc
File:
