Cable89/tesla-driver/01_Documentation/Forenklet skjema/TK514_Interrupter.pdf

# IGBT drivers

# X4_A

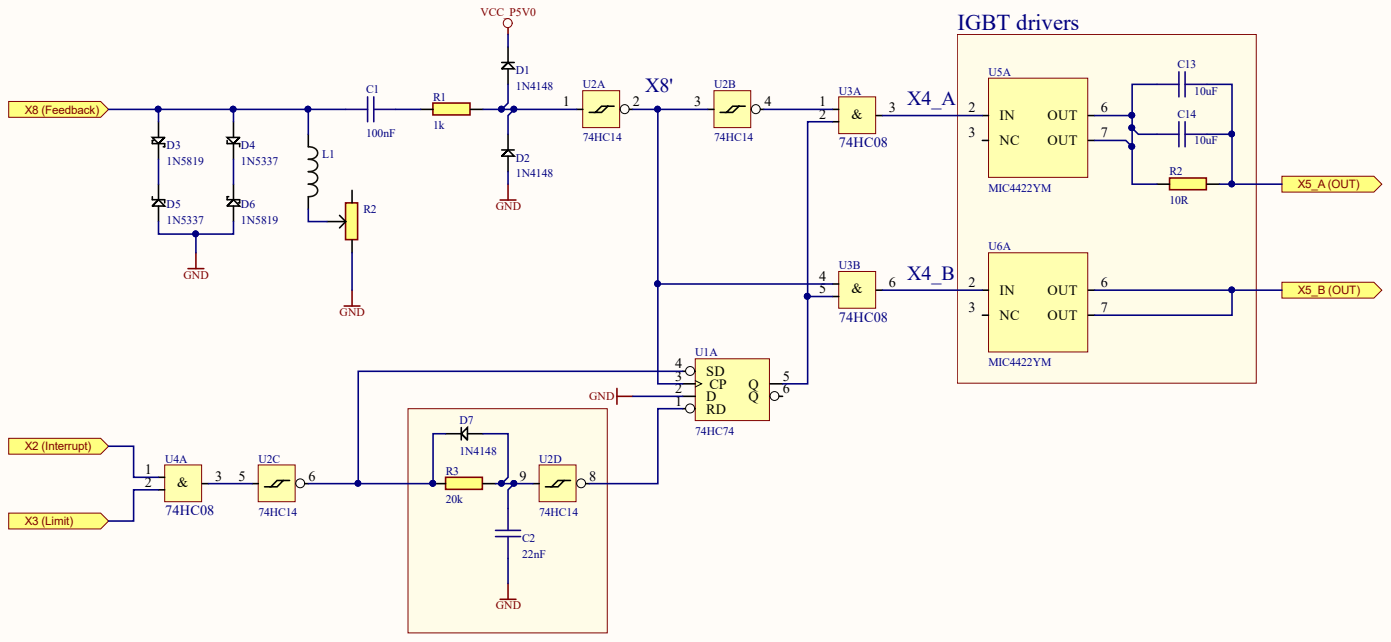
[picture p211: page 1]
