Cable89/tesla-driver/01_Documentation/Forenklet skjema/TK513_Limiter.pdf

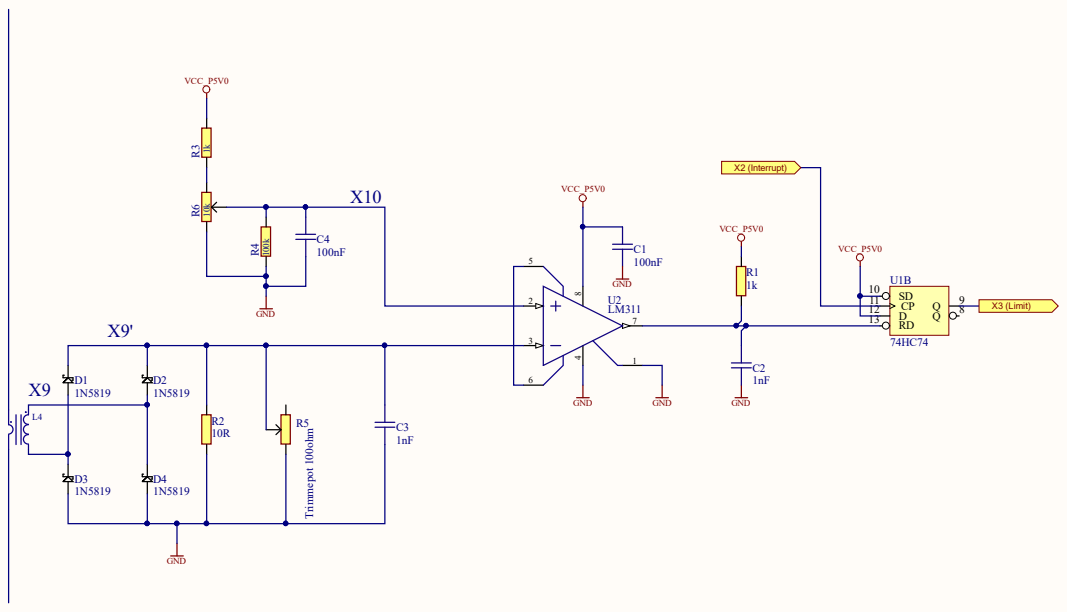
[picture p213: page 1]

Title: TK513 Limiter

Size: A3 | Revision: 0 | Author: Øystein Smith

Date: 13.06.2017 | Sheet 7 of 20 | Omega Verksted

C:\git\tesla-driver\01_Documentation\Forenklet skjema\TK513_Limiter.SchDoc
File:
