Cable89/tesla-driver/05_Hardware/TK500_Driver/TK531_Utgangstrinn/Project Outputs/TK531_Utgangstrinn.PDF

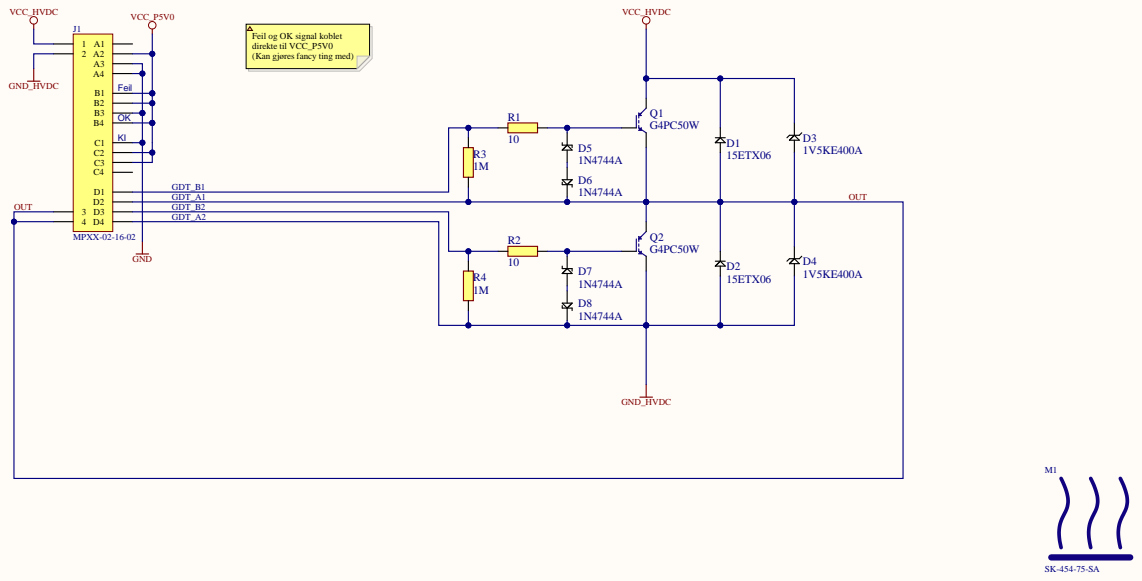
[picture p216: page 1]

Feil og OK signal koblet
direkte til VC
(Kan gj

GDT_A 1
GDT_B 2
GDT_A 2

C:\git\omega verksted\tesla-driver\05_Hardware\TK500_Driver\TK531_Utgangstrinn\TK531_Utgangstrinn

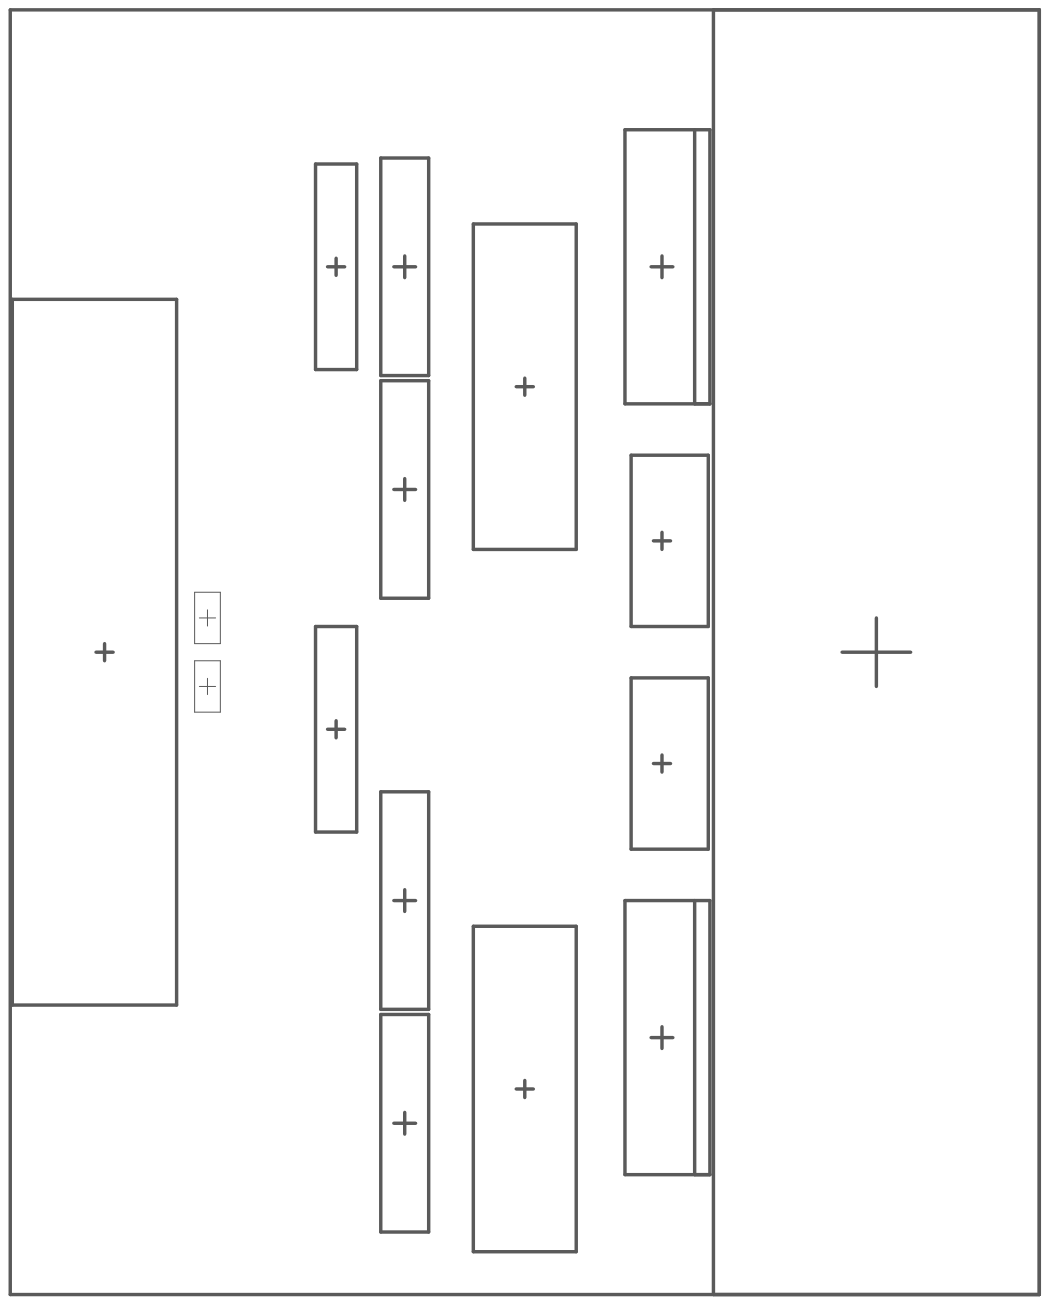
[picture p217: page 2]

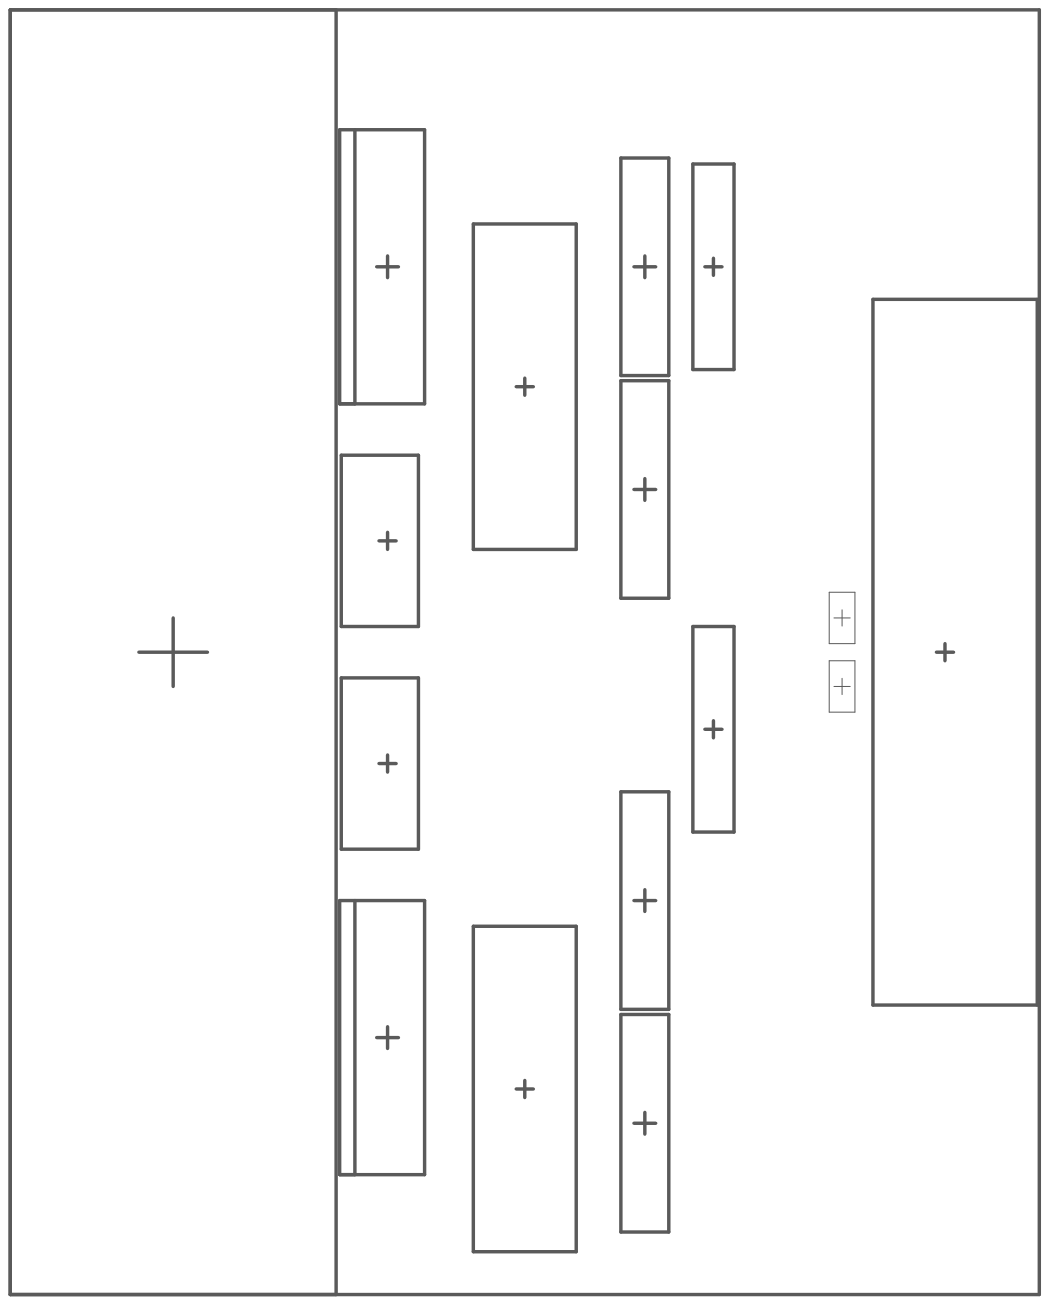
[picture p218: page 3]

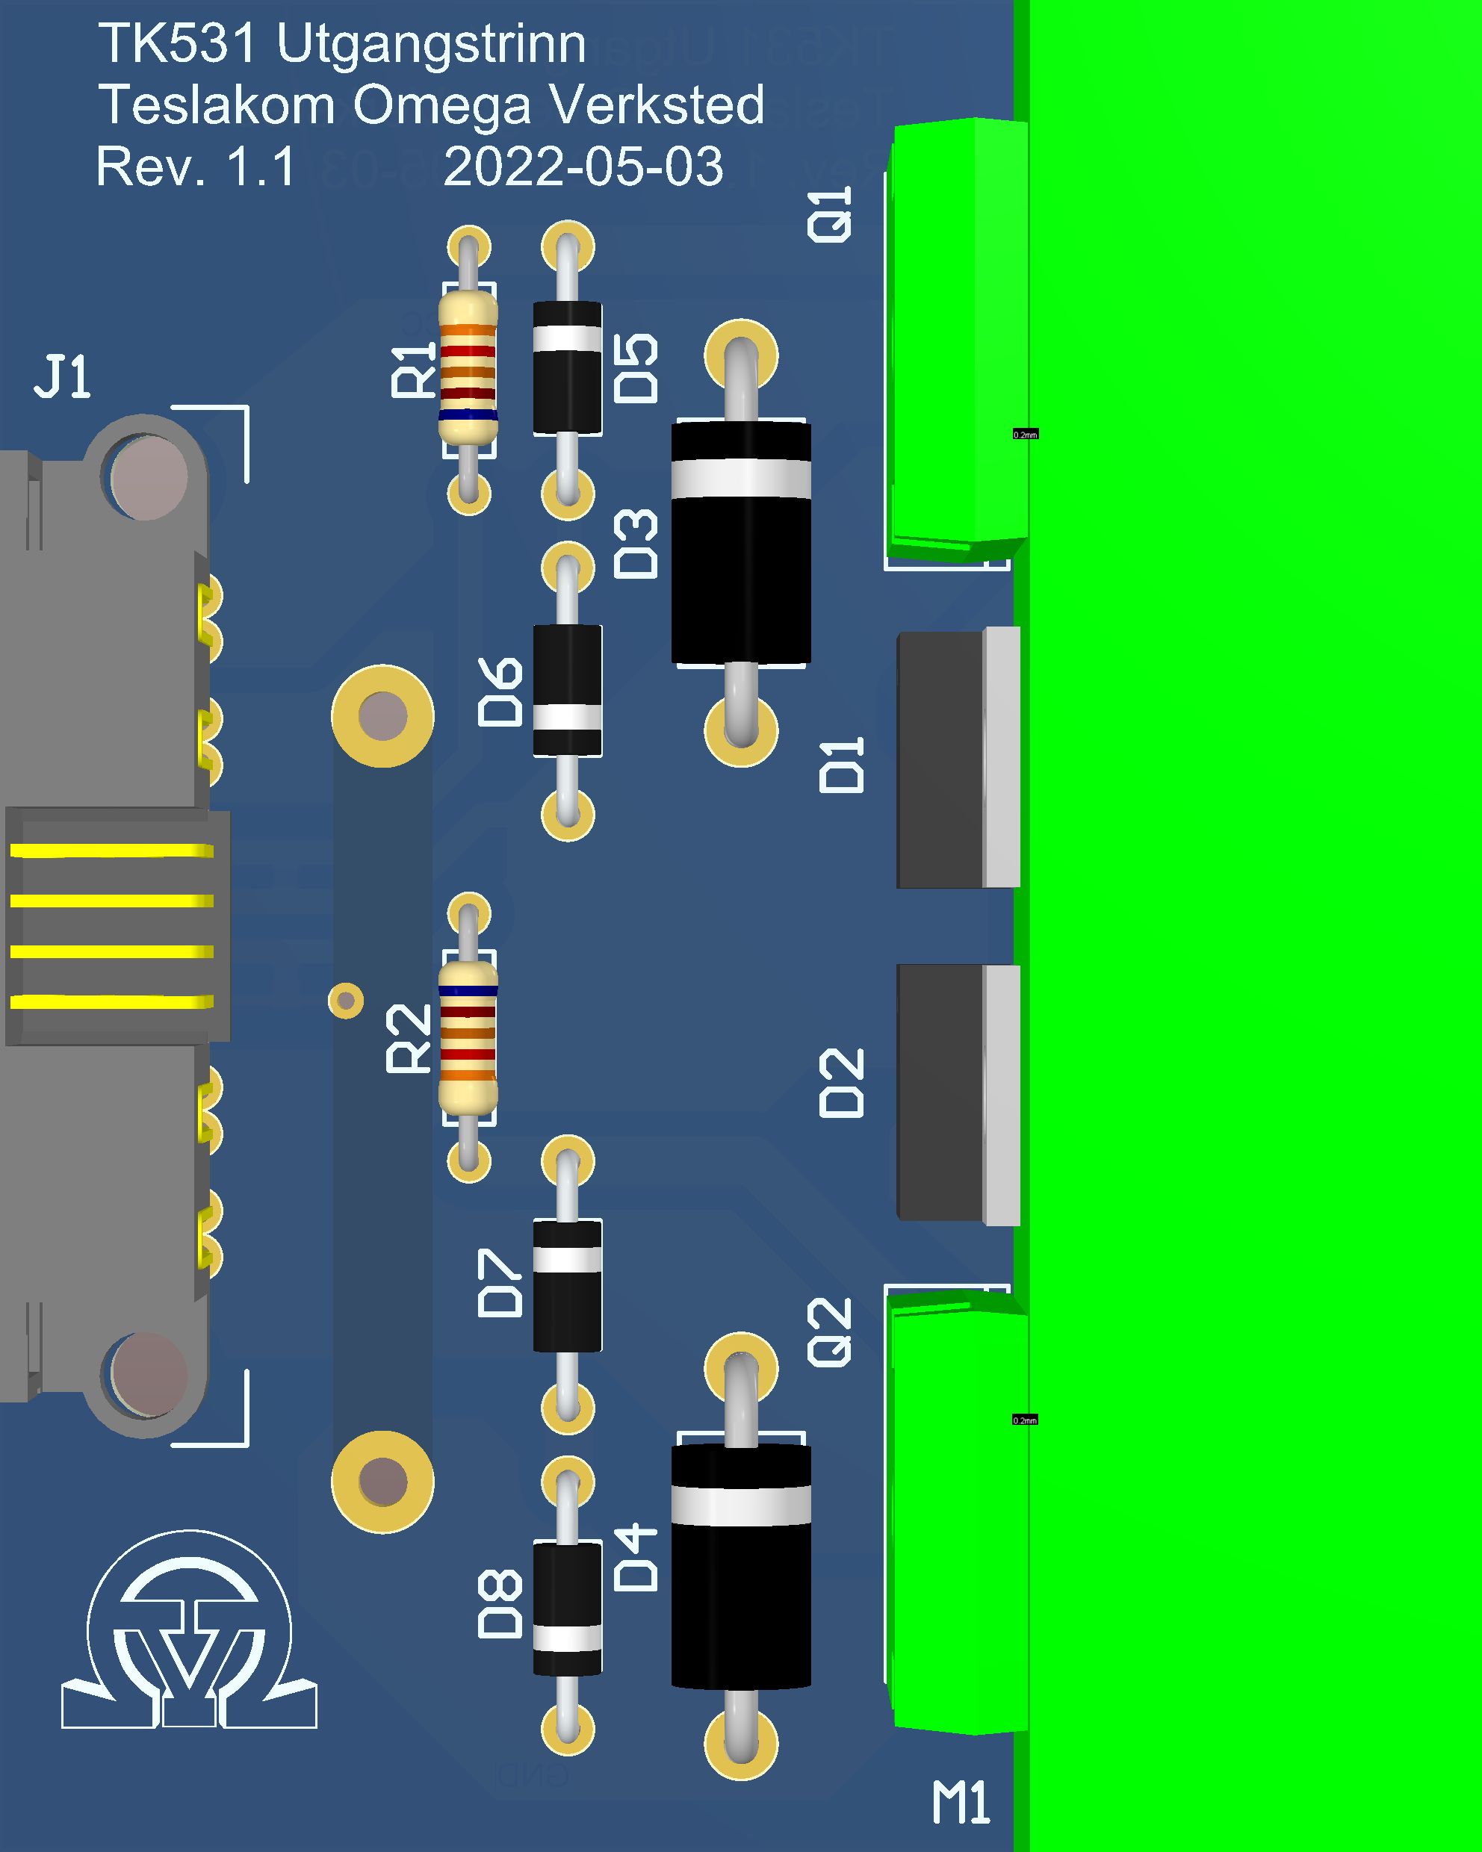
[picture p219: page 4]

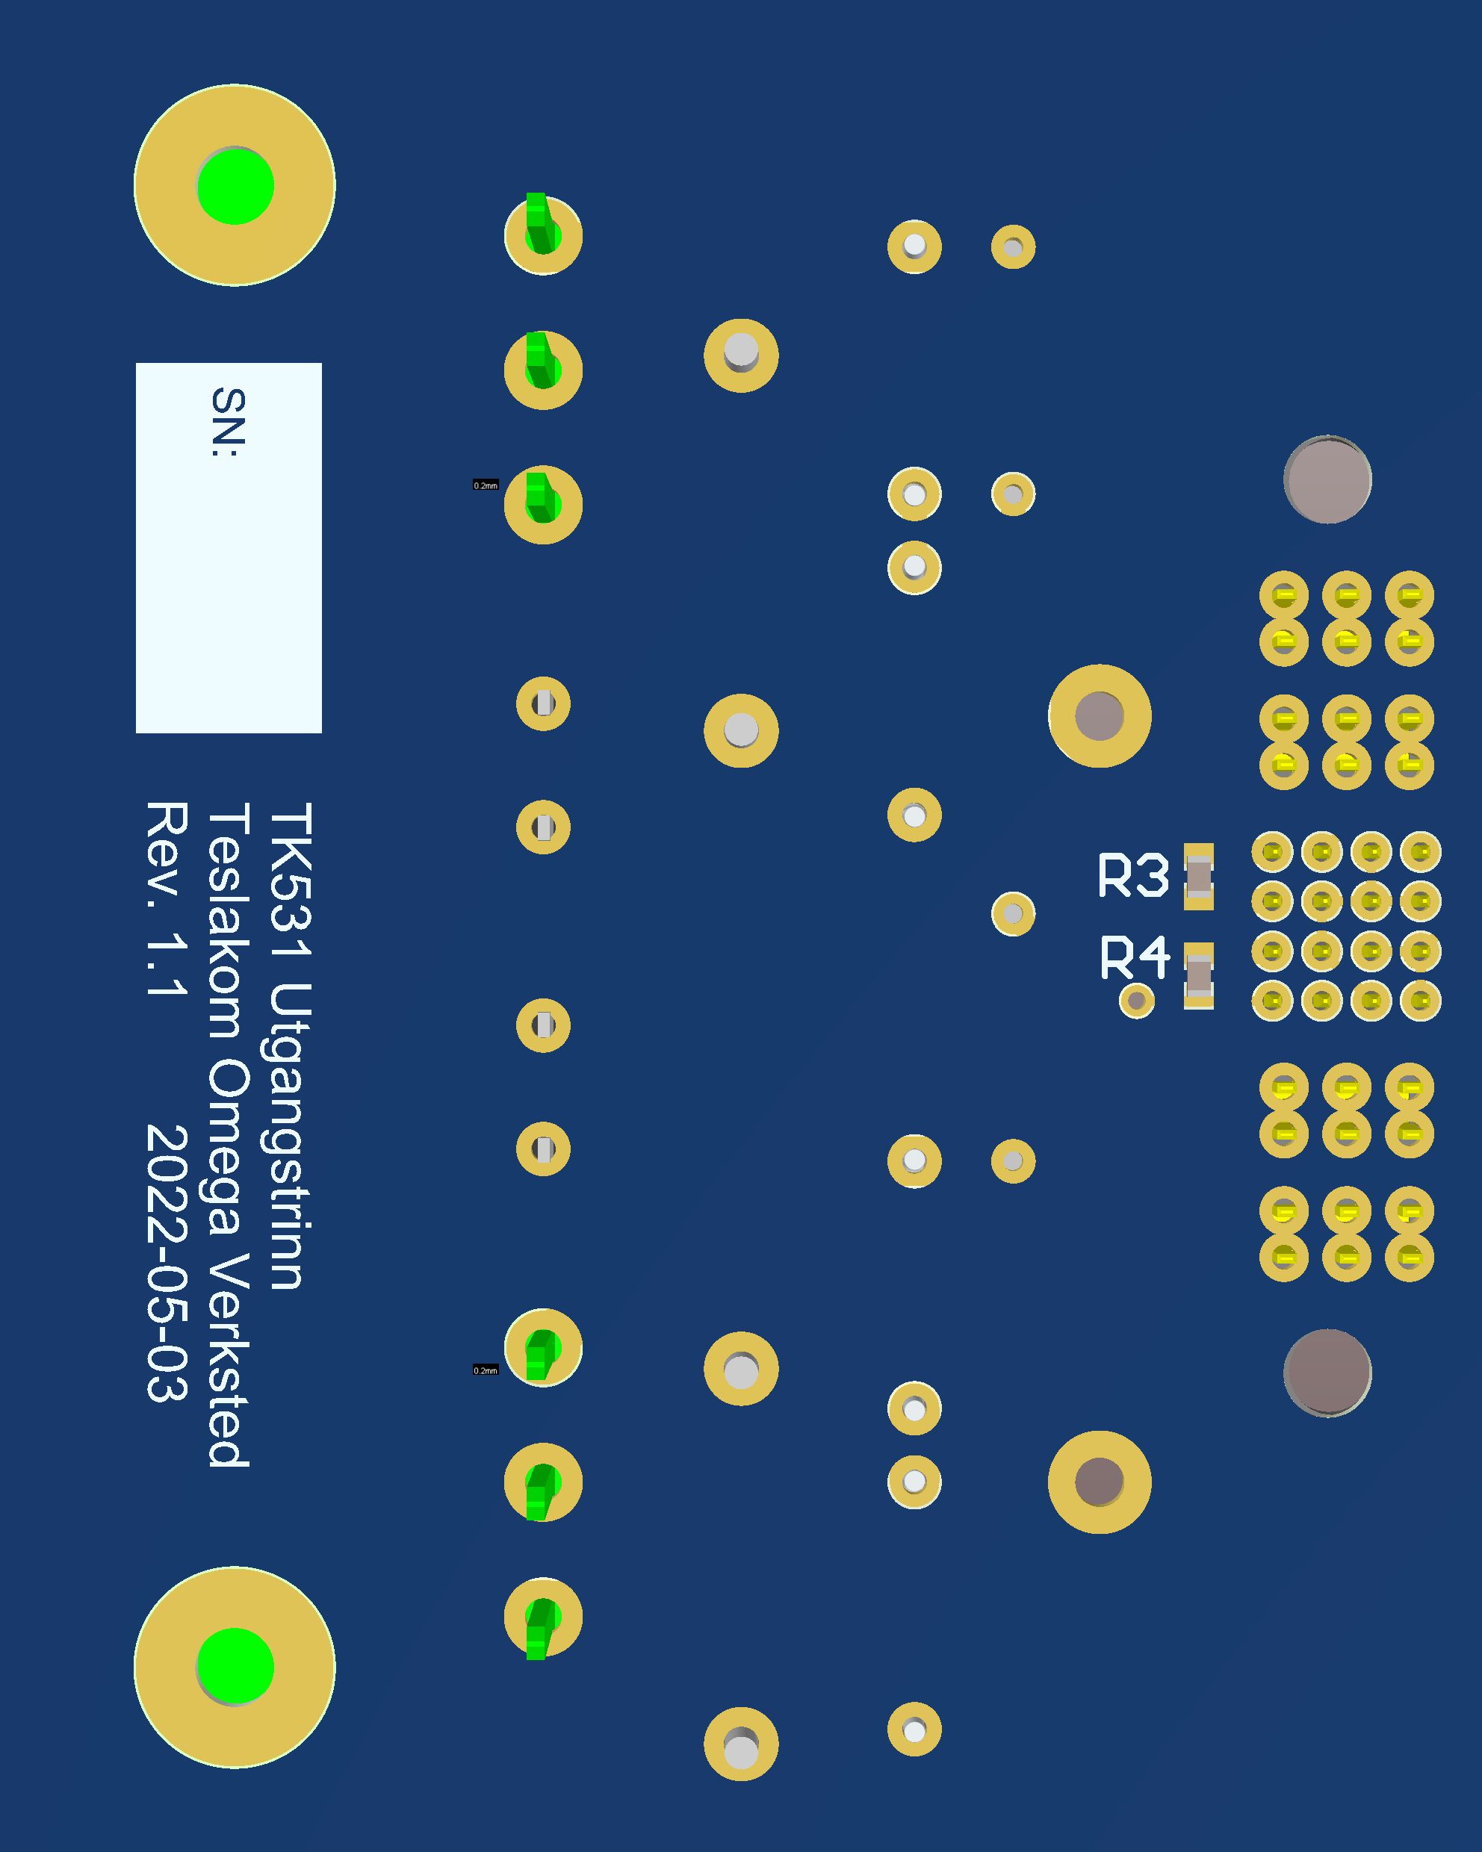
[picture p220: page 5]

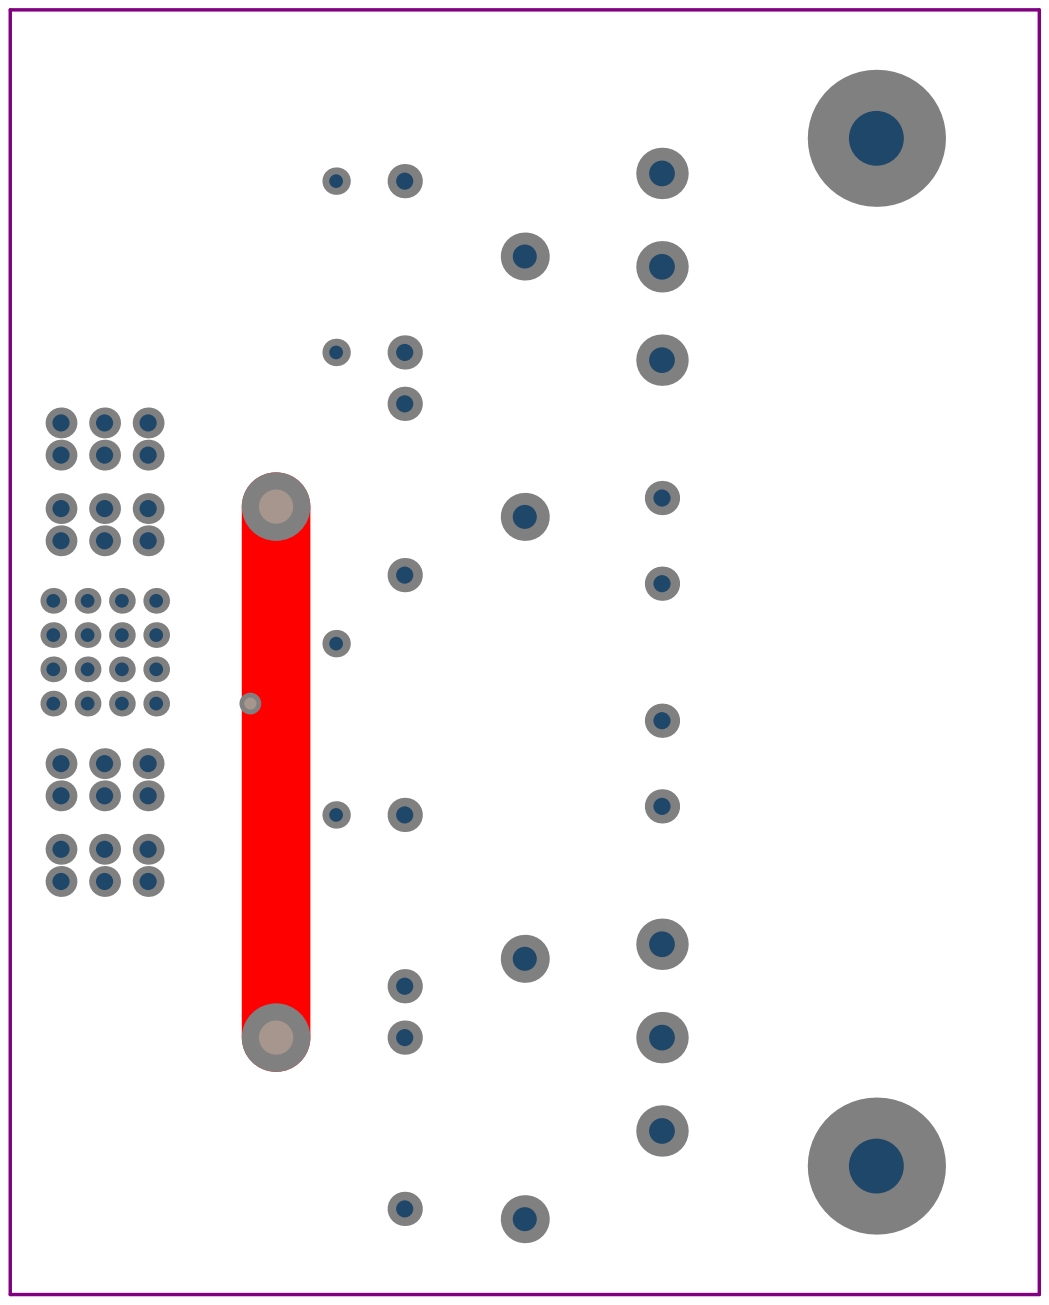
[picture p221: page 6]

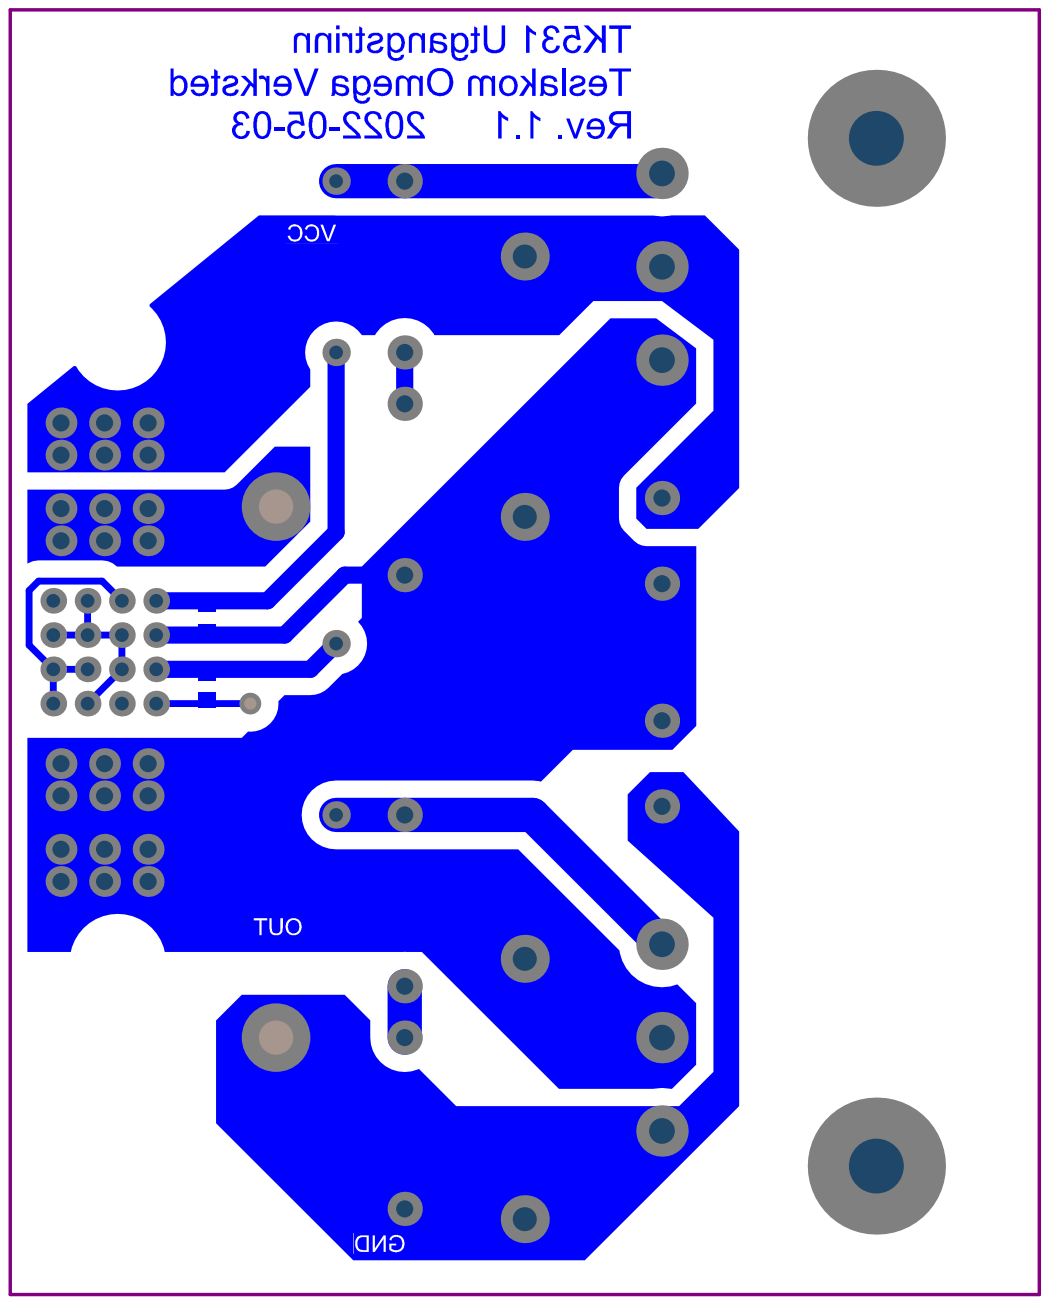
[picture p222: page 7]

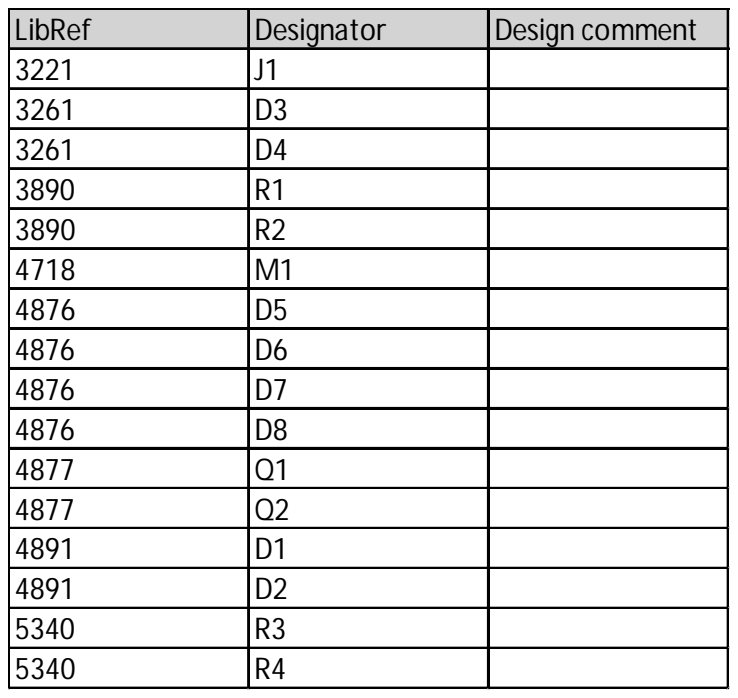
[picture p223: page 8]

LibRef | Designator | Design comment
3221 | J1
3261 | D3
3261 | D4
3890 | R1
3890 | R2
4718 | M1
4876 | D5
4876 | D6
4876 | D7
4876 | D8
4877 | Q1
4877 | Q2
4891 | D1
4891 | D2
5340 | R3
5340 | R4
