Cable89/tesla-driver/05_Hardware/TK500_Driver/TK522_LV-Trafo/Project Outputs/TK522_LV-Trafo.PDF

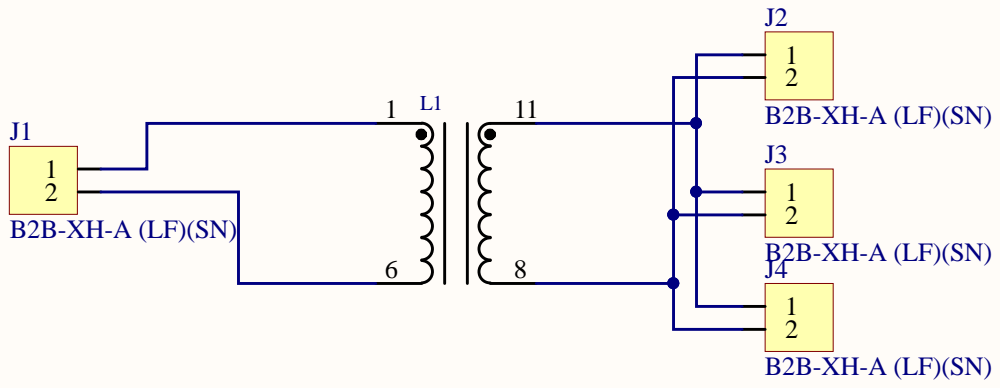
[picture p224: page 1]

Title: TK517 P5V0-PSU

Size: A3 | Revision: 10 20 0 | Author : *

Date: | Sheet of | Omega Verksted

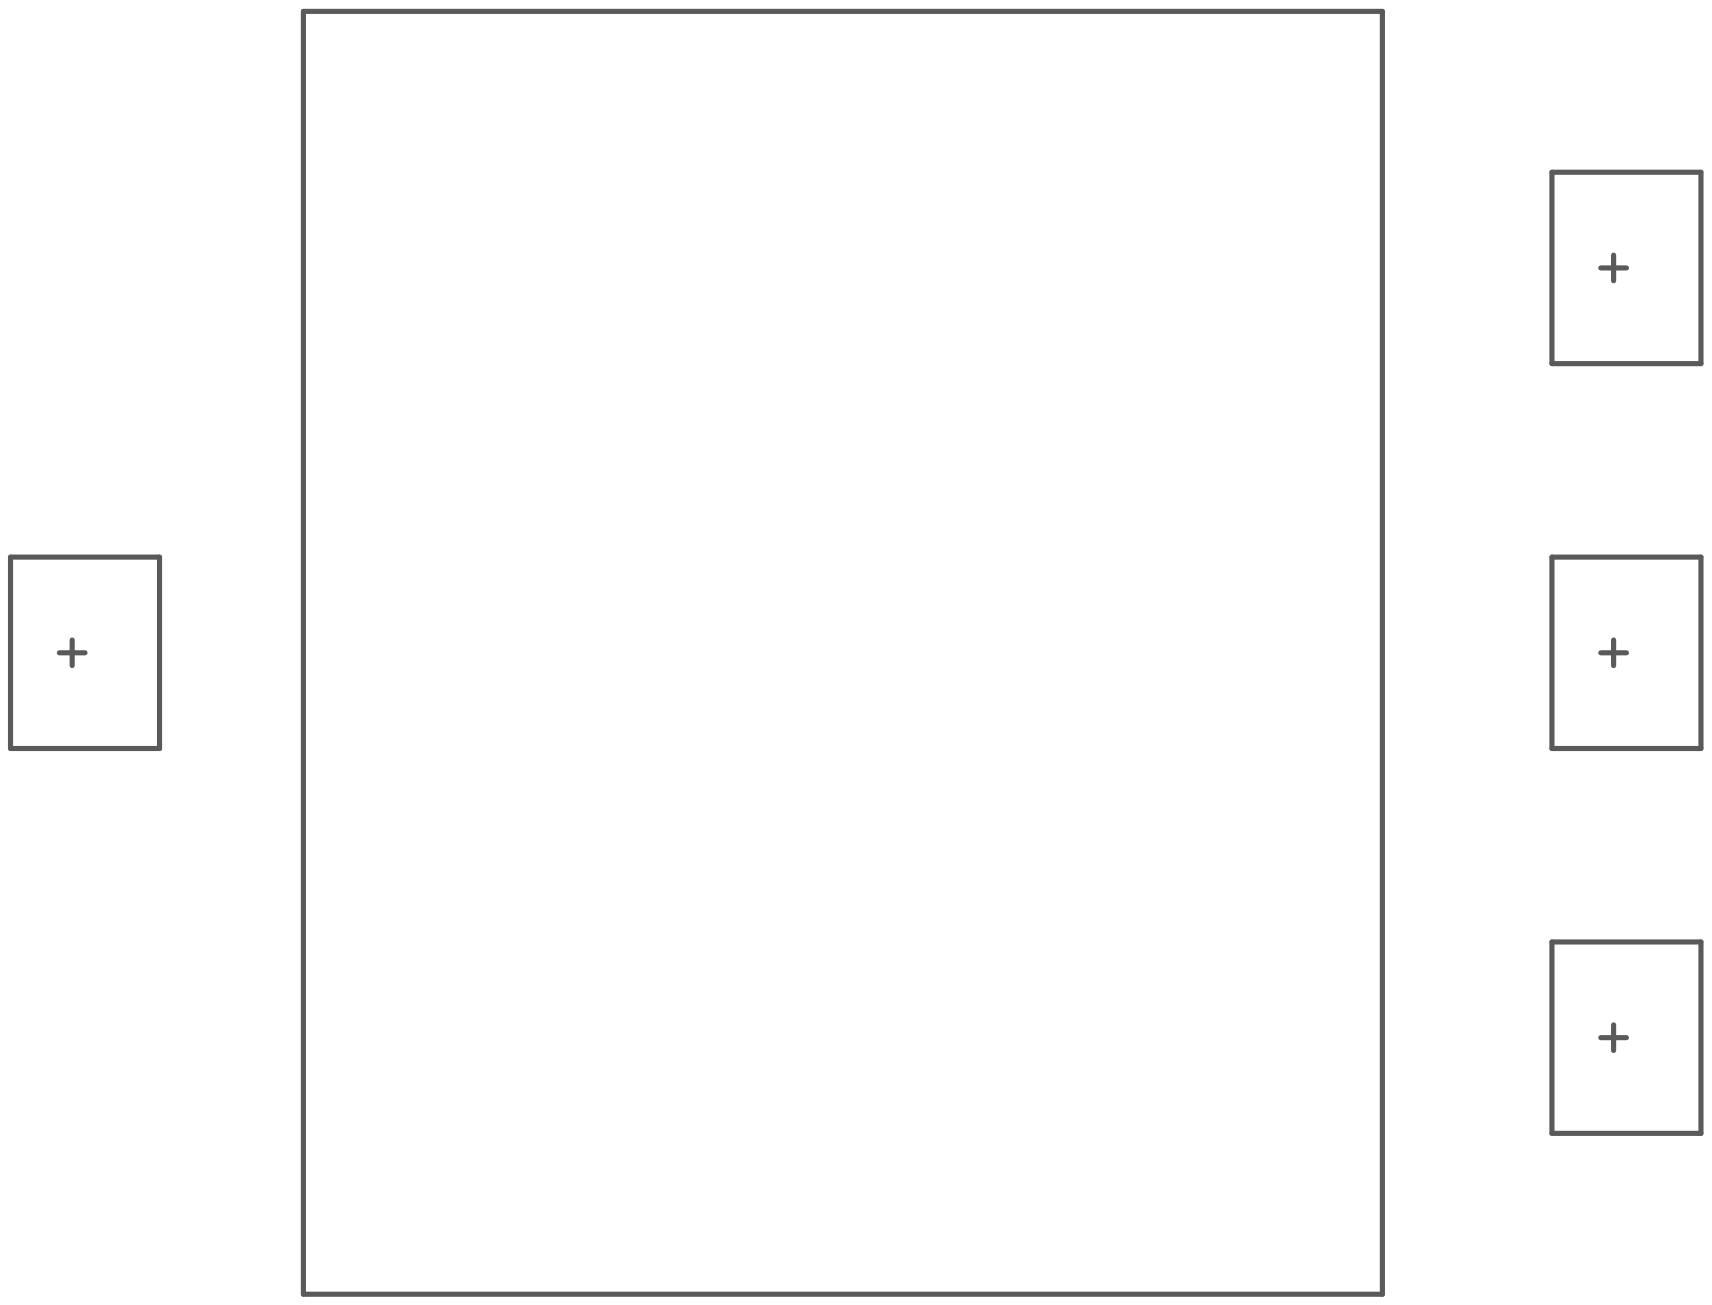
[picture p225: page 2]

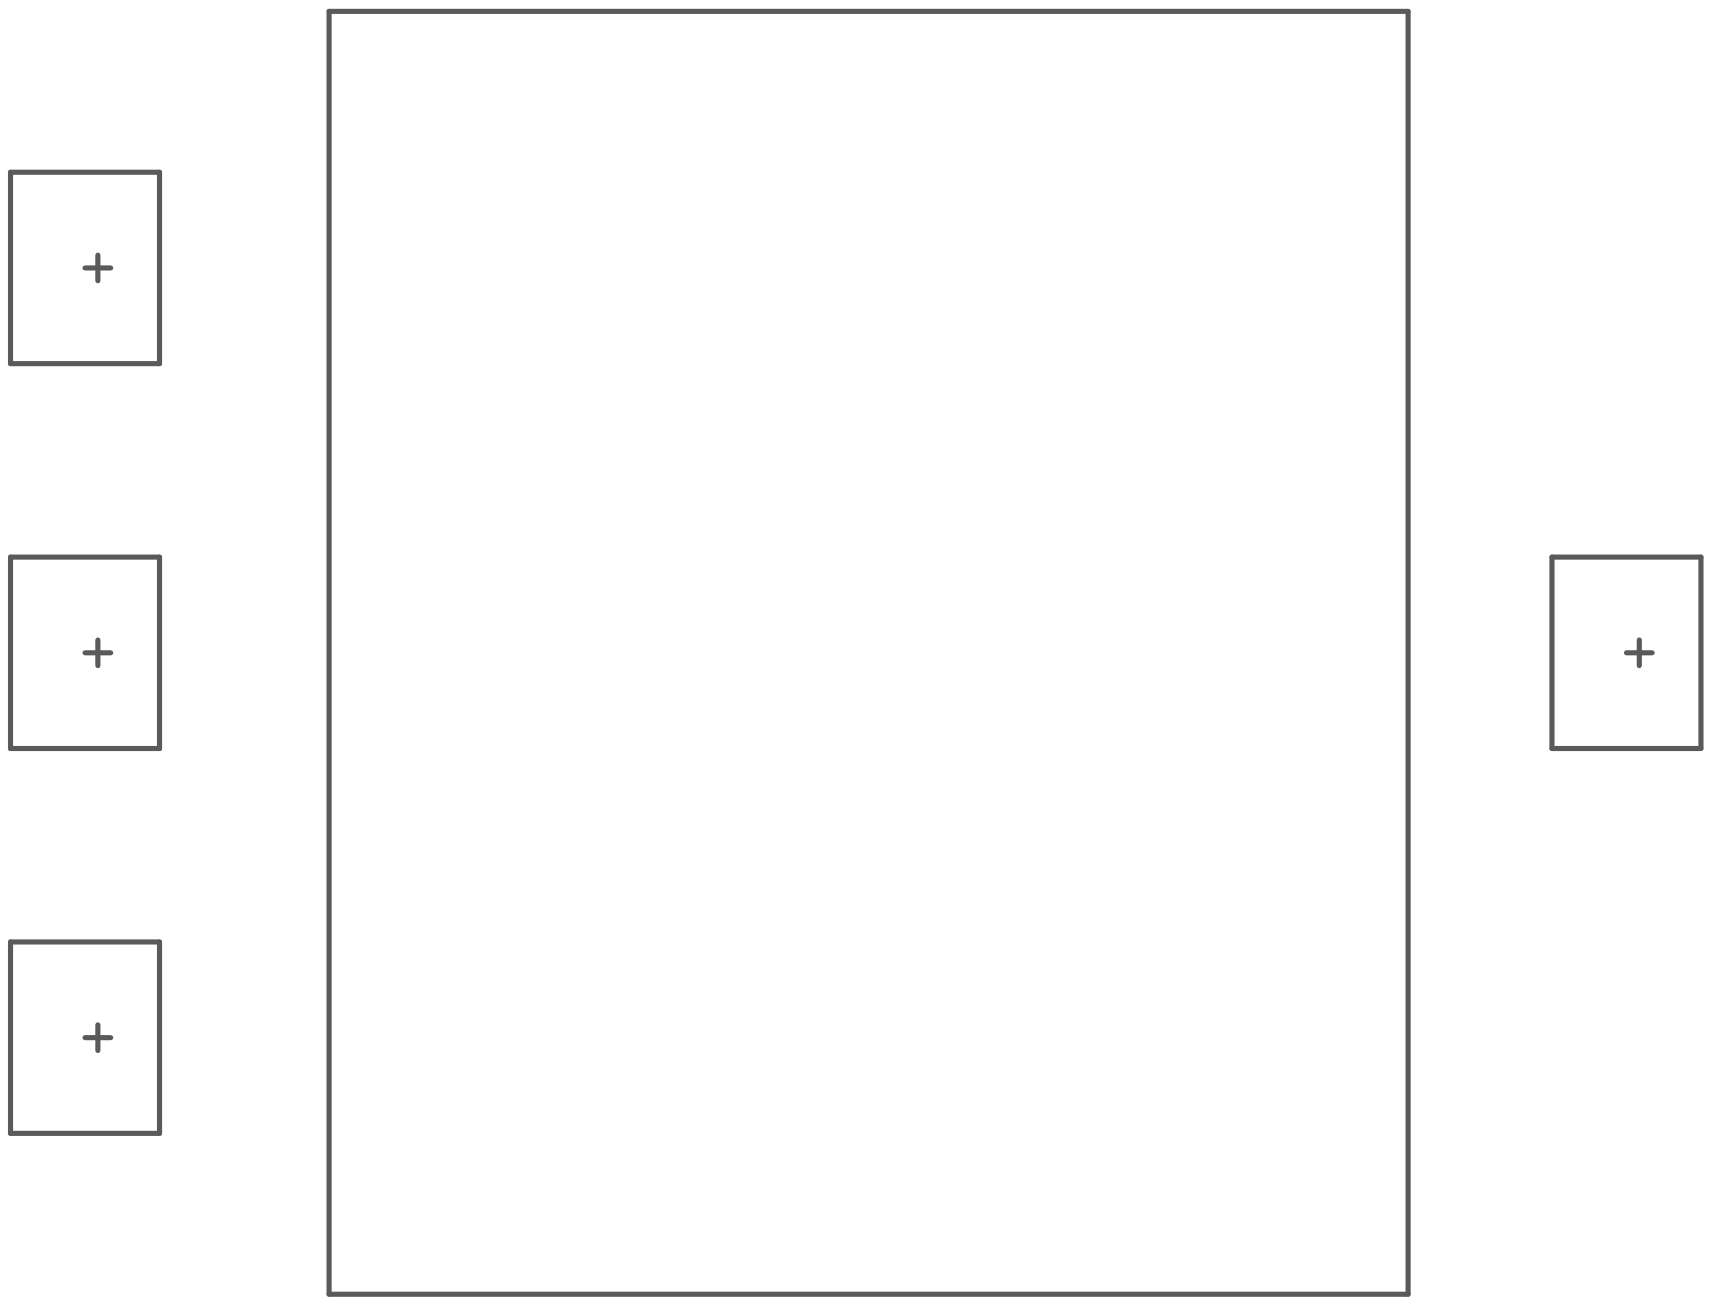
[picture p226: page 3]

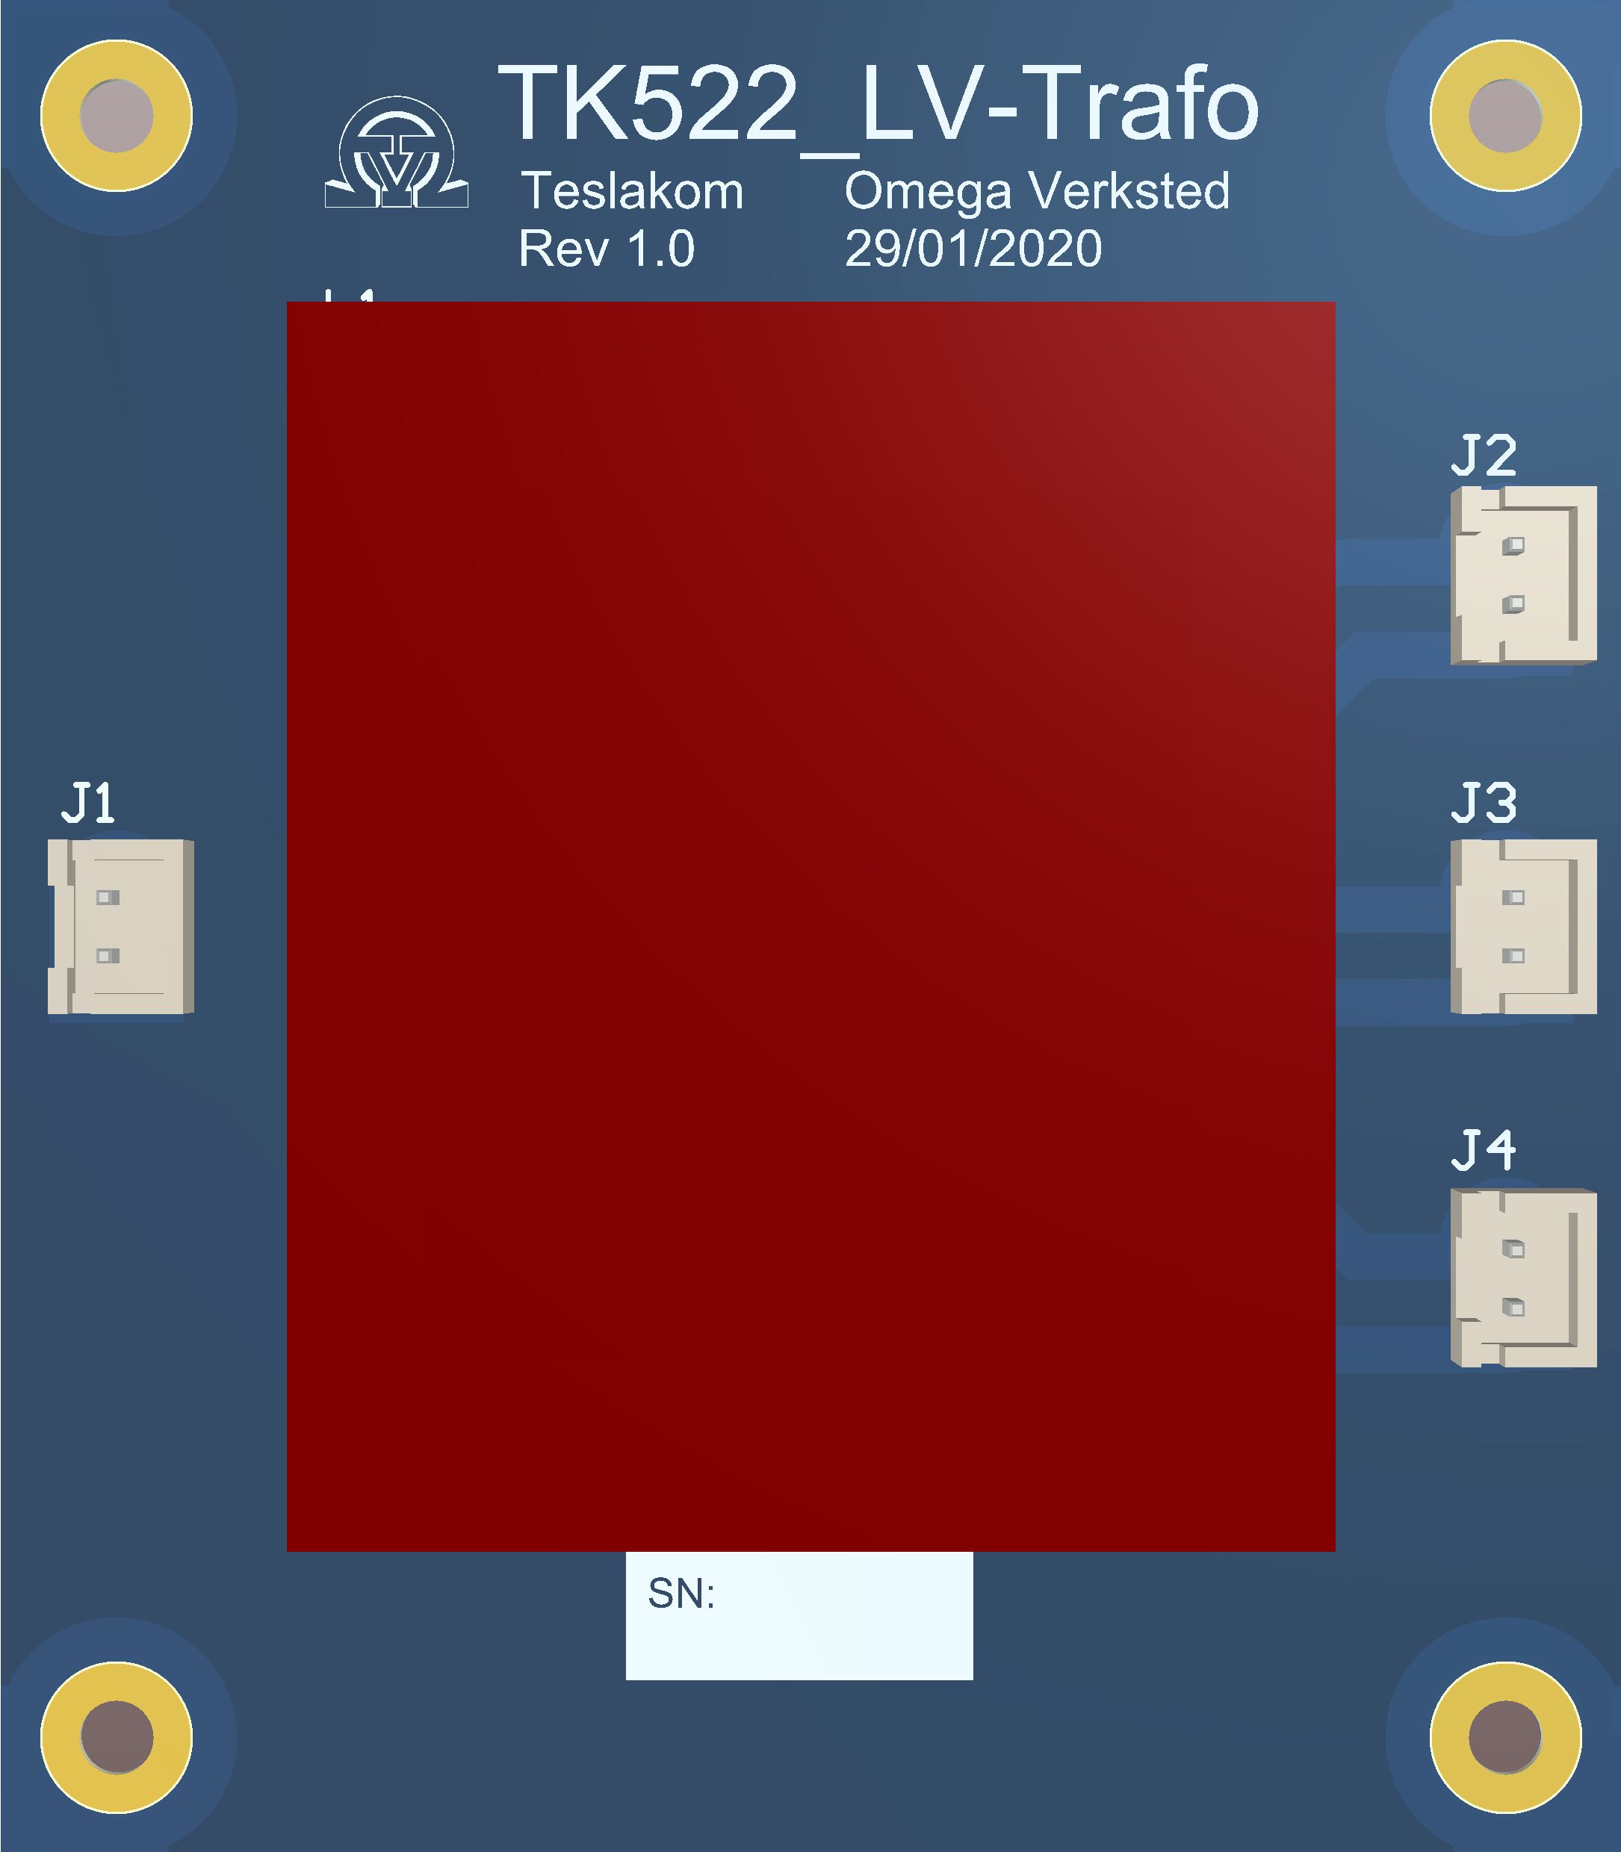
[picture p227: page 4]

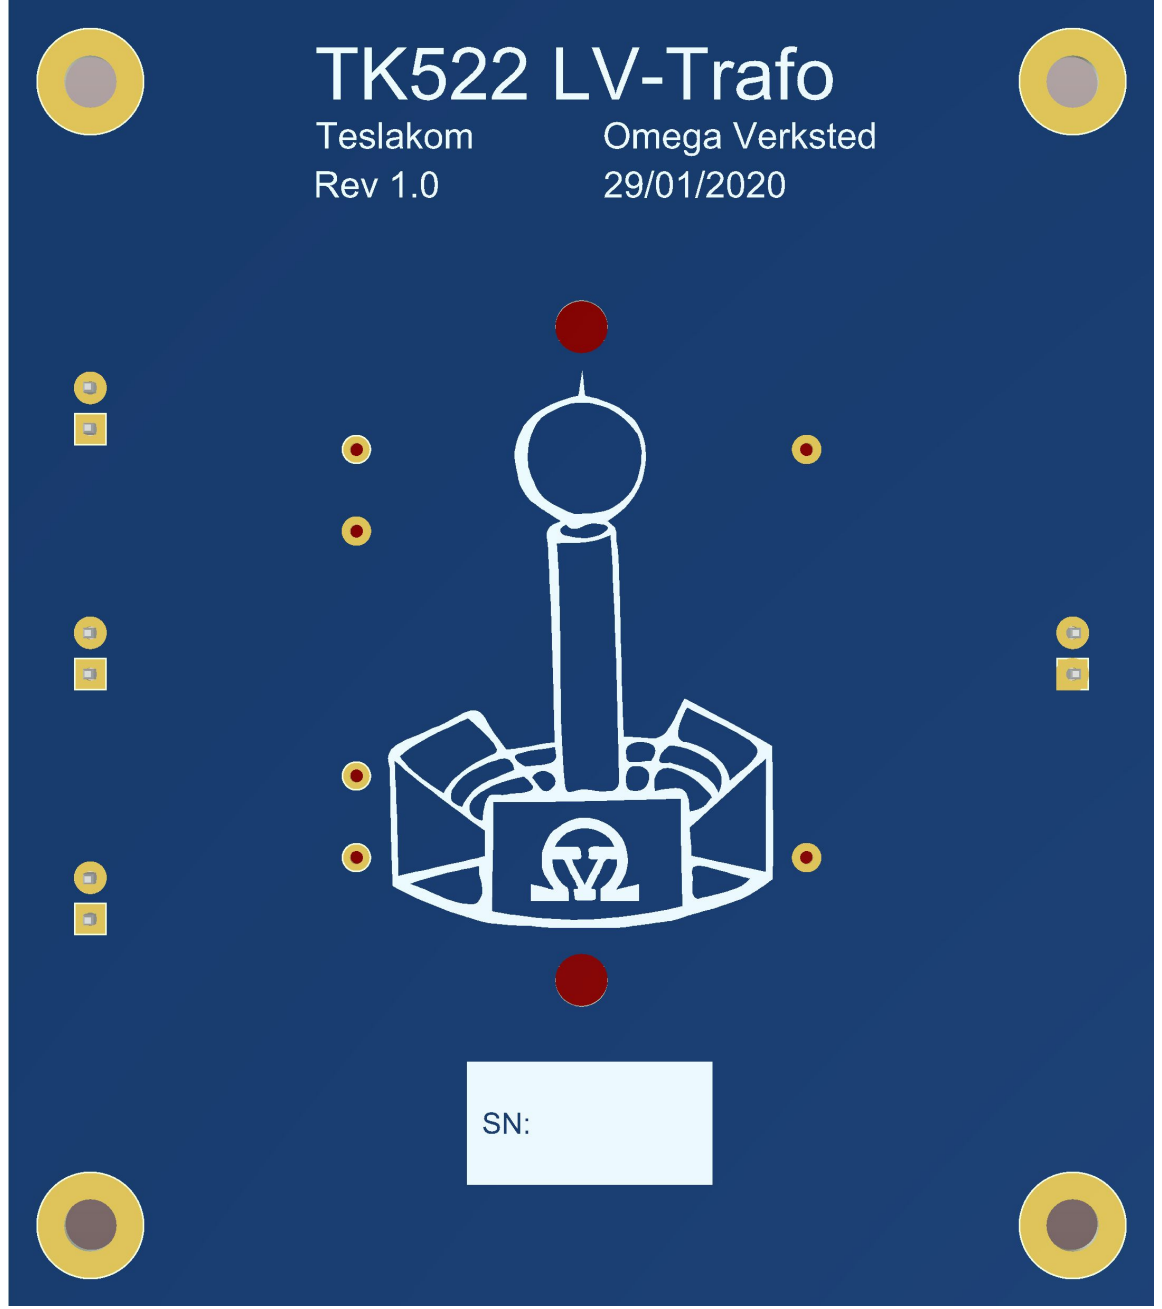
[picture p228: page 5]

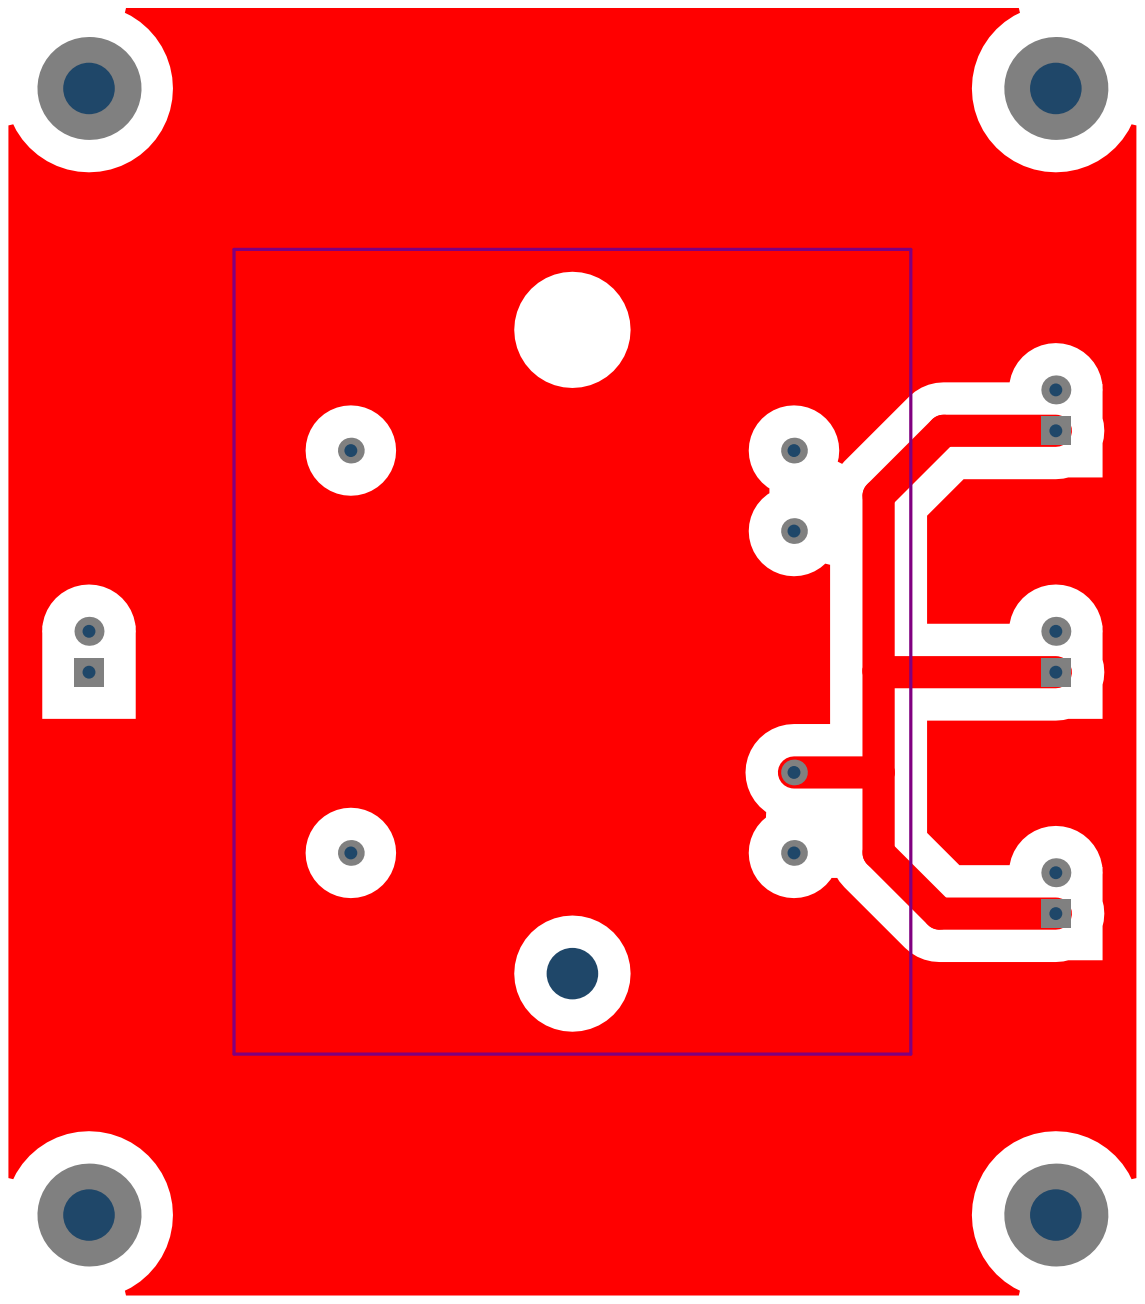
[picture p229: page 6]

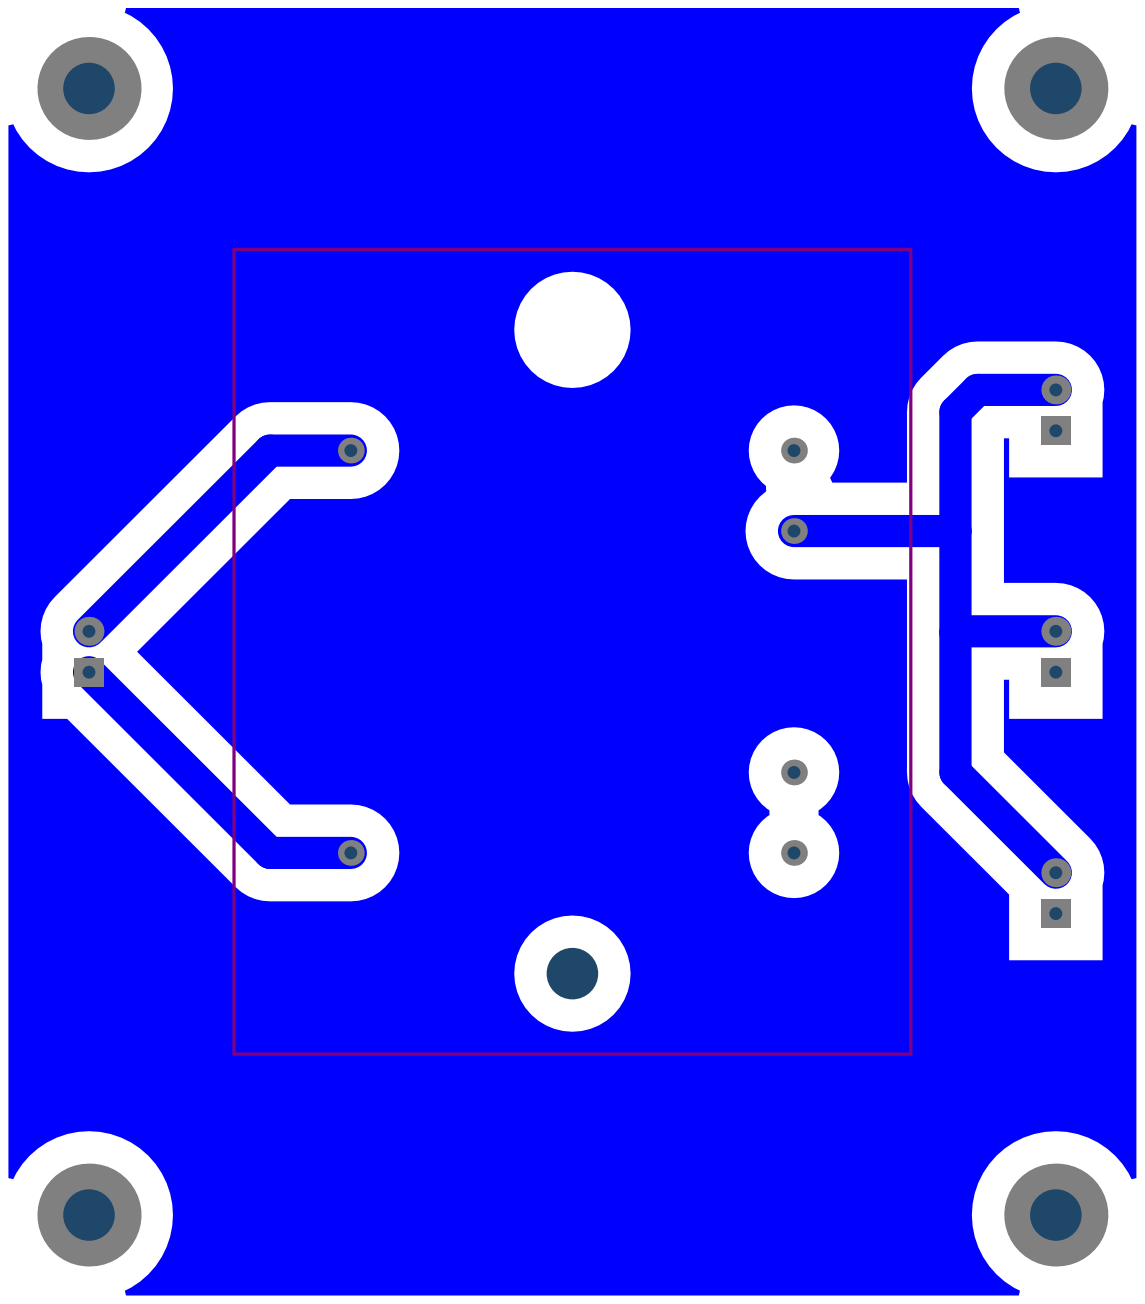
[picture p230: page 7]

LibRef | Designator

2227 | J1
2227 | J2
2227 | J3
2227 | J4
44268 Myrra Transformer | L1
