Cable89/tesla-driver/05_Hardware/TK500_Driver/TK532_Kondensatorkort/Project Outputs/TK532_Kondensatorkort.PDF

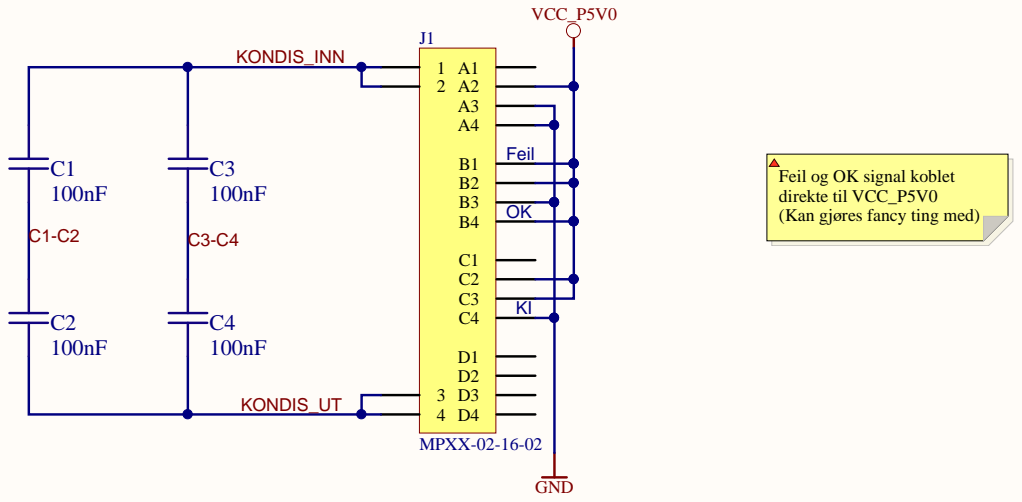
[picture p231: page 1]

Feil og OK signal koblet
direkte til VC
(Kan gj

res fancy ting med)

Title: TK532 Kondensatorkort

Size: A3 | Revision: 1.1 | Author : Øystein Smith

Date: | Sheet * of * | Omega Verksted

29/01/2020 C:\Git\tesla-driver\05_Hardware\TK500_Driver\TK532_Kondensatorkort\TK532_Kondensatorkort.SchDoc

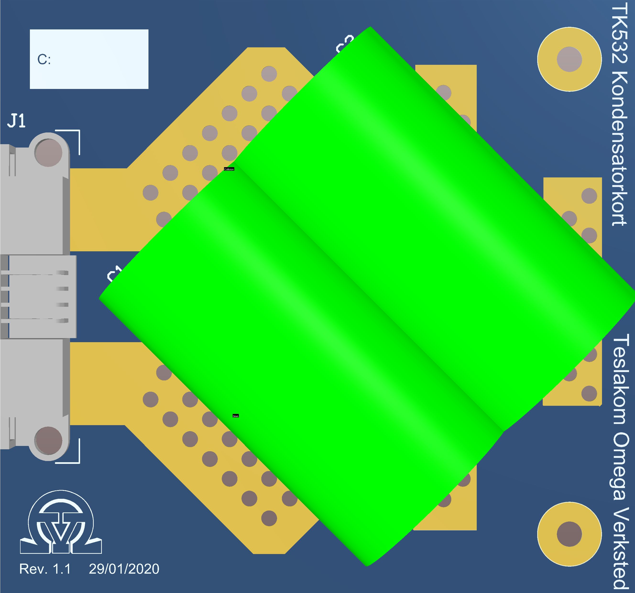
[picture p232: page 4]

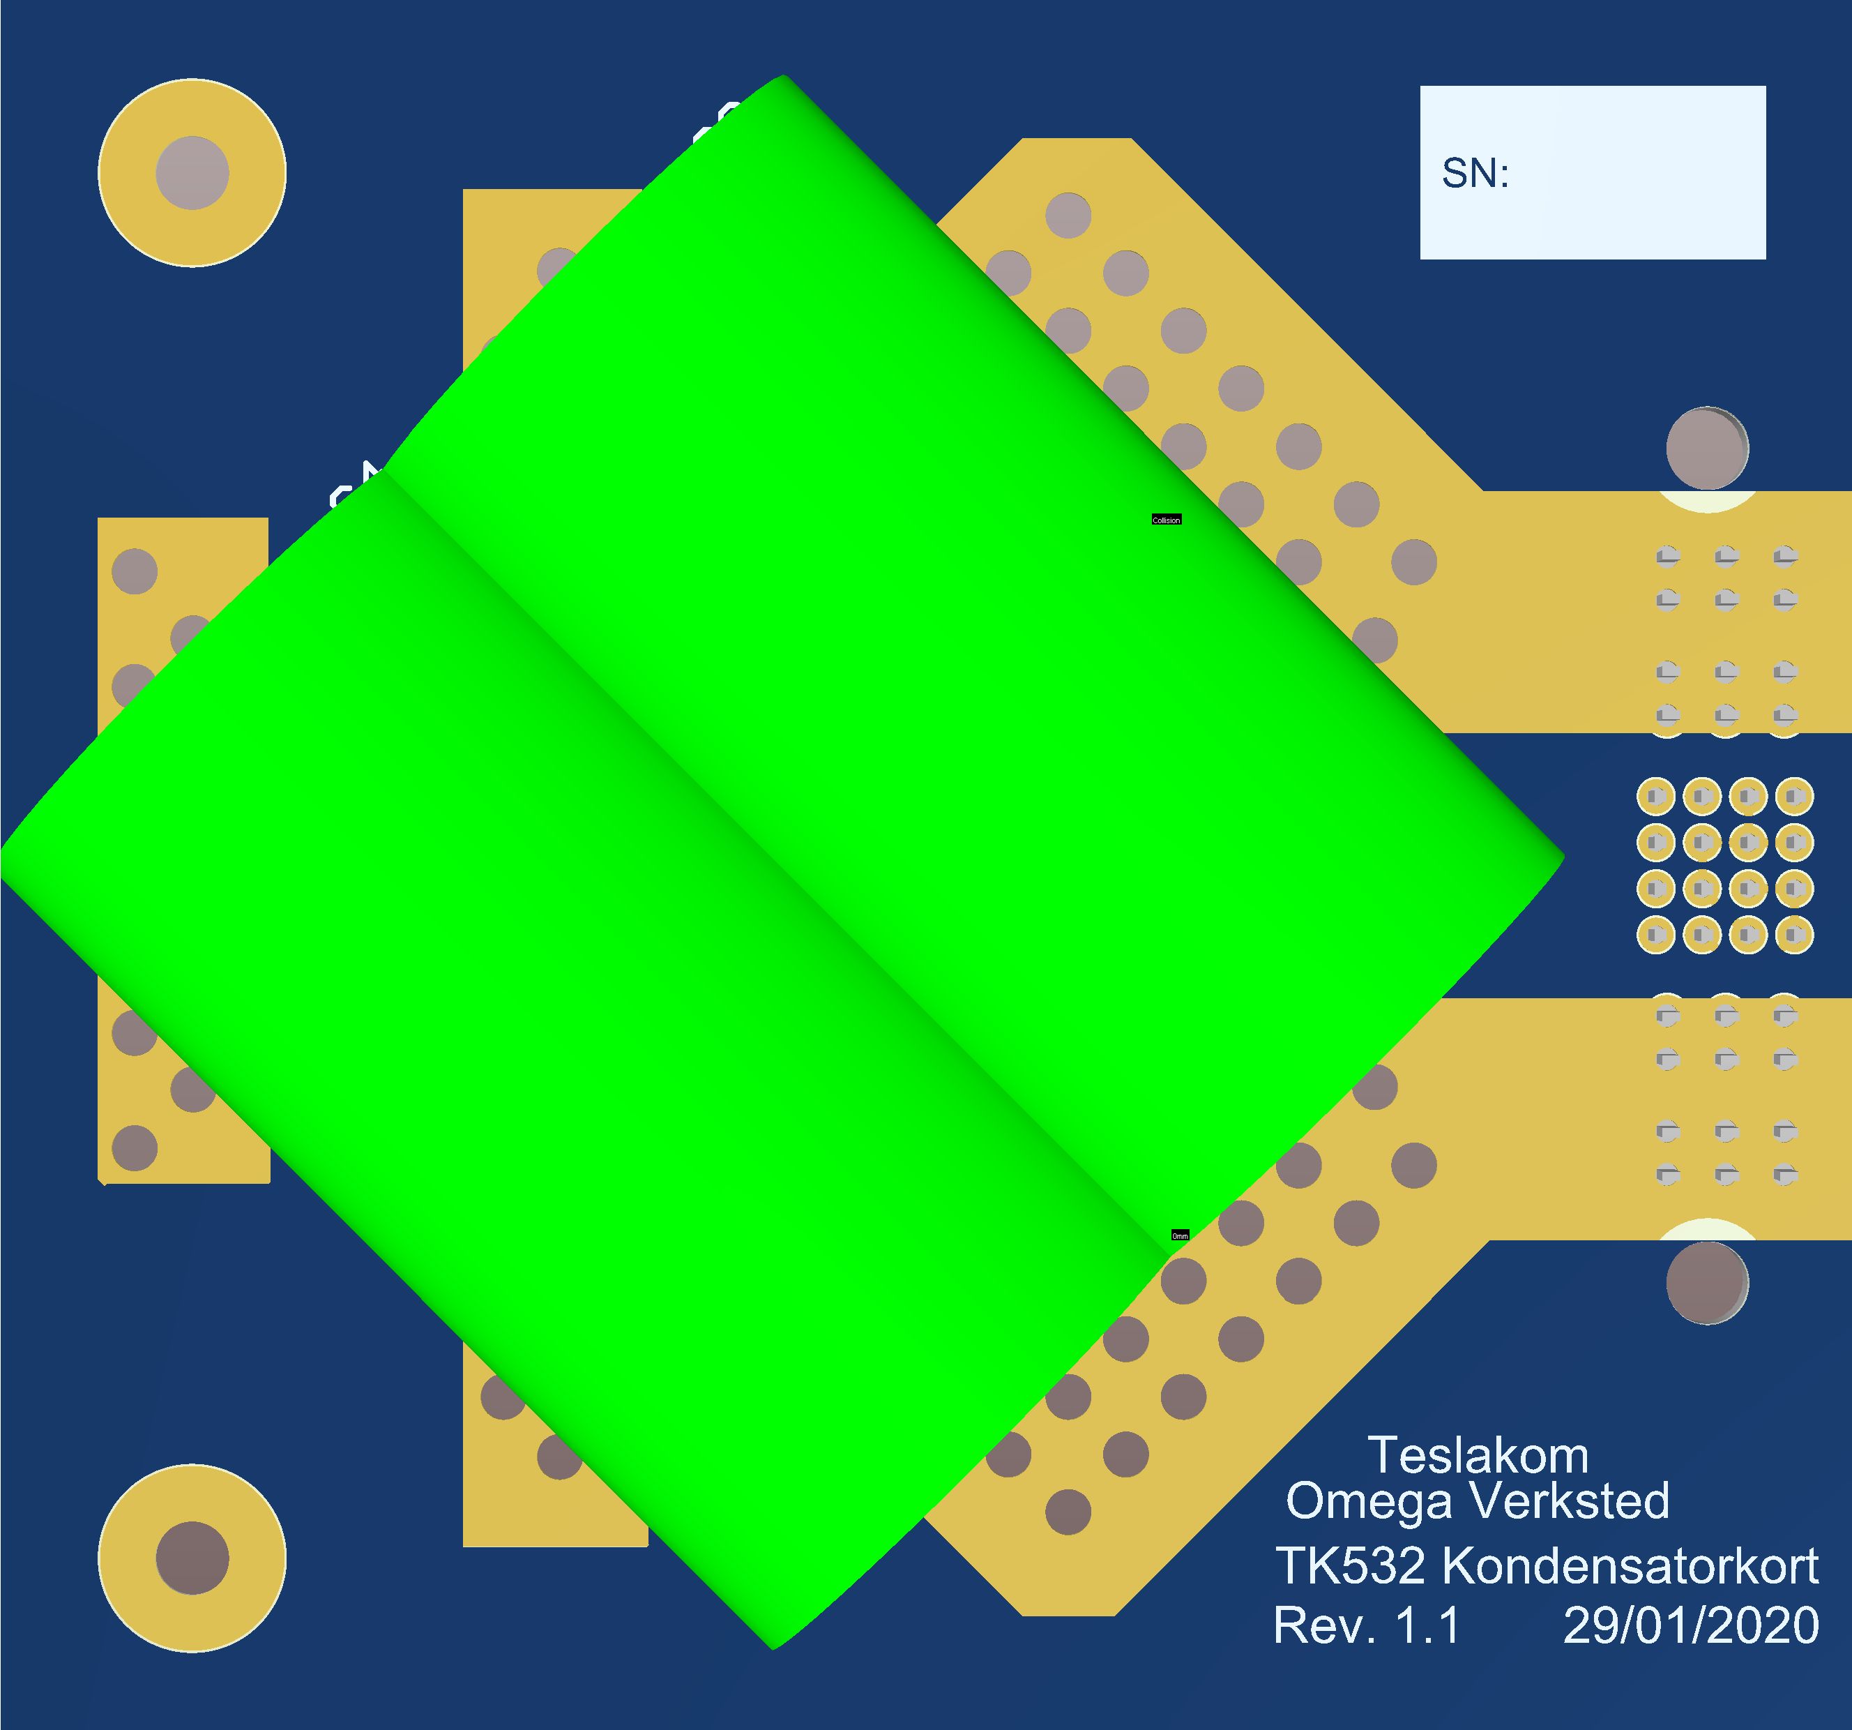
[picture p233: page 5]

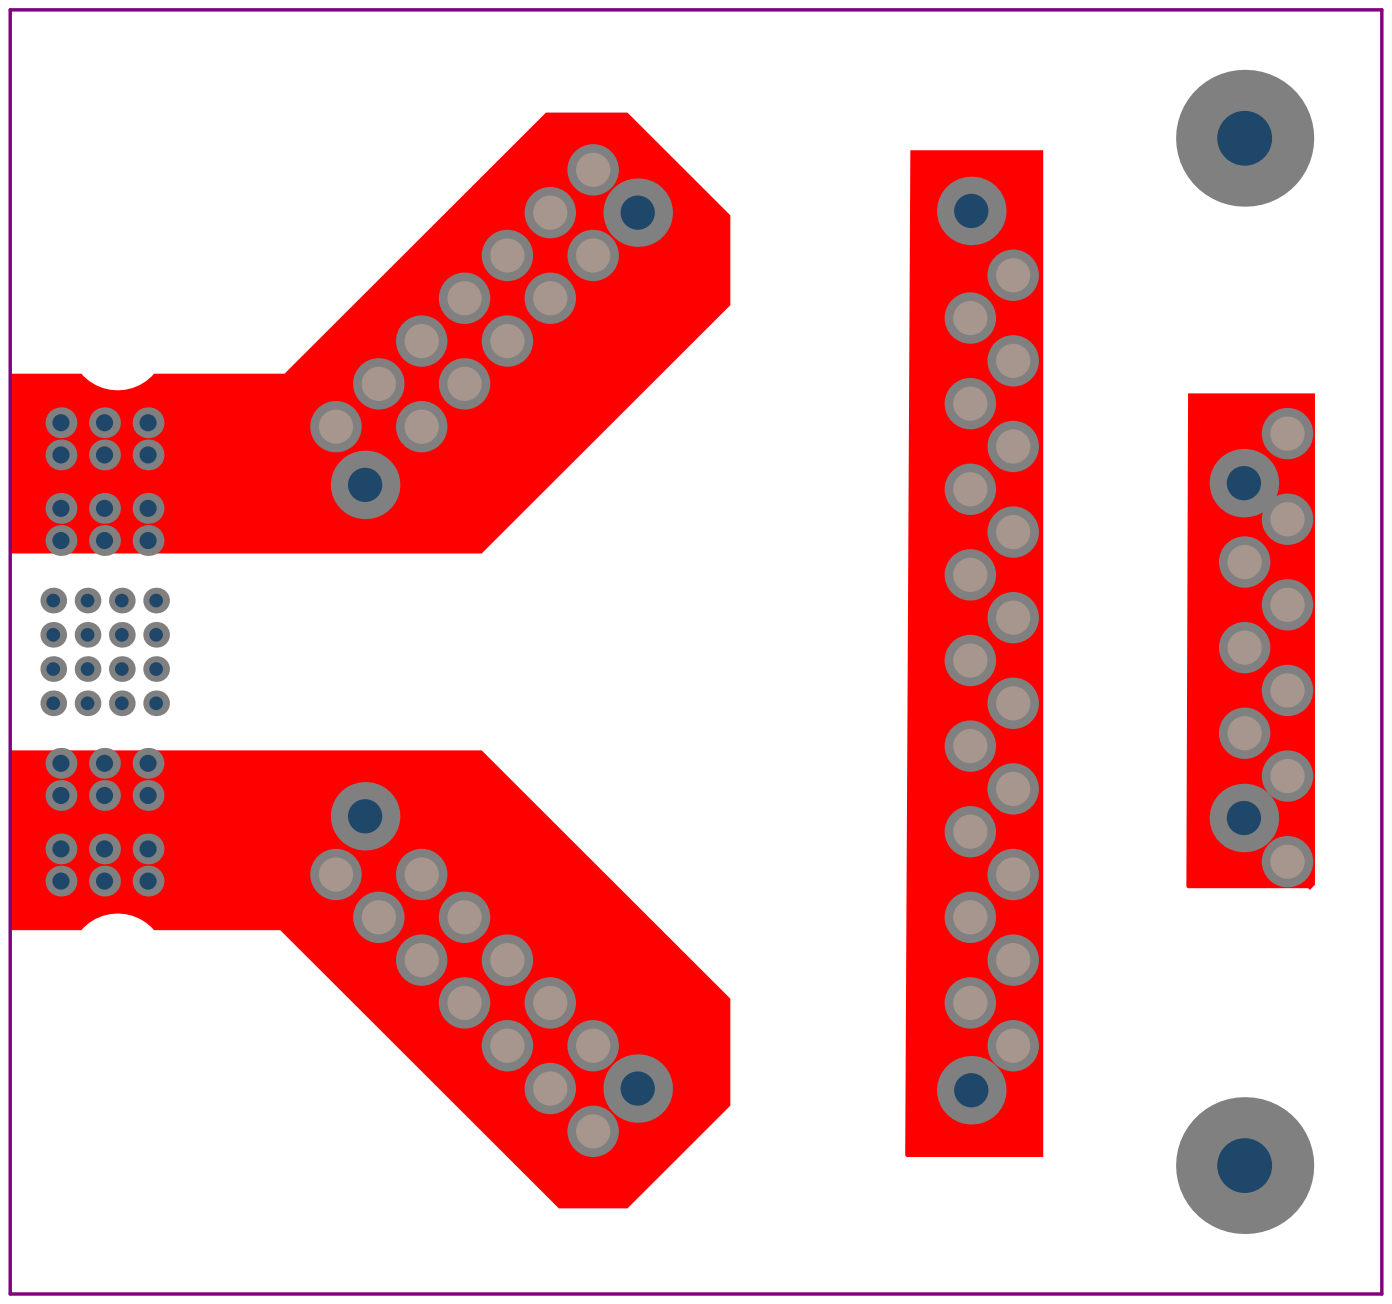
[picture p234: page 6]

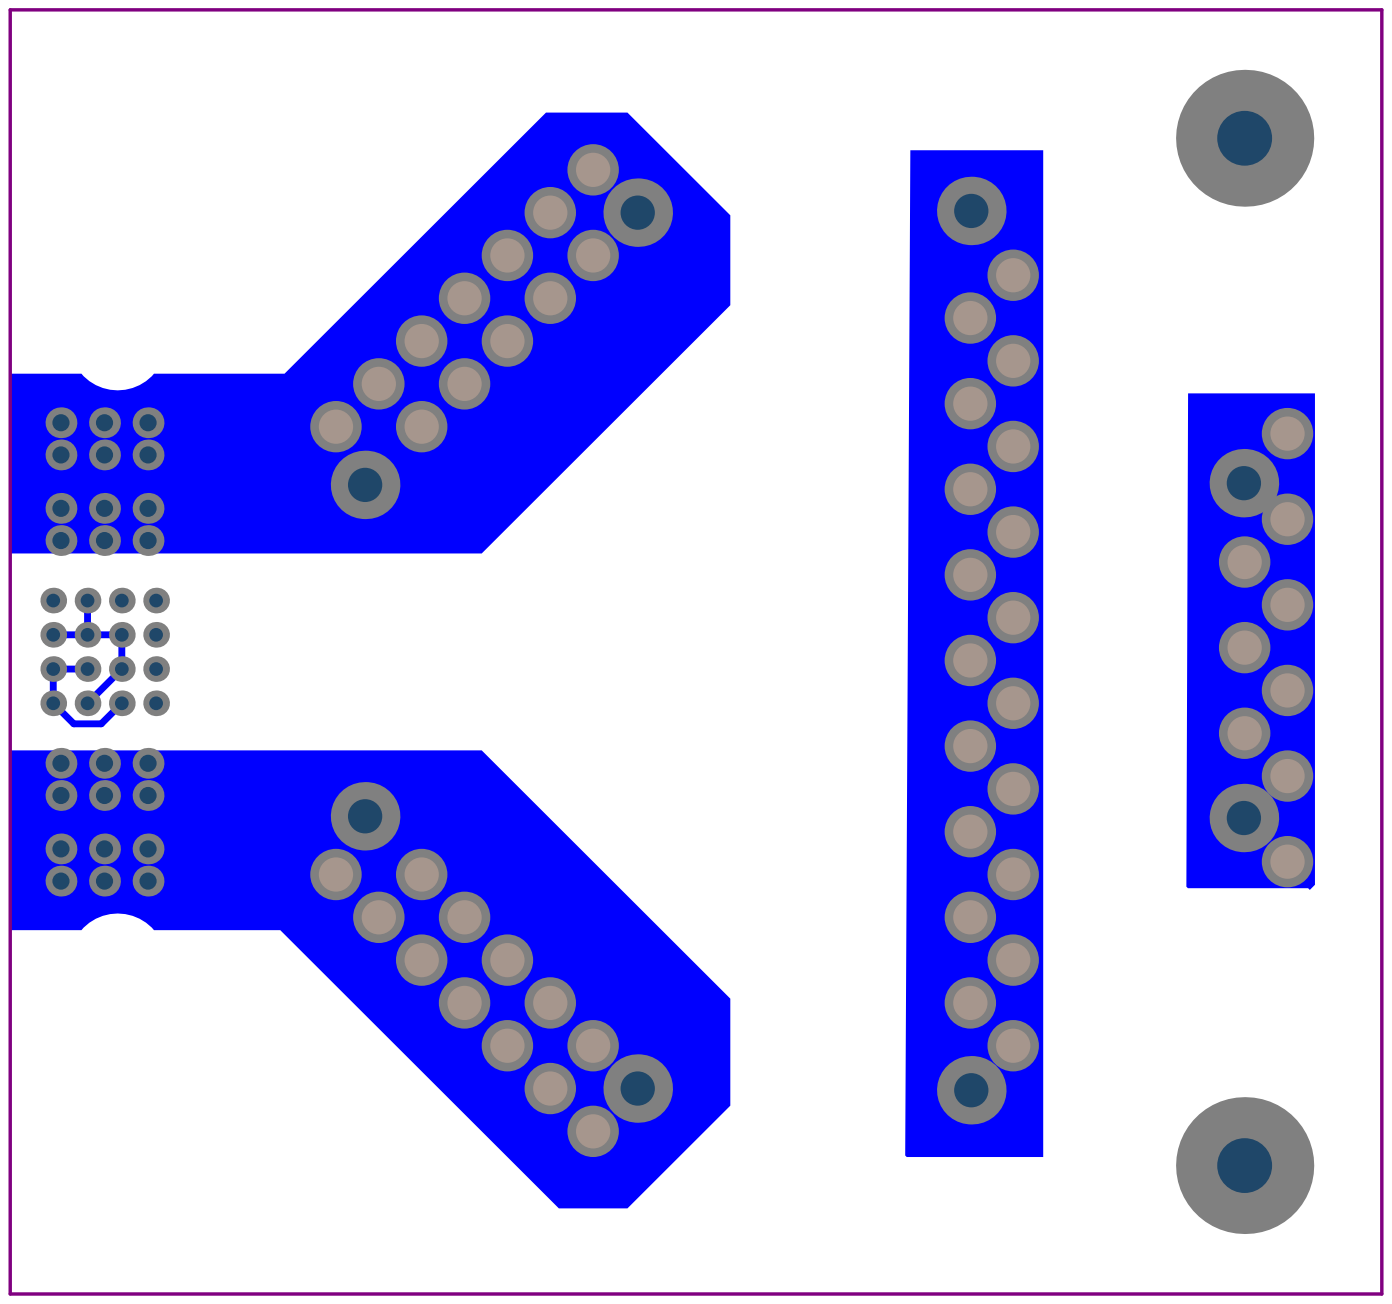
[picture p235: page 7]

LibRef | Designator

2393 | J1
4153 | C1
4153 | C2
4153 | C3
4153 | C4
