Cable89/tesla-driver/05_Hardware/TK100_Tonegenerator/TK103_Multiplexer/Project Outputs/TK103_Multiplexer.PDF

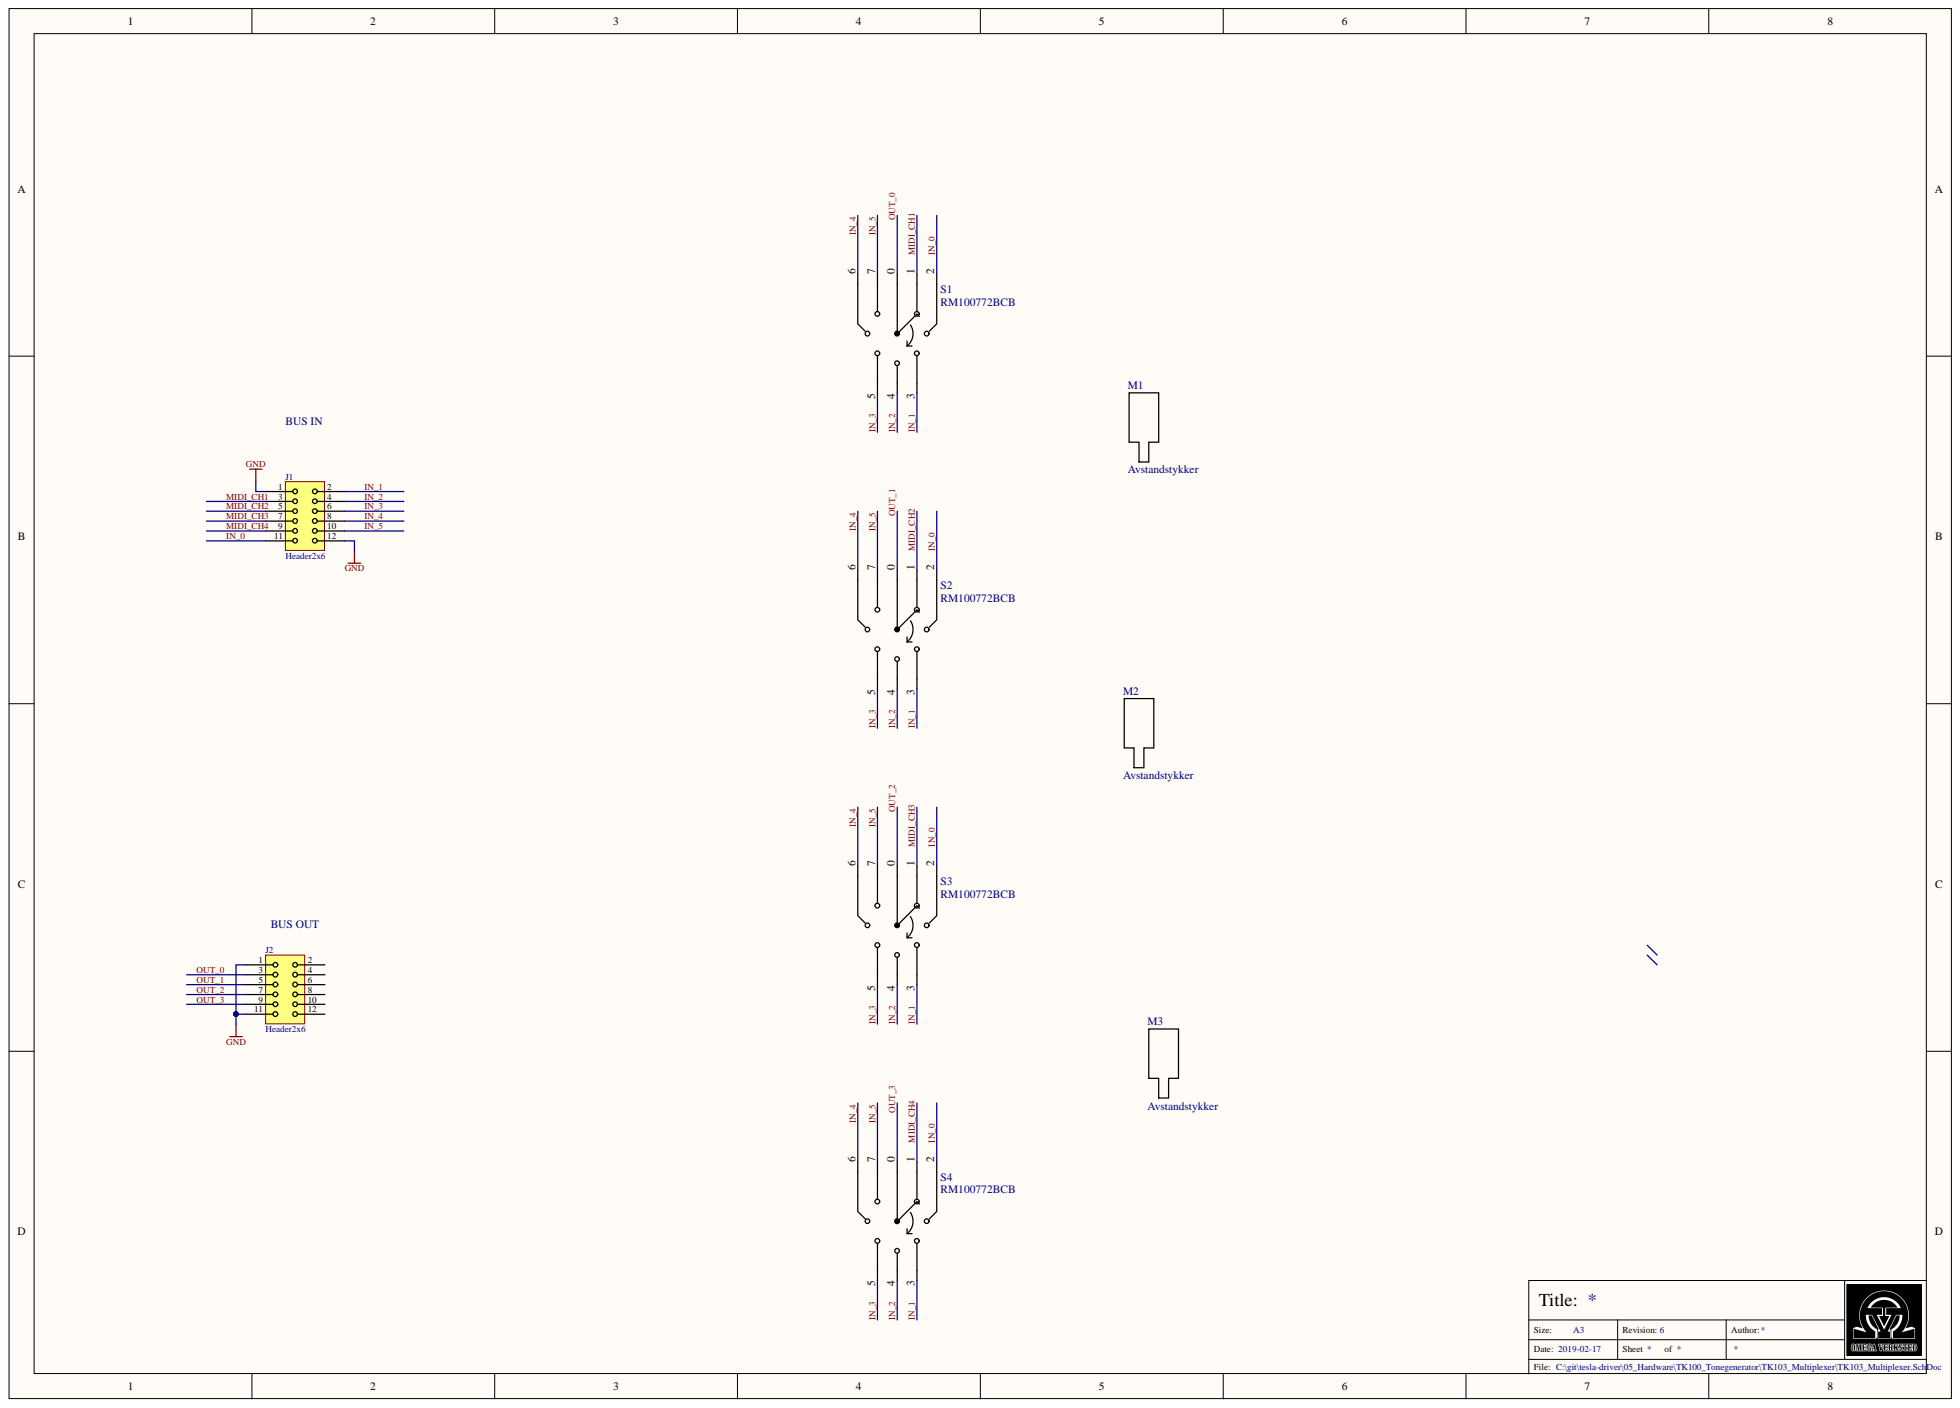
[picture p236: page 1]

Title: *

Size: A3 | Revision: 6 | Author: *

Date: 2019-02-17 | Sheet * of * | *

C:\git\tesla-driver\05_Hardware\TK100_Tonegenerator\TK103_Multiplexer\TK103_Multiplexer.SchDoc

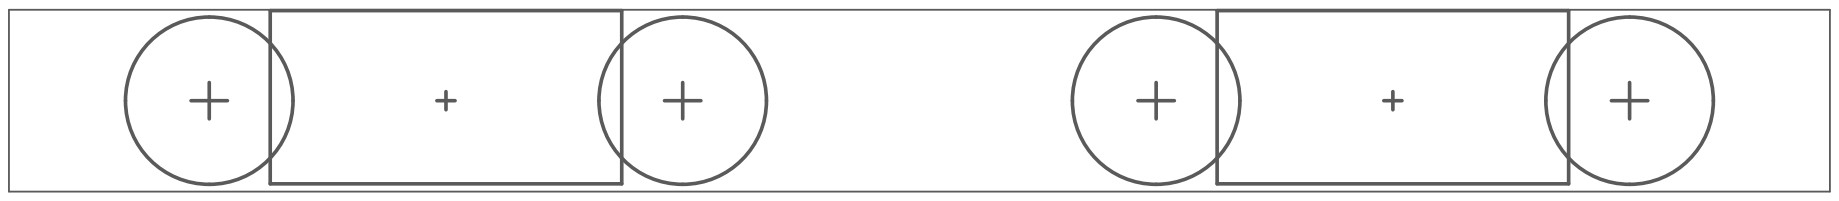
[picture p237: page 2]

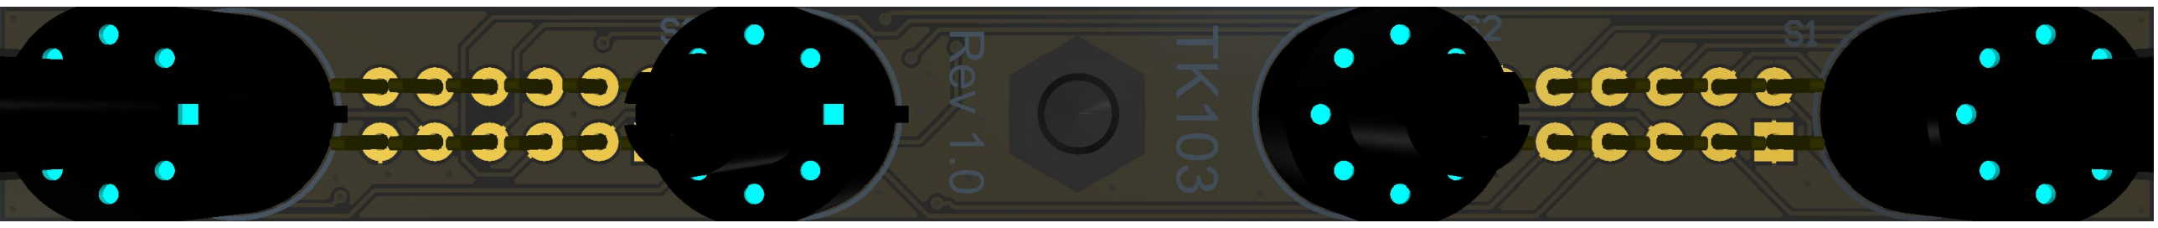
[picture p238: figure]

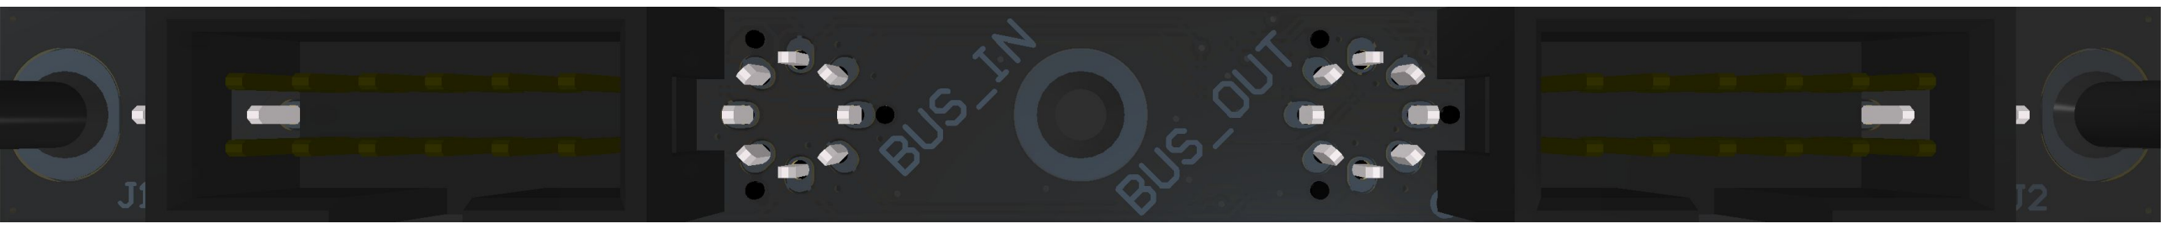
[picture p239: figure]
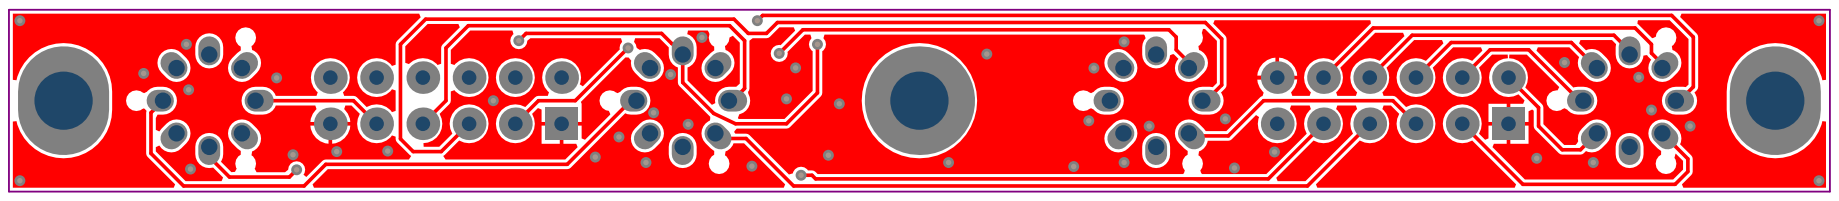
[picture p240: page 6]

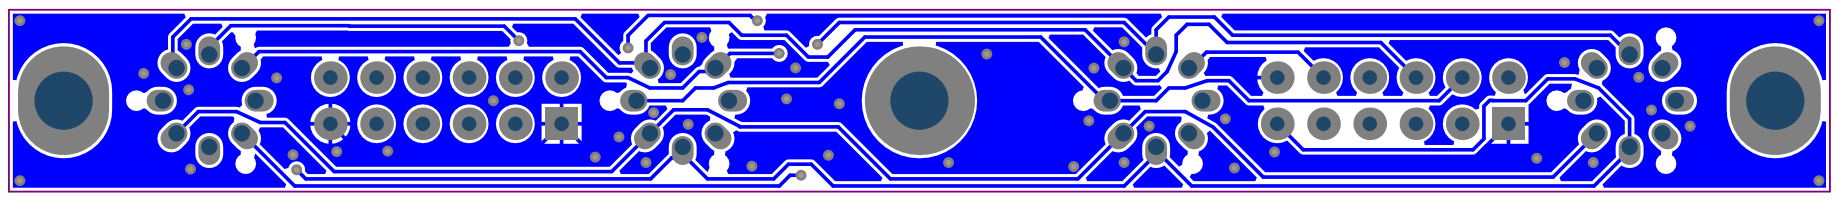
[picture p241: page 7]

Designator | Quantitynavn | | beskrivelse | leverandor | leverandor_varenr | antall
M1, M2, M3 | 3 | Avstandstykker | | Farnell | 1733429 | 300
J1, J2 | 2 | Header 2X6 Shrouded Hader Shrouded
S1, S2, S3, S4 | 4 | RM100772BCB | | DigiKey | CKN10691-ND
