Cable89/tesla-driver/05_Hardware/TK100_Tonegenerator/TK104_Pulsbegrenser_Eurorack/Project Outputs/TK104_Pulsbegrenser_Eurorack_frontpanel.PDF

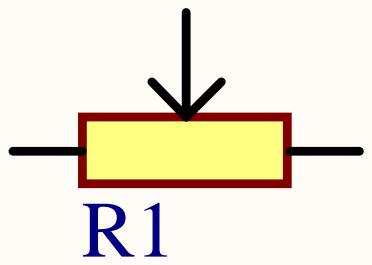
[picture p242: page 1]

Title: *

Size: A3 | Revision: 6 | Author: *

Date: 2019-02-17 | Sheet * of * | *

C:\git\tesla-driver\05_Hardware\TK100_Tonegenerator\TK104_Pulsbegrenser_Eurorack\TK104_Pulsbegrenser_Eurorack_frontpanel.SchDoc

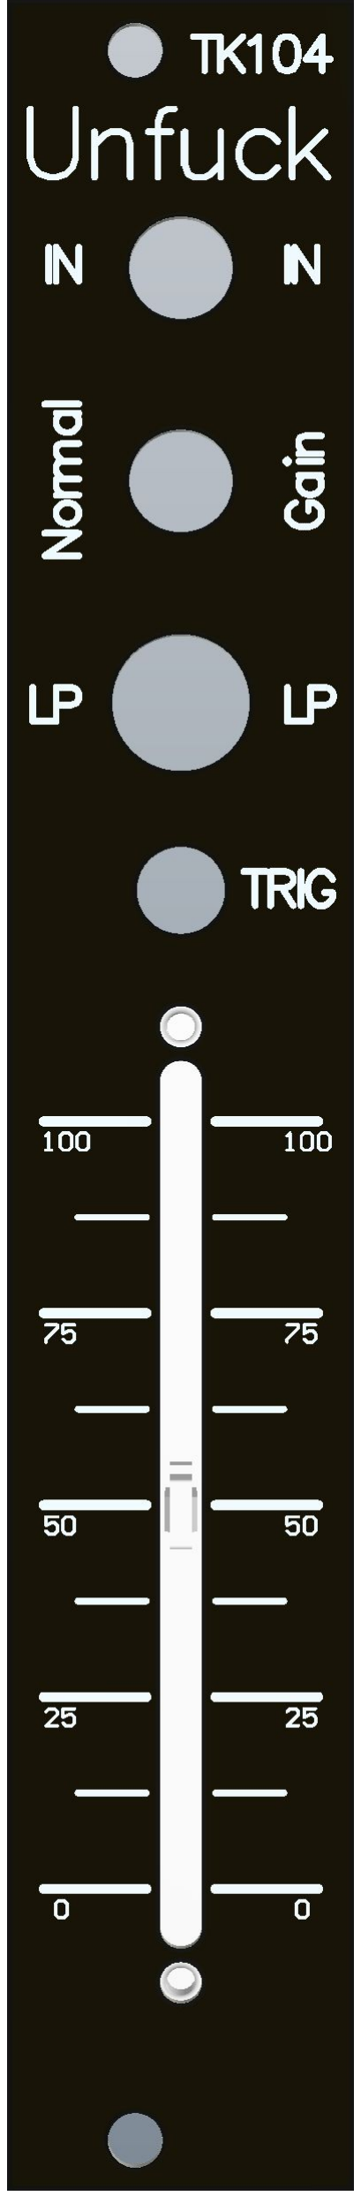
[picture p243: figure]

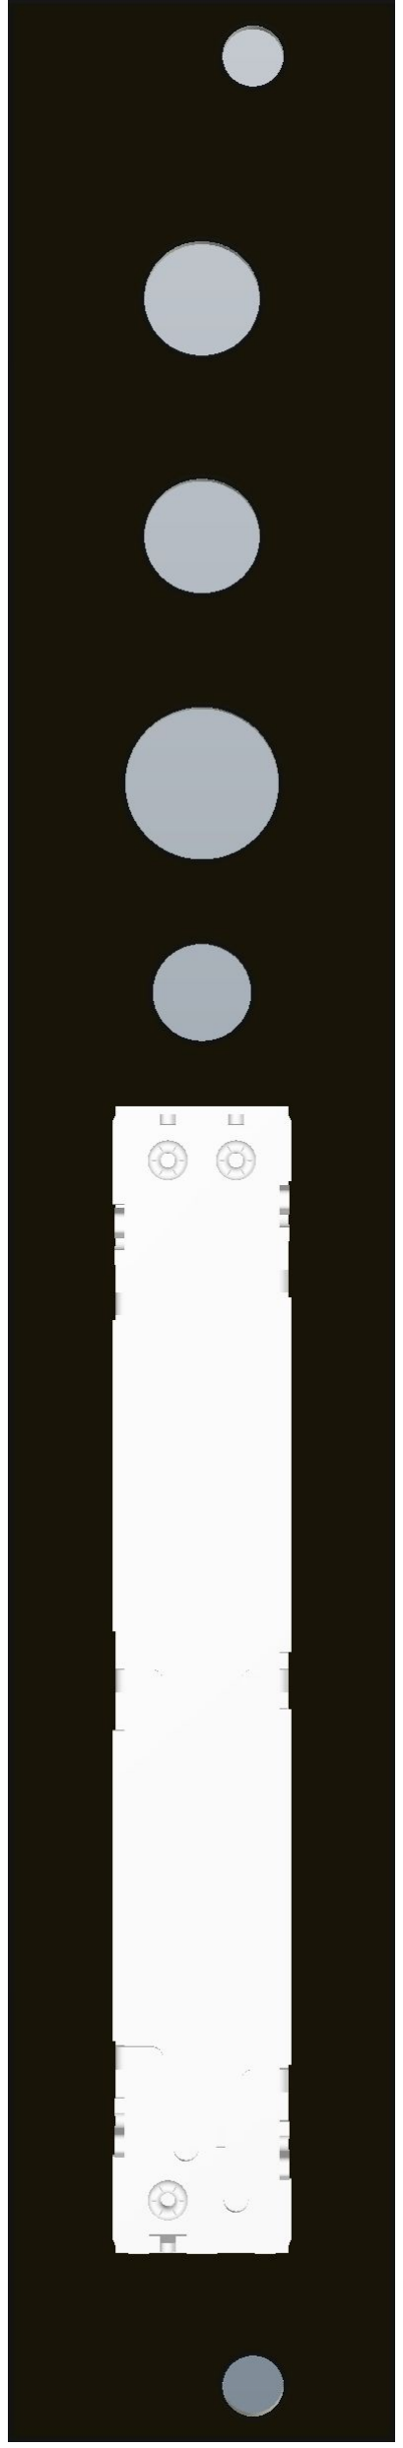
[picture p244: figure]
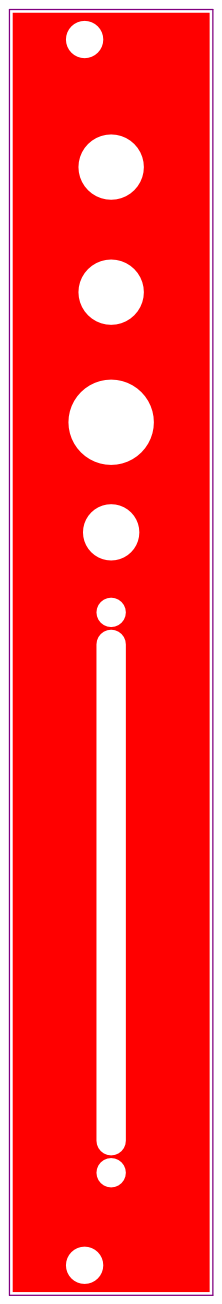
[picture p245: page 6]

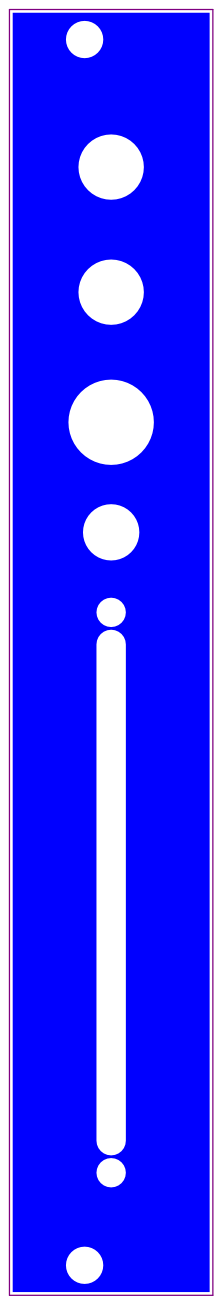
[picture p246: page 7]

Designator | Quantitynavn | beskrivelse | leverandor | leverandor_varenr | antall
R1 | 1
