Cable89/tesla-driver/05_Hardware/TK500_Driver/TK511_Blindkort/Project Outputs/TK511_Blindkort.PDF

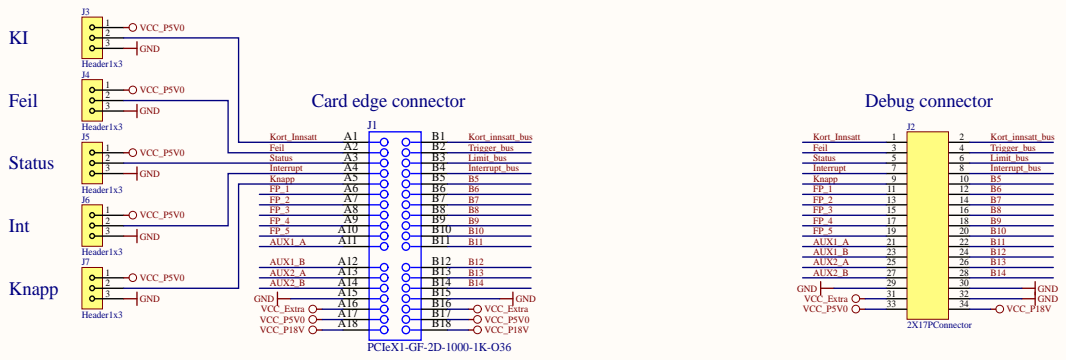
[picture p247: page 1]

Title: TK511 Blindkort

Size: A3 | Revision: 5 20 0 | Author : Øystein Smith

Date: 23.01.2019 C:\git\tesla-driver\05_Hardware\TK500_Driver\TK511_Blindkort\TK511_Blindkort.SchDoc | Sheet of | Omega Verksted

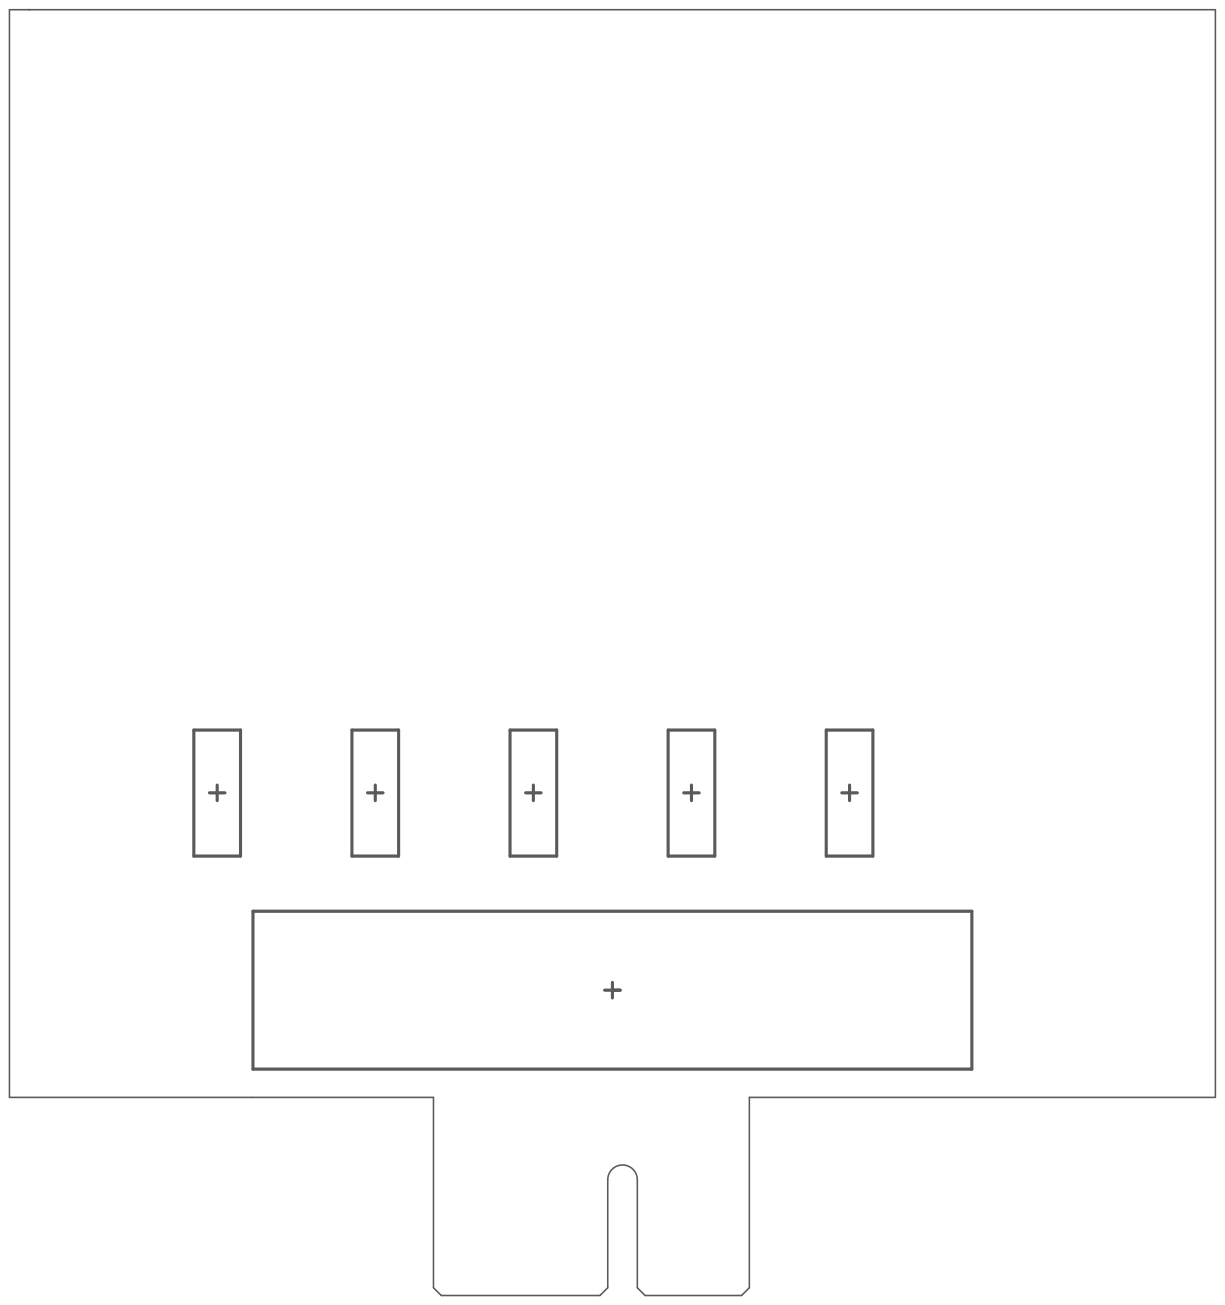
[picture p248: page 2]

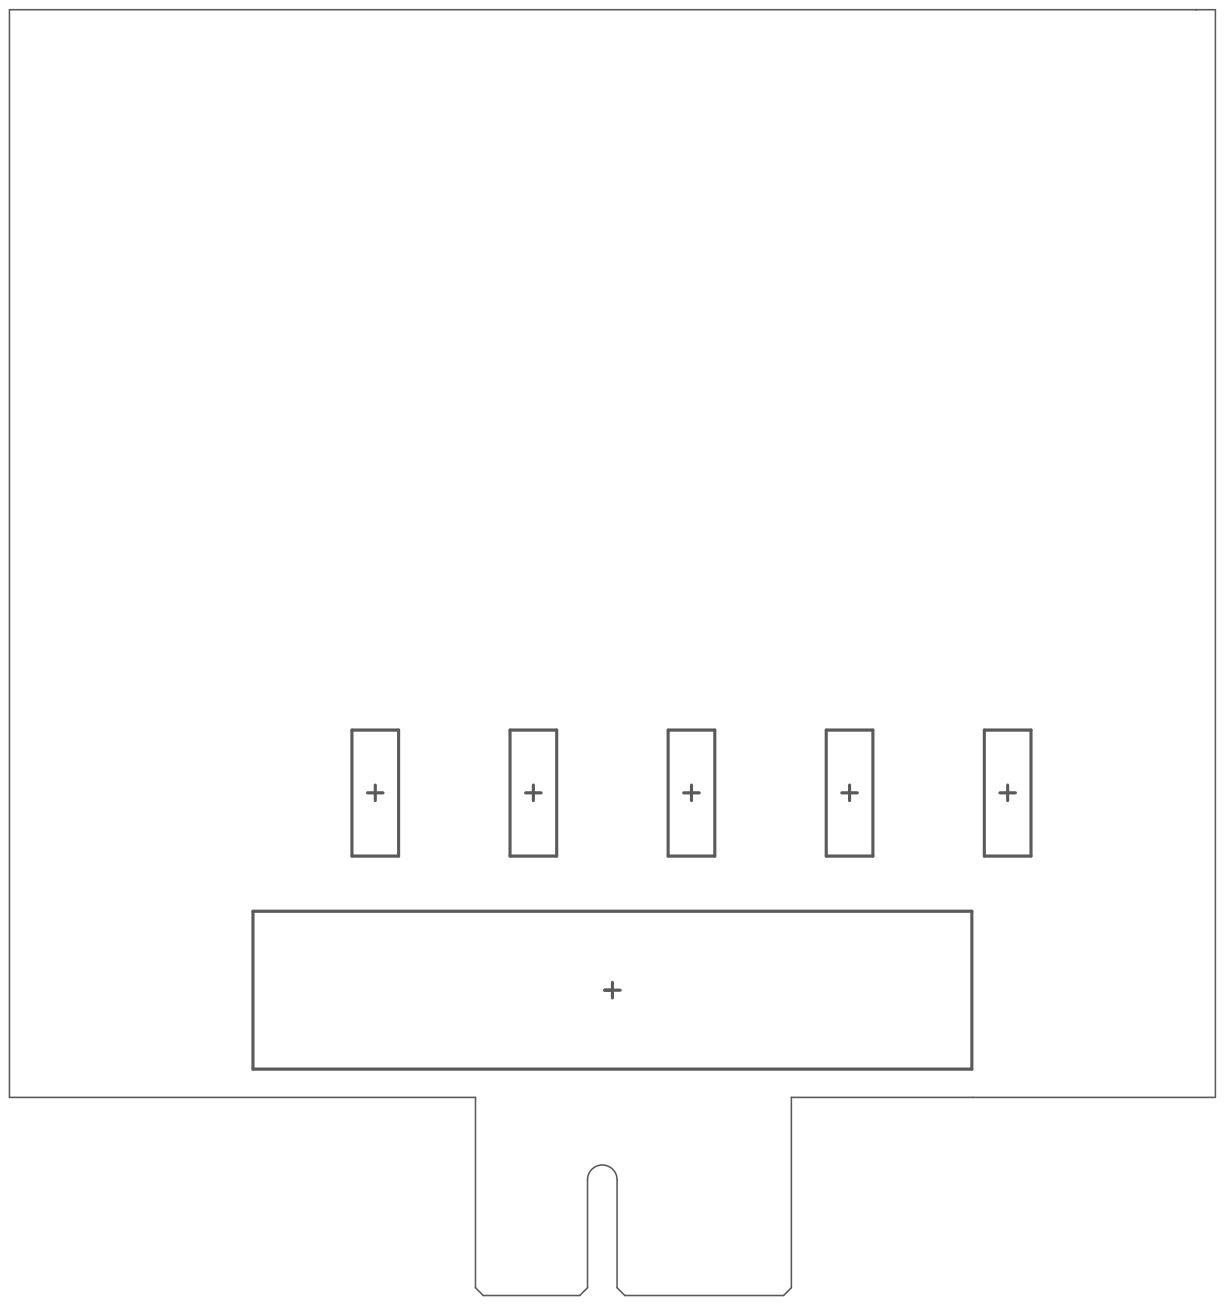
[picture p249: page 3]

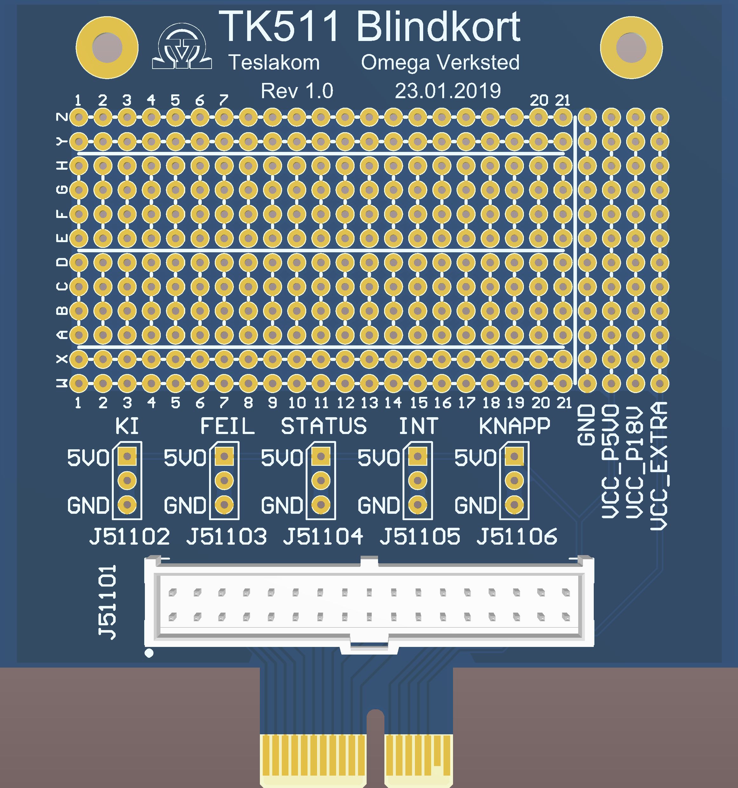
[picture p250: page 4]

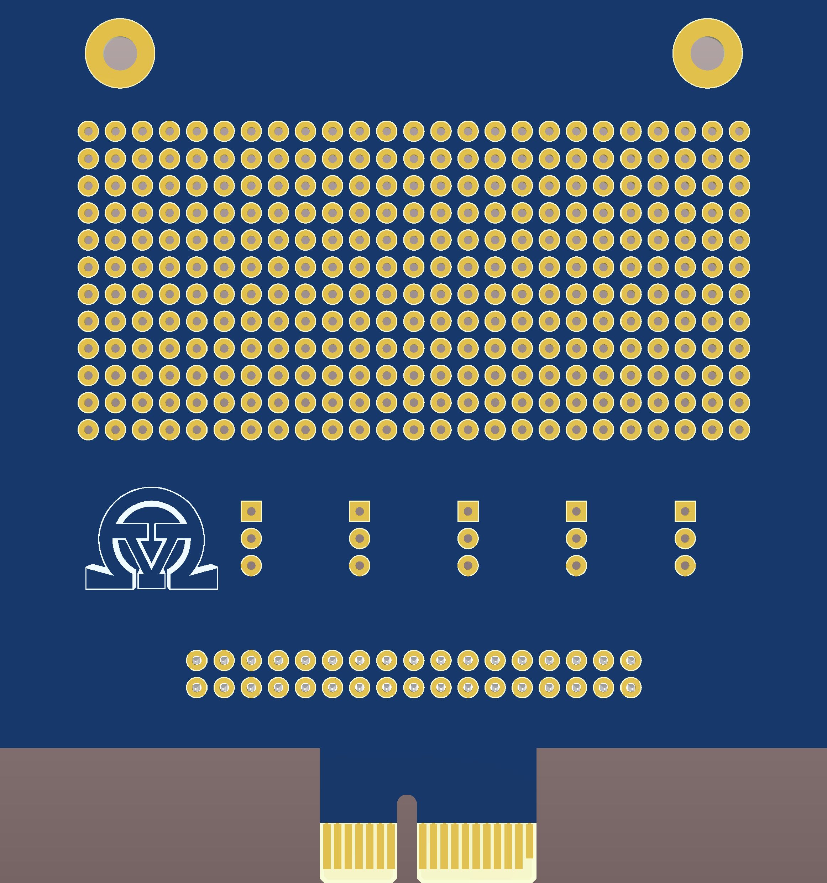
[picture p251: page 5]

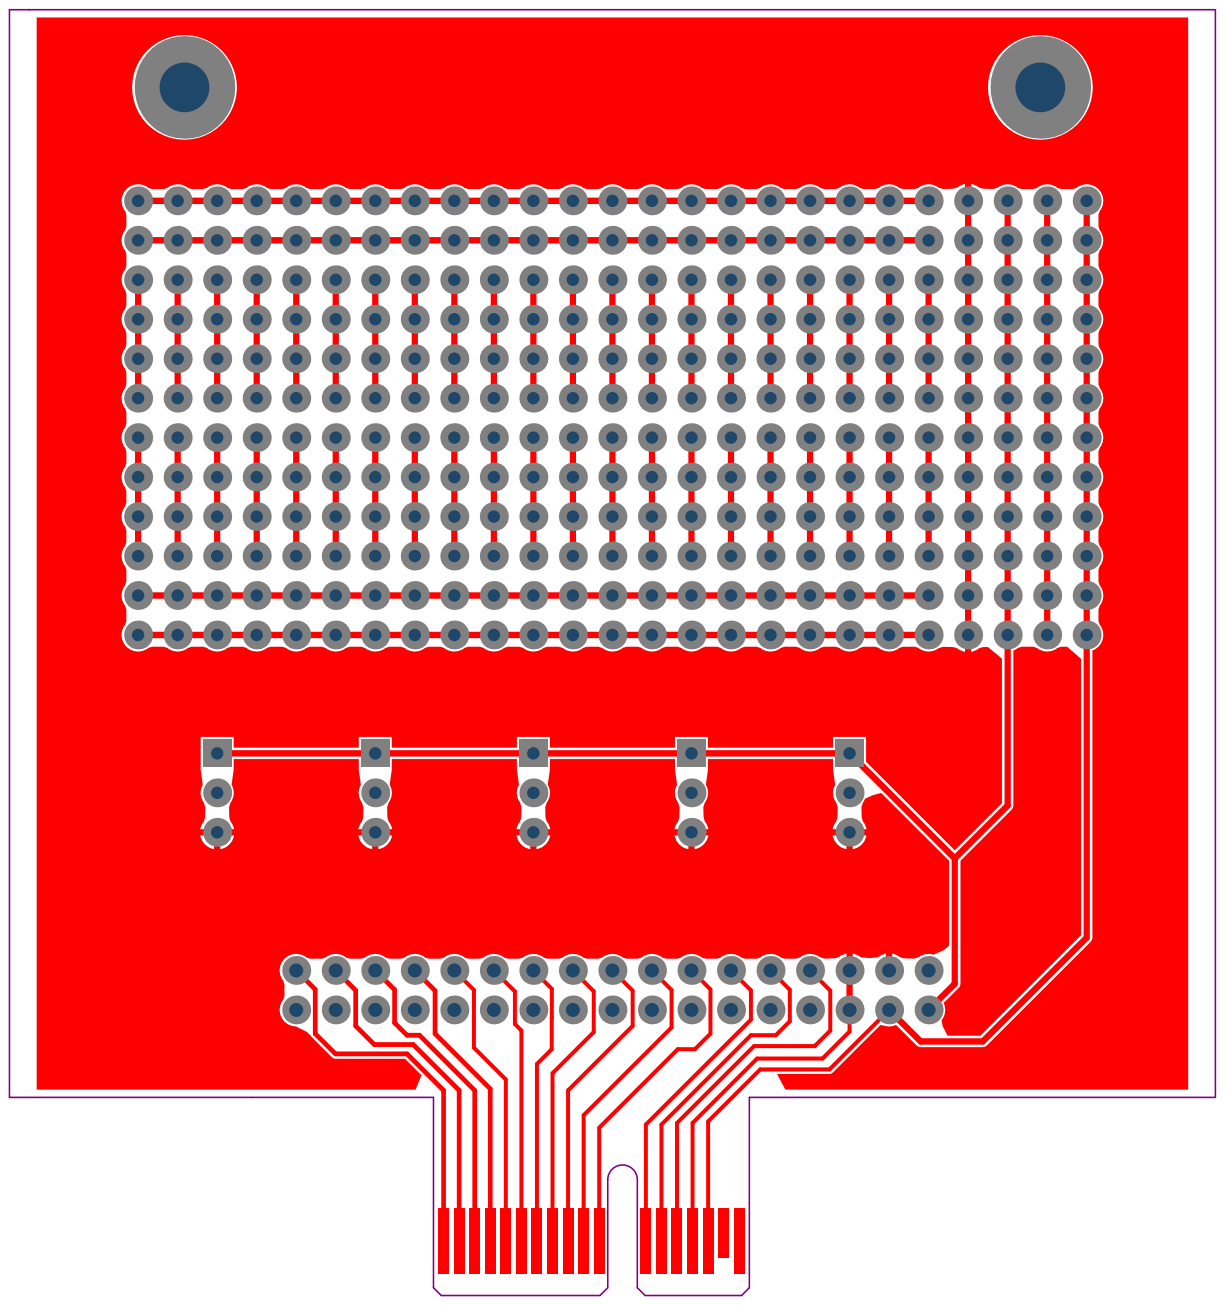
[picture p252: page 6]

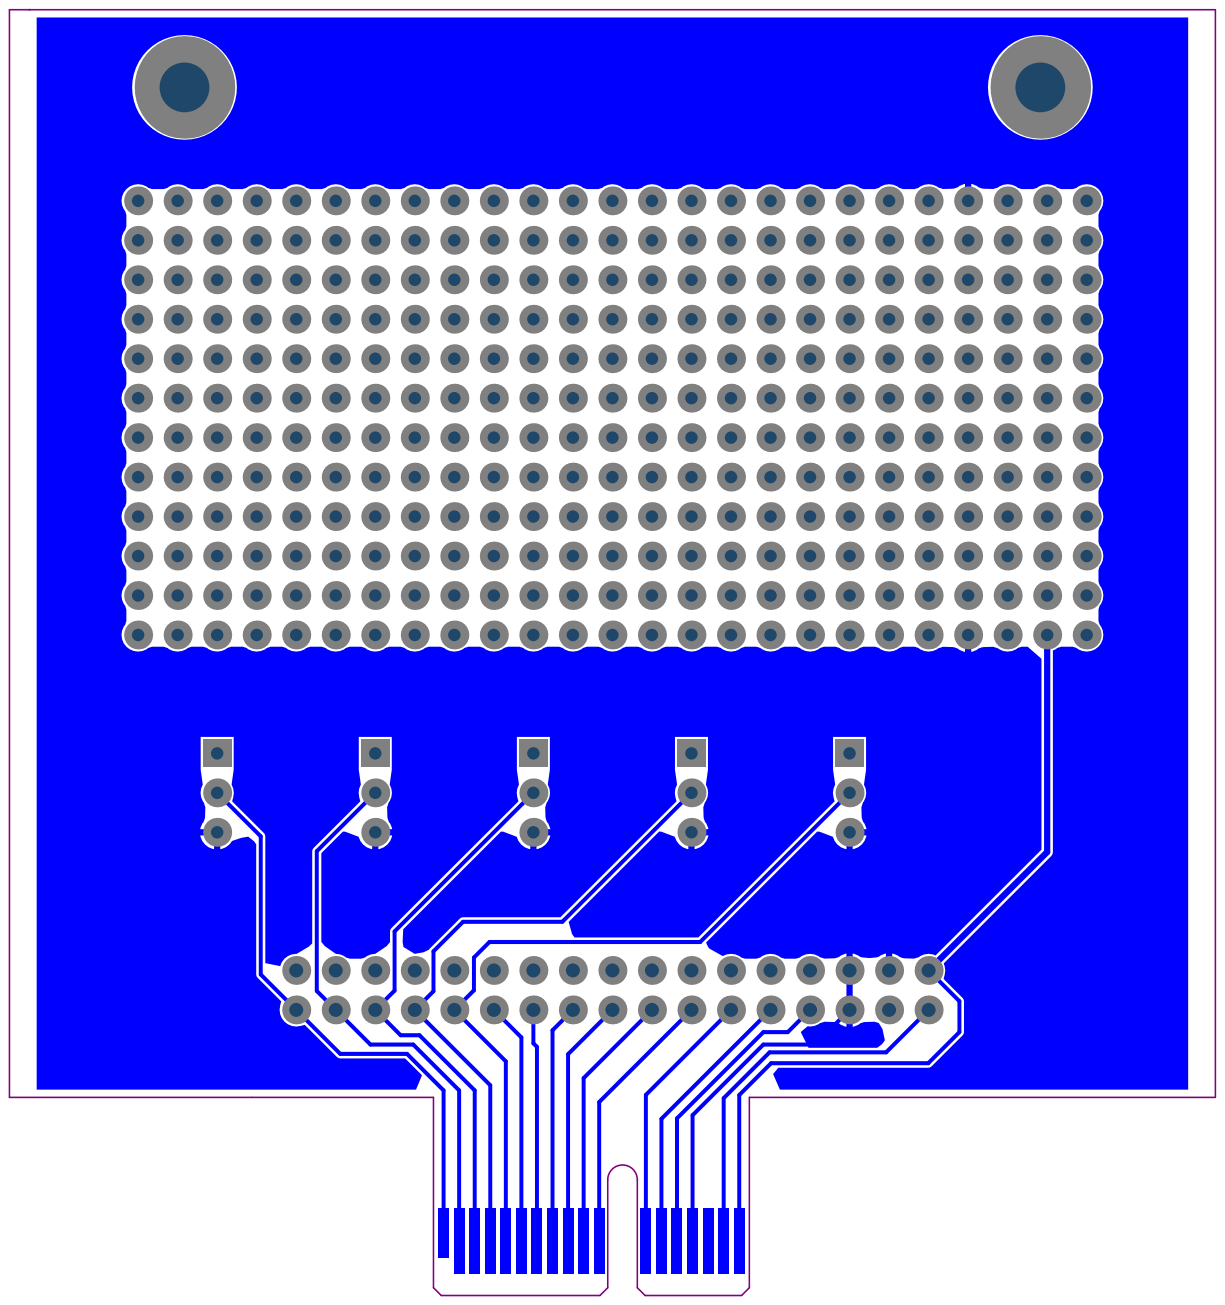
[picture p253: page 7]

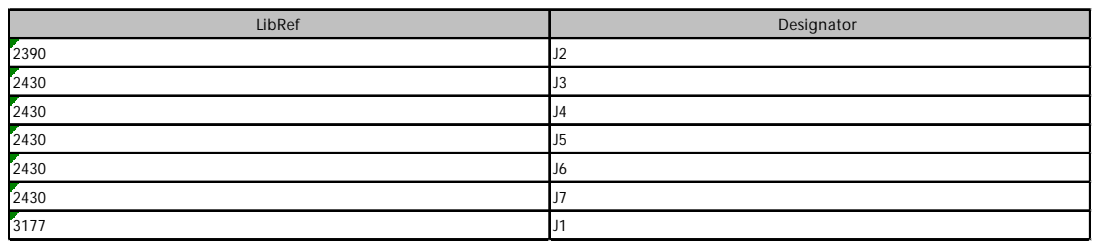
[picture p254: page 8]

LibRef | Designator
