Cable89/tesla-driver/05_Hardware/TK500_Driver/TK516_LINREG-PSU/Project Outputs/TK516_LINREG-PSU.PDF

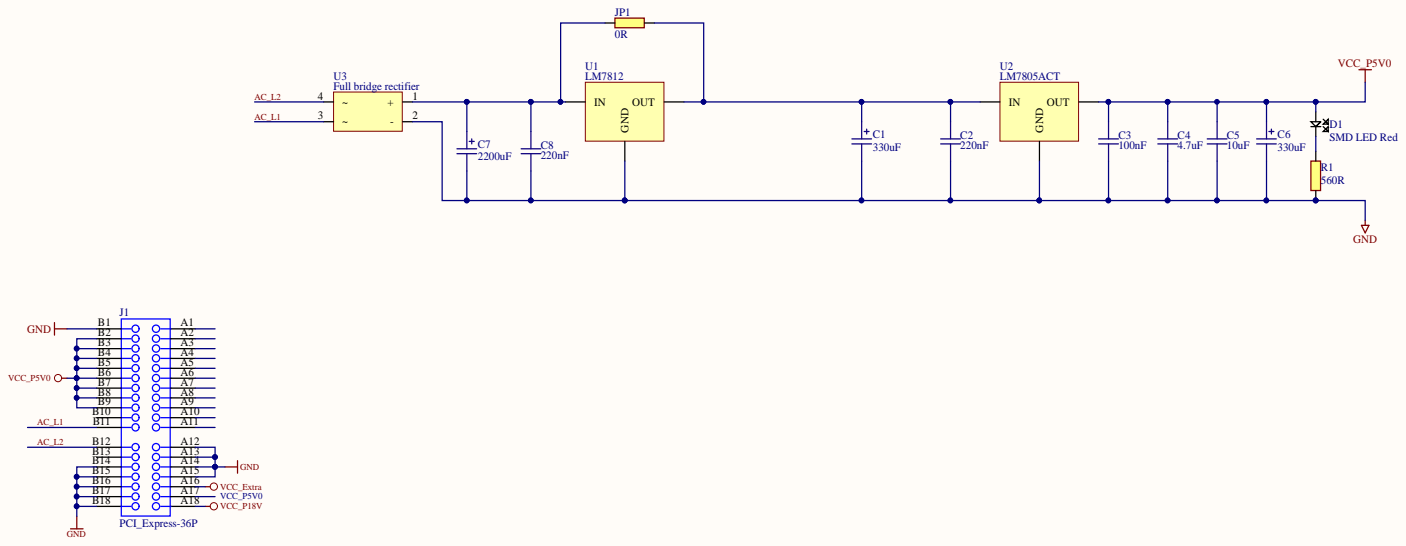
[picture p255: page 1]

Title: TK516 LINREG-PSU

Size: A3 | Revision: 10 20 0 | Author : *

Date: | Sheet of | Omega Verksted

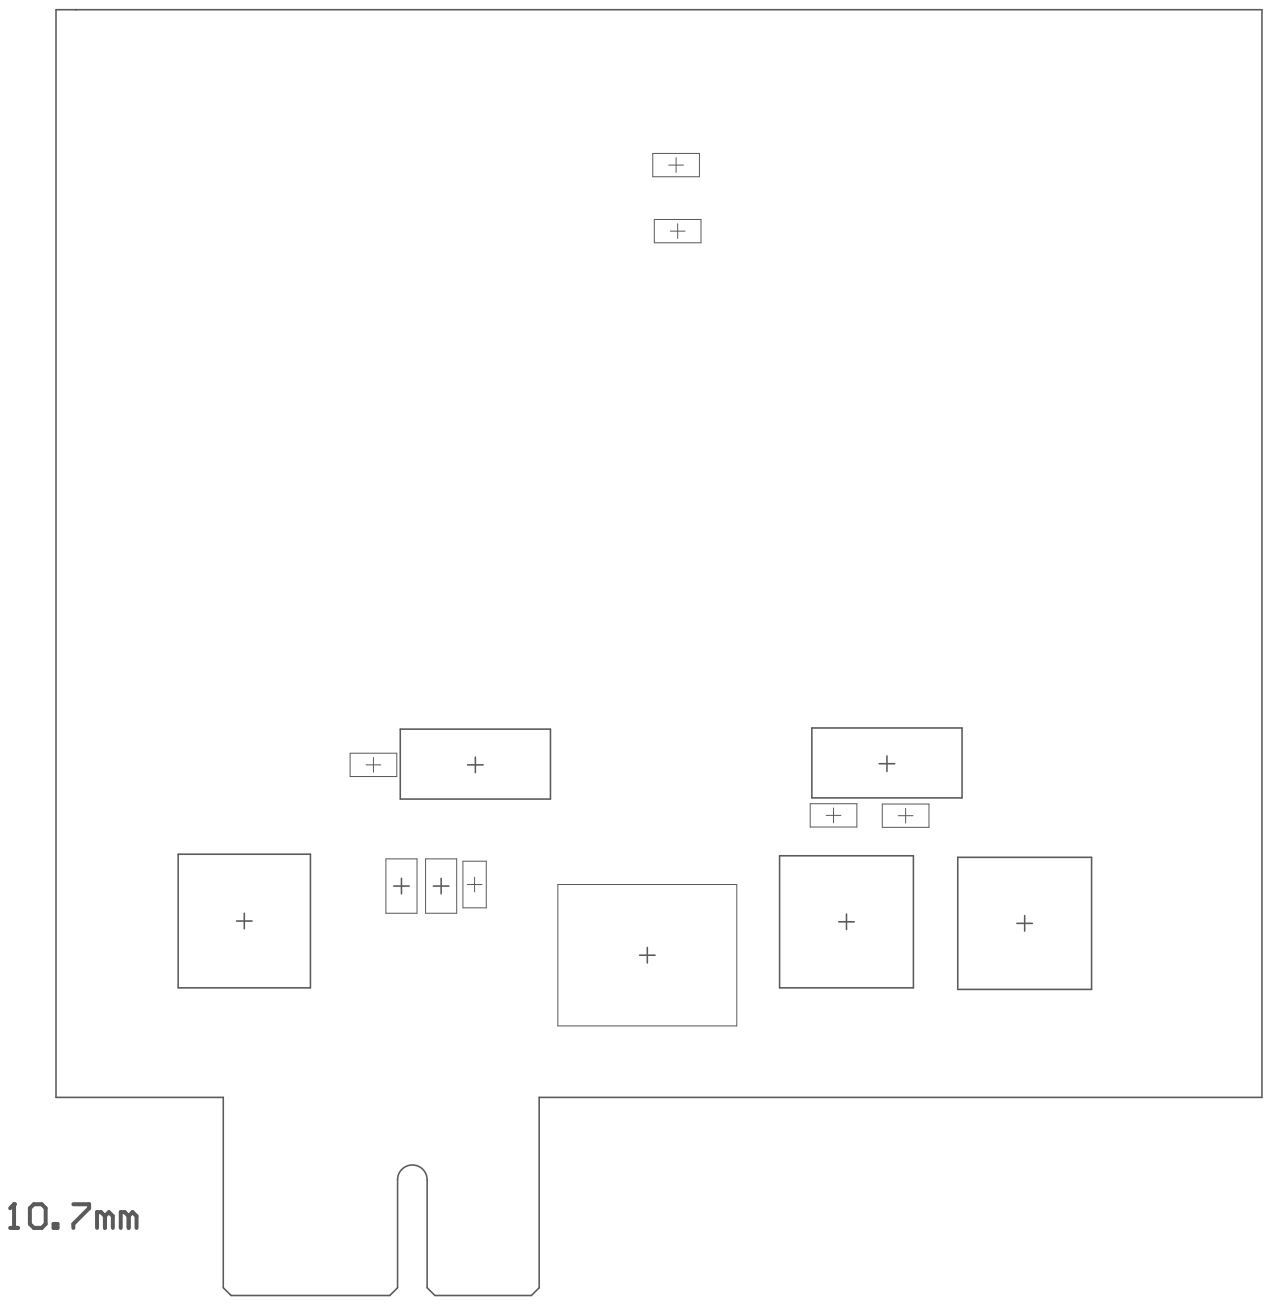
[picture p256: page 2]

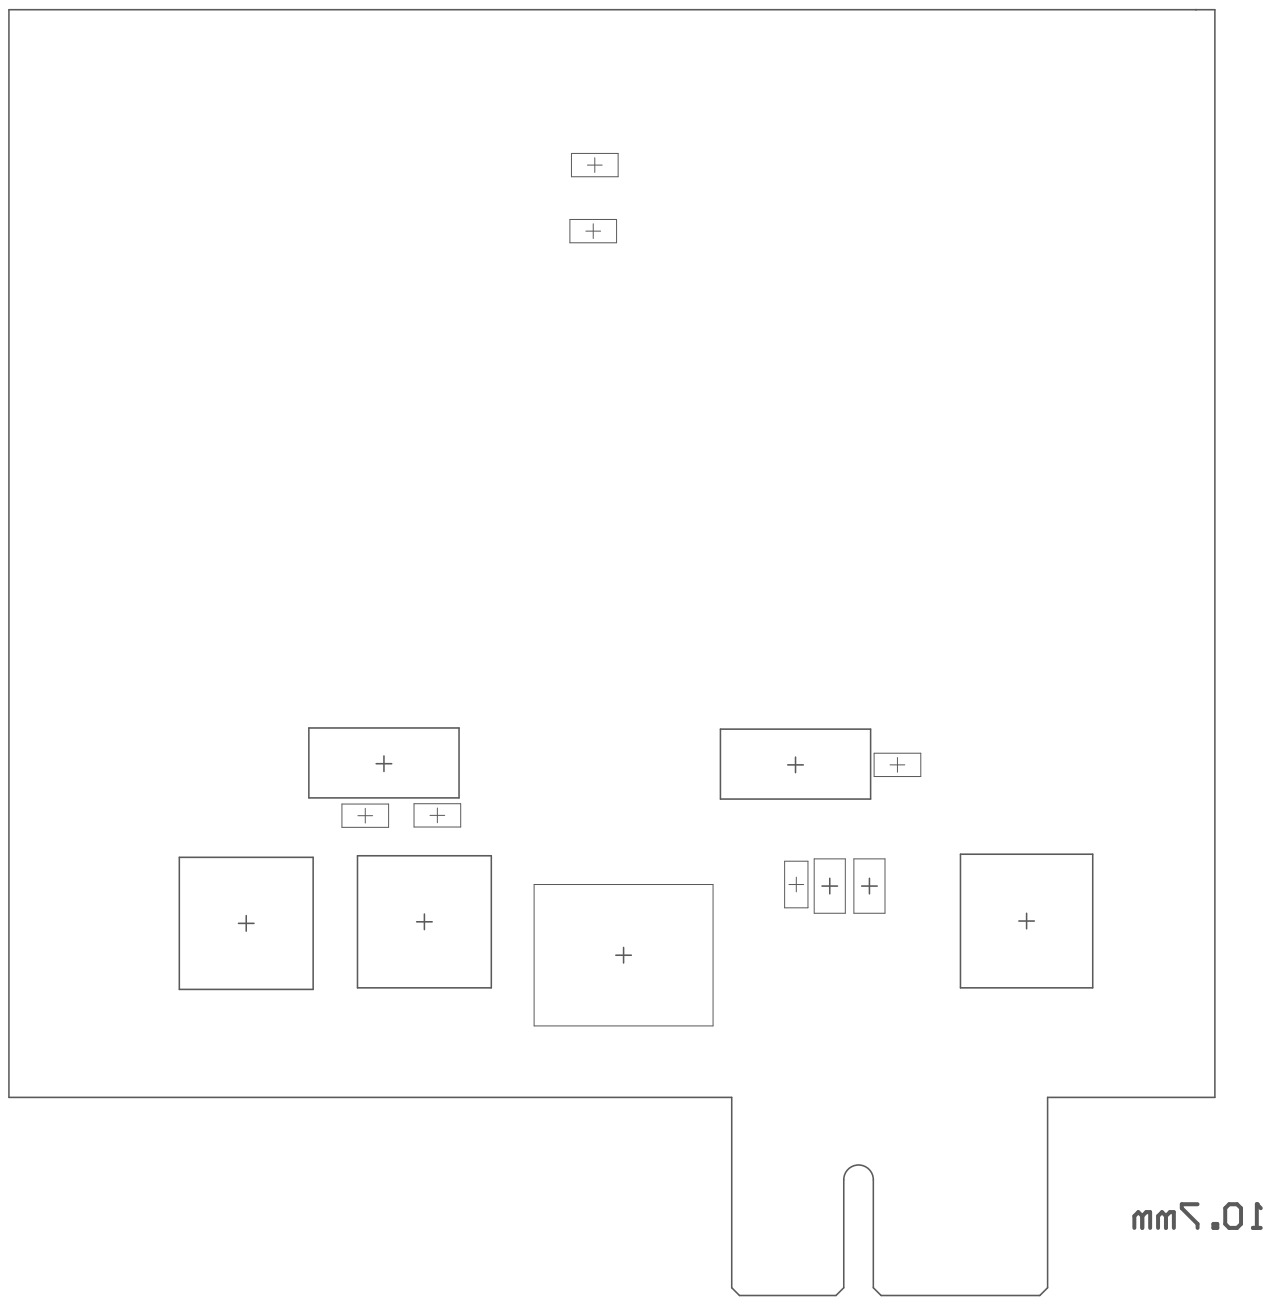
[picture p257: page 3]

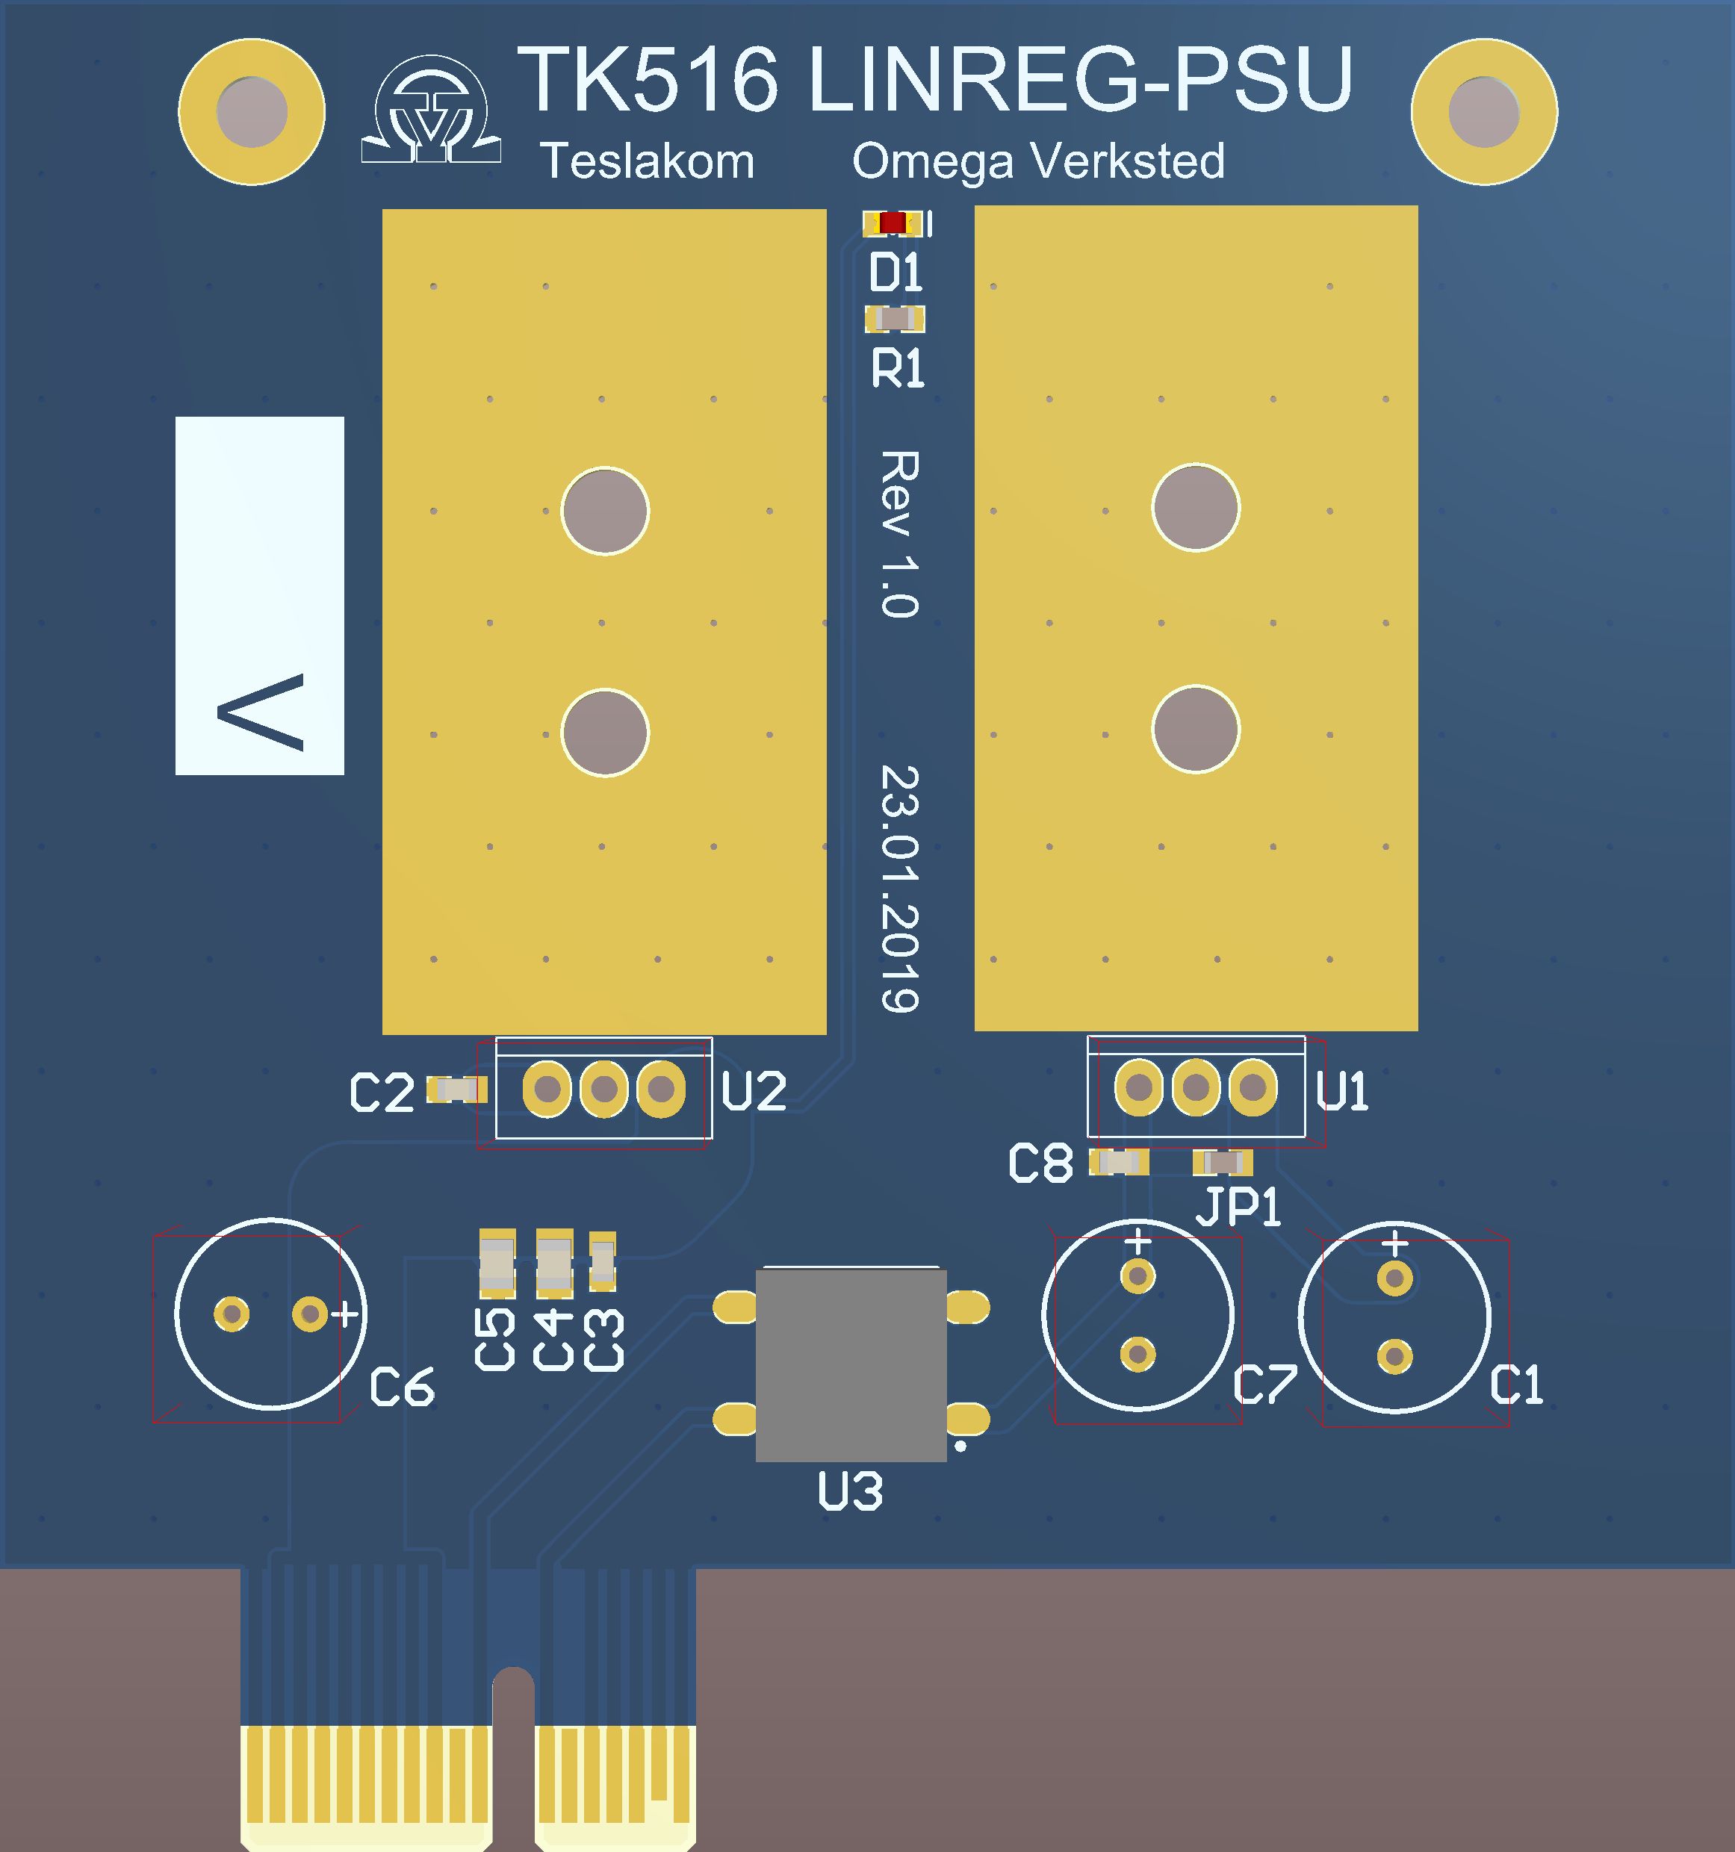
[picture p258: page 4]

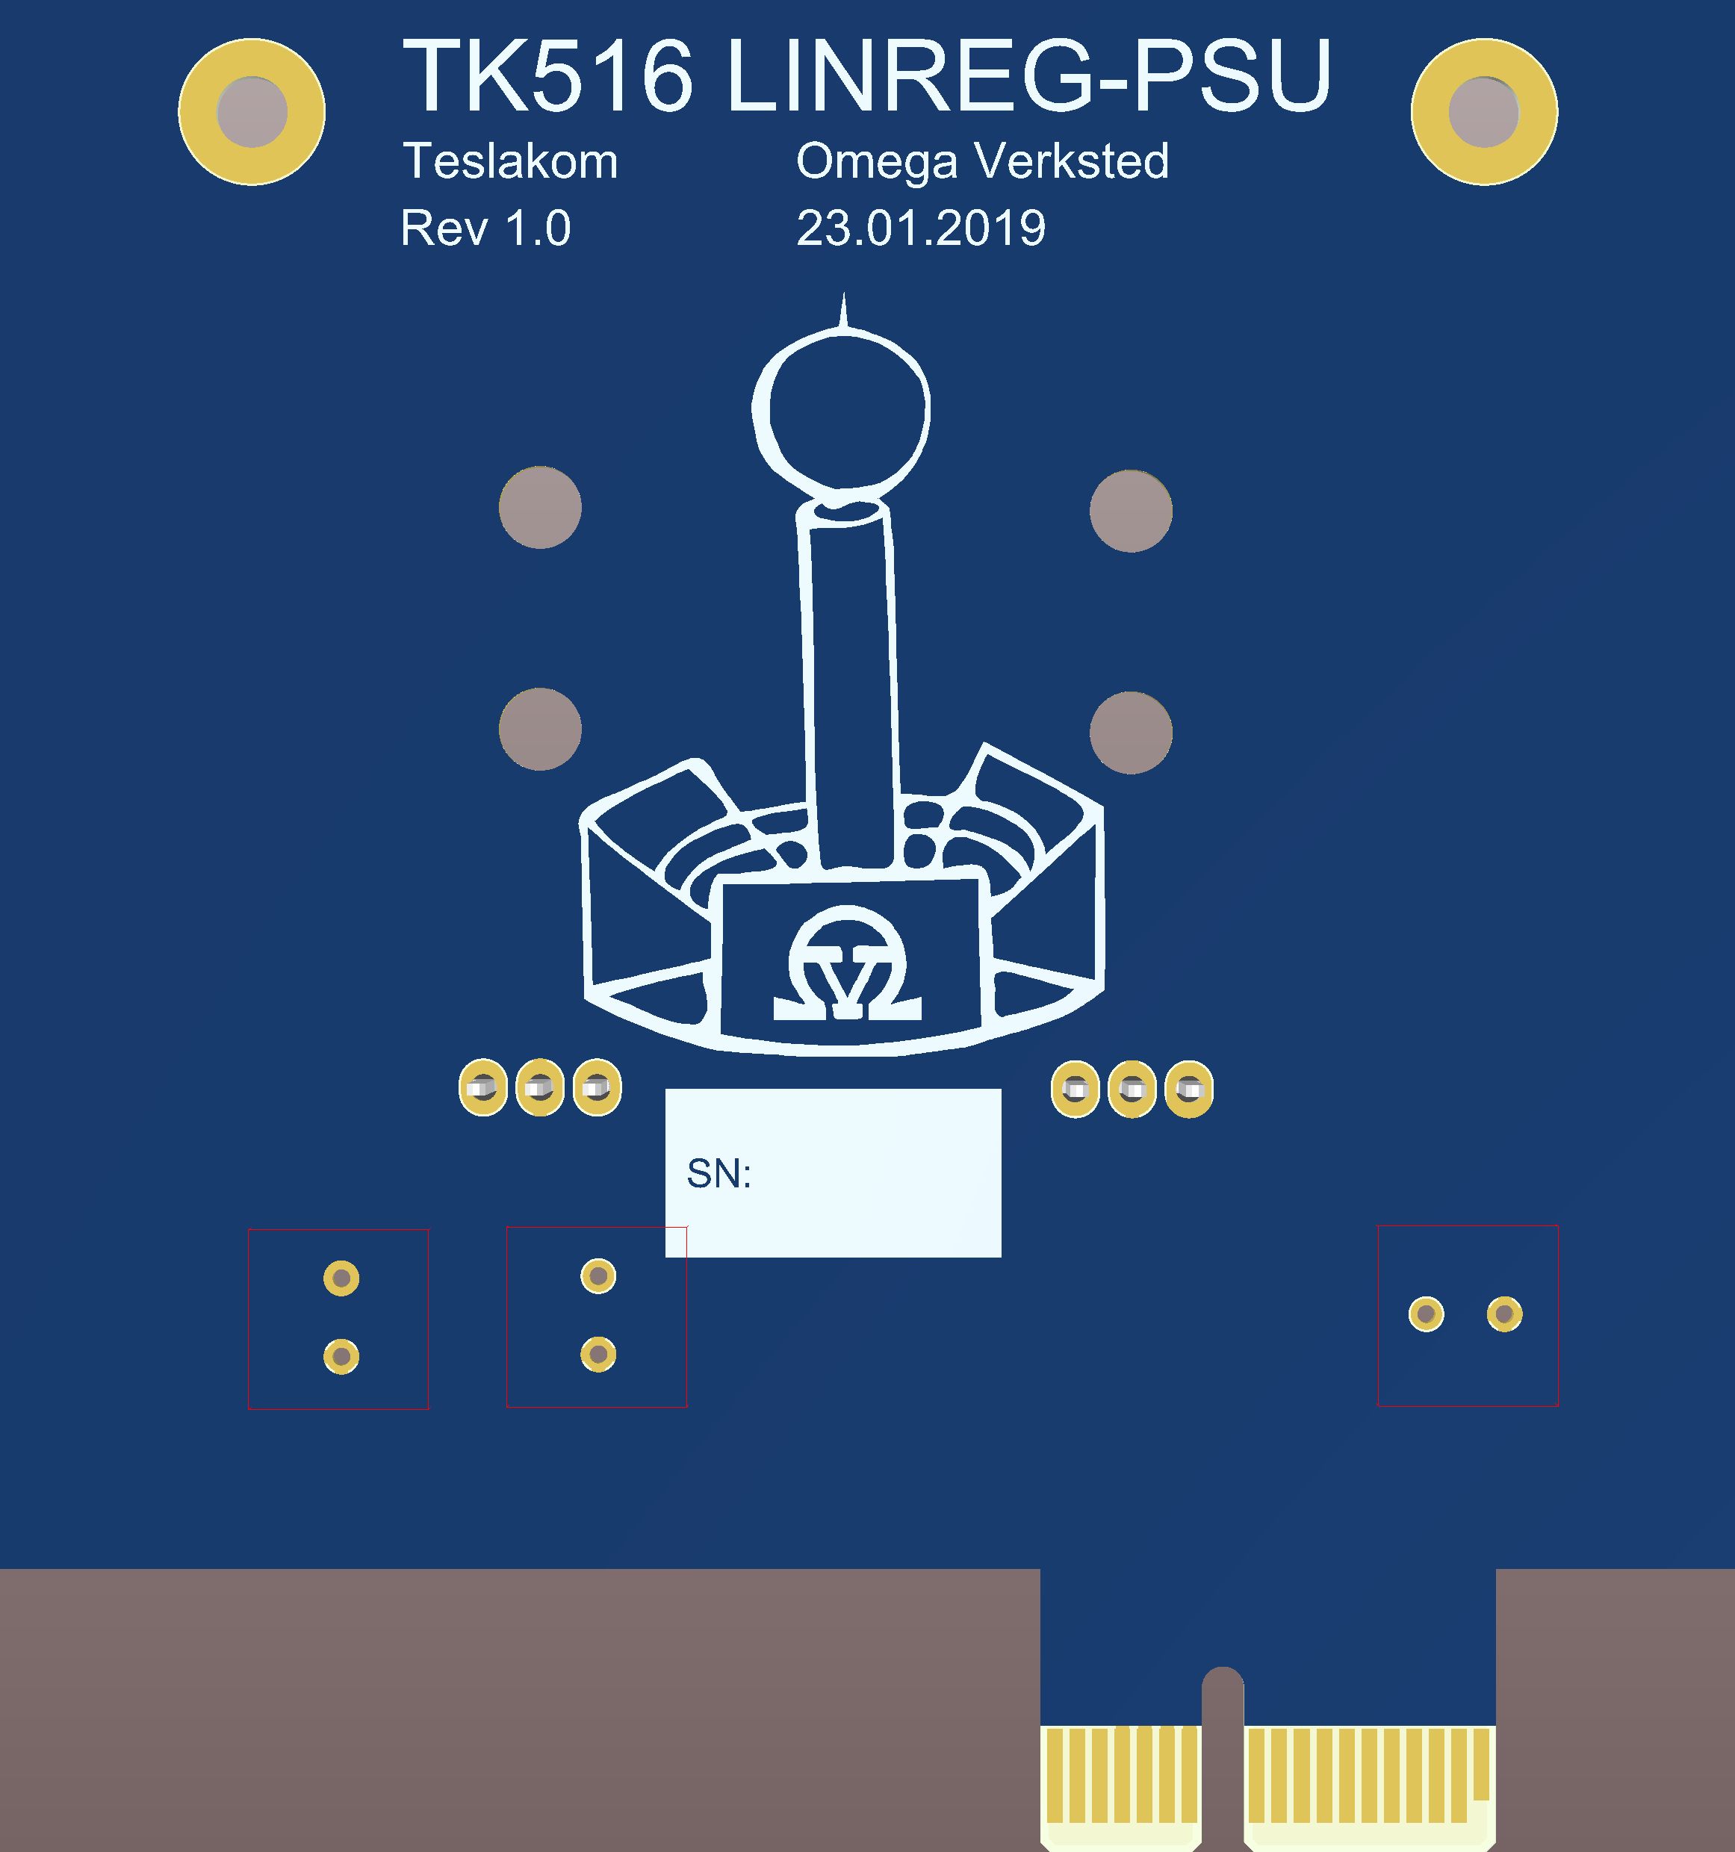
[picture p259: page 5]

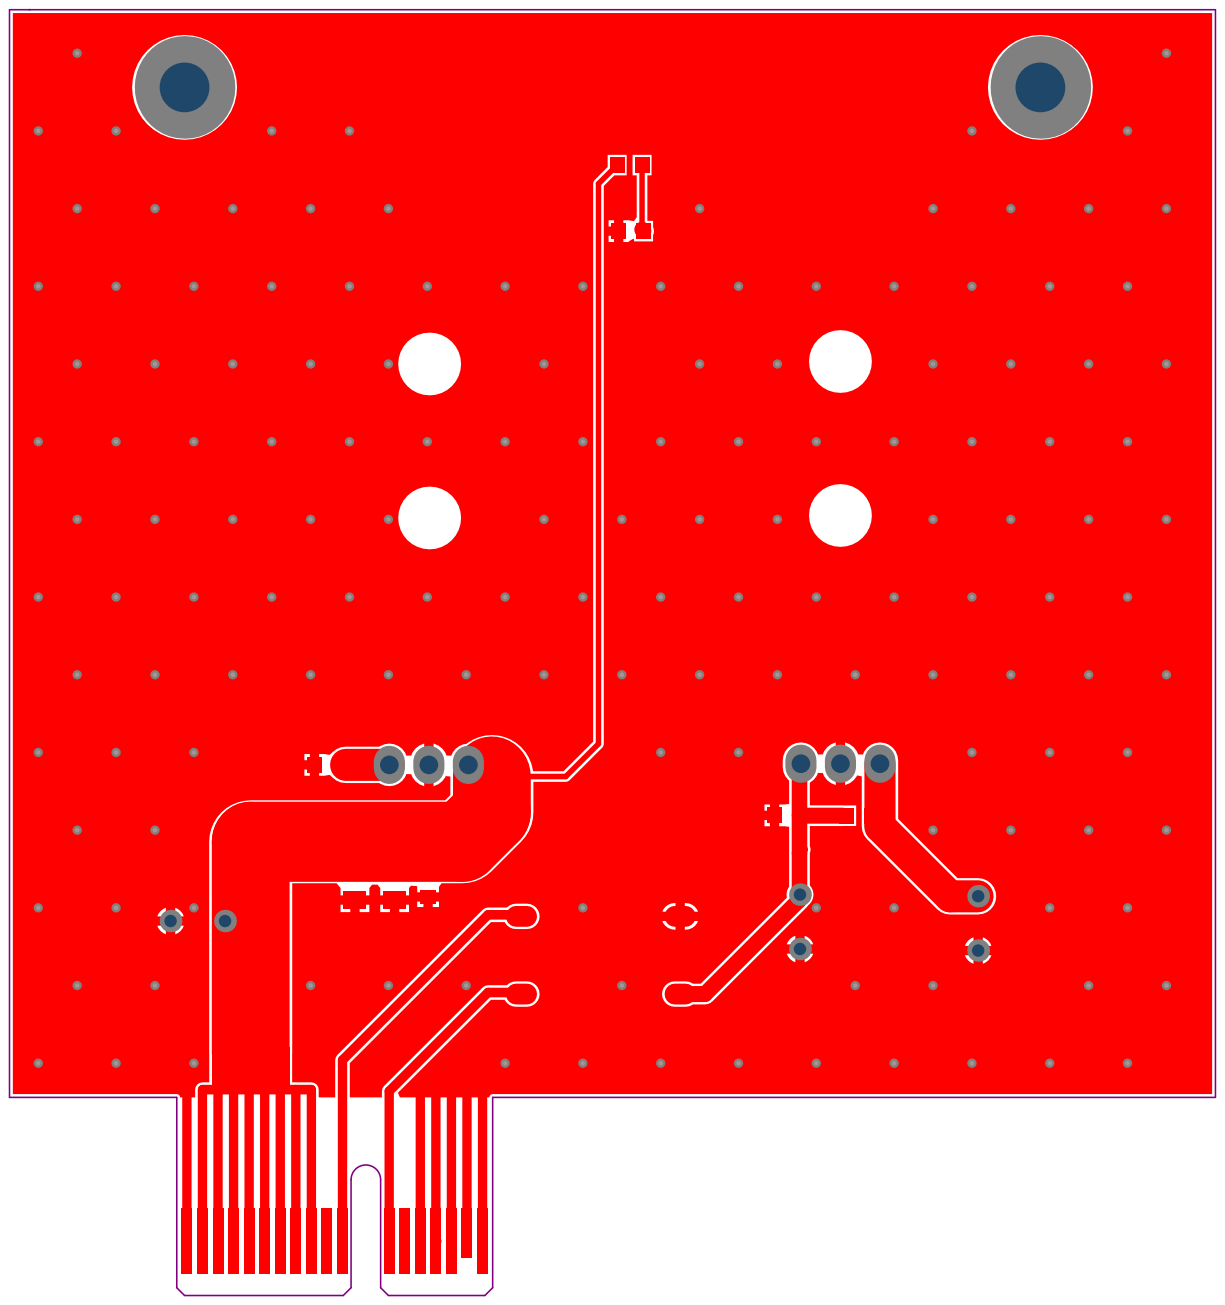
[picture p260: page 6]

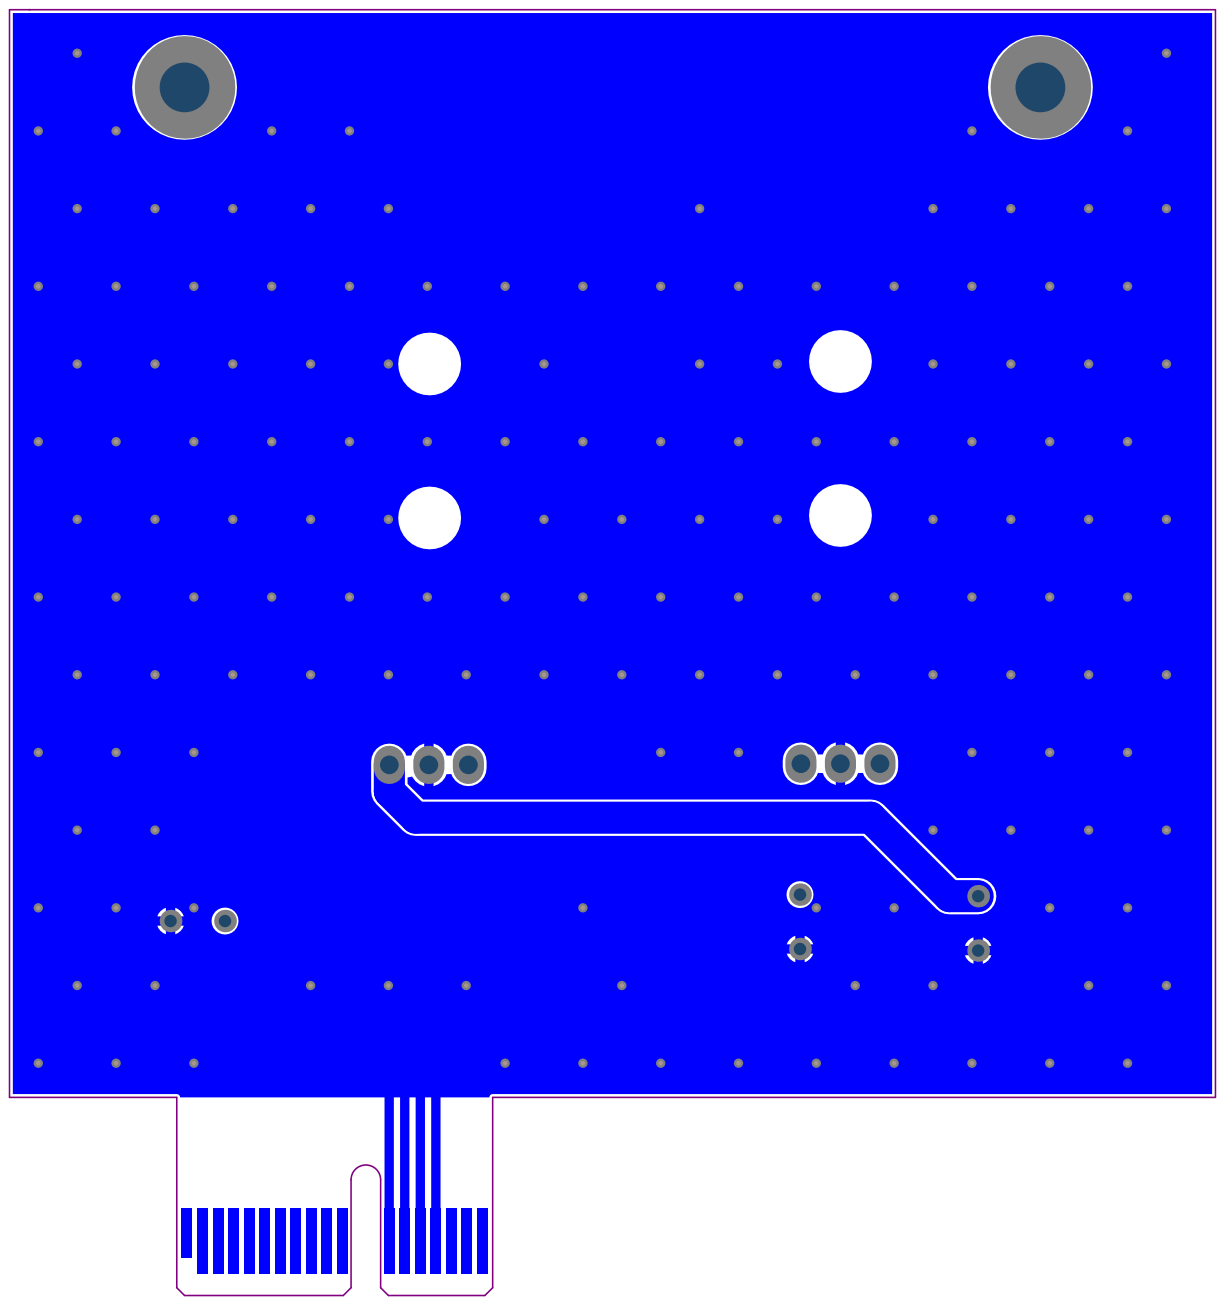
[picture p261: page 7]

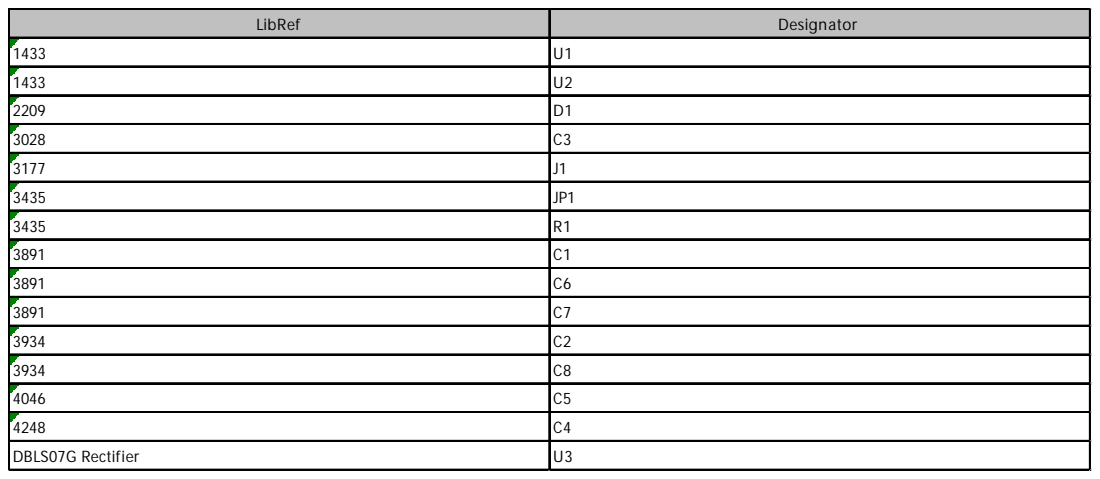
[picture p262: page 8]

LibRef | Designator

DBLS07G Rectifier | U3
