Cable89/tesla-driver/05_Hardware/TK500_Driver/TK520_GDT-Trafo/Project Outputs/TK520_GDT-Trafo.PDF

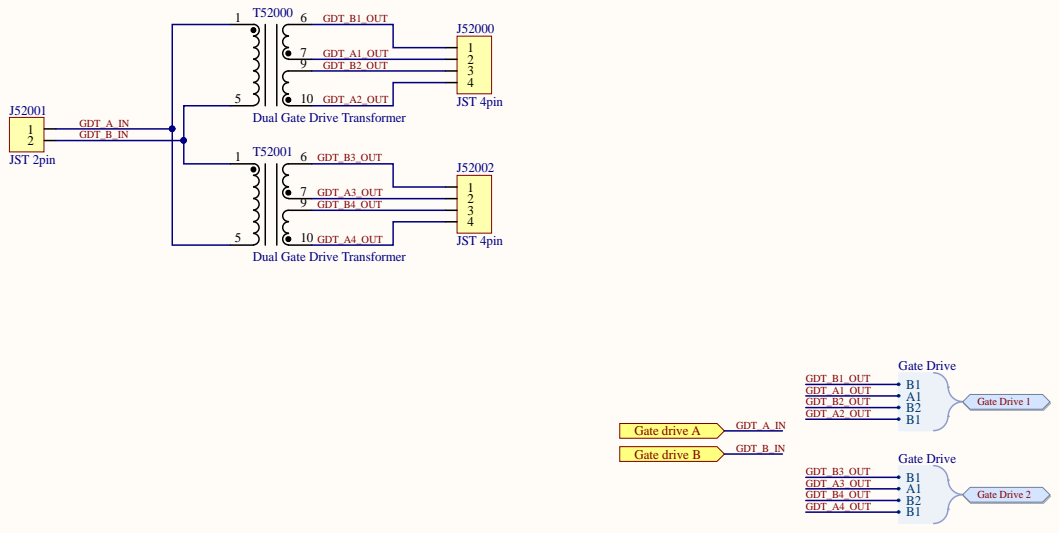
[picture p263: page 1]

Dual Gate Drive Transformer

Title: TK520 GDT-Trafo

Size: A3 | Revision: 1 | Author: Øystein Smith

Date: 23.01.2019 | Sheet 13 of 20 | Omega Verksted

C:\git\tesla-driver\05_Hardware\TK500_Driver\TK520_GDT-Trafo\TK520_GDT-Trafo.SchDoc

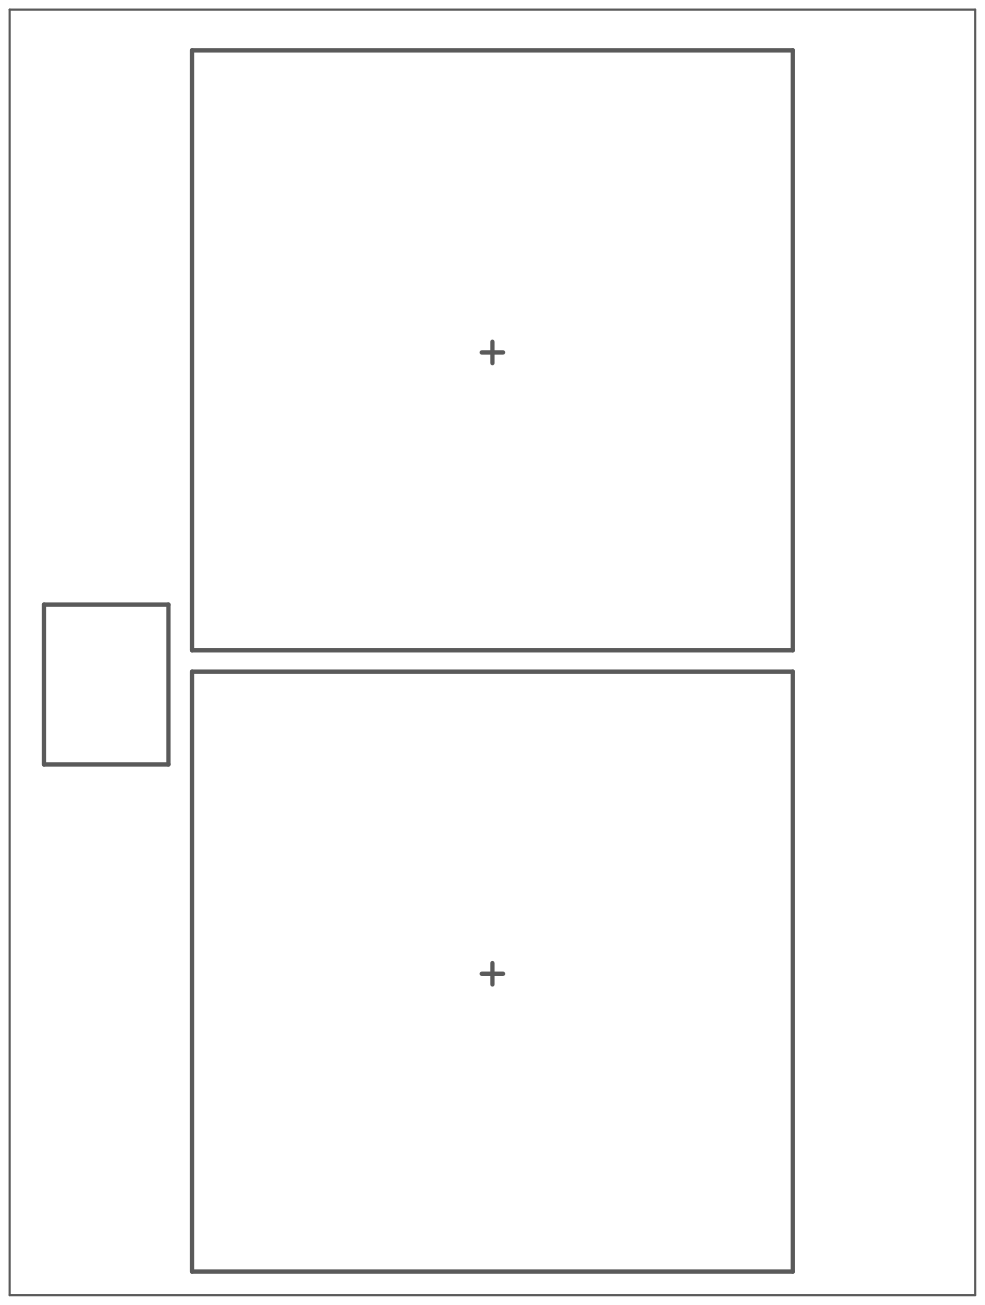
[picture p264: page 2]

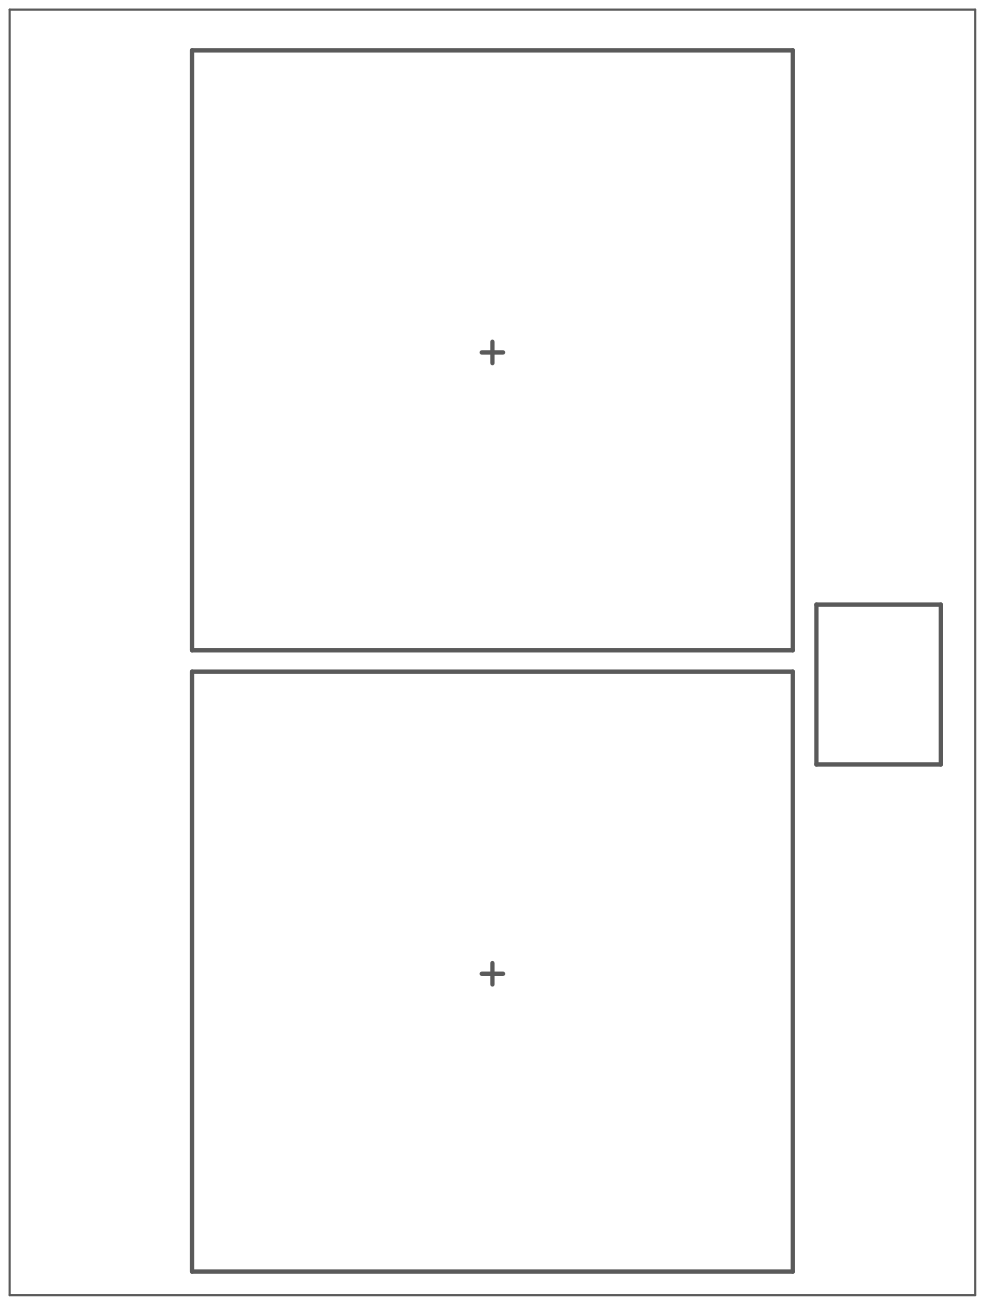
[picture p265: page 3]

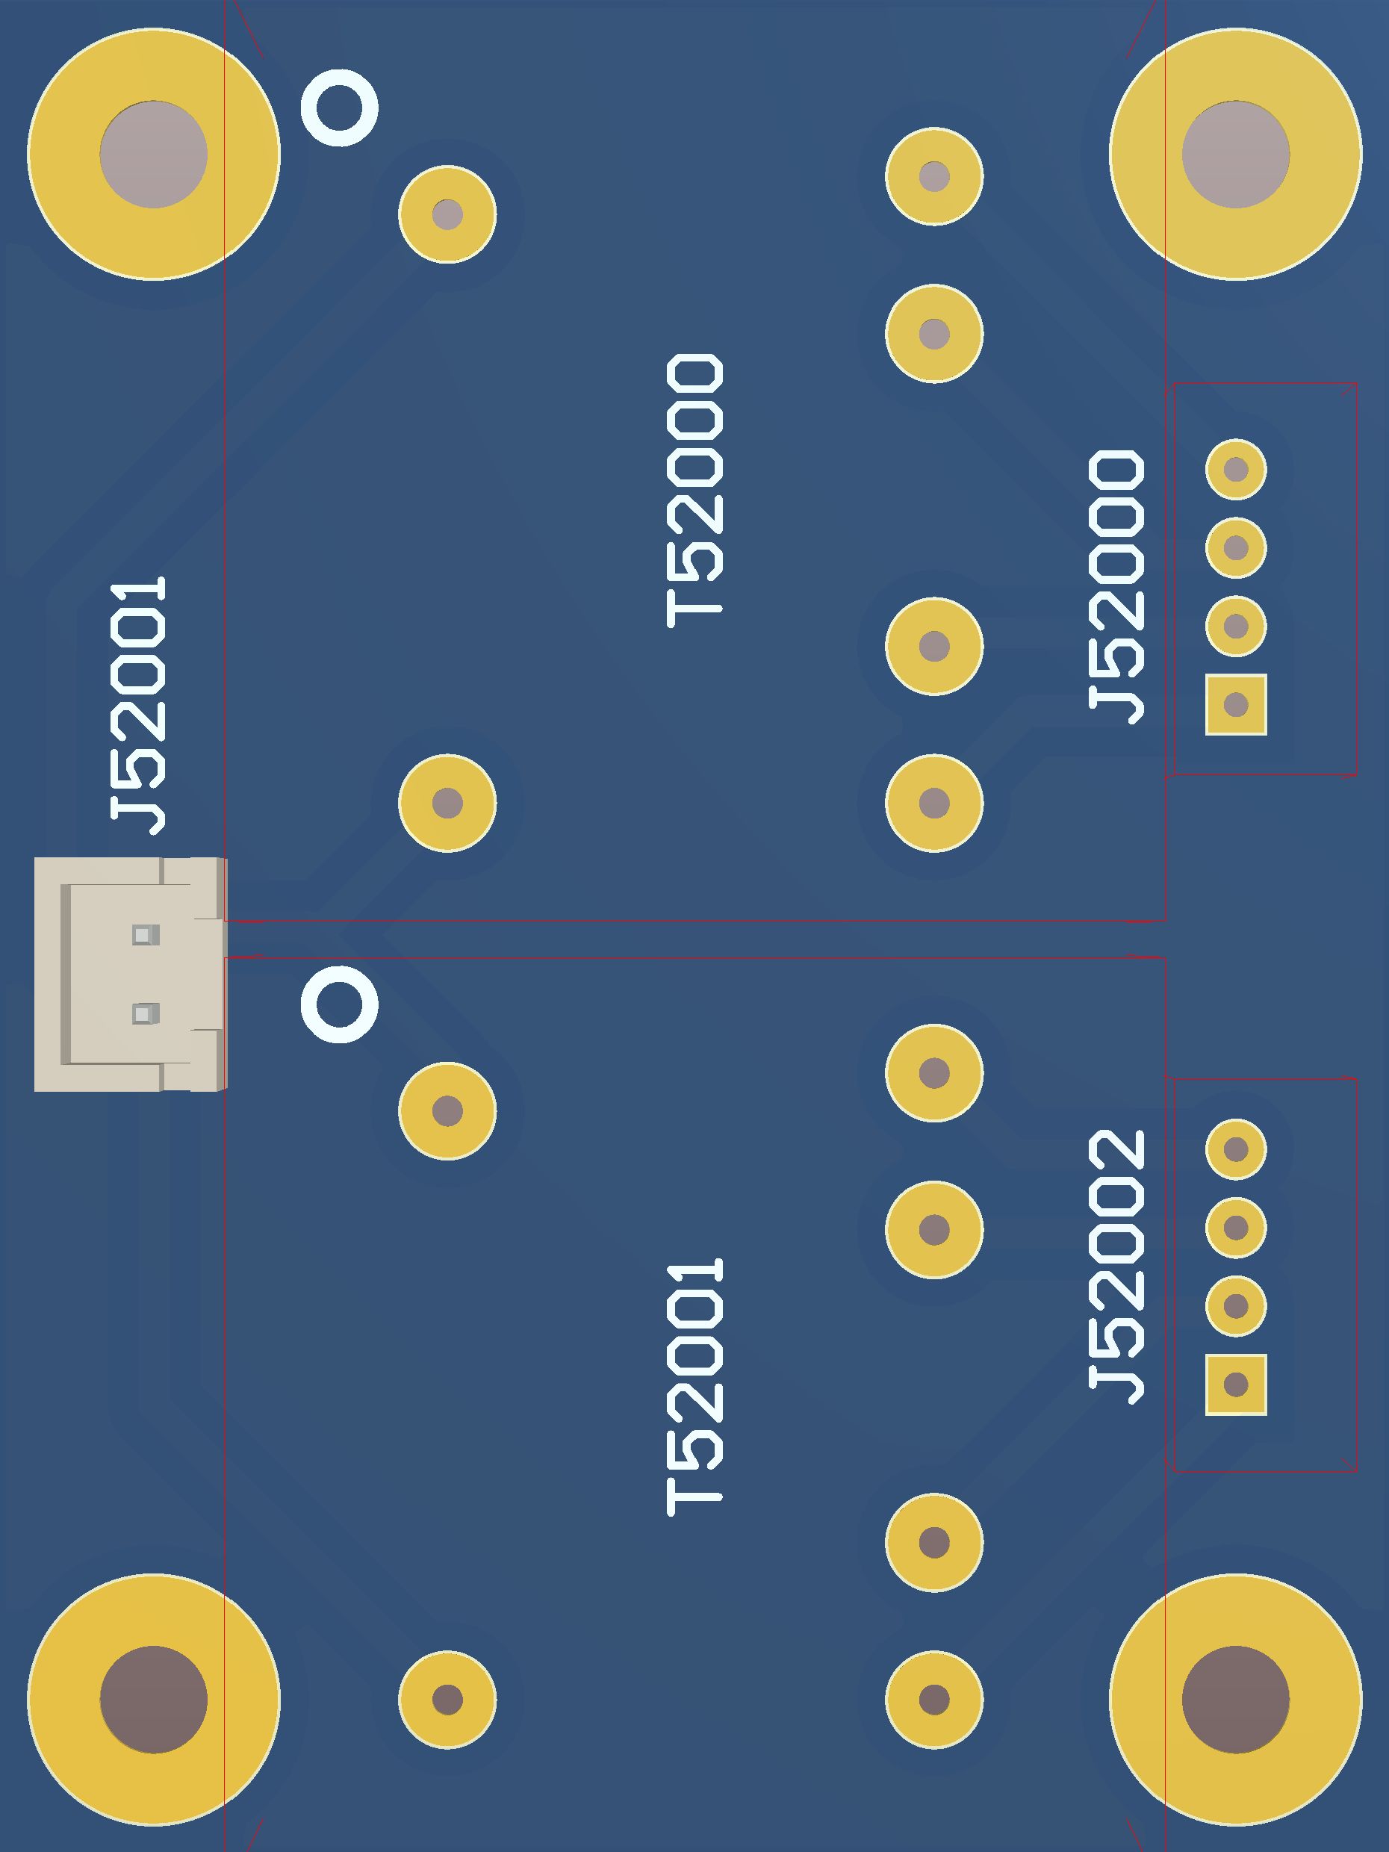
[picture p266: page 4]

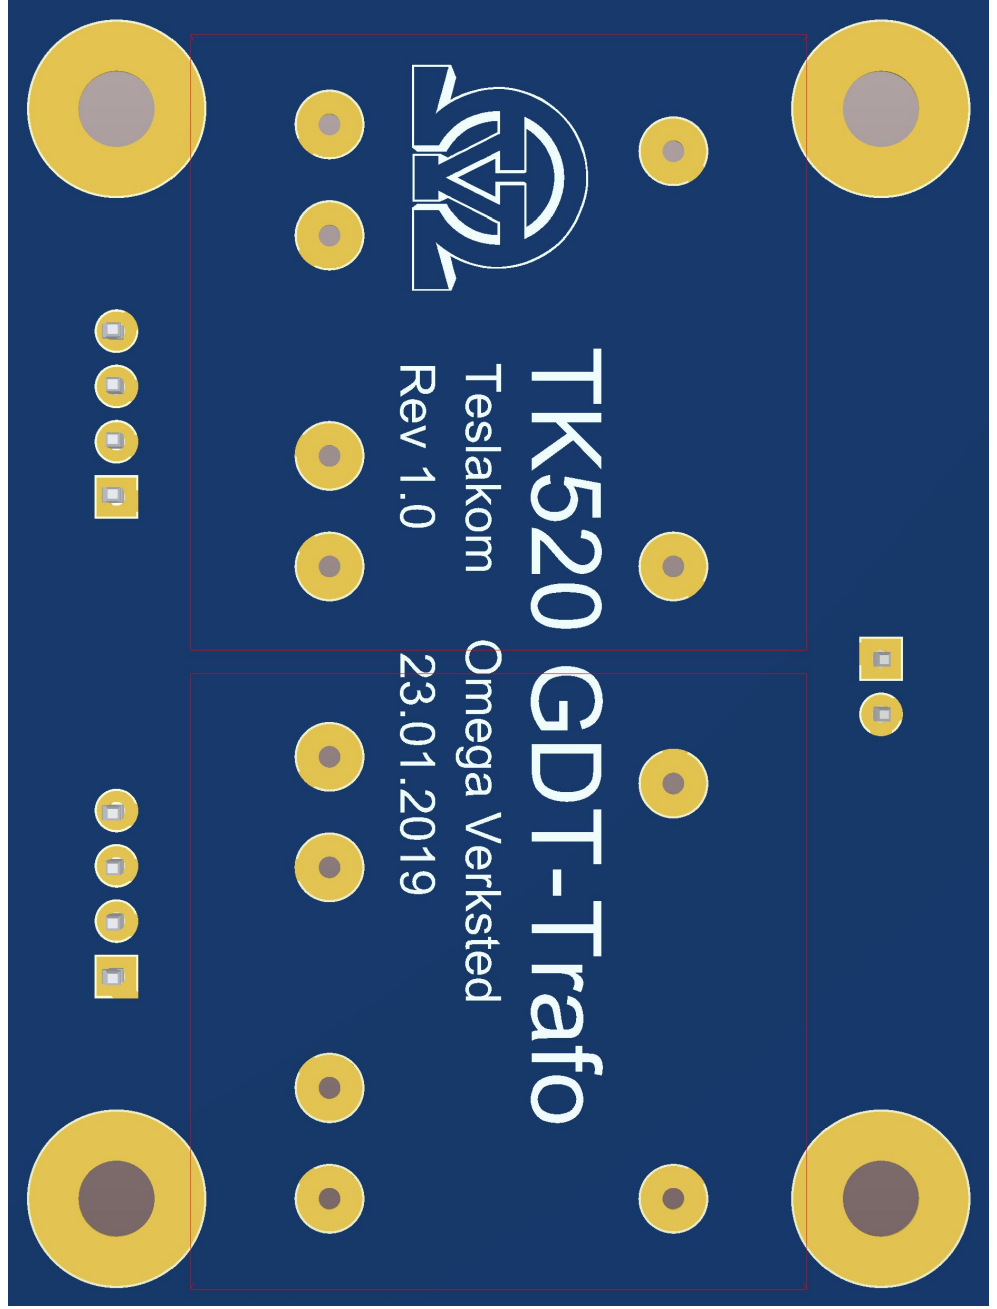
[picture p267: page 5]

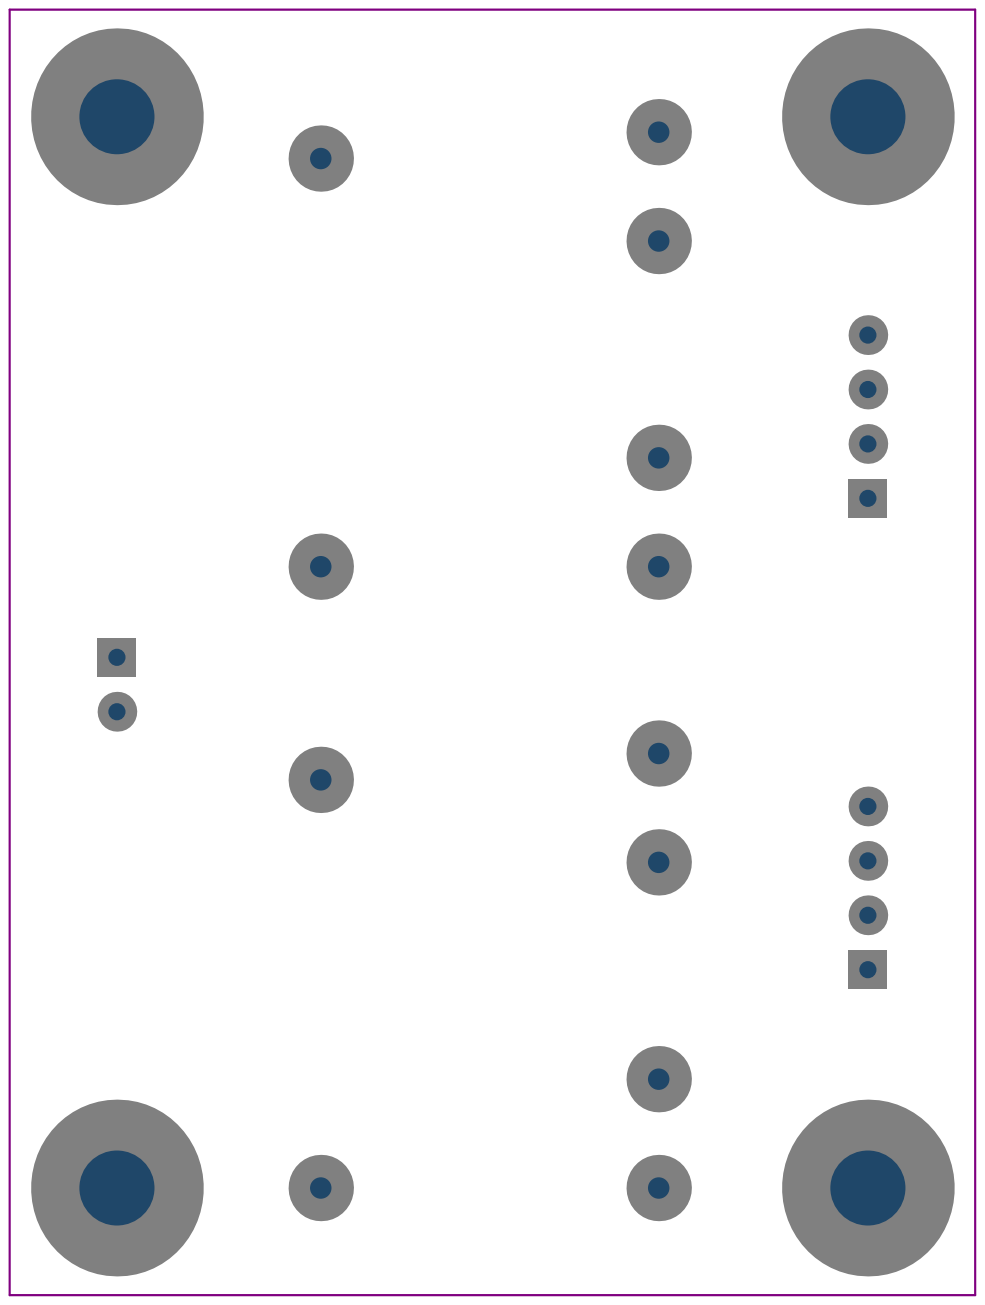
[picture p268: page 6]

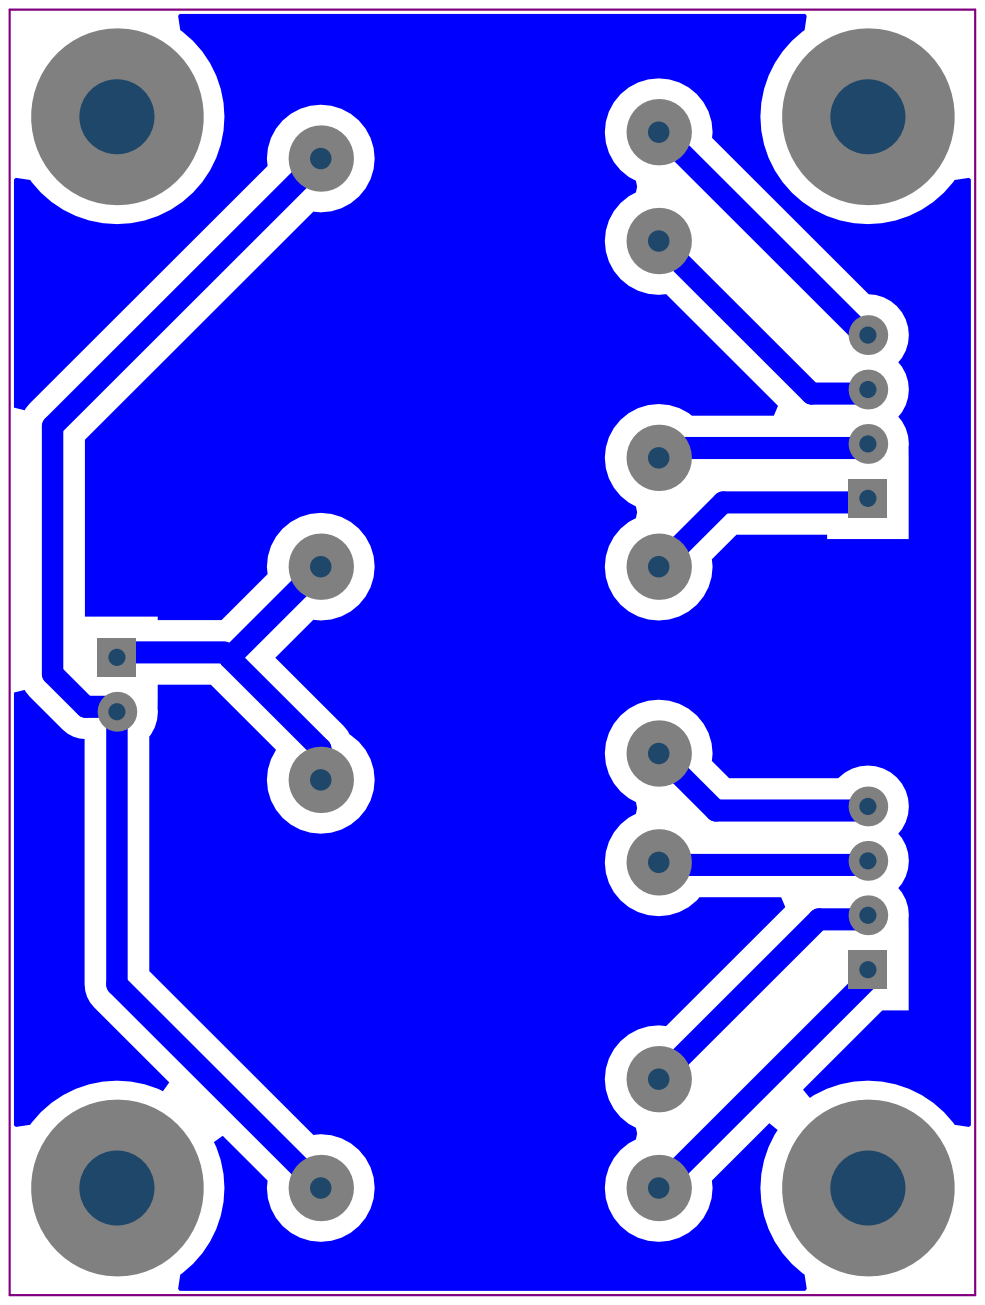
[picture p269: page 7]

LibRef | Designator
