Cable89/tesla-driver/05_Hardware/TK500_Driver/TK530_Kraftbakplan/Project Outputs/TK530_Kraftbakplan.PDF

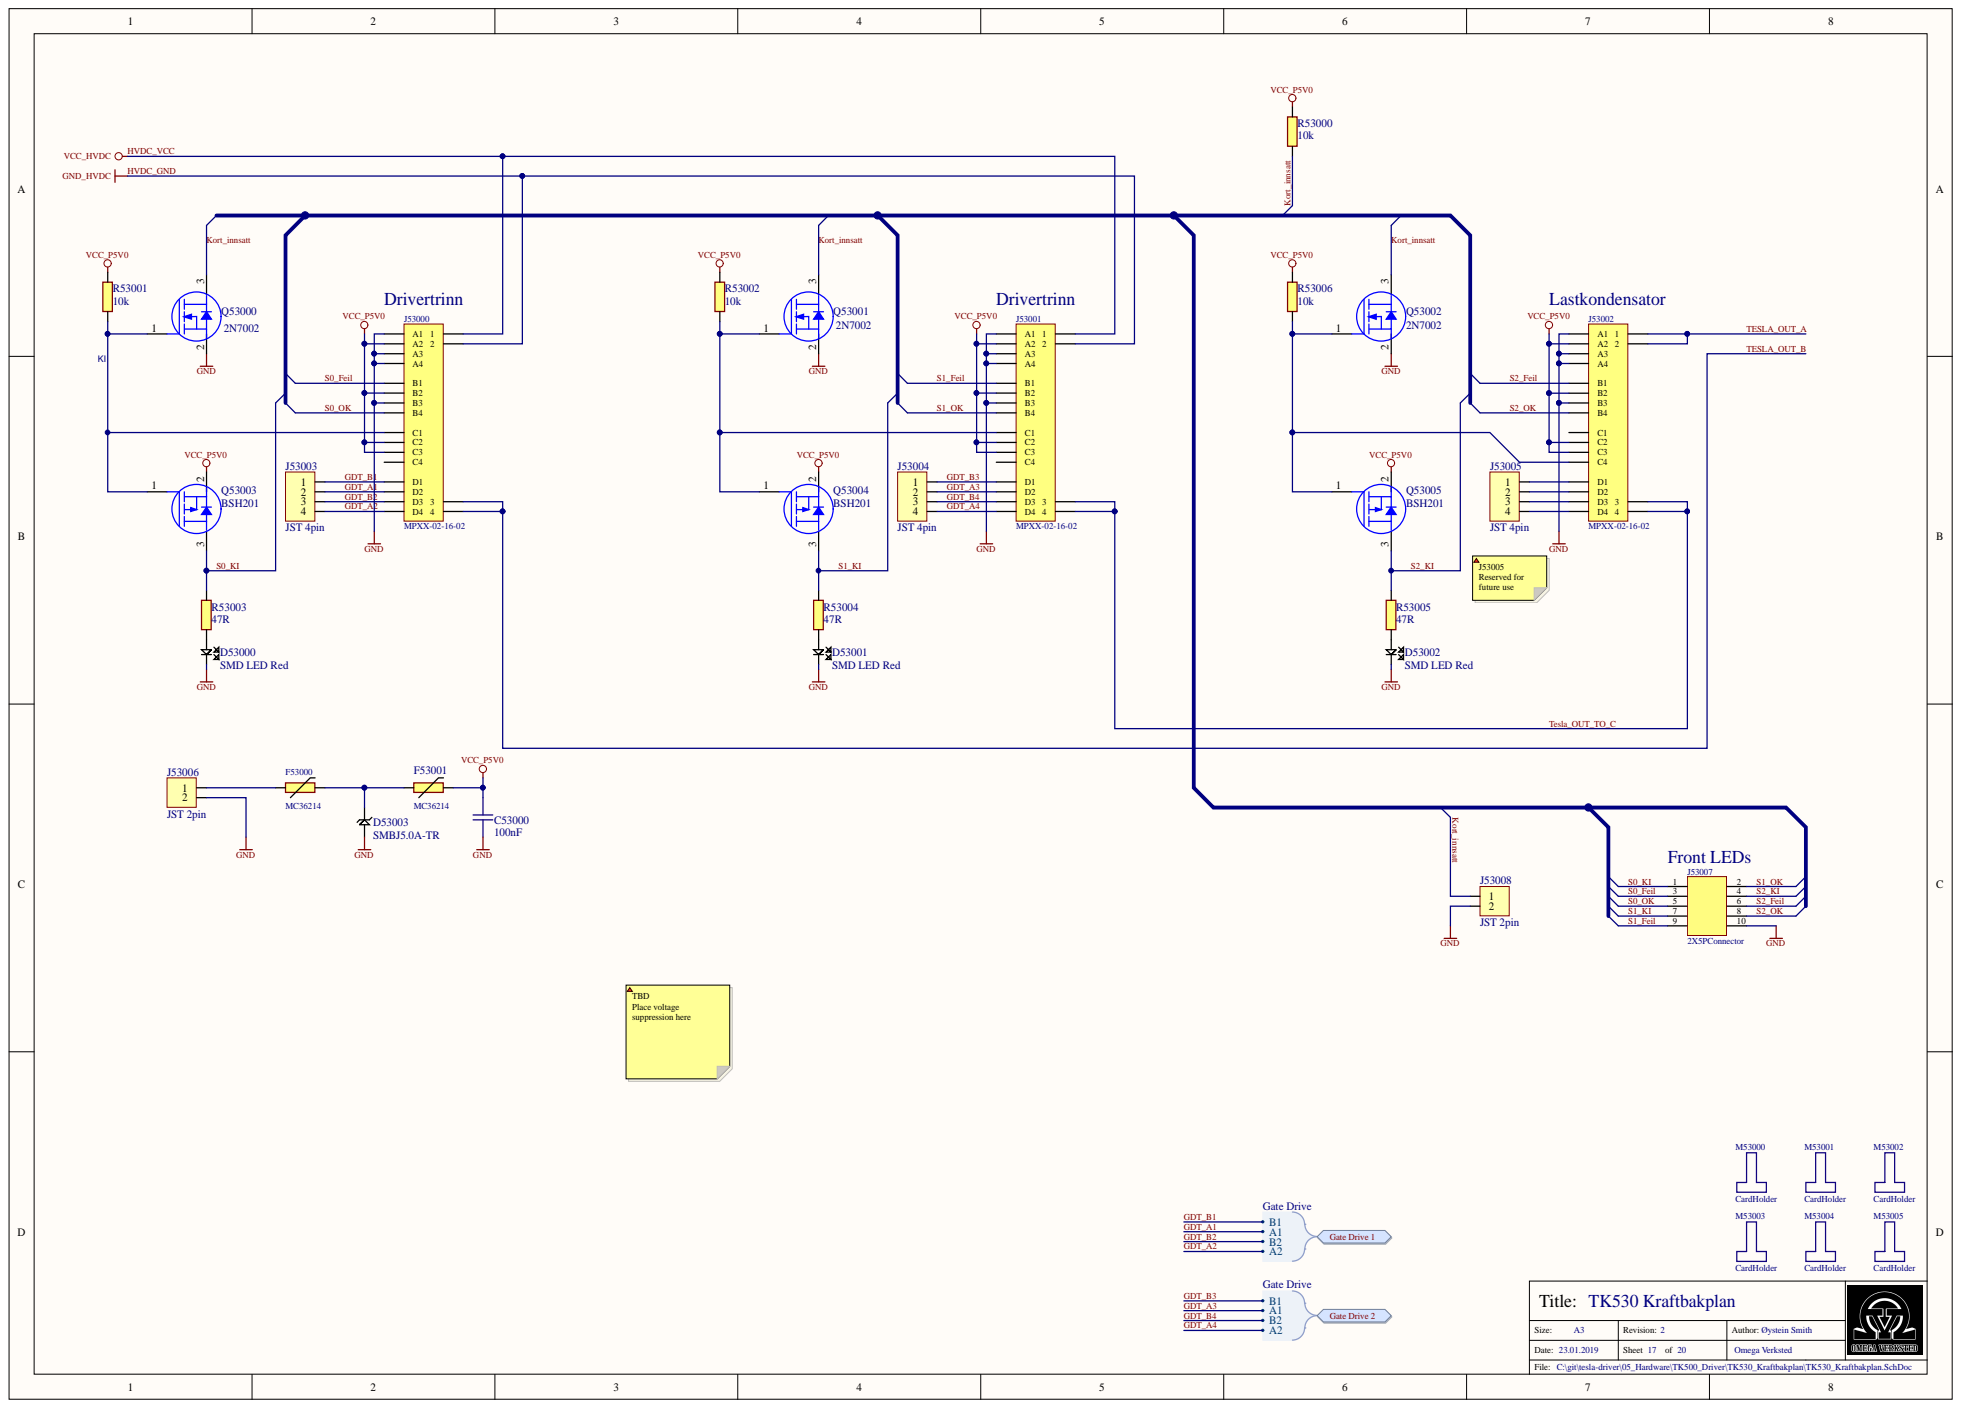
[picture p270: page 1]

S0_Feil | A3 A4 B1 B2 B3 B4 C1 C2 C3 C4 D1 D2 D3 3 D4 4 | S1_Feil | A3 A4 B1 B2 B3 B4 C1 C2 C3 C4 D1 D2 D3 3 D4 4

Title: TK530 Kraftbakplan

Size: A3 | Revision: 2 | Author: Øystein Smith

Date: 23.01.2019 | Sheet 17 of 20 | Omega Verksted

C:\git\tesla-driver\05_Hardware\TK500_Driver\TK530_Kraftbakplan\TK530_Kraftbakplan.SchDoc

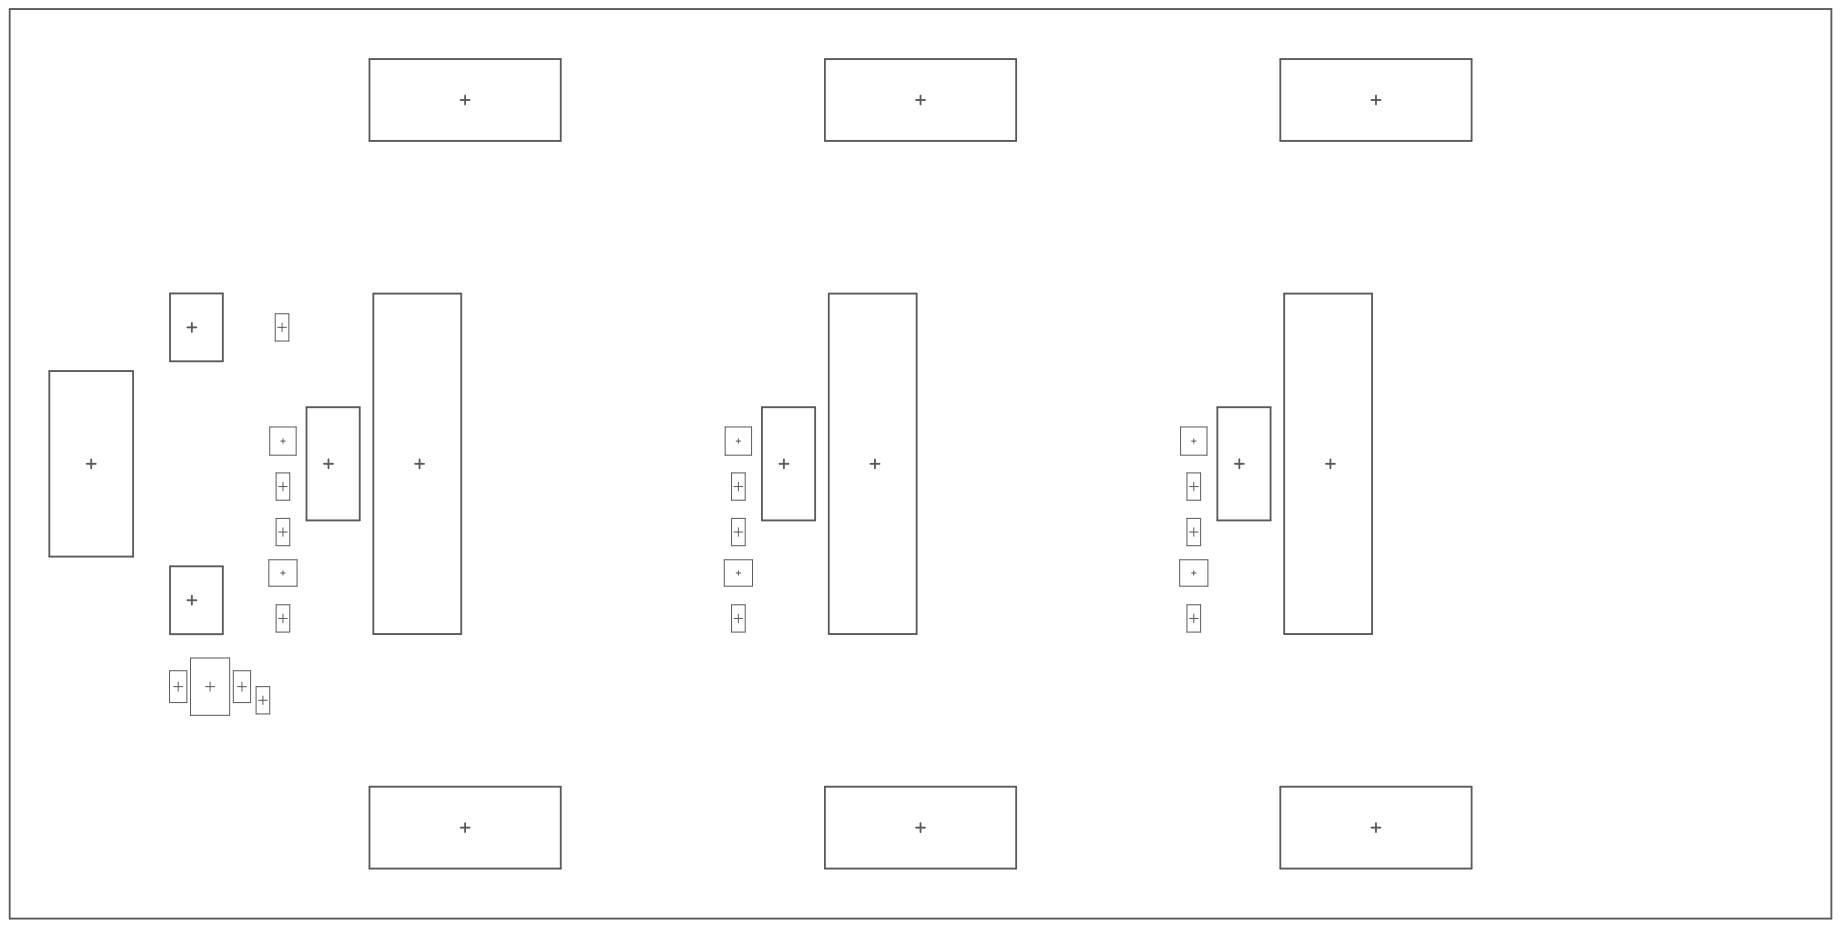
[picture p271: page 2]

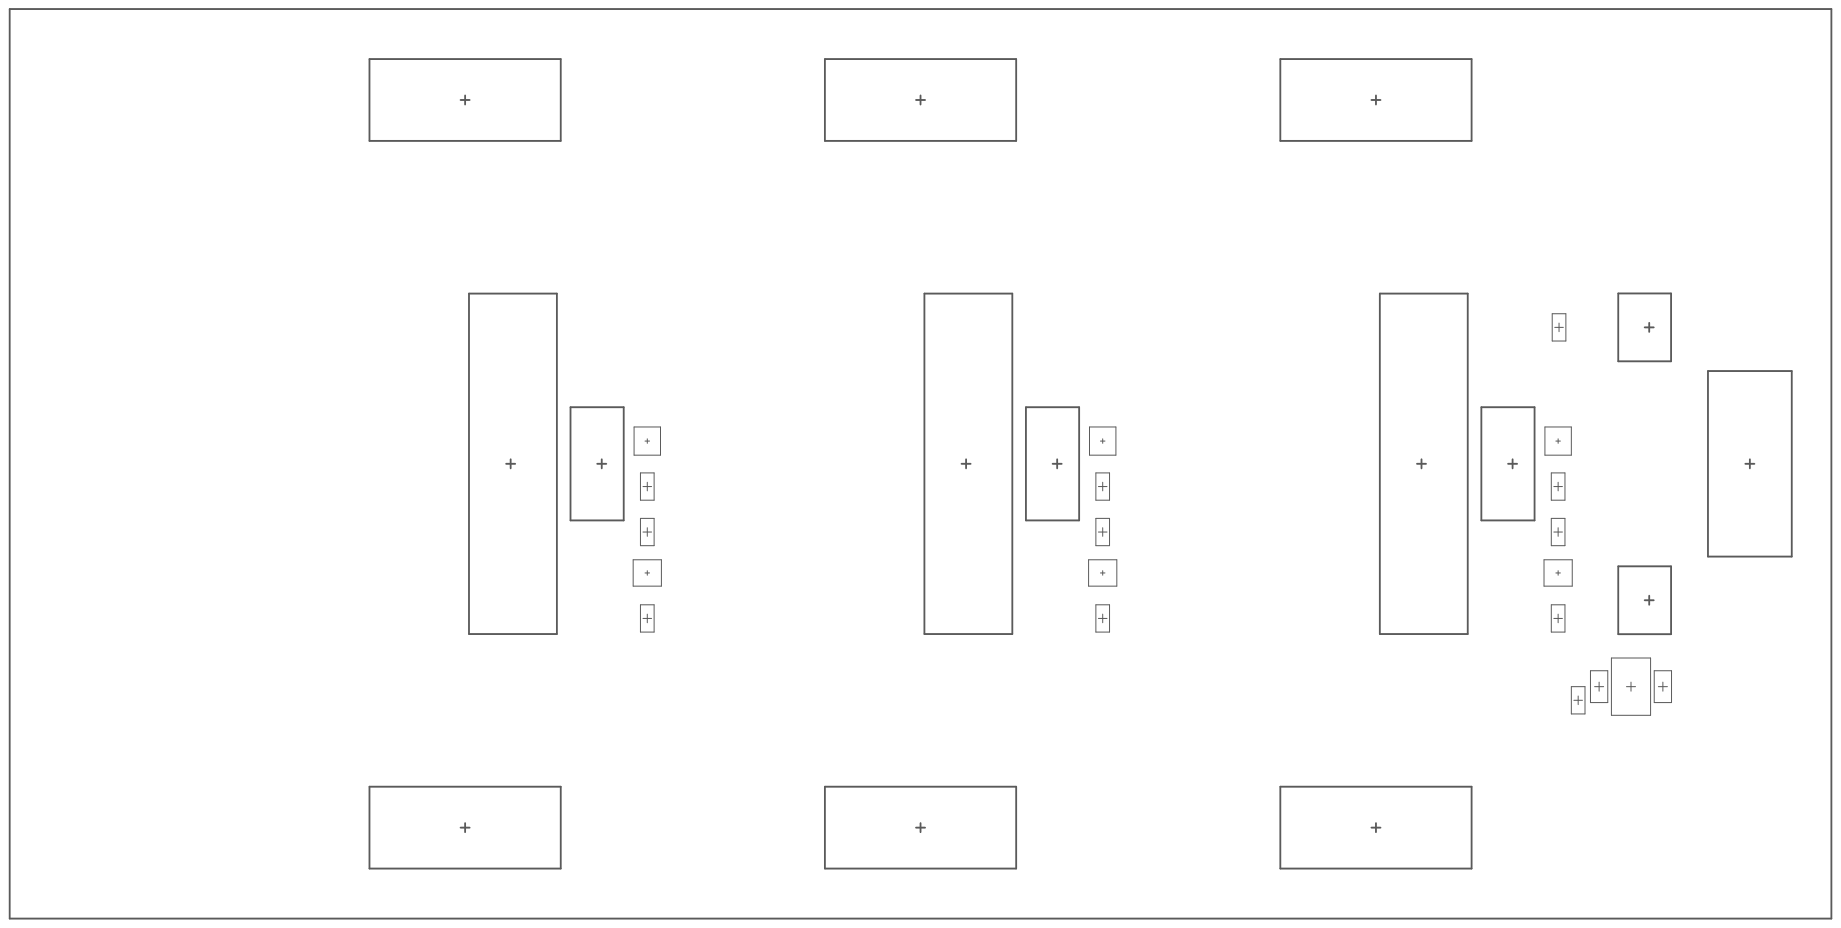
[picture p272: page 3]

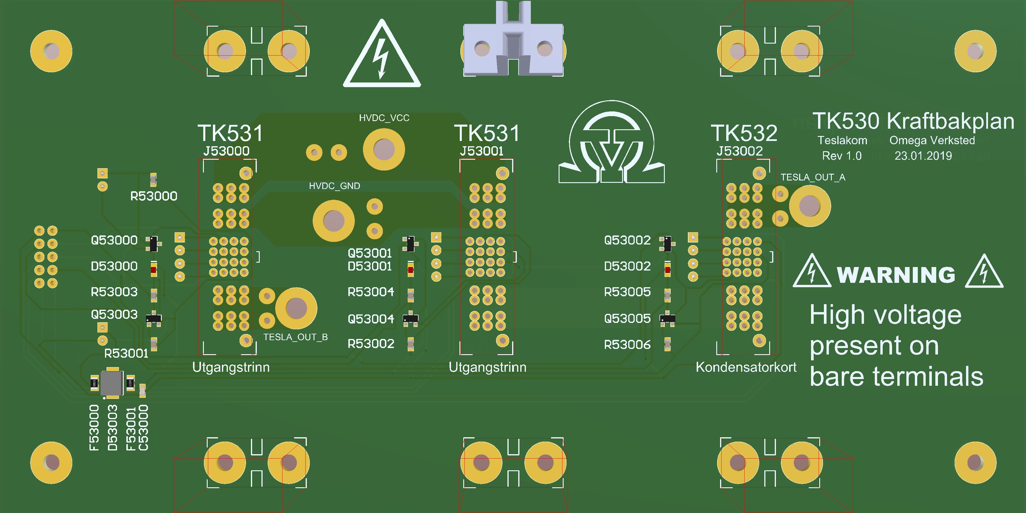
[picture p273: page 4]

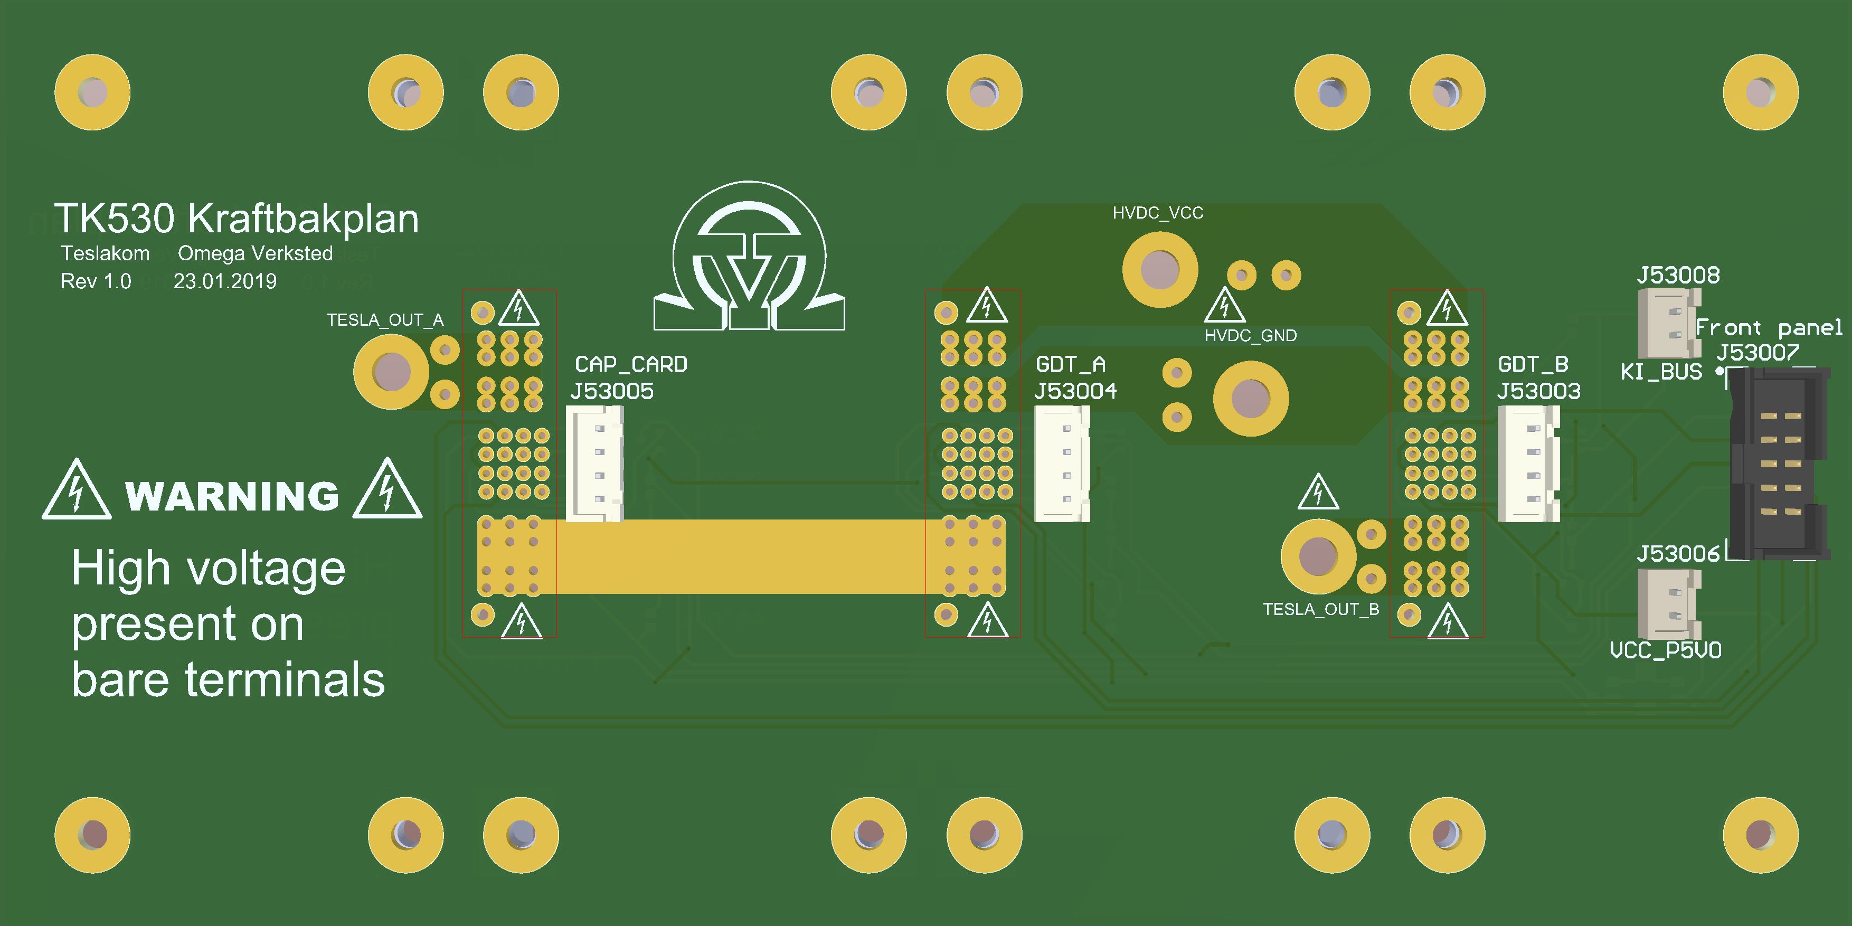
[picture p274: page 5]

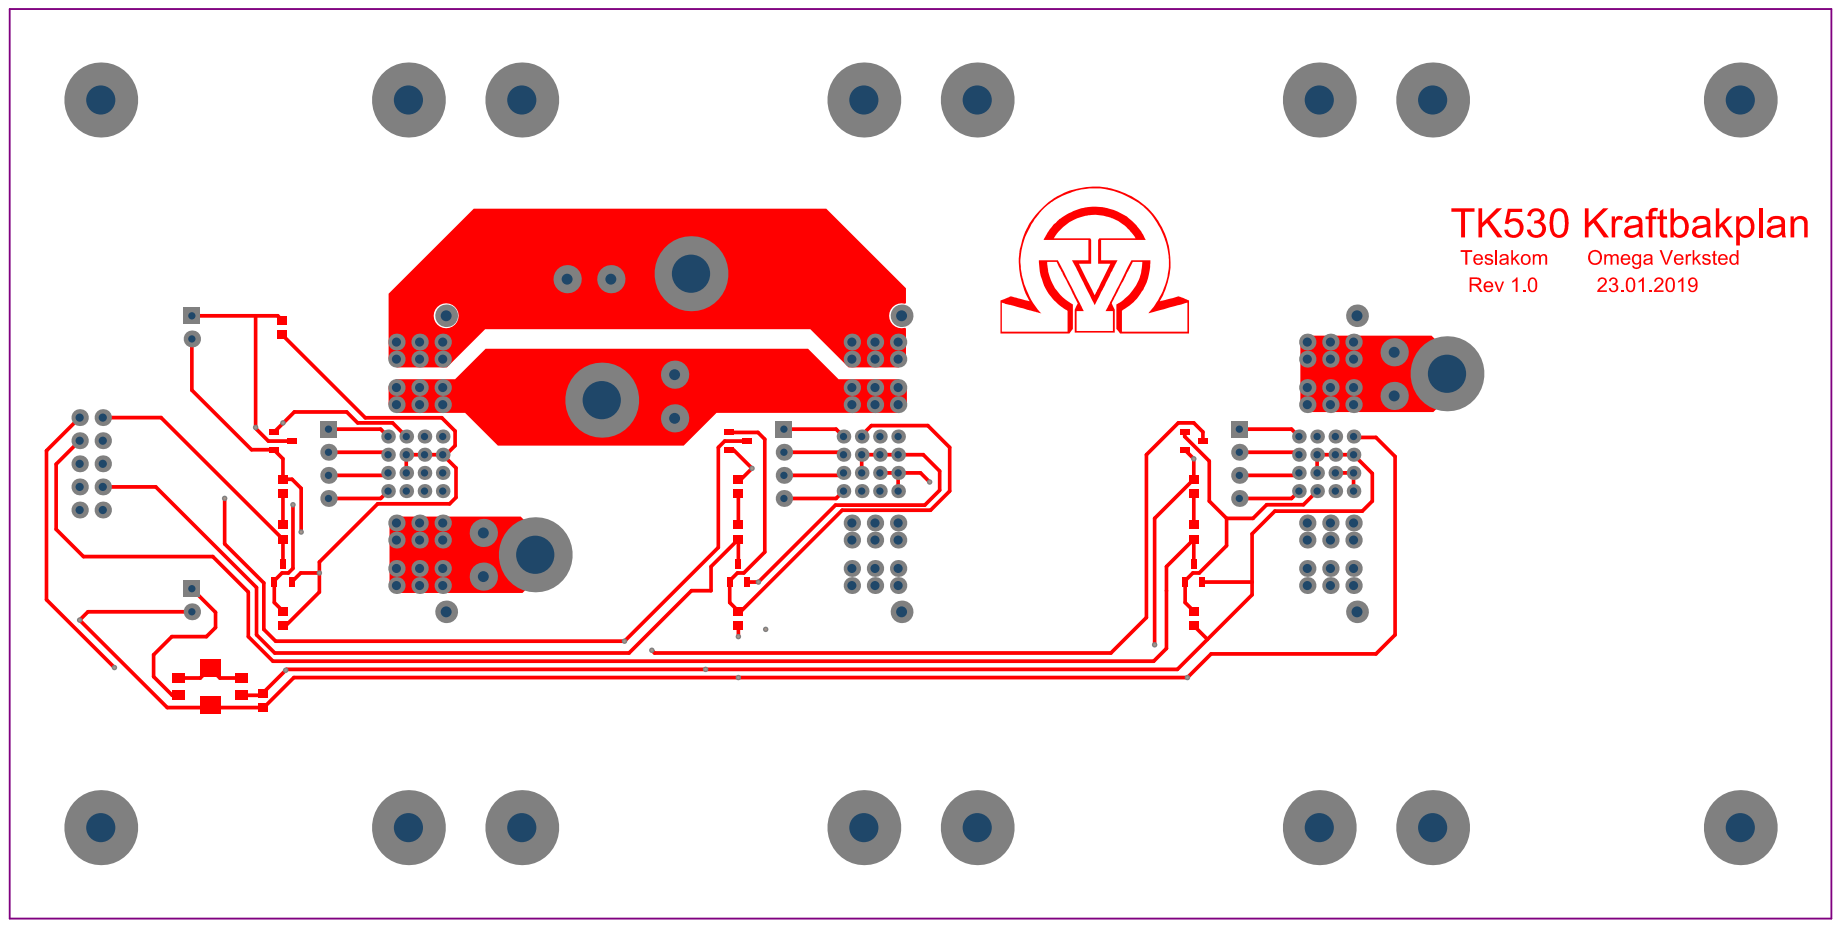
[picture p275: page 6]

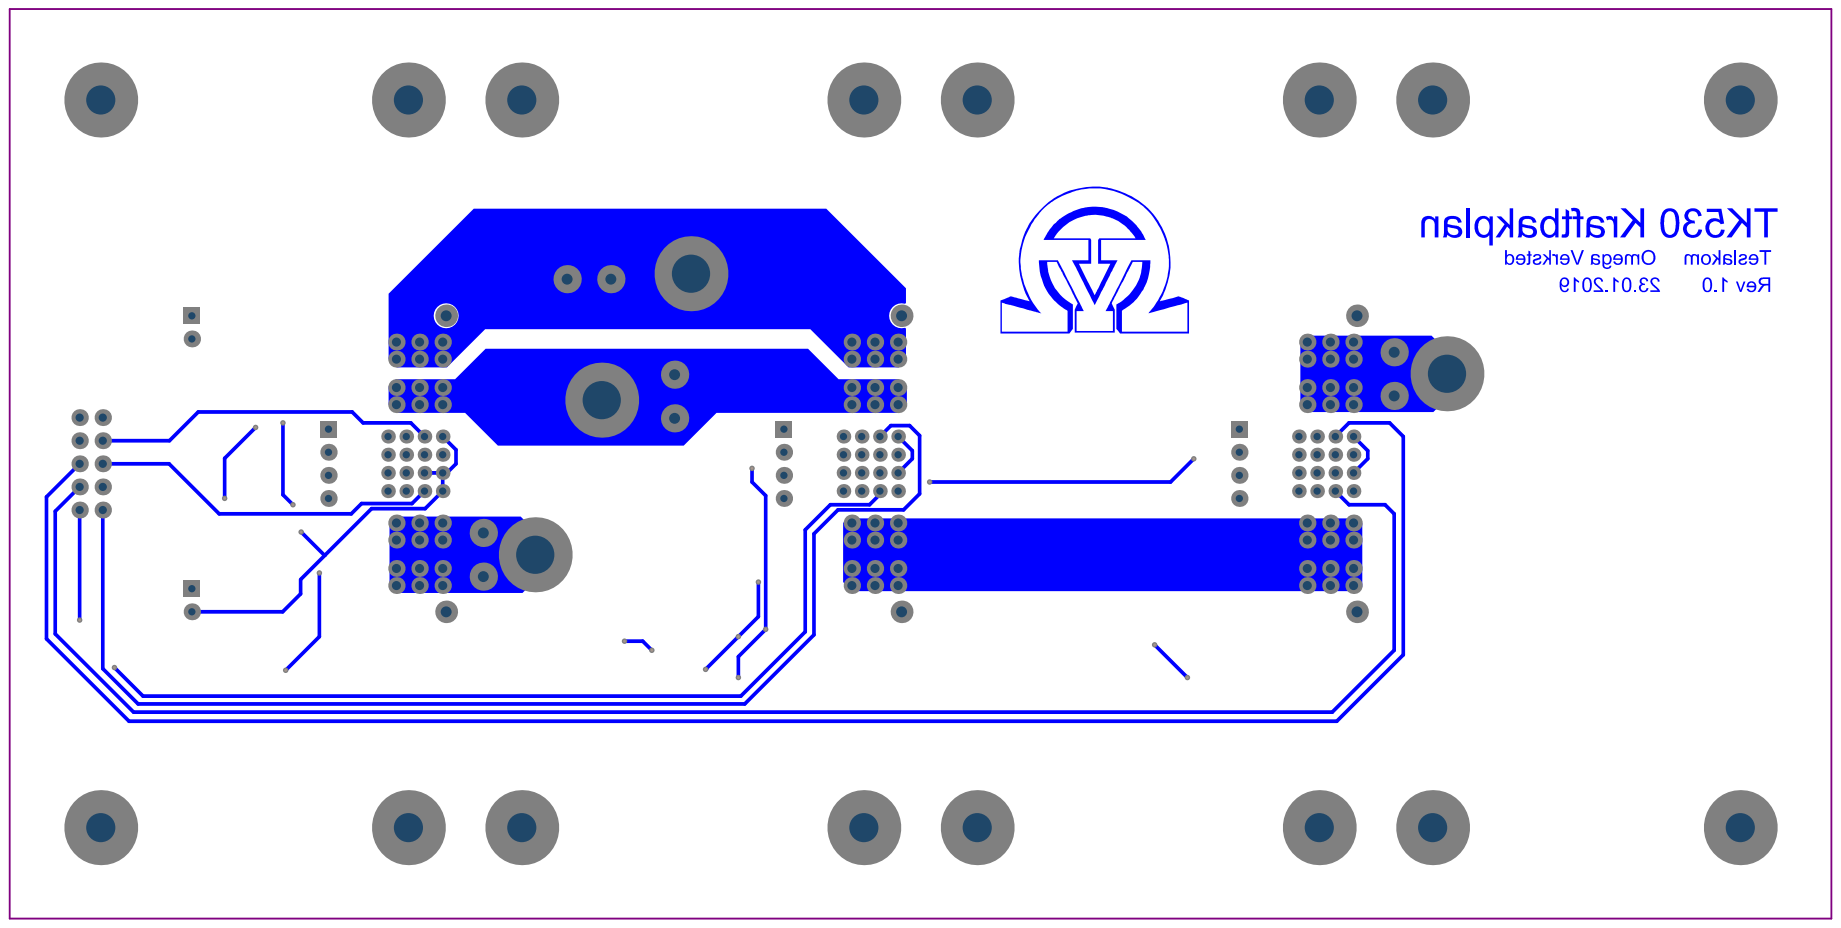
[picture p276: page 7]

Quantit y | Designator | navn | pakketyp e | leverando r | leverandor_var enr | pris | hylle | rad | kolonne | dybde | antall
3 | D53000, D53001, D53002 | SMD LED Red | 0603 | Farnell | 8554641 | 1 | 13 | 0 | 0 | 2 | 50
3 | Q53003, Q53004, Q53005 | BSH201 | SOT | Farnell | 1758073 | 3
3 | Q53000, Q53001, Q53002 | 2N7002 | SMD | Farnell | 1829184 | 2 | 4 | 2 | 3 | 0 | 100
3 | J53003, J53004, J53005 | JST 4pin | TH | | | 2
2 | J53006, J53008 | JST 2pin | TH | | | 2 | 10, [NoPa ram] | 3, [NoP aram ] | 0, [NoPara m] | 0, [NoPar am] | 100, [NoPar am]
3 | R53003, R53004, R53005 | 47R | 0603 | | | 0 | 6 | -1 | -1 | 1 | 100
1 | J53007 | Header Shrouded 2X5P | TH | | | 5
3 | J53000, J53001, J53002 | MPSC-02-16-02-7.70-03-L-V-LC | TH | | | 30
4 | R53000, R53001, R53002, R53006 | 10k | 0603 | Farnell | 2447230 | 0 | 6 | -1 | 0 | 72 | 100
1 | C53000 | 100nF | 0603 | Farnell | 1759122 | 1
2 | F53000, F53001 | MC36214 | 0805 | Farnell | 1861181 | 2
1 | D53003 | SMBJ5.0A-TR | SMD | Farnell | 9886311 | 1
6 | M53000, M53001, M53002, M53003, M53004, M53005 | KortStøtte 50mm | TH | | | 5
