Cable89/tesla-driver/01_Documentation/Forenklet skjema/TK513_Limiter(1).pdf

X10
