Cable89/tesla-driver/05_Hardware/TK500_Driver/TK510_Signalbakplan/TK510_Signalbakplan.VHD

------------------------------------------------------------
-- VHDL TK510_Signalbakplan
-- 2014 7 12 22 55 36
-- Created By "DXP VHDL Generator"
-- "Copyright (c) 2002-2014 Altium Limited"
-- Product Version: 14.3.11.33708
------------------------------------------------------------

------------------------------------------------------------
-- VHDL TK510_Signalbakplan
------------------------------------------------------------

Library IEEE;
Use     IEEE.std_logic_1164.all;

Entity TK510_Signalbakplan Is
  port
  (
    AUX1_SLOT0       : InOut STD_LOGIC;                      -- ObjectKind=Port|PrimaryId=AUX1_SLOT0
    AUX1_SLOT1       : InOut STD_LOGIC;                      -- ObjectKind=Port|PrimaryId=AUX1_SLOT1
    AUX1_SLOT2       : InOut STD_LOGIC;                      -- ObjectKind=Port|PrimaryId=AUX1_SLOT2
    AUX1_SLOT3       : InOut STD_LOGIC;                      -- ObjectKind=Port|PrimaryId=AUX1_SLOT3
    AUX1_SLOT4       : InOut STD_LOGIC;                      -- ObjectKind=Port|PrimaryId=AUX1_SLOT4
    AUX1_SLOT5       : InOut STD_LOGIC;                      -- ObjectKind=Port|PrimaryId=AUX1_SLOT5
    AUX2_SLOT0       : InOut STD_LOGIC;                      -- ObjectKind=Port|PrimaryId=AUX2_SLOT0
    AUX2_SLOT1       : InOut STD_LOGIC;                      -- ObjectKind=Port|PrimaryId=AUX2_SLOT1
    AUX2_SLOT2       : InOut STD_LOGIC;                      -- ObjectKind=Port|PrimaryId=AUX2_SLOT2
    AUX2_SLOT3       : InOut STD_LOGIC;                      -- ObjectKind=Port|PrimaryId=AUX2_SLOT3
    AUX2_SLOT4       : InOut STD_LOGIC;                      -- ObjectKind=Port|PrimaryId=AUX2_SLOT4
    AUX2_SLOT5       : InOut STD_LOGIC;                      -- ObjectKind=Port|PrimaryId=AUX2_SLOT5
    BUS_SLOT0        : InOut STD_LOGIC;                      -- ObjectKind=Port|PrimaryId=BUS_SLOT0
    BUS_SLOT1        : InOut STD_LOGIC;                      -- ObjectKind=Port|PrimaryId=BUS_SLOT1
    BUS_SLOT2        : InOut STD_LOGIC;                      -- ObjectKind=Port|PrimaryId=BUS_SLOT2
    BUS_SLOT3        : InOut STD_LOGIC;                      -- ObjectKind=Port|PrimaryId=BUS_SLOT3
    BUS_SLOT4        : InOut STD_LOGIC;                      -- ObjectKind=Port|PrimaryId=BUS_SLOT4
    BUS_SLOT5        : InOut STD_LOGIC;                      -- ObjectKind=Port|PrimaryId=BUS_SLOT5
    EKSTRA           : In    STD_LOGIC;                      -- ObjectKind=Port|PrimaryId=EKSTRA
    FRONT_IO         : InOut STD_LOGIC;                      -- ObjectKind=Port|PrimaryId=FRONT_IO
    FRONT_IO_SLOT0   : InOut STD_LOGIC;                      -- ObjectKind=Port|PrimaryId=FRONT_IO_SLOT0
    FRONT_IO_SLOT1   : InOut STD_LOGIC;                      -- ObjectKind=Port|PrimaryId=FRONT_IO_SLOT1
    FRONT_IO_SLOT2   : InOut STD_LOGIC;                      -- ObjectKind=Port|PrimaryId=FRONT_IO_SLOT2
    FRONT_IO_SLOT3   : InOut STD_LOGIC;                      -- ObjectKind=Port|PrimaryId=FRONT_IO_SLOT3
    FRONT_IO_SLOT4   : InOut STD_LOGIC;                      -- ObjectKind=Port|PrimaryId=FRONT_IO_SLOT4
    FRONT_IO_SLOT5   : InOut STD_LOGIC;                      -- ObjectKind=Port|PrimaryId=FRONT_IO_SLOT5
    FRONT_LEDS       : InOut STD_LOGIC;                      -- ObjectKind=Port|PrimaryId=FRONT_LEDS
    FRONT_LEDS_SLOT0 : InOut STD_LOGIC;                      -- ObjectKind=Port|PrimaryId=FRONT_LEDS_SLOT0
    FRONT_LEDS_SLOT1 : InOut STD_LOGIC;                      -- ObjectKind=Port|PrimaryId=FRONT_LEDS_SLOT1
    FRONT_LEDS_SLOT2 : InOut STD_LOGIC;                      -- ObjectKind=Port|PrimaryId=FRONT_LEDS_SLOT2
    FRONT_LEDS_SLOT3 : InOut STD_LOGIC;                      -- ObjectKind=Port|PrimaryId=FRONT_LEDS_SLOT3
    FRONT_LEDS_SLOT4 : InOut STD_LOGIC;                      -- ObjectKind=Port|PrimaryId=FRONT_LEDS_SLOT4
    FRONT_LEDS_SLOT5 : InOut STD_LOGIC;                      -- ObjectKind=Port|PrimaryId=FRONT_LEDS_SLOT5
    GATE_DRIVE_A     : Out   STD_LOGIC;                      -- ObjectKind=Port|PrimaryId=GATE DRIVE A
    GATE_DRIVE_B     : Out   STD_LOGIC;                      -- ObjectKind=Port|PrimaryId=GATE DRIVE B
    KI_SLOT0         : In    STD_LOGIC;                      -- ObjectKind=Port|PrimaryId=KI_SLOT0
    KI_SLOT1         : In    STD_LOGIC;                      -- ObjectKind=Port|PrimaryId=KI_SLOT1
    KI_SLOT2         : In    STD_LOGIC;                      -- ObjectKind=Port|PrimaryId=KI_SLOT2
    KI_SLOT3         : In    STD_LOGIC;                      -- ObjectKind=Port|PrimaryId=KI_SLOT3
    KI_SLOT4         : In    STD_LOGIC;                      -- ObjectKind=Port|PrimaryId=KI_SLOT4
    KI_SLOT5         : In    STD_LOGIC;                      -- ObjectKind=Port|PrimaryId=KI_SLOT5
    KI_SLOT6         : In    STD_LOGIC;                      -- ObjectKind=Port|PrimaryId=KI_SLOT6
    KI_SLOT7         : In    STD_LOGIC;                      -- ObjectKind=Port|PrimaryId=KI_SLOT7
    KI_SLOT8         : In    STD_LOGIC;                      -- ObjectKind=Port|PrimaryId=KI_SLOT8
    P5V0             : In    STD_LOGIC;                      -- ObjectKind=Port|PrimaryId=P5V0
    P18V             : In    STD_LOGIC                       -- ObjectKind=Port|PrimaryId=P18V
  );
  attribute MacroCell : boolean;

End TK510_Signalbakplan;
------------------------------------------------------------

------------------------------------------------------------
Architecture Structure Of TK510_Signalbakplan Is
   Component X_47R                                           -- ObjectKind=Part|PrimaryId=R51007|SecondaryId=1
      port
      (
        X_1 : inout STD_LOGIC;                               -- ObjectKind=Pin|PrimaryId=R51007-1
        X_2 : inout STD_LOGIC                                -- ObjectKind=Pin|PrimaryId=R51007-2
      );
   End Component;

   Component X_100k                                          -- ObjectKind=Part|PrimaryId=R51000|SecondaryId=1
      port
      (
        X_1 : inout STD_LOGIC;                               -- ObjectKind=Pin|PrimaryId=R51000-1
        X_2 : inout STD_LOGIC                                -- ObjectKind=Pin|PrimaryId=R51000-2
      );
   End Component;

   Component Header_Shrouded_2X5P                            -- ObjectKind=Part|PrimaryId=J51009|SecondaryId=1
      port
      (
        X_1  : inout STD_LOGIC;                              -- ObjectKind=Pin|PrimaryId=J51009-1
        X_2  : inout STD_LOGIC;                              -- ObjectKind=Pin|PrimaryId=J51009-2
        X_3  : inout STD_LOGIC;                              -- ObjectKind=Pin|PrimaryId=J51009-3
        X_4  : inout STD_LOGIC;                              -- ObjectKind=Pin|PrimaryId=J51009-4
        X_5  : inout STD_LOGIC;                              -- ObjectKind=Pin|PrimaryId=J51009-5
        X_6  : inout STD_LOGIC;                              -- ObjectKind=Pin|PrimaryId=J51009-6
        X_7  : inout STD_LOGIC;                              -- ObjectKind=Pin|PrimaryId=J51009-7
        X_8  : inout STD_LOGIC;                              -- ObjectKind=Pin|PrimaryId=J51009-8
        X_9  : inout STD_LOGIC;                              -- ObjectKind=Pin|PrimaryId=J51009-9
        X_10 : inout STD_LOGIC                               -- ObjectKind=Pin|PrimaryId=J51009-10
      );
   End Component;

   Component Header_Shrouded_2X17P                           -- ObjectKind=Part|PrimaryId=J51027|SecondaryId=1
      port
      (
        X_1  : inout STD_LOGIC;                              -- ObjectKind=Pin|PrimaryId=J51027-1
        X_2  : inout STD_LOGIC;                              -- ObjectKind=Pin|PrimaryId=J51027-2
        X_3  : inout STD_LOGIC;                              -- ObjectKind=Pin|PrimaryId=J51027-3
        X_4  : inout STD_LOGIC;                              -- ObjectKind=Pin|PrimaryId=J51027-4
        X_5  : inout STD_LOGIC;                              -- ObjectKind=Pin|PrimaryId=J51027-5
        X_6  : inout STD_LOGIC;                              -- ObjectKind=Pin|PrimaryId=J51027-6
        X_7  : inout STD_LOGIC;                              -- ObjectKind=Pin|PrimaryId=J51027-7
        X_8  : inout STD_LOGIC;                              -- ObjectKind=Pin|PrimaryId=J51027-8
        X_9  : inout STD_LOGIC;                              -- ObjectKind=Pin|PrimaryId=J51027-9
        X_10 : inout STD_LOGIC;                              -- ObjectKind=Pin|PrimaryId=J51027-10
        X_11 : inout STD_LOGIC;                              -- ObjectKind=Pin|PrimaryId=J51027-11
        X_12 : inout STD_LOGIC;                              -- ObjectKind=Pin|PrimaryId=J51027-12
        X_13 : inout STD_LOGIC;                              -- ObjectKind=Pin|PrimaryId=J51027-13
        X_14 : inout STD_LOGIC;                              -- ObjectKind=Pin|PrimaryId=J51027-14
        X_15 : inout STD_LOGIC;                              -- ObjectKind=Pin|PrimaryId=J51027-15
        X_16 : inout STD_LOGIC;                              -- ObjectKind=Pin|PrimaryId=J51027-16
        X_17 : inout STD_LOGIC;                              -- ObjectKind=Pin|PrimaryId=J51027-17
        X_18 : inout STD_LOGIC;                              -- ObjectKind=Pin|PrimaryId=J51027-18
        X_19 : inout STD_LOGIC;                              -- ObjectKind=Pin|PrimaryId=J51027-19
        X_20 : inout STD_LOGIC;                              -- ObjectKind=Pin|PrimaryId=J51027-20
        X_21 : inout STD_LOGIC;                              -- ObjectKind=Pin|PrimaryId=J51027-21
        X_22 : inout STD_LOGIC;                              -- ObjectKind=Pin|PrimaryId=J51027-22
        X_23 : inout STD_LOGIC;                              -- ObjectKind=Pin|PrimaryId=J51027-23
        X_24 : inout STD_LOGIC;                              -- ObjectKind=Pin|PrimaryId=J51027-24
        X_25 : inout STD_LOGIC;                              -- ObjectKind=Pin|PrimaryId=J51027-25
        X_26 : inout STD_LOGIC;                              -- ObjectKind=Pin|PrimaryId=J51027-26
        X_27 : inout STD_LOGIC;                              -- ObjectKind=Pin|PrimaryId=J51027-27
        X_28 : inout STD_LOGIC;                              -- ObjectKind=Pin|PrimaryId=J51027-28
        X_29 : inout STD_LOGIC;                              -- ObjectKind=Pin|PrimaryId=J51027-29
        X_30 : inout STD_LOGIC;                              -- ObjectKind=Pin|PrimaryId=J51027-30
        X_31 : inout STD_LOGIC;                              -- ObjectKind=Pin|PrimaryId=J51027-31
        X_32 : inout STD_LOGIC;                              -- ObjectKind=Pin|PrimaryId=J51027-32
        X_33 : inout STD_LOGIC;                              -- ObjectKind=Pin|PrimaryId=J51027-33
        X_34 : inout STD_LOGIC                               -- ObjectKind=Pin|PrimaryId=J51027-34
      );
   End Component;

   Component IRLML6402                                       -- ObjectKind=Part|PrimaryId=Q51003|SecondaryId=1
      port
      (
        X_1 : inout STD_LOGIC;                               -- ObjectKind=Pin|PrimaryId=Q51003-1
        X_2 : inout STD_LOGIC;                               -- ObjectKind=Pin|PrimaryId=Q51003-2
        X_3 : inout STD_LOGIC                                -- ObjectKind=Pin|PrimaryId=Q51003-3
      );
   End Component;

   Component JST_2pin                                        -- ObjectKind=Part|PrimaryId=J51012|SecondaryId=1
      port
      (
        X_1 : inout STD_LOGIC;                               -- ObjectKind=Pin|PrimaryId=J51012-1
        X_2 : inout STD_LOGIC                                -- ObjectKind=Pin|PrimaryId=J51012-2
      );
   End Component;

   Component PCI_ExpressMINUS36P                             -- ObjectKind=Part|PrimaryId=J51000|SecondaryId=1
      port
      (
        A1  : inout STD_LOGIC;                               -- ObjectKind=Pin|PrimaryId=J51000-A1
        A2  : inout STD_LOGIC;                               -- ObjectKind=Pin|PrimaryId=J51000-A2
        A3  : inout STD_LOGIC;                               -- ObjectKind=Pin|PrimaryId=J51000-A3
        A4  : inout STD_LOGIC;                               -- ObjectKind=Pin|PrimaryId=J51000-A4
        A5  : inout STD_LOGIC;                               -- ObjectKind=Pin|PrimaryId=J51000-A5
        A6  : inout STD_LOGIC;                               -- ObjectKind=Pin|PrimaryId=J51000-A6
        A7  : inout STD_LOGIC;                               -- ObjectKind=Pin|PrimaryId=J51000-A7
        A8  : inout STD_LOGIC;                               -- ObjectKind=Pin|PrimaryId=J51000-A8
        A9  : inout STD_LOGIC;                               -- ObjectKind=Pin|PrimaryId=J51000-A9
        A10 : inout STD_LOGIC;                               -- ObjectKind=Pin|PrimaryId=J51000-A10
        A11 : inout STD_LOGIC;                               -- ObjectKind=Pin|PrimaryId=J51000-A11
        A12 : inout STD_LOGIC;                               -- ObjectKind=Pin|PrimaryId=J51000-A12
        A13 : inout STD_LOGIC;                               -- ObjectKind=Pin|PrimaryId=J51000-A13
        A14 : inout STD_LOGIC;                               -- ObjectKind=Pin|PrimaryId=J51000-A14
        A15 : inout STD_LOGIC;                               -- ObjectKind=Pin|PrimaryId=J51000-A15
        A16 : inout STD_LOGIC;                               -- ObjectKind=Pin|PrimaryId=J51000-A16
        A17 : inout STD_LOGIC;                               -- ObjectKind=Pin|PrimaryId=J51000-A17
        A18 : inout STD_LOGIC;                               -- ObjectKind=Pin|PrimaryId=J51000-A18
        B1  : inout STD_LOGIC;                               -- ObjectKind=Pin|PrimaryId=J51000-B1
        B2  : inout STD_LOGIC;                               -- ObjectKind=Pin|PrimaryId=J51000-B2
        B3  : inout STD_LOGIC;                               -- ObjectKind=Pin|PrimaryId=J51000-B3
        B4  : inout STD_LOGIC;                               -- ObjectKind=Pin|PrimaryId=J51000-B4
        B5  : inout STD_LOGIC;                               -- ObjectKind=Pin|PrimaryId=J51000-B5
        B6  : inout STD_LOGIC;                               -- ObjectKind=Pin|PrimaryId=J51000-B6
        B7  : inout STD_LOGIC;                               -- ObjectKind=Pin|PrimaryId=J51000-B7
        B8  : inout STD_LOGIC;                               -- ObjectKind=Pin|PrimaryId=J51000-B8
        B9  : inout STD_LOGIC;                               -- ObjectKind=Pin|PrimaryId=J51000-B9
        B10 : inout STD_LOGIC;                               -- ObjectKind=Pin|PrimaryId=J51000-B10
        B11 : inout STD_LOGIC;                               -- ObjectKind=Pin|PrimaryId=J51000-B11
        B12 : inout STD_LOGIC;                               -- ObjectKind=Pin|PrimaryId=J51000-B12
        B13 : inout STD_LOGIC;                               -- ObjectKind=Pin|PrimaryId=J51000-B13
        B14 : inout STD_LOGIC;                               -- ObjectKind=Pin|PrimaryId=J51000-B14
        B15 : inout STD_LOGIC;                               -- ObjectKind=Pin|PrimaryId=J51000-B15
        B16 : inout STD_LOGIC;                               -- ObjectKind=Pin|PrimaryId=J51000-B16
        B17 : inout STD_LOGIC;                               -- ObjectKind=Pin|PrimaryId=J51000-B17
        B18 : inout STD_LOGIC                                -- ObjectKind=Pin|PrimaryId=J51000-B18
      );
   End Component;

   Component SMD_LED_Red                                     -- ObjectKind=Part|PrimaryId=D51000|SecondaryId=1
      port
      (
        X_1 : inout STD_LOGIC;                               -- ObjectKind=Pin|PrimaryId=D51000-1
        X_2 : inout STD_LOGIC                                -- ObjectKind=Pin|PrimaryId=D51000-2
      );
   End Component;

   Component TK510_Mekanisk                                  -- ObjectKind=Sheet Symbol|PrimaryId=TK510
   End Component;

   Component TSM2314                                         -- ObjectKind=Part|PrimaryId=Q51000|SecondaryId=1
      port
      (
        X_1 : inout STD_LOGIC;                               -- ObjectKind=Pin|PrimaryId=Q51000-1
        X_2 : inout STD_LOGIC;                               -- ObjectKind=Pin|PrimaryId=Q51000-2
        X_3 : inout STD_LOGIC                                -- ObjectKind=Pin|PrimaryId=Q51000-3
      );
   End Component;


    Signal NamedSignal_0_FE            : STD_LOGIC; -- ObjectKind=Net|PrimaryId=0_FE
    Signal NamedSignal_0_INT           : STD_LOGIC; -- ObjectKind=Net|PrimaryId=0_INT
    Signal NamedSignal_0_KI            : STD_LOGIC; -- ObjectKind=Net|PrimaryId=0_KI
    Signal NamedSignal_0_RES           : STD_LOGIC; -- ObjectKind=Net|PrimaryId=0_RES
    Signal NamedSignal_0_ST            : STD_LOGIC; -- ObjectKind=Net|PrimaryId=0_ST
    Signal NamedSignal_1_FE            : STD_LOGIC; -- ObjectKind=Net|PrimaryId=1_FE
    Signal NamedSignal_1_INT           : STD_LOGIC; -- ObjectKind=Net|PrimaryId=1_INT
    Signal NamedSignal_1_KI            : STD_LOGIC; -- ObjectKind=Net|PrimaryId=1_KI
    Signal NamedSignal_1_RES           : STD_LOGIC; -- ObjectKind=Net|PrimaryId=1_RES
    Signal NamedSignal_1_ST            : STD_LOGIC; -- ObjectKind=Net|PrimaryId=1_ST
    Signal NamedSignal_2_FE            : STD_LOGIC; -- ObjectKind=Net|PrimaryId=2_FE
    Signal NamedSignal_2_INT           : STD_LOGIC; -- ObjectKind=Net|PrimaryId=2_INT
    Signal NamedSignal_2_KI            : STD_LOGIC; -- ObjectKind=Net|PrimaryId=2_KI
    Signal NamedSignal_2_RES           : STD_LOGIC; -- ObjectKind=Net|PrimaryId=2_RES
    Signal NamedSignal_2_ST            : STD_LOGIC; -- ObjectKind=Net|PrimaryId=2_ST
    Signal NamedSignal_3_FE            : STD_LOGIC; -- ObjectKind=Net|PrimaryId=3_FE
    Signal NamedSignal_3_INT           : STD_LOGIC; -- ObjectKind=Net|PrimaryId=3_INT
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
   attribute Verified_date of Q51010 : Label is "";
   attribute Verified_date of Q51009 : Label is "";
   attribute Verified_date of Q51005 : Label is "";
   attribute Verified_date of Q51004 : Label is "";
   attribute Verified_date of Q51003 : Label is "";
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
