Cable89/tesla-driver/05_Hardware/TK500_Driver/ProjectOutputs/TK502_Frontpanel_LEDs.VHD

------------------------------------------------------------
-- VHDL TK502_Frontpanel_LEDs
-- 2017 1 13 17 4 7
-- Created By "DXP VHDL Generator"
-- "Copyright (c) 2002-2014 Altium Limited"
-- Product Version: 16.0.6.282
------------------------------------------------------------

------------------------------------------------------------
-- VHDL TK502_Frontpanel_LEDs
------------------------------------------------------------

Library IEEE;
Use     IEEE.std_logic_1164.all;

Entity TK502_Frontpanel_LEDs Is
  attribute MacroCell : boolean;

End TK502_Frontpanel_LEDs;
------------------------------------------------------------

------------------------------------------------------------
Architecture Structure Of TK502_Frontpanel_LEDs Is
   Component X_2076                                          -- ObjectKind=Part|PrimaryId=D50200|SecondaryId=1
      port
      (
        X_1 : inout STD_LOGIC;                               -- ObjectKind=Pin|PrimaryId=D50200-1
        X_2 : inout STD_LOGIC                                -- ObjectKind=Pin|PrimaryId=D50200-2
      );
   End Component;

   Component X_2226                                          -- ObjectKind=Part|PrimaryId=J50200|SecondaryId=1
      port
      (
        X_1 : inout STD_LOGIC;                               -- ObjectKind=Pin|PrimaryId=J50200-1
        X_2 : inout STD_LOGIC;                               -- ObjectKind=Pin|PrimaryId=J50200-2
        X_3 : inout STD_LOGIC                                -- ObjectKind=Pin|PrimaryId=J50200-3
      );
   End Component;

   Component X_2390                                          -- ObjectKind=Part|PrimaryId=J50206|SecondaryId=1
      port
      (
        X_1  : inout STD_LOGIC;                              -- ObjectKind=Pin|PrimaryId=J50206-1
        X_2  : inout STD_LOGIC;                              -- ObjectKind=Pin|PrimaryId=J50206-2
        X_3  : inout STD_LOGIC;                              -- ObjectKind=Pin|PrimaryId=J50206-3
        X_4  : inout STD_LOGIC;                              -- ObjectKind=Pin|PrimaryId=J50206-4
        X_5  : inout STD_LOGIC;                              -- ObjectKind=Pin|PrimaryId=J50206-5
        X_6  : inout STD_LOGIC;                              -- ObjectKind=Pin|PrimaryId=J50206-6
        X_7  : inout STD_LOGIC;                              -- ObjectKind=Pin|PrimaryId=J50206-7
        X_8  : inout STD_LOGIC;                              -- ObjectKind=Pin|PrimaryId=J50206-8
        X_9  : inout STD_LOGIC;                              -- ObjectKind=Pin|PrimaryId=J50206-9
        X_10 : inout STD_LOGIC;                              -- ObjectKind=Pin|PrimaryId=J50206-10
        X_11 : inout STD_LOGIC;                              -- ObjectKind=Pin|PrimaryId=J50206-11
        X_12 : inout STD_LOGIC;                              -- ObjectKind=Pin|PrimaryId=J50206-12
        X_13 : inout STD_LOGIC;                              -- ObjectKind=Pin|PrimaryId=J50206-13
        X_14 : inout STD_LOGIC;                              -- ObjectKind=Pin|PrimaryId=J50206-14
        X_15 : inout STD_LOGIC;                              -- ObjectKind=Pin|PrimaryId=J50206-15
        X_16 : inout STD_LOGIC;                              -- ObjectKind=Pin|PrimaryId=J50206-16
        X_17 : inout STD_LOGIC;                              -- ObjectKind=Pin|PrimaryId=J50206-17
        X_18 : inout STD_LOGIC;                              -- ObjectKind=Pin|PrimaryId=J50206-18
        X_19 : inout STD_LOGIC;                              -- ObjectKind=Pin|PrimaryId=J50206-19
        X_20 : inout STD_LOGIC;                              -- ObjectKind=Pin|PrimaryId=J50206-20
        X_21 : inout STD_LOGIC;                              -- ObjectKind=Pin|PrimaryId=J50206-21
        X_22 : inout STD_LOGIC;                              -- ObjectKind=Pin|PrimaryId=J50206-22
        X_23 : inout STD_LOGIC;                              -- ObjectKind=Pin|PrimaryId=J50206-23
        X_24 : inout STD_LOGIC;                              -- ObjectKind=Pin|PrimaryId=J50206-24
        X_25 : inout STD_LOGIC;                              -- ObjectKind=Pin|PrimaryId=J50206-25
        X_26 : inout STD_LOGIC;                              -- ObjectKind=Pin|PrimaryId=J50206-26
        X_27 : inout STD_LOGIC;                              -- ObjectKind=Pin|PrimaryId=J50206-27
        X_28 : inout STD_LOGIC;                              -- ObjectKind=Pin|PrimaryId=J50206-28
        X_29 : inout STD_LOGIC;                              -- ObjectKind=Pin|PrimaryId=J50206-29
        X_30 : inout STD_LOGIC;                              -- ObjectKind=Pin|PrimaryId=J50206-30
        X_31 : inout STD_LOGIC;                              -- ObjectKind=Pin|PrimaryId=J50206-31
        X_32 : inout STD_LOGIC;                              -- ObjectKind=Pin|PrimaryId=J50206-32
        X_33 : inout STD_LOGIC;                              -- ObjectKind=Pin|PrimaryId=J50206-33
        X_34 : inout STD_LOGIC                               -- ObjectKind=Pin|PrimaryId=J50206-34
      );
   End Component;

   Component X_2444                                          -- ObjectKind=Part|PrimaryId=R50200|SecondaryId=1
      port
      (
        X_1 : inout STD_LOGIC;                               -- ObjectKind=Pin|PrimaryId=R50200-1
        X_2 : inout STD_LOGIC                                -- ObjectKind=Pin|PrimaryId=R50200-2
      );
   End Component;

   Component X_2448                                          -- ObjectKind=Part|PrimaryId=R50202|SecondaryId=1
      port
      (
        X_1 : inout STD_LOGIC;                               -- ObjectKind=Pin|PrimaryId=R50202-1
        X_2 : inout STD_LOGIC                                -- ObjectKind=Pin|PrimaryId=R50202-2
      );
   End Component;

   Component X_3186                                          -- ObjectKind=Part|PrimaryId=R50224|SecondaryId=1
      port
      (
        X_1 : inout STD_LOGIC;                               -- ObjectKind=Pin|PrimaryId=R50224-1
        X_2 : inout STD_LOGIC                                -- ObjectKind=Pin|PrimaryId=R50224-2
      );
   End Component;

   Component X_3597                                          -- ObjectKind=Part|PrimaryId=D50201|SecondaryId=1
      port
      (
        X_1 : inout STD_LOGIC;                               -- ObjectKind=Pin|PrimaryId=D50201-1
        X_2 : inout STD_LOGIC                                -- ObjectKind=Pin|PrimaryId=D50201-2
      );
   End Component;


    Signal NamedSignal_0_FE     : STD_LOGIC; -- ObjectKind=Net|PrimaryId=0_FE
    Signal NamedSignal_0_INT    : STD_LOGIC; -- ObjectKind=Net|PrimaryId=0_INT
    Signal NamedSignal_0_KI     : STD_LOGIC; -- ObjectKind=Net|PrimaryId=0_KI
    Signal NamedSignal_0_KNP    : STD_LOGIC; -- ObjectKind=Net|PrimaryId=0_KNP
    Signal NamedSignal_0_ST     : STD_LOGIC; -- ObjectKind=Net|PrimaryId=0_ST
    Signal NamedSignal_1_FE     : STD_LOGIC; -- ObjectKind=Net|PrimaryId=1_FE
    Signal NamedSignal_1_INT    : STD_LOGIC; -- ObjectKind=Net|PrimaryId=1_INT
    Signal NamedSignal_1_KI     : STD_LOGIC; -- ObjectKind=Net|PrimaryId=1_KI
    Signal NamedSignal_1_KNP    : STD_LOGIC; -- ObjectKind=Net|PrimaryId=1_KNP
    Signal NamedSignal_1_ST     : STD_LOGIC; -- ObjectKind=Net|PrimaryId=1_ST
    Signal NamedSignal_2_FE     : STD_LOGIC; -- ObjectKind=Net|PrimaryId=2_FE
    Signal NamedSignal_2_INT    : STD_LOGIC; -- ObjectKind=Net|PrimaryId=2_INT
    Signal NamedSignal_2_KI     : STD_LOGIC; -- ObjectKind=Net|PrimaryId=2_KI
    Signal NamedSignal_2_KNP    : STD_LOGIC; -- ObjectKind=Net|PrimaryId=2_KNP
    Signal NamedSignal_2_ST     : STD_LOGIC; -- ObjectKind=Net|PrimaryId=2_ST
    Signal NamedSignal_3_FE     : STD_LOGIC; -- ObjectKind=Net|PrimaryId=3_FE
    Signal NamedSignal_3_INT    : STD_LOGIC; -- ObjectKind=Net|PrimaryId=3_INT
    Signal NamedSignal_3_KI     : STD_LOGIC; -- ObjectKind=Net|PrimaryId=3_KI
    Signal NamedSignal_3_KNP    : STD_LOGIC; -- ObjectKind=Net|PrimaryId=3_KNP
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
   attribute antall of R50205 : Label is "100";
   attribute antall of R50204 : Label is "100";
   attribute antall of R50203 : Label is "100";
   attribute antall of R50202 : Label is "100";
   attribute antall of R50201 : Label is "100";
   attribute antall of R50200 : Label is "100";

   attribute beskrivelse : string;
   attribute beskrivelse of D50217 : Label is "LED, Green, 5mm, 572 nm, 2.1 V, 20 mA, 150 mcd";
   attribute beskrivelse of D50216 : Label is "LED, Red, 5mm, 643 nm, 1.8 V, 20 mA, 400 mcd";
   attribute beskrivelse of D50215 : Label is "LED, Green, 5mm, 572 nm, 2.1 V, 20 mA, 150 mcd";
   attribute beskrivelse of D50214 : Label is "LED, Green, 5mm, 572 nm, 2.1 V, 20 mA, 150 mcd";
   attribute beskrivelse of D50213 : Label is "LED, Red, 5mm, 643 nm, 1.8 V, 20 mA, 400 mcd";
   attribute beskrivelse of D50212 : Label is "LED, Green, 5mm, 572 nm, 2.1 V, 20 mA, 150 mcd";
   attribute beskrivelse of D50211 : Label is "LED, Green, 5mm, 572 nm, 2.1 V, 20 mA, 150 mcd";
   attribute beskrivelse of D50210 : Label is "LED, Red, 5mm, 643 nm, 1.8 V, 20 mA, 400 mcd";
   attribute beskrivelse of D50209 : Label is "LED, Green, 5mm, 572 nm, 2.1 V, 20 mA, 150 mcd";
   attribute beskrivelse of D50208 : Label is "LED, Green, 5mm, 572 nm, 2.1 V, 20 mA, 150 mcd";
   attribute beskrivelse of D50207 : Label is "LED, Red, 5mm, 643 nm, 1.8 V, 20 mA, 400 mcd";
   attribute beskrivelse of D50206 : Label is "LED, Green, 5mm, 572 nm, 2.1 V, 20 mA, 150 mcd";
   attribute beskrivelse of D50205 : Label is "LED, Green, 5mm, 572 nm, 2.1 V, 20 mA, 150 mcd";
   attribute beskrivelse of D50204 : Label is "LED, Red, 5mm, 643 nm, 1.8 V, 20 mA, 400 mcd";
   attribute beskrivelse of D50203 : Label is "LED, Green, 5mm, 572 nm, 2.1 V, 20 mA, 150 mcd";
   attribute beskrivelse of D50202 : Label is "LED, Green, 5mm, 572 nm, 2.1 V, 20 mA, 150 mcd";
   attribute beskrivelse of D50201 : Label is "LED, Red, 5mm, 643 nm, 1.8 V, 20 mA, 400 mcd";
   attribute beskrivelse of D50200 : Label is "LED, Green, 5mm, 572 nm, 2.1 V, 20 mA, 150 mcd";

   attribute Database_Table_Name : string;
   attribute Database_Table_Name of R50229 : Label is "altium_Motstander";
   attribute Database_Table_Name of R50228 : Label is "altium_Motstander";
   attribute Database_Table_Name of R50227 : Label is "altium_Motstander";
   attribute Database_Table_Name of R50226 : Label is "altium_Motstander";
   attribute Database_Table_Name of R50225 : Label is "altium_Motstander";
   attribute Database_Table_Name of R50224 : Label is "altium_Motstander";
   attribute Database_Table_Name of R50223 : Label is "altium_Motstander";
   attribute Database_Table_Name of R50222 : Label is "altium_Motstander";
   attribute Database_Table_Name of R50221 : Label is "altium_Motstander";
   attribute Database_Table_Name of R50220 : Label is "altium_Motstander";
   attribute Database_Table_Name of R50219 : Label is "altium_Motstander";
   attribute Database_Table_Name of R50218 : Label is "altium_Motstander";
   attribute Database_Table_Name of R50217 : Label is "altium_Motstander";
   attribute Database_Table_Name of R50216 : Label is "altium_Motstander";
   attribute Database_Table_Name of R50215 : Label is "altium_Motstander";
   attribute Database_Table_Name of R50214 : Label is "altium_Motstander";
   attribute Database_Table_Name of R50213 : Label is "altium_Motstander";
   attribute Database_Table_Name of R50212 : Label is "altium_Motstander";
   attribute Database_Table_Name of R50211 : Label is "altium_Motstander";
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
   attribute leverandor of D50204 : Label is "Farnell";
   attribute leverandor of D50203 : Label is "Farnell";
   attribute leverandor of D50202 : Label is "Farnell";
   attribute leverandor of D50201 : Label is "Farnell";
   attribute leverandor of D50200 : Label is "Farnell";

   attribute leverandor_varenr : string;
   attribute leverandor_varenr of R50217 : Label is "2447230";
   attribute leverandor_varenr of R50216 : Label is "2447230";
   attribute leverandor_varenr of R50209 : Label is "2447230";
   attribute leverandor_varenr of R50208 : Label is "2447230";
   attribute leverandor_varenr of R50201 : Label is "2447230";
   attribute leverandor_varenr of R50200 : Label is "2447230";
   attribute leverandor_varenr of D50217 : Label is "2112108";
   attribute leverandor_varenr of D50216 : Label is "2112111";
   attribute leverandor_varenr of D50215 : Label is "2112108";
   attribute leverandor_varenr of D50214 : Label is "2112108";
   attribute leverandor_varenr of D50213 : Label is "2112111";
   attribute leverandor_varenr of D50212 : Label is "2112108";
   attribute leverandor_varenr of D50211 : Label is "2112108";
   attribute leverandor_varenr of D50210 : Label is "2112111";
   attribute leverandor_varenr of D50209 : Label is "2112108";
   attribute leverandor_varenr of D50208 : Label is "2112108";
   attribute leverandor_varenr of D50207 : Label is "2112111";
   attribute leverandor_varenr of D50206 : Label is "2112108";
   attribute leverandor_varenr of D50205 : Label is "2112108";
   attribute leverandor_varenr of D50204 : Label is "2112111";
   attribute leverandor_varenr of D50203 : Label is "2112108";
   attribute leverandor_varenr of D50202 : Label is "2112108";
   attribute leverandor_varenr of D50201 : Label is "2112111";
   attribute leverandor_varenr of D50200 : Label is "2112108";

   attribute navn : string;
   attribute navn of R50229 : Label is "0R";
   attribute navn of R50228 : Label is "0R";
   attribute navn of R50227 : Label is "0R";
   attribute navn of R50226 : Label is "0R";
   attribute navn of R50225 : Label is "0R";
   attribute navn of R50224 : Label is "0R";
   attribute navn of R50223 : Label is "330R";
   attribute navn of R50222 : Label is "330R";
   attribute navn of R50221 : Label is "330R";
   attribute navn of R50220 : Label is "330R";
   attribute navn of R50219 : Label is "330R";
   attribute navn of R50218 : Label is "330R";
   attribute navn of R50217 : Label is "10k";
   attribute navn of R50216 : Label is "10k";
   attribute navn of R50215 : Label is "330R";
   attribute navn of R50214 : Label is "330R";
   attribute navn of R50213 : Label is "330R";
   attribute navn of R50212 : Label is "330R";
   attribute navn of R50211 : Label is "330R";
   attribute navn of R50210 : Label is "330R";
   attribute navn of R50209 : Label is "10k";
   attribute navn of R50208 : Label is "10k";
   attribute navn of R50207 : Label is "330R";
   attribute navn of R50206 : Label is "330R";
   attribute navn of R50205 : Label is "330R";
   attribute navn of R50204 : Label is "330R";
   attribute navn of R50203 : Label is "330R";
   attribute navn of R50202 : Label is "330R";
   attribute navn of R50201 : Label is "10k";
   attribute navn of R50200 : Label is "10k";
   attribute navn of J50206 : Label is "Header Shrouded 2X17P";
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
      Port Map
      (
        X_1 => NamedSignal_0_KNP,                            -- ObjectKind=Pin|PrimaryId=R50200-1
        X_2 => PowerSignal_VCC_P5V0                          -- ObjectKind=Pin|PrimaryId=R50200-2
      );

    J50206 : X_2390                                          -- ObjectKind=Part|PrimaryId=J50206|SecondaryId=1
      Port Map
      (
        X_1  => NamedSignal_2_KNP,                           -- ObjectKind=Pin|PrimaryId=J50206-1
        X_2  => NamedSignal_3_KI,                            -- ObjectKind=Pin|PrimaryId=J50206-2
        X_3  => NamedSignal_2_INT,                           -- ObjectKind=Pin|PrimaryId=J50206-3
        X_4  => NamedSignal_3_FE,                            -- ObjectKind=Pin|PrimaryId=J50206-4
        X_5  => NamedSignal_2_ST,                            -- ObjectKind=Pin|PrimaryId=J50206-5
        X_6  => NamedSignal_3_ST,                            -- ObjectKind=Pin|PrimaryId=J50206-6
        X_7  => NamedSignal_2_FE,                            -- ObjectKind=Pin|PrimaryId=J50206-7
        X_8  => NamedSignal_3_INT,                           -- ObjectKind=Pin|PrimaryId=J50206-8
        X_9  => NamedSignal_2_KI,                            -- ObjectKind=Pin|PrimaryId=J50206-9
        X_10 => NamedSignal_3_KNP,                           -- ObjectKind=Pin|PrimaryId=J50206-10
        X_11 => NamedSignal_1_KNP,                           -- ObjectKind=Pin|PrimaryId=J50206-11
        X_12 => NamedSignal_4_KI,                            -- ObjectKind=Pin|PrimaryId=J50206-12
        X_13 => NamedSignal_1_INT,                           -- ObjectKind=Pin|PrimaryId=J50206-13
        X_14 => NamedSignal_4_FE,                            -- ObjectKind=Pin|PrimaryId=J50206-14
        X_15 => NamedSignal_1_ST,                            -- ObjectKind=Pin|PrimaryId=J50206-15
        X_16 => NamedSignal_4_ST,                            -- ObjectKind=Pin|PrimaryId=J50206-16
        X_17 => NamedSignal_1_FE,                            -- ObjectKind=Pin|PrimaryId=J50206-17
        X_18 => NamedSignal_4_INT,                           -- ObjectKind=Pin|PrimaryId=J50206-18
        X_19 => NamedSignal_1_KI,                            -- ObjectKind=Pin|PrimaryId=J50206-19
        X_20 => NamedSignal_4_KNP,                           -- ObjectKind=Pin|PrimaryId=J50206-20
        X_21 => NamedSignal_0_KNP,                           -- ObjectKind=Pin|PrimaryId=J50206-21
        X_22 => NamedSignal_5_KI,                            -- ObjectKind=Pin|PrimaryId=J50206-22
        X_23 => NamedSignal_0_INT,                           -- ObjectKind=Pin|PrimaryId=J50206-23
        X_24 => NamedSignal_5_FE,                            -- ObjectKind=Pin|PrimaryId=J50206-24
        X_25 => NamedSignal_0_ST,                            -- ObjectKind=Pin|PrimaryId=J50206-25
        X_26 => NamedSignal_5_ST,                            -- ObjectKind=Pin|PrimaryId=J50206-26
        X_27 => NamedSignal_0_FE,                            -- ObjectKind=Pin|PrimaryId=J50206-27
        X_28 => NamedSignal_5_INT,                           -- ObjectKind=Pin|PrimaryId=J50206-28
        X_29 => NamedSignal_0_KI,                            -- ObjectKind=Pin|PrimaryId=J50206-29
        X_30 => NamedSignal_5_KNP,                           -- ObjectKind=Pin|PrimaryId=J50206-30
        X_31 => PowerSignal_VCC_P5V0,                        -- ObjectKind=Pin|PrimaryId=J50206-31
        X_32 => PowerSignal_GND,                             -- ObjectKind=Pin|PrimaryId=J50206-32
        X_33 => PowerSignal_VCC_P5V0,                        -- ObjectKind=Pin|PrimaryId=J50206-33
        X_34 => PowerSignal_GND                              -- ObjectKind=Pin|PrimaryId=J50206-34
      );

    J50205 : X_2226                                          -- ObjectKind=Part|PrimaryId=J50205|SecondaryId=1
      Port Map
      (
        X_1 => PinSignal_J50205_1,                           -- ObjectKind=Pin|PrimaryId=J50205-1
        X_2 => NamedSignal_5_KNP,                            -- ObjectKind=Pin|PrimaryId=J50205-2
        X_3 => PowerSignal_GND                               -- ObjectKind=Pin|PrimaryId=J50205-3
      );

    J50204 : X_2226                                          -- ObjectKind=Part|PrimaryId=J50204|SecondaryId=1
      Port Map
      (
        X_1 => PinSignal_J50204_1,                           -- ObjectKind=Pin|PrimaryId=J50204-1
        X_2 => NamedSignal_4_KNP,                            -- ObjectKind=Pin|PrimaryId=J50204-2
        X_3 => PowerSignal_GND                               -- ObjectKind=Pin|PrimaryId=J50204-3
      );

    J50203 : X_2226                                          -- ObjectKind=Part|PrimaryId=J50203|SecondaryId=1
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
      Port Map
      (
        X_1 => PinSignal_D50203_1,                           -- ObjectKind=Pin|PrimaryId=D50203-1
        X_2 => PowerSignal_GND                               -- ObjectKind=Pin|PrimaryId=D50203-2
      );

    D50202 : X_2076                                          -- ObjectKind=Part|PrimaryId=D50202|SecondaryId=1
      Port Map
      (
        X_1 => PinSignal_D50202_1,                           -- ObjectKind=Pin|PrimaryId=D50202-1
        X_2 => PowerSignal_GND                               -- ObjectKind=Pin|PrimaryId=D50202-2
      );

    D50201 : X_3597                                          -- ObjectKind=Part|PrimaryId=D50201|SecondaryId=1
      Port Map
      (
        X_1 => PinSignal_D50201_1,                           -- ObjectKind=Pin|PrimaryId=D50201-1
        X_2 => PowerSignal_GND                               -- ObjectKind=Pin|PrimaryId=D50201-2
      );

    D50200 : X_2076                                          -- ObjectKind=Part|PrimaryId=D50200|SecondaryId=1
      Port Map
      (
        X_1 => PinSignal_D50200_1,                           -- ObjectKind=Pin|PrimaryId=D50200-1
        X_2 => PowerSignal_GND                               -- ObjectKind=Pin|PrimaryId=D50200-2
      );

    -- Signal Assignments
    ---------------------
    PowerSignal_GND <= '0'; -- ObjectKind=Net|PrimaryId=GND

End Structure;
------------------------------------------------------------
