Cable89/tesla-driver/05_Hardware/TK500_Driver/ProjectOutputs/TK510_Mekanisk.VHD

------------------------------------------------------------
-- VHDL TK510_Mekanisk
-- 2017 1 13 17 4 7
-- Created By "DXP VHDL Generator"
-- "Copyright (c) 2002-2014 Altium Limited"
-- Product Version: 16.0.6.282
------------------------------------------------------------

------------------------------------------------------------
-- VHDL TK510_Mekanisk
------------------------------------------------------------

Library IEEE;
Use     IEEE.std_logic_1164.all;

Entity TK510_Mekanisk Is
  attribute MacroCell : boolean;

End TK510_Mekanisk;
------------------------------------------------------------

------------------------------------------------------------
Architecture Structure Of TK510_Mekanisk Is
   Component X_2392                                          -- ObjectKind=Part|PrimaryId=M51000|SecondaryId=1
   End Component;



   attribute antall : string;
   attribute antall of M51017 : Label is "30";
   attribute antall of M51016 : Label is "30";
   attribute antall of M51015 : Label is "30";
   attribute antall of M51014 : Label is "30";
   attribute antall of M51013 : Label is "30";
   attribute antall of M51012 : Label is "30";
   attribute antall of M51011 : Label is "30";
   attribute antall of M51010 : Label is "30";
   attribute antall of M51009 : Label is "30";
   attribute antall of M51008 : Label is "30";
   attribute antall of M51007 : Label is "30";
   attribute antall of M51006 : Label is "30";
   attribute antall of M51005 : Label is "30";
   attribute antall of M51004 : Label is "30";
   attribute antall of M51003 : Label is "30";
   attribute antall of M51002 : Label is "30";
   attribute antall of M51001 : Label is "30";
   attribute antall of M51000 : Label is "30";

   attribute Database_Table_Name : string;
   attribute Database_Table_Name of M51017 : Label is "altium";
   attribute Database_Table_Name of M51016 : Label is "altium";
   attribute Database_Table_Name of M51015 : Label is "altium";
   attribute Database_Table_Name of M51014 : Label is "altium";
   attribute Database_Table_Name of M51013 : Label is "altium";
   attribute Database_Table_Name of M51012 : Label is "altium";
   attribute Database_Table_Name of M51011 : Label is "altium";
   attribute Database_Table_Name of M51010 : Label is "altium";
   attribute Database_Table_Name of M51009 : Label is "altium";
   attribute Database_Table_Name of M51008 : Label is "altium";
   attribute Database_Table_Name of M51007 : Label is "altium";
   attribute Database_Table_Name of M51006 : Label is "altium";
   attribute Database_Table_Name of M51005 : Label is "altium";
   attribute Database_Table_Name of M51004 : Label is "altium";
   attribute Database_Table_Name of M51003 : Label is "altium";
   attribute Database_Table_Name of M51002 : Label is "altium";
   attribute Database_Table_Name of M51001 : Label is "altium";
   attribute Database_Table_Name of M51000 : Label is "altium";

   attribute dybde : string;
   attribute dybde of M51017 : Label is "0";
   attribute dybde of M51016 : Label is "0";
   attribute dybde of M51015 : Label is "0";
   attribute dybde of M51014 : Label is "0";
   attribute dybde of M51013 : Label is "0";
   attribute dybde of M51012 : Label is "0";
   attribute dybde of M51011 : Label is "0";
   attribute dybde of M51010 : Label is "0";
   attribute dybde of M51009 : Label is "0";
   attribute dybde of M51008 : Label is "0";
   attribute dybde of M51007 : Label is "0";
   attribute dybde of M51006 : Label is "0";
   attribute dybde of M51005 : Label is "0";
   attribute dybde of M51004 : Label is "0";
   attribute dybde of M51003 : Label is "0";
   attribute dybde of M51002 : Label is "0";
   attribute dybde of M51001 : Label is "0";
   attribute dybde of M51000 : Label is "0";

   attribute hylle : string;
   attribute hylle of M51017 : Label is "15";
   attribute hylle of M51016 : Label is "15";
   attribute hylle of M51015 : Label is "15";
   attribute hylle of M51014 : Label is "15";
   attribute hylle of M51013 : Label is "15";
   attribute hylle of M51012 : Label is "15";
   attribute hylle of M51011 : Label is "15";
   attribute hylle of M51010 : Label is "15";
   attribute hylle of M51009 : Label is "15";
   attribute hylle of M51008 : Label is "15";
   attribute hylle of M51007 : Label is "15";
   attribute hylle of M51006 : Label is "15";
   attribute hylle of M51005 : Label is "15";
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
;

    M51003 : X_2392                                          -- ObjectKind=Part|PrimaryId=M51003|SecondaryId=1
;

    M51002 : X_2392                                          -- ObjectKind=Part|PrimaryId=M51002|SecondaryId=1
;

    M51001 : X_2392                                          -- ObjectKind=Part|PrimaryId=M51001|SecondaryId=1
;

    M51000 : X_2392                                          -- ObjectKind=Part|PrimaryId=M51000|SecondaryId=1
;

End Structure;
------------------------------------------------------------
