Cable89/tesla-driver/05_Hardware/TK500_Driver/ProjectOutputs/TK510_Spenningsforsyninger.VHD

------------------------------------------------------------
-- VHDL TK510_Spenningsforsyninger
-- 2017 1 13 17 4 10
-- Created By "DXP VHDL Generator"
-- "Copyright (c) 2002-2014 Altium Limited"
-- Product Version: 16.0.6.282
------------------------------------------------------------

------------------------------------------------------------
-- VHDL TK510_Spenningsforsyninger
------------------------------------------------------------

Library IEEE;
Use     IEEE.std_logic_1164.all;

Entity TK510_Spenningsforsyninger Is
  port
  (
    BUS_B5           : InOut STD_LOGIC;                      -- ObjectKind=Port|PrimaryId=BUS.B5
    BUS_B6           : InOut STD_LOGIC;                      -- ObjectKind=Port|PrimaryId=BUS.B6
    BUS_B7           : InOut STD_LOGIC;                      -- ObjectKind=Port|PrimaryId=BUS.B7
    BUS_B8           : InOut STD_LOGIC;                      -- ObjectKind=Port|PrimaryId=BUS.B8
    BUS_B9           : InOut STD_LOGIC;                      -- ObjectKind=Port|PrimaryId=BUS.B9
    BUS_B10          : InOut STD_LOGIC;                      -- ObjectKind=Port|PrimaryId=BUS.B10
    BUS_B11          : InOut STD_LOGIC;                      -- ObjectKind=Port|PrimaryId=BUS.B11
    BUS_INTERRUPT    : InOut STD_LOGIC;                      -- ObjectKind=Port|PrimaryId=BUS.INTERRUPT
    BUS_KORT_INNSATT : InOut STD_LOGIC;                      -- ObjectKind=Port|PrimaryId=BUS.KORT_INNSATT
    BUS_LIMIT        : InOut STD_LOGIC;                      -- ObjectKind=Port|PrimaryId=BUS.LIMIT
    BUS_TRIGGER      : InOut STD_LOGIC                       -- ObjectKind=Port|PrimaryId=BUS.TRIGGER
  );
  attribute MacroCell : boolean;

End TK510_Spenningsforsyninger;
------------------------------------------------------------

------------------------------------------------------------
Architecture Structure Of TK510_Spenningsforsyninger Is
   Component X_2209                                          -- ObjectKind=Part|PrimaryId=D51001|SecondaryId=1
      port
      (
        X_1 : inout STD_LOGIC;                               -- ObjectKind=Pin|PrimaryId=D51001-1
        X_2 : inout STD_LOGIC                                -- ObjectKind=Pin|PrimaryId=D51001-2
      );
   End Component;

   Component X_2212                                          -- ObjectKind=Part|PrimaryId=Q51016|SecondaryId=1
      port
      (
        X_1 : inout STD_LOGIC;                               -- ObjectKind=Pin|PrimaryId=Q51016-1
        X_2 : inout STD_LOGIC;                               -- ObjectKind=Pin|PrimaryId=Q51016-2
        X_3 : inout STD_LOGIC                                -- ObjectKind=Pin|PrimaryId=Q51016-3
      );
   End Component;

   Component X_2213                                          -- ObjectKind=Part|PrimaryId=Q51013|SecondaryId=1
      port
      (
        X_1 : inout STD_LOGIC;                               -- ObjectKind=Pin|PrimaryId=Q51013-1
        X_2 : inout STD_LOGIC;                               -- ObjectKind=Pin|PrimaryId=Q51013-2
        X_3 : inout STD_LOGIC                                -- ObjectKind=Pin|PrimaryId=Q51013-3
      );
   End Component;

   Component X_2227                                          -- ObjectKind=Part|PrimaryId=J51029|SecondaryId=1
      port
      (
        X_1 : inout STD_LOGIC;                               -- ObjectKind=Pin|PrimaryId=J51029-1
        X_2 : inout STD_LOGIC                                -- ObjectKind=Pin|PrimaryId=J51029-2
      );
   End Component;

   Component X_2382                                          -- ObjectKind=Part|PrimaryId=J51007|SecondaryId=1
      port
      (
        A1  : inout STD_LOGIC;                               -- ObjectKind=Pin|PrimaryId=J51007-A1
        A2  : inout STD_LOGIC;                               -- ObjectKind=Pin|PrimaryId=J51007-A2
        A3  : inout STD_LOGIC;                               -- ObjectKind=Pin|PrimaryId=J51007-A3
        A4  : inout STD_LOGIC;                               -- ObjectKind=Pin|PrimaryId=J51007-A4
        A5  : inout STD_LOGIC;                               -- ObjectKind=Pin|PrimaryId=J51007-A5
        A6  : inout STD_LOGIC;                               -- ObjectKind=Pin|PrimaryId=J51007-A6
        A7  : inout STD_LOGIC;                               -- ObjectKind=Pin|PrimaryId=J51007-A7
        A8  : inout STD_LOGIC;                               -- ObjectKind=Pin|PrimaryId=J51007-A8
        A9  : inout STD_LOGIC;                               -- ObjectKind=Pin|PrimaryId=J51007-A9
        A10 : inout STD_LOGIC;                               -- ObjectKind=Pin|PrimaryId=J51007-A10
        A11 : inout STD_LOGIC;                               -- ObjectKind=Pin|PrimaryId=J51007-A11
        A12 : inout STD_LOGIC;                               -- ObjectKind=Pin|PrimaryId=J51007-A12
        A13 : inout STD_LOGIC;                               -- ObjectKind=Pin|PrimaryId=J51007-A13
        A14 : inout STD_LOGIC;                               -- ObjectKind=Pin|PrimaryId=J51007-A14
        A15 : inout STD_LOGIC;                               -- ObjectKind=Pin|PrimaryId=J51007-A15
        A16 : inout STD_LOGIC;                               -- ObjectKind=Pin|PrimaryId=J51007-A16
        A17 : inout STD_LOGIC;                               -- ObjectKind=Pin|PrimaryId=J51007-A17
        A18 : inout STD_LOGIC;                               -- ObjectKind=Pin|PrimaryId=J51007-A18
        B1  : inout STD_LOGIC;                               -- ObjectKind=Pin|PrimaryId=J51007-B1
        B2  : inout STD_LOGIC;                               -- ObjectKind=Pin|PrimaryId=J51007-B2
        B3  : inout STD_LOGIC;                               -- ObjectKind=Pin|PrimaryId=J51007-B3
        B4  : inout STD_LOGIC;                               -- ObjectKind=Pin|PrimaryId=J51007-B4
        B5  : inout STD_LOGIC;                               -- ObjectKind=Pin|PrimaryId=J51007-B5
        B6  : inout STD_LOGIC;                               -- ObjectKind=Pin|PrimaryId=J51007-B6
        B7  : inout STD_LOGIC;                               -- ObjectKind=Pin|PrimaryId=J51007-B7
        B8  : inout STD_LOGIC;                               -- ObjectKind=Pin|PrimaryId=J51007-B8
        B9  : inout STD_LOGIC;                               -- ObjectKind=Pin|PrimaryId=J51007-B9
        B10 : inout STD_LOGIC;                               -- ObjectKind=Pin|PrimaryId=J51007-B10
        B11 : inout STD_LOGIC;                               -- ObjectKind=Pin|PrimaryId=J51007-B11
        B12 : inout STD_LOGIC;                               -- ObjectKind=Pin|PrimaryId=J51007-B12
        B13 : inout STD_LOGIC;                               -- ObjectKind=Pin|PrimaryId=J51007-B13
        B14 : inout STD_LOGIC;                               -- ObjectKind=Pin|PrimaryId=J51007-B14
        B15 : inout STD_LOGIC;                               -- ObjectKind=Pin|PrimaryId=J51007-B15
        B16 : inout STD_LOGIC;                               -- ObjectKind=Pin|PrimaryId=J51007-B16
        B17 : inout STD_LOGIC;                               -- ObjectKind=Pin|PrimaryId=J51007-B17
        B18 : inout STD_LOGIC                                -- ObjectKind=Pin|PrimaryId=J51007-B18
      );
   End Component;

   Component X_2444                                          -- ObjectKind=Part|PrimaryId=R51041|SecondaryId=1
      port
      (
        X_1 : inout STD_LOGIC;                               -- ObjectKind=Pin|PrimaryId=R51041-1
        X_2 : inout STD_LOGIC                                -- ObjectKind=Pin|PrimaryId=R51041-2
      );
   End Component;

   Component X_2448                                          -- ObjectKind=Part|PrimaryId=R51044|SecondaryId=1
      port
      (
        X_1 : inout STD_LOGIC;                               -- ObjectKind=Pin|PrimaryId=R51044-1
        X_2 : inout STD_LOGIC                                -- ObjectKind=Pin|PrimaryId=R51044-2
      );
   End Component;


    Signal NamedSignal_AC_S6_L1        : STD_LOGIC; -- ObjectKind=Net|PrimaryId=AC_S6_L1
    Signal NamedSignal_AC_S6_L2        : STD_LOGIC; -- ObjectKind=Net|PrimaryId=AC_S6_L2
    Signal NamedSignal_AC_S7_L1        : STD_LOGIC; -- ObjectKind=Net|PrimaryId=AC_S7_L1
    Signal NamedSignal_AC_S7_L2        : STD_LOGIC; -- ObjectKind=Net|PrimaryId=AC_S7_L2
    Signal NamedSignal_AC_S8_L1        : STD_LOGIC; -- ObjectKind=Net|PrimaryId=AC_S8_L1
    Signal NamedSignal_AC_S8_L2        : STD_LOGIC; -- ObjectKind=Net|PrimaryId=AC_S8_L2
    Signal PinSignal_D51001_1          : STD_LOGIC; -- ObjectKind=Net|PrimaryId=NetD51001_1
    Signal PinSignal_D51002_1          : STD_LOGIC; -- ObjectKind=Net|PrimaryId=NetD51002_1
    Signal PinSignal_D51003_1          : STD_LOGIC; -- ObjectKind=Net|PrimaryId=NetD51003_1
    Signal PinSignal_J51007_A1         : STD_LOGIC; -- ObjectKind=Net|PrimaryId=NetJ51028_A1
    Signal PinSignal_J51007_A10        : STD_LOGIC; -- ObjectKind=Net|PrimaryId=NetJ51028_A10
    Signal PinSignal_J51007_A11        : STD_LOGIC; -- ObjectKind=Net|PrimaryId=NetJ51028_A11
    Signal PinSignal_J51007_A2         : STD_LOGIC; -- ObjectKind=Net|PrimaryId=NetJ51028_A2
    Signal PinSignal_J51007_A3         : STD_LOGIC; -- ObjectKind=Net|PrimaryId=NetJ51028_A3
    Signal PinSignal_J51007_A4         : STD_LOGIC; -- ObjectKind=Net|PrimaryId=NetJ51028_A4
    Signal PinSignal_J51007_A5         : STD_LOGIC; -- ObjectKind=Net|PrimaryId=NetJ51028_A5
    Signal PinSignal_J51007_A6         : STD_LOGIC; -- ObjectKind=Net|PrimaryId=NetJ51028_A6
    Signal PinSignal_J51007_A7         : STD_LOGIC; -- ObjectKind=Net|PrimaryId=NetJ51028_A7
    Signal PinSignal_J51007_A8         : STD_LOGIC; -- ObjectKind=Net|PrimaryId=NetJ51028_A8
    Signal PinSignal_J51007_A9         : STD_LOGIC; -- ObjectKind=Net|PrimaryId=NetJ51028_A9
    Signal PinSignal_J51007_B1         : STD_LOGIC; -- ObjectKind=Net|PrimaryId=NetJ51007_B1
    Signal PinSignal_J51008_A1         : STD_LOGIC; -- ObjectKind=Net|PrimaryId=NetJ51028_A1
    Signal PinSignal_J51008_A10        : STD_LOGIC; -- ObjectKind=Net|PrimaryId=NetJ51028_A10
    Signal PinSignal_J51008_A11        : STD_LOGIC; -- ObjectKind=Net|PrimaryId=NetJ51028_A11
    Signal PinSignal_J51008_A2         : STD_LOGIC; -- ObjectKind=Net|PrimaryId=NetJ51028_A2
    Signal PinSignal_J51008_A3         : STD_LOGIC; -- ObjectKind=Net|PrimaryId=NetJ51028_A3
    Signal PinSignal_J51008_A4         : STD_LOGIC; -- ObjectKind=Net|PrimaryId=NetJ51028_A4
    Signal PinSignal_J51008_A5         : STD_LOGIC; -- ObjectKind=Net|PrimaryId=NetJ51028_A5
    Signal PinSignal_J51008_A6         : STD_LOGIC; -- ObjectKind=Net|PrimaryId=NetJ51028_A6
    Signal PinSignal_J51008_A7         : STD_LOGIC; -- ObjectKind=Net|PrimaryId=NetJ51028_A7
    Signal PinSignal_J51008_A8         : STD_LOGIC; -- ObjectKind=Net|PrimaryId=NetJ51028_A8
    Signal PinSignal_J51008_A9         : STD_LOGIC; -- ObjectKind=Net|PrimaryId=NetJ51028_A9
    Signal PinSignal_J51008_B1         : STD_LOGIC; -- ObjectKind=Net|PrimaryId=NetJ51008_B1
    Signal PinSignal_J51028_A1         : STD_LOGIC; -- ObjectKind=Net|PrimaryId=NetJ51028_A1
    Signal PinSignal_J51028_A10        : STD_LOGIC; -- ObjectKind=Net|PrimaryId=NetJ51028_A10
    Signal PinSignal_J51028_A11        : STD_LOGIC; -- ObjectKind=Net|PrimaryId=NetJ51028_A11
    Signal PinSignal_J51028_A2         : STD_LOGIC; -- ObjectKind=Net|PrimaryId=NetJ51028_A2
    Signal PinSignal_J51028_A3         : STD_LOGIC; -- ObjectKind=Net|PrimaryId=NetJ51028_A3
    Signal PinSignal_J51028_A4         : STD_LOGIC; -- ObjectKind=Net|PrimaryId=NetJ51028_A4
    Signal PinSignal_J51028_A5         : STD_LOGIC; -- ObjectKind=Net|PrimaryId=NetJ51028_A5
    Signal PinSignal_J51028_A6         : STD_LOGIC; -- ObjectKind=Net|PrimaryId=NetJ51028_A6
    Signal PinSignal_J51028_A7         : STD_LOGIC; -- ObjectKind=Net|PrimaryId=NetJ51028_A7
    Signal PinSignal_J51028_A8         : STD_LOGIC; -- ObjectKind=Net|PrimaryId=NetJ51028_A8
    Signal PinSignal_J51028_A9         : STD_LOGIC; -- ObjectKind=Net|PrimaryId=NetJ51028_A9
    Signal PinSignal_J51028_B1         : STD_LOGIC; -- ObjectKind=Net|PrimaryId=NetJ51028_B1
    Signal PinSignal_Q51016_2          : STD_LOGIC; -- ObjectKind=Net|PrimaryId=NetQ51016_2
    Signal PinSignal_Q51017_2          : STD_LOGIC; -- ObjectKind=Net|PrimaryId=NetQ51017_2
    Signal PinSignal_Q51018_2          : STD_LOGIC; -- ObjectKind=Net|PrimaryId=NetQ51018_2
    Signal PowerSignal_GND             : STD_LOGIC; -- ObjectKind=Net|PrimaryId=GND
    Signal PowerSignal_VCC_EXTRA       : STD_LOGIC; -- ObjectKind=Net|PrimaryId=VCC_EXTRA
    Signal PowerSignal_VCC_P18V        : STD_LOGIC; -- ObjectKind=Net|PrimaryId=VCC_P18V
    Signal PowerSignal_VCC_P5V0        : STD_LOGIC; -- ObjectKind=Net|PrimaryId=VCC_P5V0

   attribute antall : string;
   attribute antall of R51046 : Label is "100";
   attribute antall of R51045 : Label is "100";
   attribute antall of R51044 : Label is "100";
   attribute antall of R51043 : Label is "100";
   attribute antall of R51042 : Label is "100";
   attribute antall of R51041 : Label is "100";
   attribute antall of Q51015 : Label is "100";
   attribute antall of Q51014 : Label is "100";
   attribute antall of Q51013 : Label is "100";
   attribute antall of J51049 : Label is "100";
   attribute antall of J51048 : Label is "100";
   attribute antall of J51047 : Label is "100";
   attribute antall of J51046 : Label is "100";
   attribute antall of J51045 : Label is "100";
   attribute antall of J51044 : Label is "100";
   attribute antall of J51043 : Label is "100";
   attribute antall of J51042 : Label is "100";
   attribute antall of J51041 : Label is "100";
   attribute antall of J51040 : Label is "100";
   attribute antall of J51039 : Label is "100";
   attribute antall of J51038 : Label is "100";
   attribute antall of J51037 : Label is "100";
   attribute antall of J51036 : Label is "100";
   attribute antall of J51035 : Label is "100";
   attribute antall of J51034 : Label is "100";
   attribute antall of J51033 : Label is "100";
   attribute antall of J51032 : Label is "100";
   attribute antall of J51031 : Label is "100";
   attribute antall of J51030 : Label is "100";
   attribute antall of J51029 : Label is "100";
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
      Port Map
      (
        X_1 => NamedSignal_AC_S8_L2,                         -- ObjectKind=Pin|PrimaryId=J51031-1
        X_2 => NamedSignal_AC_S8_L1                          -- ObjectKind=Pin|PrimaryId=J51031-2
      );

    J51030 : X_2227                                          -- ObjectKind=Part|PrimaryId=J51030|SecondaryId=1
      Port Map
      (
        X_1 => NamedSignal_AC_S7_L2,                         -- ObjectKind=Pin|PrimaryId=J51030-1
        X_2 => NamedSignal_AC_S7_L1                          -- ObjectKind=Pin|PrimaryId=J51030-2
      );

    J51029 : X_2227                                          -- ObjectKind=Part|PrimaryId=J51029|SecondaryId=1
      Port Map
      (
        X_1 => NamedSignal_AC_S6_L2,                         -- ObjectKind=Pin|PrimaryId=J51029-1
        X_2 => NamedSignal_AC_S6_L1                          -- ObjectKind=Pin|PrimaryId=J51029-2
      );

    J51028 : X_2382                                          -- ObjectKind=Part|PrimaryId=J51028|SecondaryId=1
      Port Map
      (
        A1  => PinSignal_J51028_A1,                          -- ObjectKind=Pin|PrimaryId=J51028-A1
        A2  => PinSignal_J51028_A2,                          -- ObjectKind=Pin|PrimaryId=J51028-A2
        A3  => PinSignal_J51028_A3,                          -- ObjectKind=Pin|PrimaryId=J51028-A3
        A4  => PinSignal_J51028_A4,                          -- ObjectKind=Pin|PrimaryId=J51028-A4
        A5  => PinSignal_J51028_A5,                          -- ObjectKind=Pin|PrimaryId=J51028-A5
        A6  => PinSignal_J51028_A6,                          -- ObjectKind=Pin|PrimaryId=J51028-A6
        A7  => PinSignal_J51028_A7,                          -- ObjectKind=Pin|PrimaryId=J51028-A7
        A8  => PinSignal_J51028_A8,                          -- ObjectKind=Pin|PrimaryId=J51028-A8
        A9  => PinSignal_J51028_A9,                          -- ObjectKind=Pin|PrimaryId=J51028-A9
        A10 => PinSignal_J51028_A10,                         -- ObjectKind=Pin|PrimaryId=J51028-A10
        A11 => PinSignal_J51028_A11,                         -- ObjectKind=Pin|PrimaryId=J51028-A11
        A12 => PowerSignal_GND,                              -- ObjectKind=Pin|PrimaryId=J51028-A12
        A13 => PowerSignal_GND,                              -- ObjectKind=Pin|PrimaryId=J51028-A13
        A14 => PowerSignal_GND,                              -- ObjectKind=Pin|PrimaryId=J51028-A14
        A15 => PowerSignal_GND,                              -- ObjectKind=Pin|PrimaryId=J51028-A15
        A16 => PowerSignal_VCC_EXTRA,                        -- ObjectKind=Pin|PrimaryId=J51028-A16
        A17 => PowerSignal_VCC_P5V0,                         -- ObjectKind=Pin|PrimaryId=J51028-A17
        A18 => PowerSignal_VCC_P18V,                         -- ObjectKind=Pin|PrimaryId=J51028-A18
        B1  => PinSignal_J51028_B1,                          -- ObjectKind=Pin|PrimaryId=J51028-B1
        B2  => PowerSignal_VCC_P18V,                         -- ObjectKind=Pin|PrimaryId=J51028-B2
        B3  => PowerSignal_VCC_P18V,                         -- ObjectKind=Pin|PrimaryId=J51028-B3
        B4  => PowerSignal_VCC_P18V,                         -- ObjectKind=Pin|PrimaryId=J51028-B4
        B5  => PowerSignal_VCC_P18V,                         -- ObjectKind=Pin|PrimaryId=J51028-B5
        B6  => PowerSignal_VCC_P18V,                         -- ObjectKind=Pin|PrimaryId=J51028-B6
        B7  => PowerSignal_VCC_P18V,                         -- ObjectKind=Pin|PrimaryId=J51028-B7
        B8  => PowerSignal_VCC_P18V,                         -- ObjectKind=Pin|PrimaryId=J51028-B8
        B9  => PowerSignal_VCC_P18V,                         -- ObjectKind=Pin|PrimaryId=J51028-B9
        B11 => NamedSignal_AC_S8_L1,                         -- ObjectKind=Pin|PrimaryId=J51028-B11
        B12 => NamedSignal_AC_S8_L2,                         -- ObjectKind=Pin|PrimaryId=J51028-B12
        B14 => PowerSignal_GND,                              -- ObjectKind=Pin|PrimaryId=J51028-B14
        B15 => PowerSignal_GND,                              -- ObjectKind=Pin|PrimaryId=J51028-B15
        B16 => PowerSignal_GND,                              -- ObjectKind=Pin|PrimaryId=J51028-B16
        B17 => PowerSignal_GND,                              -- ObjectKind=Pin|PrimaryId=J51028-B17
        B18 => PowerSignal_GND                               -- ObjectKind=Pin|PrimaryId=J51028-B18
      );

    J51008 : X_2382                                          -- ObjectKind=Part|PrimaryId=J51008|SecondaryId=1
      Port Map
      (
        A1  => PinSignal_J51008_A1,                          -- ObjectKind=Pin|PrimaryId=J51008-A1
        A2  => PinSignal_J51008_A2,                          -- ObjectKind=Pin|PrimaryId=J51008-A2
        A3  => PinSignal_J51008_A3,                          -- ObjectKind=Pin|PrimaryId=J51008-A3
        A4  => PinSignal_J51008_A4,                          -- ObjectKind=Pin|PrimaryId=J51008-A4
        A5  => PinSignal_J51008_A5,                          -- ObjectKind=Pin|PrimaryId=J51008-A5
        A6  => PinSignal_J51008_A6,                          -- ObjectKind=Pin|PrimaryId=J51008-A6
        A7  => PinSignal_J51008_A7,                          -- ObjectKind=Pin|PrimaryId=J51008-A7
        A8  => PinSignal_J51008_A8,                          -- ObjectKind=Pin|PrimaryId=J51008-A8
        A9  => PinSignal_J51008_A9,                          -- ObjectKind=Pin|PrimaryId=J51008-A9
        A10 => PinSignal_J51008_A10,                         -- ObjectKind=Pin|PrimaryId=J51008-A10
        A11 => PinSignal_J51008_A11,                         -- ObjectKind=Pin|PrimaryId=J51008-A11
        A12 => PowerSignal_GND,                              -- ObjectKind=Pin|PrimaryId=J51008-A12
        A13 => PowerSignal_GND,                              -- ObjectKind=Pin|PrimaryId=J51008-A13
        A14 => PowerSignal_GND,                              -- ObjectKind=Pin|PrimaryId=J51008-A14
        A15 => PowerSignal_GND,                              -- ObjectKind=Pin|PrimaryId=J51008-A15
        A16 => PowerSignal_VCC_EXTRA,                        -- ObjectKind=Pin|PrimaryId=J51008-A16
        A17 => PowerSignal_VCC_P5V0,                         -- ObjectKind=Pin|PrimaryId=J51008-A17
        A18 => PowerSignal_VCC_P18V,                         -- ObjectKind=Pin|PrimaryId=J51008-A18
        B1  => PinSignal_J51008_B1,                          -- ObjectKind=Pin|PrimaryId=J51008-B1
        B2  => PowerSignal_VCC_P5V0,                         -- ObjectKind=Pin|PrimaryId=J51008-B2
        B3  => PowerSignal_VCC_P5V0,                         -- ObjectKind=Pin|PrimaryId=J51008-B3
        B4  => PowerSignal_VCC_P5V0,                         -- ObjectKind=Pin|PrimaryId=J51008-B4
        B5  => PowerSignal_VCC_P5V0,                         -- ObjectKind=Pin|PrimaryId=J51008-B5
        B6  => PowerSignal_VCC_P5V0,                         -- ObjectKind=Pin|PrimaryId=J51008-B6
        B7  => PowerSignal_VCC_P5V0,                         -- ObjectKind=Pin|PrimaryId=J51008-B7
        B8  => PowerSignal_VCC_P5V0,                         -- ObjectKind=Pin|PrimaryId=J51008-B8
        B9  => PowerSignal_VCC_P5V0,                         -- ObjectKind=Pin|PrimaryId=J51008-B9
        B11 => NamedSignal_AC_S7_L1,                         -- ObjectKind=Pin|PrimaryId=J51008-B11
        B12 => NamedSignal_AC_S7_L2,                         -- ObjectKind=Pin|PrimaryId=J51008-B12
        B14 => PowerSignal_GND,                              -- ObjectKind=Pin|PrimaryId=J51008-B14
        B15 => PowerSignal_GND,                              -- ObjectKind=Pin|PrimaryId=J51008-B15
        B16 => PowerSignal_GND,                              -- ObjectKind=Pin|PrimaryId=J51008-B16
        B17 => PowerSignal_GND,                              -- ObjectKind=Pin|PrimaryId=J51008-B17
        B18 => PowerSignal_GND                               -- ObjectKind=Pin|PrimaryId=J51008-B18
      );

    J51007 : X_2382                                          -- ObjectKind=Part|PrimaryId=J51007|SecondaryId=1
      Port Map
      (
        A1  => PinSignal_J51007_A1,                          -- ObjectKind=Pin|PrimaryId=J51007-A1
        A2  => PinSignal_J51007_A2,                          -- ObjectKind=Pin|PrimaryId=J51007-A2
        A3  => PinSignal_J51007_A3,                          -- ObjectKind=Pin|PrimaryId=J51007-A3
        A4  => PinSignal_J51007_A4,                          -- ObjectKind=Pin|PrimaryId=J51007-A4
        A5  => PinSignal_J51007_A5,                          -- ObjectKind=Pin|PrimaryId=J51007-A5
        A6  => PinSignal_J51007_A6,                          -- ObjectKind=Pin|PrimaryId=J51007-A6
        A7  => PinSignal_J51007_A7,                          -- ObjectKind=Pin|PrimaryId=J51007-A7
        A8  => PinSignal_J51007_A8,                          -- ObjectKind=Pin|PrimaryId=J51007-A8
        A9  => PinSignal_J51007_A9,                          -- ObjectKind=Pin|PrimaryId=J51007-A9
        A10 => PinSignal_J51007_A10,                         -- ObjectKind=Pin|PrimaryId=J51007-A10
        A11 => PinSignal_J51007_A11,                         -- ObjectKind=Pin|PrimaryId=J51007-A11
        A12 => PowerSignal_GND,                              -- ObjectKind=Pin|PrimaryId=J51007-A12
        A13 => PowerSignal_GND,                              -- ObjectKind=Pin|PrimaryId=J51007-A13
        A14 => PowerSignal_GND,                              -- ObjectKind=Pin|PrimaryId=J51007-A14
        A15 => PowerSignal_GND,                              -- ObjectKind=Pin|PrimaryId=J51007-A15
        A16 => PowerSignal_VCC_EXTRA,                        -- ObjectKind=Pin|PrimaryId=J51007-A16
        A17 => PowerSignal_VCC_P5V0,                         -- ObjectKind=Pin|PrimaryId=J51007-A17
        A18 => PowerSignal_VCC_P18V,                         -- ObjectKind=Pin|PrimaryId=J51007-A18
        B1  => PinSignal_J51007_B1,                          -- ObjectKind=Pin|PrimaryId=J51007-B1
        B2  => PowerSignal_VCC_EXTRA,                        -- ObjectKind=Pin|PrimaryId=J51007-B2
        B3  => PowerSignal_VCC_EXTRA,                        -- ObjectKind=Pin|PrimaryId=J51007-B3
        B4  => PowerSignal_VCC_EXTRA,                        -- ObjectKind=Pin|PrimaryId=J51007-B4
        B5  => PowerSignal_VCC_EXTRA,                        -- ObjectKind=Pin|PrimaryId=J51007-B5
        B6  => PowerSignal_VCC_EXTRA,                        -- ObjectKind=Pin|PrimaryId=J51007-B6
        B7  => PowerSignal_VCC_EXTRA,                        -- ObjectKind=Pin|PrimaryId=J51007-B7
        B8  => PowerSignal_VCC_EXTRA,                        -- ObjectKind=Pin|PrimaryId=J51007-B8
        B9  => PowerSignal_VCC_EXTRA,                        -- ObjectKind=Pin|PrimaryId=J51007-B9
        B11 => NamedSignal_AC_S6_L1,                         -- ObjectKind=Pin|PrimaryId=J51007-B11
        B12 => NamedSignal_AC_S6_L2,                         -- ObjectKind=Pin|PrimaryId=J51007-B12
        B14 => PowerSignal_GND,                              -- ObjectKind=Pin|PrimaryId=J51007-B14
        B15 => PowerSignal_GND,                              -- ObjectKind=Pin|PrimaryId=J51007-B15
        B16 => PowerSignal_GND,                              -- ObjectKind=Pin|PrimaryId=J51007-B16
        B17 => PowerSignal_GND,                              -- ObjectKind=Pin|PrimaryId=J51007-B17
        B18 => PowerSignal_GND                               -- ObjectKind=Pin|PrimaryId=J51007-B18
      );

    D51003 : X_2209                                          -- ObjectKind=Part|PrimaryId=D51003|SecondaryId=1
      Port Map
      (
        X_1 => PinSignal_D51003_1,                           -- ObjectKind=Pin|PrimaryId=D51003-1
        X_2 => PowerSignal_GND                               -- ObjectKind=Pin|PrimaryId=D51003-2
      );

    D51002 : X_2209                                          -- ObjectKind=Part|PrimaryId=D51002|SecondaryId=1
      Port Map
      (
        X_1 => PinSignal_D51002_1,                           -- ObjectKind=Pin|PrimaryId=D51002-1
        X_2 => PowerSignal_GND                               -- ObjectKind=Pin|PrimaryId=D51002-2
      );

    D51001 : X_2209                                          -- ObjectKind=Part|PrimaryId=D51001|SecondaryId=1
      Port Map
      (
        X_1 => PinSignal_D51001_1,                           -- ObjectKind=Pin|PrimaryId=D51001-1
        X_2 => PowerSignal_GND                               -- ObjectKind=Pin|PrimaryId=D51001-2
      );

    -- Signal Assignments
    ---------------------
    BUS_B10              <= PinSignal_J51007_A2; -- ObjectKind=Net|PrimaryId=NetJ51028_A2
    BUS_B10              <= PinSignal_J51008_A2; -- ObjectKind=Net|PrimaryId=NetJ51028_A2
    BUS_B10              <= PinSignal_J51028_A2; -- ObjectKind=Net|PrimaryId=NetJ51028_A2
    BUS_B11              <= PinSignal_J51007_A1; -- ObjectKind=Net|PrimaryId=NetJ51028_A1
    BUS_B11              <= PinSignal_J51008_A1; -- ObjectKind=Net|PrimaryId=NetJ51028_A1
    BUS_B11              <= PinSignal_J51028_A1; -- ObjectKind=Net|PrimaryId=NetJ51028_A1
    BUS_B5               <= PinSignal_J51007_A7; -- ObjectKind=Net|PrimaryId=NetJ51028_A7
    BUS_B5               <= PinSignal_J51008_A7; -- ObjectKind=Net|PrimaryId=NetJ51028_A7
    BUS_B5               <= PinSignal_J51028_A7; -- ObjectKind=Net|PrimaryId=NetJ51028_A7
    BUS_B6               <= PinSignal_J51007_A6; -- ObjectKind=Net|PrimaryId=NetJ51028_A6
    BUS_B6               <= PinSignal_J51008_A6; -- ObjectKind=Net|PrimaryId=NetJ51028_A6
    BUS_B6               <= PinSignal_J51028_A6; -- ObjectKind=Net|PrimaryId=NetJ51028_A6
    BUS_B7               <= PinSignal_J51007_A5; -- ObjectKind=Net|PrimaryId=NetJ51028_A5
    BUS_B7               <= PinSignal_J51008_A5; -- ObjectKind=Net|PrimaryId=NetJ51028_A5
    BUS_B7               <= PinSignal_J51028_A5; -- ObjectKind=Net|PrimaryId=NetJ51028_A5
    BUS_B8               <= PinSignal_J51007_A4; -- ObjectKind=Net|PrimaryId=NetJ51028_A4
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
    PinSignal_J51028_A9  <= BUS_LIMIT; -- ObjectKind=Net|PrimaryId=NetJ51028_A9
    PowerSignal_GND      <= '0'; -- ObjectKind=Net|PrimaryId=GND

End Structure;
------------------------------------------------------------
