Cable89/tesla-driver/05_Hardware/TK500_Driver/ProjectOutputs/TK511_Blindkort.VHD

------------------------------------------------------------
-- VHDL TK511_Blindkort
-- 2017 1 13 17 4 6
-- Created By "DXP VHDL Generator"
-- "Copyright (c) 2002-2014 Altium Limited"
-- Product Version: 16.0.6.282
------------------------------------------------------------

------------------------------------------------------------
-- VHDL TK511_Blindkort
------------------------------------------------------------

Library IEEE;
Use     IEEE.std_logic_1164.all;

Entity TK511_Blindkort Is
  attribute MacroCell : boolean;

End TK511_Blindkort;
------------------------------------------------------------

------------------------------------------------------------
Architecture Structure Of TK511_Blindkort Is
   Component X_2390                                          -- ObjectKind=Part|PrimaryId=J51101|SecondaryId=1
      port
      (
        X_1  : inout STD_LOGIC;                              -- ObjectKind=Pin|PrimaryId=J51101-1
        X_2  : inout STD_LOGIC;                              -- ObjectKind=Pin|PrimaryId=J51101-2
        X_3  : inout STD_LOGIC;                              -- ObjectKind=Pin|PrimaryId=J51101-3
        X_4  : inout STD_LOGIC;                              -- ObjectKind=Pin|PrimaryId=J51101-4
        X_5  : inout STD_LOGIC;                              -- ObjectKind=Pin|PrimaryId=J51101-5
        X_6  : inout STD_LOGIC;                              -- ObjectKind=Pin|PrimaryId=J51101-6
        X_7  : inout STD_LOGIC;                              -- ObjectKind=Pin|PrimaryId=J51101-7
        X_8  : inout STD_LOGIC;                              -- ObjectKind=Pin|PrimaryId=J51101-8
        X_9  : inout STD_LOGIC;                              -- ObjectKind=Pin|PrimaryId=J51101-9
        X_10 : inout STD_LOGIC;                              -- ObjectKind=Pin|PrimaryId=J51101-10
        X_11 : inout STD_LOGIC;                              -- ObjectKind=Pin|PrimaryId=J51101-11
        X_12 : inout STD_LOGIC;                              -- ObjectKind=Pin|PrimaryId=J51101-12
        X_13 : inout STD_LOGIC;                              -- ObjectKind=Pin|PrimaryId=J51101-13
        X_14 : inout STD_LOGIC;                              -- ObjectKind=Pin|PrimaryId=J51101-14
        X_15 : inout STD_LOGIC;                              -- ObjectKind=Pin|PrimaryId=J51101-15
        X_16 : inout STD_LOGIC;                              -- ObjectKind=Pin|PrimaryId=J51101-16
        X_17 : inout STD_LOGIC;                              -- ObjectKind=Pin|PrimaryId=J51101-17
        X_18 : inout STD_LOGIC;                              -- ObjectKind=Pin|PrimaryId=J51101-18
        X_19 : inout STD_LOGIC;                              -- ObjectKind=Pin|PrimaryId=J51101-19
        X_20 : inout STD_LOGIC;                              -- ObjectKind=Pin|PrimaryId=J51101-20
        X_21 : inout STD_LOGIC;                              -- ObjectKind=Pin|PrimaryId=J51101-21
        X_22 : inout STD_LOGIC;                              -- ObjectKind=Pin|PrimaryId=J51101-22
        X_23 : inout STD_LOGIC;                              -- ObjectKind=Pin|PrimaryId=J51101-23
        X_24 : inout STD_LOGIC;                              -- ObjectKind=Pin|PrimaryId=J51101-24
        X_25 : inout STD_LOGIC;                              -- ObjectKind=Pin|PrimaryId=J51101-25
        X_26 : inout STD_LOGIC;                              -- ObjectKind=Pin|PrimaryId=J51101-26
        X_27 : inout STD_LOGIC;                              -- ObjectKind=Pin|PrimaryId=J51101-27
        X_28 : inout STD_LOGIC;                              -- ObjectKind=Pin|PrimaryId=J51101-28
        X_29 : inout STD_LOGIC;                              -- ObjectKind=Pin|PrimaryId=J51101-29
        X_30 : inout STD_LOGIC;                              -- ObjectKind=Pin|PrimaryId=J51101-30
        X_31 : inout STD_LOGIC;                              -- ObjectKind=Pin|PrimaryId=J51101-31
        X_32 : inout STD_LOGIC;                              -- ObjectKind=Pin|PrimaryId=J51101-32
        X_33 : inout STD_LOGIC;                              -- ObjectKind=Pin|PrimaryId=J51101-33
        X_34 : inout STD_LOGIC                               -- ObjectKind=Pin|PrimaryId=J51101-34
      );
   End Component;

   Component X_2430                                          -- ObjectKind=Part|PrimaryId=J51102|SecondaryId=1
      port
      (
        X_1 : inout STD_LOGIC;                               -- ObjectKind=Pin|PrimaryId=J51102-1
        X_2 : inout STD_LOGIC;                               -- ObjectKind=Pin|PrimaryId=J51102-2
        X_3 : inout STD_LOGIC                                -- ObjectKind=Pin|PrimaryId=J51102-3
      );
   End Component;

   Component X_3177                                          -- ObjectKind=Part|PrimaryId=J51100|SecondaryId=1
      port
      (
        A1  : inout STD_LOGIC;                               -- ObjectKind=Pin|PrimaryId=J51100-A1
        A2  : inout STD_LOGIC;                               -- ObjectKind=Pin|PrimaryId=J51100-A2
        A3  : inout STD_LOGIC;                               -- ObjectKind=Pin|PrimaryId=J51100-A3
        A4  : inout STD_LOGIC;                               -- ObjectKind=Pin|PrimaryId=J51100-A4
        A5  : inout STD_LOGIC;                               -- ObjectKind=Pin|PrimaryId=J51100-A5
        A6  : inout STD_LOGIC;                               -- ObjectKind=Pin|PrimaryId=J51100-A6
        A7  : inout STD_LOGIC;                               -- ObjectKind=Pin|PrimaryId=J51100-A7
        A8  : inout STD_LOGIC;                               -- ObjectKind=Pin|PrimaryId=J51100-A8
        A9  : inout STD_LOGIC;                               -- ObjectKind=Pin|PrimaryId=J51100-A9
        A10 : inout STD_LOGIC;                               -- ObjectKind=Pin|PrimaryId=J51100-A10
        A11 : inout STD_LOGIC;                               -- ObjectKind=Pin|PrimaryId=J51100-A11
        A12 : inout STD_LOGIC;                               -- ObjectKind=Pin|PrimaryId=J51100-A12
        A13 : inout STD_LOGIC;                               -- ObjectKind=Pin|PrimaryId=J51100-A13
        A14 : inout STD_LOGIC;                               -- ObjectKind=Pin|PrimaryId=J51100-A14
        A15 : inout STD_LOGIC;                               -- ObjectKind=Pin|PrimaryId=J51100-A15
        A16 : inout STD_LOGIC;                               -- ObjectKind=Pin|PrimaryId=J51100-A16
        A17 : inout STD_LOGIC;                               -- ObjectKind=Pin|PrimaryId=J51100-A17
        A18 : inout STD_LOGIC;                               -- ObjectKind=Pin|PrimaryId=J51100-A18
        B1  : inout STD_LOGIC;                               -- ObjectKind=Pin|PrimaryId=J51100-B1
        B2  : inout STD_LOGIC;                               -- ObjectKind=Pin|PrimaryId=J51100-B2
        B3  : inout STD_LOGIC;                               -- ObjectKind=Pin|PrimaryId=J51100-B3
        B4  : inout STD_LOGIC;                               -- ObjectKind=Pin|PrimaryId=J51100-B4
        B5  : inout STD_LOGIC;                               -- ObjectKind=Pin|PrimaryId=J51100-B5
        B6  : inout STD_LOGIC;                               -- ObjectKind=Pin|PrimaryId=J51100-B6
        B7  : inout STD_LOGIC;                               -- ObjectKind=Pin|PrimaryId=J51100-B7
        B8  : inout STD_LOGIC;                               -- ObjectKind=Pin|PrimaryId=J51100-B8
        B9  : inout STD_LOGIC;                               -- ObjectKind=Pin|PrimaryId=J51100-B9
        B10 : inout STD_LOGIC;                               -- ObjectKind=Pin|PrimaryId=J51100-B10
        B11 : inout STD_LOGIC;                               -- ObjectKind=Pin|PrimaryId=J51100-B11
        B12 : inout STD_LOGIC;                               -- ObjectKind=Pin|PrimaryId=J51100-B12
        B13 : inout STD_LOGIC;                               -- ObjectKind=Pin|PrimaryId=J51100-B13
        B14 : inout STD_LOGIC;                               -- ObjectKind=Pin|PrimaryId=J51100-B14
        B15 : inout STD_LOGIC;                               -- ObjectKind=Pin|PrimaryId=J51100-B15
        B16 : inout STD_LOGIC;                               -- ObjectKind=Pin|PrimaryId=J51100-B16
        B17 : inout STD_LOGIC;                               -- ObjectKind=Pin|PrimaryId=J51100-B17
        B18 : inout STD_LOGIC                                -- ObjectKind=Pin|PrimaryId=J51100-B18
      );
   End Component;


    Signal NamedSignal_AUX1_A           : STD_LOGIC; -- ObjectKind=Net|PrimaryId=AUX1_A
    Signal NamedSignal_AUX1_B           : STD_LOGIC; -- ObjectKind=Net|PrimaryId=AUX1_B
    Signal NamedSignal_AUX2_A           : STD_LOGIC; -- ObjectKind=Net|PrimaryId=AUX2_A
    Signal NamedSignal_AUX2_B           : STD_LOGIC; -- ObjectKind=Net|PrimaryId=AUX2_B
    Signal NamedSignal_B10              : STD_LOGIC; -- ObjectKind=Net|PrimaryId=B10
    Signal NamedSignal_B11              : STD_LOGIC; -- ObjectKind=Net|PrimaryId=B11
    Signal NamedSignal_B12              : STD_LOGIC; -- ObjectKind=Net|PrimaryId=B12
    Signal NamedSignal_B13              : STD_LOGIC; -- ObjectKind=Net|PrimaryId=B13
    Signal NamedSignal_B14              : STD_LOGIC; -- ObjectKind=Net|PrimaryId=B14
    Signal NamedSignal_B5               : STD_LOGIC; -- ObjectKind=Net|PrimaryId=B5
    Signal NamedSignal_B6               : STD_LOGIC; -- ObjectKind=Net|PrimaryId=B6
    Signal NamedSignal_B7               : STD_LOGIC; -- ObjectKind=Net|PrimaryId=B7
    Signal NamedSignal_B8               : STD_LOGIC; -- ObjectKind=Net|PrimaryId=B8
    Signal NamedSignal_B9               : STD_LOGIC; -- ObjectKind=Net|PrimaryId=B9
    Signal NamedSignal_FEIL             : STD_LOGIC; -- ObjectKind=Net|PrimaryId=FEIL
    Signal NamedSignal_FP_1             : STD_LOGIC; -- ObjectKind=Net|PrimaryId=FP_1
    Signal NamedSignal_FP_2             : STD_LOGIC; -- ObjectKind=Net|PrimaryId=FP_2
    Signal NamedSignal_FP_3             : STD_LOGIC; -- ObjectKind=Net|PrimaryId=FP_3
    Signal NamedSignal_FP_4             : STD_LOGIC; -- ObjectKind=Net|PrimaryId=FP_4
    Signal NamedSignal_FP_5             : STD_LOGIC; -- ObjectKind=Net|PrimaryId=FP_5
    Signal NamedSignal_INTERRUPT        : STD_LOGIC; -- ObjectKind=Net|PrimaryId=INTERRUPT
    Signal NamedSignal_INTERRUPT_BUS    : STD_LOGIC; -- ObjectKind=Net|PrimaryId=INTERRUPT_BUS
    Signal NamedSignal_KNAPP            : STD_LOGIC; -- ObjectKind=Net|PrimaryId=KNAPP
    Signal NamedSignal_KORT_INNSATT     : STD_LOGIC; -- ObjectKind=Net|PrimaryId=KORT_INNSATT
    Signal NamedSignal_KORT_INNSATT_BUS : STD_LOGIC; -- ObjectKind=Net|PrimaryId=KORT_INNSATT_BUS
    Signal NamedSignal_LIMIT_BUS        : STD_LOGIC; -- ObjectKind=Net|PrimaryId=LIMIT_BUS
    Signal NamedSignal_STATUS           : STD_LOGIC; -- ObjectKind=Net|PrimaryId=STATUS
    Signal NamedSignal_TRIGGER_BUS      : STD_LOGIC; -- ObjectKind=Net|PrimaryId=TRIGGER_BUS
    Signal PowerSignal_GND              : STD_LOGIC; -- ObjectKind=Net|PrimaryId=GND
    Signal PowerSignal_VCC_EXTRA        : STD_LOGIC; -- ObjectKind=Net|PrimaryId=VCC_EXTRA
    Signal PowerSignal_VCC_P18V         : STD_LOGIC; -- ObjectKind=Net|PrimaryId=VCC_P18V
    Signal PowerSignal_VCC_P5V0         : STD_LOGIC; -- ObjectKind=Net|PrimaryId=VCC_P5V0

   attribute Database_Table_Name : string;
   attribute Database_Table_Name of J51106 : Label is "altium";
   attribute Database_Table_Name of J51105 : Label is "altium";
   attribute Database_Table_Name of J51104 : Label is "altium";
   attribute Database_Table_Name of J51103 : Label is "altium";
   attribute Database_Table_Name of J51102 : Label is "altium";
   attribute Database_Table_Name of J51101 : Label is "altium";
   attribute Database_Table_Name of J51100 : Label is "altium";

   attribute id : string;
   attribute id of J51106 : Label is "2430";
   attribute id of J51105 : Label is "2430";
   attribute id of J51104 : Label is "2430";
   attribute id of J51103 : Label is "2430";
   attribute id of J51102 : Label is "2430";
   attribute id of J51101 : Label is "2390";
   attribute id of J51100 : Label is "3177";

   attribute navn : string;
   attribute navn of J51106 : Label is "Header 1x3";
   attribute navn of J51105 : Label is "Header 1x3";
   attribute navn of J51104 : Label is "Header 1x3";
   attribute navn of J51103 : Label is "Header 1x3";
   attribute navn of J51102 : Label is "Header 1x3";
   attribute navn of J51101 : Label is "Header Shrouded 2X17P";
   attribute navn of J51100 : Label is "PCIeX1-GF-2D-1000-1K-O36";

   attribute nokkelord : string;
   attribute nokkelord of J51101 : Label is "IDE";

   attribute pakke_opprettet : string;
   attribute pakke_opprettet of J51106 : Label is "13.11.2014 12:31:03";
   attribute pakke_opprettet of J51105 : Label is "13.11.2014 12:31:03";
   attribute pakke_opprettet of J51104 : Label is "13.11.2014 12:31:03";
   attribute pakke_opprettet of J51103 : Label is "13.11.2014 12:31:03";
   attribute pakke_opprettet of J51102 : Label is "13.11.2014 12:31:03";
   attribute pakke_opprettet of J51101 : Label is "12.07.2014 17:05:20";
   attribute pakke_opprettet of J51100 : Label is "07.06.2015 17.49.10";

   attribute pakke_opprettet_av : string;
   attribute pakke_opprettet_av of J51106 : Label is "815";
   attribute pakke_opprettet_av of J51105 : Label is "815";
   attribute pakke_opprettet_av of J51104 : Label is "815";
   attribute pakke_opprettet_av of J51103 : Label is "815";
   attribute pakke_opprettet_av of J51102 : Label is "815";
   attribute pakke_opprettet_av of J51101 : Label is "815";
   attribute pakke_opprettet_av of J51100 : Label is "815";

   attribute pakketype : string;
   attribute pakketype of J51106 : Label is "TH";
   attribute pakketype of J51105 : Label is "TH";
   attribute pakketype of J51104 : Label is "TH";
   attribute pakketype of J51103 : Label is "TH";
   attribute pakketype of J51102 : Label is "TH";
   attribute pakketype of J51101 : Label is "TH";
   attribute pakketype of J51100 : Label is "-";

   attribute pris : string;
   attribute pris of J51106 : Label is "2";
   attribute pris of J51105 : Label is "2";
   attribute pris of J51104 : Label is "2";
   attribute pris of J51103 : Label is "2";
   attribute pris of J51102 : Label is "2";
   attribute pris of J51101 : Label is "10";
   attribute pris of J51100 : Label is "0";

   attribute symbol_opprettet : string;
   attribute symbol_opprettet of J51106 : Label is "13.11.2014 10:59:05";
   attribute symbol_opprettet of J51105 : Label is "13.11.2014 10:59:05";
   attribute symbol_opprettet of J51104 : Label is "13.11.2014 10:59:05";
   attribute symbol_opprettet of J51103 : Label is "13.11.2014 10:59:05";
   attribute symbol_opprettet of J51102 : Label is "13.11.2014 10:59:05";
   attribute symbol_opprettet of J51101 : Label is "12.07.2014 17:03:56";
   attribute symbol_opprettet of J51100 : Label is "06.07.2014 17.26.37";

   attribute symbol_opprettet_av : string;
   attribute symbol_opprettet_av of J51106 : Label is "815";
   attribute symbol_opprettet_av of J51105 : Label is "815";
   attribute symbol_opprettet_av of J51104 : Label is "815";
   attribute symbol_opprettet_av of J51103 : Label is "815";
   attribute symbol_opprettet_av of J51102 : Label is "815";
   attribute symbol_opprettet_av of J51101 : Label is "815";
   attribute symbol_opprettet_av of J51100 : Label is "815";


Begin
    J51106 : X_2430                                          -- ObjectKind=Part|PrimaryId=J51106|SecondaryId=1
      Port Map
      (
        X_1 => PowerSignal_VCC_P5V0,                         -- ObjectKind=Pin|PrimaryId=J51106-1
        X_2 => NamedSignal_KNAPP,                            -- ObjectKind=Pin|PrimaryId=J51106-2
        X_3 => PowerSignal_GND                               -- ObjectKind=Pin|PrimaryId=J51106-3
      );

    J51105 : X_2430                                          -- ObjectKind=Part|PrimaryId=J51105|SecondaryId=1
      Port Map
      (
        X_1 => PowerSignal_VCC_P5V0,                         -- ObjectKind=Pin|PrimaryId=J51105-1
        X_2 => NamedSignal_INTERRUPT,                        -- ObjectKind=Pin|PrimaryId=J51105-2
        X_3 => PowerSignal_GND                               -- ObjectKind=Pin|PrimaryId=J51105-3
      );

    J51104 : X_2430                                          -- ObjectKind=Part|PrimaryId=J51104|SecondaryId=1
      Port Map
      (
        X_1 => PowerSignal_VCC_P5V0,                         -- ObjectKind=Pin|PrimaryId=J51104-1
        X_2 => NamedSignal_STATUS,                           -- ObjectKind=Pin|PrimaryId=J51104-2
        X_3 => PowerSignal_GND                               -- ObjectKind=Pin|PrimaryId=J51104-3
      );

    J51103 : X_2430                                          -- ObjectKind=Part|PrimaryId=J51103|SecondaryId=1
      Port Map
      (
        X_1 => PowerSignal_VCC_P5V0,                         -- ObjectKind=Pin|PrimaryId=J51103-1
        X_2 => NamedSignal_FEIL,                             -- ObjectKind=Pin|PrimaryId=J51103-2
        X_3 => PowerSignal_GND                               -- ObjectKind=Pin|PrimaryId=J51103-3
      );

    J51102 : X_2430                                          -- ObjectKind=Part|PrimaryId=J51102|SecondaryId=1
      Port Map
      (
        X_1 => PowerSignal_VCC_P5V0,                         -- ObjectKind=Pin|PrimaryId=J51102-1
        X_2 => NamedSignal_KORT_INNSATT,                     -- ObjectKind=Pin|PrimaryId=J51102-2
        X_3 => PowerSignal_GND                               -- ObjectKind=Pin|PrimaryId=J51102-3
      );

    J51101 : X_2390                                          -- ObjectKind=Part|PrimaryId=J51101|SecondaryId=1
      Port Map
      (
        X_1  => NamedSignal_KORT_INNSATT,                    -- ObjectKind=Pin|PrimaryId=J51101-1
        X_2  => NamedSignal_KORT_INNSATT_BUS,                -- ObjectKind=Pin|PrimaryId=J51101-2
        X_3  => NamedSignal_FEIL,                            -- ObjectKind=Pin|PrimaryId=J51101-3
        X_4  => NamedSignal_TRIGGER_BUS,                     -- ObjectKind=Pin|PrimaryId=J51101-4
        X_5  => NamedSignal_STATUS,                          -- ObjectKind=Pin|PrimaryId=J51101-5
        X_6  => NamedSignal_LIMIT_BUS,                       -- ObjectKind=Pin|PrimaryId=J51101-6
        X_7  => NamedSignal_INTERRUPT,                       -- ObjectKind=Pin|PrimaryId=J51101-7
        X_8  => NamedSignal_INTERRUPT_BUS,                   -- ObjectKind=Pin|PrimaryId=J51101-8
        X_9  => NamedSignal_KNAPP,                           -- ObjectKind=Pin|PrimaryId=J51101-9
        X_10 => NamedSignal_B5,                              -- ObjectKind=Pin|PrimaryId=J51101-10
        X_11 => NamedSignal_FP_1,                            -- ObjectKind=Pin|PrimaryId=J51101-11
        X_12 => NamedSignal_B6,                              -- ObjectKind=Pin|PrimaryId=J51101-12
        X_13 => NamedSignal_FP_2,                            -- ObjectKind=Pin|PrimaryId=J51101-13
        X_14 => NamedSignal_B7,                              -- ObjectKind=Pin|PrimaryId=J51101-14
        X_15 => NamedSignal_FP_3,                            -- ObjectKind=Pin|PrimaryId=J51101-15
        X_16 => NamedSignal_B8,                              -- ObjectKind=Pin|PrimaryId=J51101-16
        X_17 => NamedSignal_FP_4,                            -- ObjectKind=Pin|PrimaryId=J51101-17
        X_18 => NamedSignal_B9,                              -- ObjectKind=Pin|PrimaryId=J51101-18
        X_19 => NamedSignal_FP_5,                            -- ObjectKind=Pin|PrimaryId=J51101-19
        X_20 => NamedSignal_B10,                             -- ObjectKind=Pin|PrimaryId=J51101-20
        X_21 => NamedSignal_AUX1_A,                          -- ObjectKind=Pin|PrimaryId=J51101-21
        X_22 => NamedSignal_B11,                             -- ObjectKind=Pin|PrimaryId=J51101-22
        X_23 => NamedSignal_AUX1_B,                          -- ObjectKind=Pin|PrimaryId=J51101-23
        X_24 => NamedSignal_B12,                             -- ObjectKind=Pin|PrimaryId=J51101-24
        X_25 => NamedSignal_AUX2_A,                          -- ObjectKind=Pin|PrimaryId=J51101-25
        X_26 => NamedSignal_B13,                             -- ObjectKind=Pin|PrimaryId=J51101-26
        X_27 => NamedSignal_AUX2_B,                          -- ObjectKind=Pin|PrimaryId=J51101-27
        X_28 => NamedSignal_B14,                             -- ObjectKind=Pin|PrimaryId=J51101-28
        X_29 => PowerSignal_GND,                             -- ObjectKind=Pin|PrimaryId=J51101-29
        X_30 => PowerSignal_GND,                             -- ObjectKind=Pin|PrimaryId=J51101-30
        X_31 => PowerSignal_VCC_EXTRA,                       -- ObjectKind=Pin|PrimaryId=J51101-31
        X_32 => PowerSignal_GND,                             -- ObjectKind=Pin|PrimaryId=J51101-32
        X_33 => PowerSignal_VCC_P5V0,                        -- ObjectKind=Pin|PrimaryId=J51101-33
        X_34 => PowerSignal_VCC_P18V                         -- ObjectKind=Pin|PrimaryId=J51101-34
      );

    J51100 : X_3177                                          -- ObjectKind=Part|PrimaryId=J51100|SecondaryId=1
      Port Map
      (
        A1  => NamedSignal_KORT_INNSATT,                     -- ObjectKind=Pin|PrimaryId=J51100-A1
        A2  => NamedSignal_FEIL,                             -- ObjectKind=Pin|PrimaryId=J51100-A2
        A3  => NamedSignal_STATUS,                           -- ObjectKind=Pin|PrimaryId=J51100-A3
        A4  => NamedSignal_INTERRUPT,                        -- ObjectKind=Pin|PrimaryId=J51100-A4
        A5  => NamedSignal_KNAPP,                            -- ObjectKind=Pin|PrimaryId=J51100-A5
        A6  => NamedSignal_FP_1,                             -- ObjectKind=Pin|PrimaryId=J51100-A6
        A7  => NamedSignal_FP_2,                             -- ObjectKind=Pin|PrimaryId=J51100-A7
        A8  => NamedSignal_FP_3,                             -- ObjectKind=Pin|PrimaryId=J51100-A8
        A9  => NamedSignal_FP_4,                             -- ObjectKind=Pin|PrimaryId=J51100-A9
        A10 => NamedSignal_FP_5,                             -- ObjectKind=Pin|PrimaryId=J51100-A10
        A11 => NamedSignal_AUX1_A,                           -- ObjectKind=Pin|PrimaryId=J51100-A11
        A12 => NamedSignal_AUX1_B,                           -- ObjectKind=Pin|PrimaryId=J51100-A12
        A13 => NamedSignal_AUX2_A,                           -- ObjectKind=Pin|PrimaryId=J51100-A13
        A14 => NamedSignal_AUX2_B,                           -- ObjectKind=Pin|PrimaryId=J51100-A14
        A15 => PowerSignal_GND,                              -- ObjectKind=Pin|PrimaryId=J51100-A15
        A16 => PowerSignal_VCC_EXTRA,                        -- ObjectKind=Pin|PrimaryId=J51100-A16
        A17 => PowerSignal_VCC_P5V0,                         -- ObjectKind=Pin|PrimaryId=J51100-A17
        A18 => PowerSignal_VCC_P18V,                         -- ObjectKind=Pin|PrimaryId=J51100-A18
        B1  => NamedSignal_KORT_INNSATT_BUS,                 -- ObjectKind=Pin|PrimaryId=J51100-B1
        B2  => NamedSignal_TRIGGER_BUS,                      -- ObjectKind=Pin|PrimaryId=J51100-B2
        B3  => NamedSignal_LIMIT_BUS,                        -- ObjectKind=Pin|PrimaryId=J51100-B3
        B4  => NamedSignal_INTERRUPT_BUS,                    -- ObjectKind=Pin|PrimaryId=J51100-B4
        B5  => NamedSignal_B5,                               -- ObjectKind=Pin|PrimaryId=J51100-B5
        B6  => NamedSignal_B6,                               -- ObjectKind=Pin|PrimaryId=J51100-B6
        B7  => NamedSignal_B7,                               -- ObjectKind=Pin|PrimaryId=J51100-B7
        B8  => NamedSignal_B8,                               -- ObjectKind=Pin|PrimaryId=J51100-B8
        B9  => NamedSignal_B9,                               -- ObjectKind=Pin|PrimaryId=J51100-B9
        B10 => NamedSignal_B10,                              -- ObjectKind=Pin|PrimaryId=J51100-B10
        B11 => NamedSignal_B11,                              -- ObjectKind=Pin|PrimaryId=J51100-B11
        B12 => NamedSignal_B12,                              -- ObjectKind=Pin|PrimaryId=J51100-B12
        B13 => NamedSignal_B13,                              -- ObjectKind=Pin|PrimaryId=J51100-B13
        B14 => NamedSignal_B14,                              -- ObjectKind=Pin|PrimaryId=J51100-B14
        B15 => PowerSignal_GND,                              -- ObjectKind=Pin|PrimaryId=J51100-B15
        B16 => PowerSignal_VCC_EXTRA,                        -- ObjectKind=Pin|PrimaryId=J51100-B16
        B17 => PowerSignal_VCC_P5V0,                         -- ObjectKind=Pin|PrimaryId=J51100-B17
        B18 => PowerSignal_VCC_P18V                          -- ObjectKind=Pin|PrimaryId=J51100-B18
      );

    -- Signal Assignments
    ---------------------
    PowerSignal_GND <= '0'; -- ObjectKind=Net|PrimaryId=GND

End Structure;
------------------------------------------------------------
