Cable89/tesla-driver/05_Hardware/TK500_Driver/ProjectOutputs/TK513_Limiter.VHD

------------------------------------------------------------
-- VHDL TK513_Limiter
-- 2017 1 13 17 4 5
-- Created By "DXP VHDL Generator"
-- "Copyright (c) 2002-2014 Altium Limited"
-- Product Version: 16.0.6.282
------------------------------------------------------------

------------------------------------------------------------
-- VHDL TK513_Limiter
------------------------------------------------------------

Library IEEE;
Use     IEEE.std_logic_1164.all;

Entity TK513_Limiter Is
  port
  (
    LIMIT   : Out   STD_LOGIC;                               -- ObjectKind=Port|PrimaryId=LIMIT
    TRIGGER : In    STD_LOGIC                                -- ObjectKind=Port|PrimaryId=TRIGGER
  );
  attribute MacroCell : boolean;

End TK513_Limiter;
------------------------------------------------------------

------------------------------------------------------------
Architecture Structure Of TK513_Limiter Is
   Component X_2226                                          -- ObjectKind=Part|PrimaryId=J51303|SecondaryId=1
      port
      (
        X_1 : inout STD_LOGIC;                               -- ObjectKind=Pin|PrimaryId=J51303-1
        X_2 : inout STD_LOGIC;                               -- ObjectKind=Pin|PrimaryId=J51303-2
        X_3 : inout STD_LOGIC                                -- ObjectKind=Pin|PrimaryId=J51303-3
      );
   End Component;

   Component X_2227                                          -- ObjectKind=Part|PrimaryId=J51300|SecondaryId=1
      port
      (
        X_1 : inout STD_LOGIC;                               -- ObjectKind=Pin|PrimaryId=J51300-1
        X_2 : inout STD_LOGIC                                -- ObjectKind=Pin|PrimaryId=J51300-2
      );
   End Component;

   Component X_2369                                          -- ObjectKind=Part|PrimaryId=D51300|SecondaryId=1
      port
      (
        X_1 : inout STD_LOGIC;                               -- ObjectKind=Pin|PrimaryId=D51300-1
        X_2 : inout STD_LOGIC                                -- ObjectKind=Pin|PrimaryId=D51300-2
      );
   End Component;

   Component X_2372                                          -- ObjectKind=Part|PrimaryId=U51302|SecondaryId=1
      port
      (
        X_1 : inout STD_LOGIC;                               -- ObjectKind=Pin|PrimaryId=U51302-1
        X_2 : inout STD_LOGIC                                -- ObjectKind=Pin|PrimaryId=U51302-2
      );
   End Component;

   Component X_2373                                          -- ObjectKind=Part|PrimaryId=U51300|SecondaryId=1
      port
      (
        X_1 : inout STD_LOGIC;                               -- ObjectKind=Pin|PrimaryId=U51300-1
        X_2 : inout STD_LOGIC;                               -- ObjectKind=Pin|PrimaryId=U51300-2
        X_3 : inout STD_LOGIC;                               -- ObjectKind=Pin|PrimaryId=U51300-3
        X_4 : inout STD_LOGIC;                               -- ObjectKind=Pin|PrimaryId=U51300-4
        X_5 : inout STD_LOGIC;                               -- ObjectKind=Pin|PrimaryId=U51300-5
        X_6 : inout STD_LOGIC                                -- ObjectKind=Pin|PrimaryId=U51300-6
      );
   End Component;

   Component X_2379                                          -- ObjectKind=Part|PrimaryId=U51303|SecondaryId=1
      port
      (
        X_1 : inout STD_LOGIC;                               -- ObjectKind=Pin|PrimaryId=U51303-1
        X_2 : inout STD_LOGIC;                               -- ObjectKind=Pin|PrimaryId=U51303-2
        X_3 : inout STD_LOGIC;                               -- ObjectKind=Pin|PrimaryId=U51303-3
        X_4 : inout STD_LOGIC;                               -- ObjectKind=Pin|PrimaryId=U51303-4
        X_5 : inout STD_LOGIC;                               -- ObjectKind=Pin|PrimaryId=U51303-5
        X_6 : inout STD_LOGIC;                               -- ObjectKind=Pin|PrimaryId=U51303-6
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
      port
      (
        X_1 : inout STD_LOGIC;                               -- ObjectKind=Pin|PrimaryId=J51302-1
        X_2 : inout STD_LOGIC                                -- ObjectKind=Pin|PrimaryId=J51302-2
      );
   End Component;

   Component LM311                                           -- ObjectKind=Part|PrimaryId=U51301|SecondaryId=1
      port
      (
        X_1 : inout STD_LOGIC;                               -- ObjectKind=Pin|PrimaryId=U51301-1
        X_2 : in    STD_LOGIC;                               -- ObjectKind=Pin|PrimaryId=U51301-2
        X_3 : in    STD_LOGIC;                               -- ObjectKind=Pin|PrimaryId=U51301-3
        X_4 : inout STD_LOGIC;                               -- ObjectKind=Pin|PrimaryId=U51301-4
        X_5 : inout STD_LOGIC;                               -- ObjectKind=Pin|PrimaryId=U51301-5
        X_6 : inout STD_LOGIC;                               -- ObjectKind=Pin|PrimaryId=U51301-6
        X_7 : out   STD_LOGIC;                               -- ObjectKind=Pin|PrimaryId=U51301-7
        X_8 : inout STD_LOGIC                                -- ObjectKind=Pin|PrimaryId=U51301-8
      );
   End Component;


    Signal NamedSignal_AUX1_A           : STD_LOGIC; -- ObjectKind=Net|PrimaryId=AUX1_A
    Signal NamedSignal_AUX1_B           : STD_LOGIC; -- ObjectKind=Net|PrimaryId=AUX1_B
    Signal NamedSignal_AUX2_A           : STD_LOGIC; -- ObjectKind=Net|PrimaryId=AUX2_A
    Signal NamedSignal_AUX2_B           : STD_LOGIC; -- ObjectKind=Net|PrimaryId=AUX2_B
    Signal NamedSignal_B10              : STD_LOGIC; -- ObjectKind=Net|PrimaryId=B10
    Signal NamedSignal_B11              : STD_LOGIC; -- ObjectKind=Net|PrimaryId=B11
    Signal NamedSignal_B12              : STD_LOGIC; -- ObjectKind=Net|PrimaryId=B12
    Signal NamedSignal_B13              : STD_LOGIC; -- ObjectKind=Net|PrimaryId=B13
    Signal NamedSignal_B14              : STD_LOGIC; -- ObjectKind=Net|PrimaryId=B14
    Signal NamedSignal_B5               : STD_LOGIC; -- ObjectKind=Net|PrimaryId=B5
    Signal NamedSignal_B6               : STD_LOGIC; -- ObjectKind=Net|PrimaryId=B6
    Signal NamedSignal_B7               : STD_LOGIC; -- ObjectKind=Net|PrimaryId=B7
    Signal NamedSignal_B8               : STD_LOGIC; -- ObjectKind=Net|PrimaryId=B8
    Signal NamedSignal_B9               : STD_LOGIC; -- ObjectKind=Net|PrimaryId=B9
    Signal NamedSignal_DC_IN            : STD_LOGIC; -- ObjectKind=Net|PrimaryId=DC_IN
    Signal NamedSignal_FP_1             : STD_LOGIC; -- ObjectKind=Net|PrimaryId=FP_1
    Signal NamedSignal_FP_2             : STD_LOGIC; -- ObjectKind=Net|PrimaryId=FP_2
    Signal NamedSignal_FP_3             : STD_LOGIC; -- ObjectKind=Net|PrimaryId=FP_3
    Signal NamedSignal_FP_4             : STD_LOGIC; -- ObjectKind=Net|PrimaryId=FP_4
    Signal NamedSignal_FP_5             : STD_LOGIC; -- ObjectKind=Net|PrimaryId=FP_5
    Signal NamedSignal_INTERRUPT_BUS    : STD_LOGIC; -- ObjectKind=Net|PrimaryId=INTERRUPT_BUS
    Signal NamedSignal_KORT_INNSATT_BUS : STD_LOGIC; -- ObjectKind=Net|PrimaryId=KORT_INNSATT_BUS
    Signal NamedSignal_LED              : STD_LOGIC; -- ObjectKind=Net|PrimaryId=LED
    Signal NamedSignal_LIMIT_BUS        : STD_LOGIC; -- ObjectKind=Net|PrimaryId=LIMIT_BUS
    Signal NamedSignal_LIMITER_OUT      : STD_LOGIC; -- ObjectKind=Net|PrimaryId=LIMITER_OUT
    Signal NamedSignal_POT              : STD_LOGIC; -- ObjectKind=Net|PrimaryId=POT
    Signal NamedSignal_TRIGGER_BUS      : STD_LOGIC; -- ObjectKind=Net|PrimaryId=TRIGGER_BUS
    Signal PinSignal_J51302_1           : STD_LOGIC; -- ObjectKind=Net|PrimaryId=NetJ51302_1
    Signal PinSignal_J51302_2           : STD_LOGIC; -- ObjectKind=Net|PrimaryId=NetJ51302_2
    Signal PinSignal_J51303_1           : STD_LOGIC; -- ObjectKind=Net|PrimaryId=NetJ51303_1
    Signal PinSignal_J51304_2           : STD_LOGIC; -- ObjectKind=Net|PrimaryId=NetJ51304_2
    Signal PinSignal_R51303_1           : STD_LOGIC; -- ObjectKind=Net|PrimaryId=NetR51303_1
    Signal PinSignal_R51304_1           : STD_LOGIC; -- ObjectKind=Net|PrimaryId=NetR51304_1
    Signal PinSignal_R51305_1           : STD_LOGIC; -- ObjectKind=Net|PrimaryId=NetR51305_1
    Signal PinSignal_U51300_11          : STD_LOGIC; -- ObjectKind=Net|PrimaryId=NetU51300_11
    Signal PinSignal_U51300_9           : STD_LOGIC; -- ObjectKind=Net|PrimaryId=NetU51300_9
    Signal PinSignal_U51301_5           : STD_LOGIC; -- ObjectKind=Net|PrimaryId=NetU51301_5
    Signal PinSignal_U51301_7           : STD_LOGIC; -- ObjectKind=Net|PrimaryId=NetC51300_2
    Signal PinSignal_U51302_2           : STD_LOGIC; -- ObjectKind=Net|PrimaryId=NetU51302_2
    Signal PowerSignal_GND              : STD_LOGIC; -- ObjectKind=Net|PrimaryId=GND
    Signal PowerSignal_PLUS5V           : STD_LOGIC; -- ObjectKind=Net|PrimaryId=+5V
    Signal PowerSignal_VCC_EXTRA        : STD_LOGIC; -- ObjectKind=Net|PrimaryId=VCC_EXTRA
    Signal PowerSignal_VCC_P18V         : STD_LOGIC; -- ObjectKind=Net|PrimaryId=VCC_P18V
    Signal PowerSignal_VCC_P5V0         : STD_LOGIC; -- ObjectKind=Net|PrimaryId=VCC_P5V0

   attribute antall : string;
   attribute antall of R51306 : Label is "100";
   attribute antall of R51305 : Label is "100";
   attribute antall of R51304 : Label is "100";
   attribute antall of R51303 : Label is "100";
   attribute antall of R51302 : Label is "100";
   attribute antall of R51300 : Label is "100";
   attribute antall of J51305 : Label is "100";
   attribute antall of J51304 : Label is "100";
   attribute antall of J51303 : Label is "100";
   attribute antall of J51300 : Label is "100";
   attribute antall of D51303 : Label is "8";
   attribute antall of D51302 : Label is "8";
   attribute antall of D51301 : Label is "8";
   attribute antall of D51300 : Label is "8";

   attribute beskrivelse : string;
   attribute beskrivelse of U51302 : Label is "Hex Schmitt trigger";
   attribute beskrivelse of U51300 : Label is "Dual D flip flop";
   attribute beskrivelse of D51303 : Label is "Schottkydiode, 1A, 40V";
   attribute beskrivelse of D51302 : Label is "Schottkydiode, 1A, 40V";
   attribute beskrivelse of D51301 : Label is "Schottkydiode, 1A, 40V";
   attribute beskrivelse of D51300 : Label is "Schottkydiode, 1A, 40V";

   attribute CaseMINUSEIA : string;
   attribute CaseMINUSEIA of C51305 : Label is "0805";
   attribute CaseMINUSEIA of C51304 : Label is "0805";
   attribute CaseMINUSEIA of C51301 : Label is "0805";
   attribute CaseMINUSEIA of C51300 : Label is "0805";

   attribute CaseMINUSMetric : string;
   attribute CaseMINUSMetric of C51305 : Label is "2012";
   attribute CaseMINUSMetric of C51304 : Label is "2012";
   attribute CaseMINUSMetric of C51301 : Label is "2012";
   attribute CaseMINUSMetric of C51300 : Label is "2012";

   attribute Database_Table_Name : string;
   attribute Database_Table_Name of U51303 : Label is "altium";
   attribute Database_Table_Name of U51302 : Label is "altium_Logikk";
   attribute Database_Table_Name of U51300 : Label is "altium_Logikk";
   attribute Database_Table_Name of R51306 : Label is "altium_Motstander";
   attribute Database_Table_Name of R51305 : Label is "altium_Motstander";
   attribute Database_Table_Name of R51304 : Label is "altium_Motstander";
   attribute Database_Table_Name of R51303 : Label is "altium_Motstander";
   attribute Database_Table_Name of R51302 : Label is "altium_Motstander";
   attribute Database_Table_Name of R51301 : Label is "altium_Motstander";
   attribute Database_Table_Name of R51300 : Label is "altium_Motstander";
   attribute Database_Table_Name of J51305 : Label is "altium";
   attribute Database_Table_Name of J51304 : Label is "altium";
   attribute Database_Table_Name of J51303 : Label is "altium";
   attribute Database_Table_Name of J51300 : Label is "altium";
   attribute Database_Table_Name of J51100 : Label is "altium";
   attribute Database_Table_Name of D51303 : Label is "altium_Dioder";
   attribute Database_Table_Name of D51302 : Label is "altium_Dioder";
   attribute Database_Table_Name of D51301 : Label is "altium_Dioder";
   attribute Database_Table_Name of D51300 : Label is "altium_Dioder";
   attribute Database_Table_Name of C51303 : Label is "altium_Kondensatorer";
   attribute Database_Table_Name of C51302 : Label is "altium_Kondensatorer";

   attribute dybde : string;
   attribute dybde of R51306 : Label is "96";
   attribute dybde of R51305 : Label is "36";
   attribute dybde of R51304 : Label is "48";
   attribute dybde of R51303 : Label is "36";
   attribute dybde of R51302 : Label is "48";
   attribute dybde of R51300 : Label is "24";
   attribute dybde of J51305 : Label is "0";
   attribute dybde of J51304 : Label is "0";
   attribute dybde of J51303 : Label is "0";
   attribute dybde of J51300 : Label is "0";
   attribute dybde of D51303 : Label is "0";
   attribute dybde of D51302 : Label is "0";
   attribute dybde of D51301 : Label is "0";
   attribute dybde of D51300 : Label is "0";

   attribute hylle : string;
   attribute hylle of R51306 : Label is "6";
   attribute hylle of R51305 : Label is "6";
   attribute hylle of R51304 : Label is "6";
   attribute hylle of R51303 : Label is "6";
   attribute hylle of R51302 : Label is "6";
   attribute hylle of R51300 : Label is "6";
   attribute hylle of J51305 : Label is "10";
   attribute hylle of J51304 : Label is "10";
   attribute hylle of J51303 : Label is "10";
   attribute hylle of J51300 : Label is "10";
   attribute hylle of D51303 : Label is "6";
   attribute hylle of D51302 : Label is "6";
   attribute hylle of D51301 : Label is "6";
   attribute hylle of D51300 : Label is "6";

   attribute id : string;
   attribute id of U51303 : Label is "2379";
   attribute id of U51302 : Label is "2372";
   attribute id of U51300 : Label is "2373";
   attribute id of R51306 : Label is "2384";
   attribute id of R51305 : Label is "2448";
   attribute id of R51304 : Label is "3441";
   attribute id of R51303 : Label is "2448";
   attribute id of R51302 : Label is "3441";
   attribute id of R51301 : Label is "3585";
   attribute id of R51300 : Label is "3416";
   attribute id of J51305 : Label is "2227";
   attribute id of J51304 : Label is "2227";
   attribute id of J51303 : Label is "2226";
   attribute id of J51300 : Label is "2227";
   attribute id of J51100 : Label is "3177";
   attribute id of D51303 : Label is "2369";
   attribute id of D51302 : Label is "2369";
   attribute id of D51301 : Label is "2369";
   attribute id of D51300 : Label is "2369";
   attribute id of C51303 : Label is "3583";
   attribute id of C51302 : Label is "3028";

   attribute kolonne : string;
   attribute kolonne of R51306 : Label is "0";
   attribute kolonne of R51305 : Label is "0";
   attribute kolonne of R51304 : Label is "0";
   attribute kolonne of R51303 : Label is "0";
   attribute kolonne of R51302 : Label is "0";
   attribute kolonne of R51300 : Label is "0";
   attribute kolonne of J51305 : Label is "0";
   attribute kolonne of J51304 : Label is "0";
   attribute kolonne of J51303 : Label is "1";
   attribute kolonne of J51300 : Label is "0";
   attribute kolonne of D51303 : Label is "2";
   attribute kolonne of D51302 : Label is "2";
   attribute kolonne of D51301 : Label is "2";
   attribute kolonne of D51300 : Label is "2";

   attribute lager_type : string;
   attribute lager_type of R51306 : Label is "Fremlager";
   attribute lager_type of R51305 : Label is "Fremlager";
   attribute lager_type of R51304 : Label is "Fremlager";
   attribute lager_type of R51303 : Label is "Fremlager";
   attribute lager_type of R51302 : Label is "Fremlager";
   attribute lager_type of R51300 : Label is "Fremlager";
   attribute lager_type of J51305 : Label is "Fremlager";
   attribute lager_type of J51304 : Label is "Fremlager";
   attribute lager_type of J51303 : Label is "Fremlager";
   attribute lager_type of J51300 : Label is "Fremlager";
   attribute lager_type of D51303 : Label is "Fremlager";
   attribute lager_type of D51302 : Label is "Fremlager";
   attribute lager_type of D51301 : Label is "Fremlager";
   attribute lager_type of D51300 : Label is "Fremlager";

   attribute leverandor : string;
   attribute leverandor of U51303 : Label is "Farnell";
   attribute leverandor of U51302 : Label is "Farnell";
   attribute leverandor of U51300 : Label is "Farnell";
   attribute leverandor of D51303 : Label is "Farnell";
   attribute leverandor of D51302 : Label is "Farnell";
   attribute leverandor of D51301 : Label is "Farnell";
   attribute leverandor of D51300 : Label is "Farnell";
   attribute leverandor of C51303 : Label is "Farnell";
   attribute leverandor of C51302 : Label is "Farnell";

   attribute leverandor_varenr : string;
   attribute leverandor_varenr of U51303 : Label is "1086672";
   attribute leverandor_varenr of U51302 : Label is "1607772";
   attribute leverandor_varenr of U51300 : Label is "9591680";
   attribute leverandor_varenr of D51303 : Label is "7429304";
   attribute leverandor_varenr of D51302 : Label is "7429304";
   attribute leverandor_varenr of D51301 : Label is "7429304";
   attribute leverandor_varenr of D51300 : Label is "7429304";
   attribute leverandor_varenr of C51303 : Label is "1845762";
   attribute leverandor_varenr of C51302 : Label is "1759122";

   attribute Max_Thickness : string;
   attribute Max_Thickness of C51305 : Label is "1 mm";
   attribute Max_Thickness of C51304 : Label is "1 mm";
   attribute Max_Thickness of C51301 : Label is "1 mm";
   attribute Max_Thickness of C51300 : Label is "1 mm";

   attribute navn : string;
   attribute navn of U51303 : Label is "MOCD207R2M";
   attribute navn of U51302 : Label is "74HC14";
   attribute navn of U51300 : Label is "74HC74";
   attribute navn of R51306 : Label is "100k";
   attribute navn of R51305 : Label is "330R";
   attribute navn of R51304 : Label is "1k";
   attribute navn of R51303 : Label is "330R";
   attribute navn of R51302 : Label is "1k";
   attribute navn of R51301 : Label is "10R";
   attribute navn of R51300 : Label is "100R";
   attribute navn of J51305 : Label is "JST 2pin";
   attribute navn of J51304 : Label is "JST 2pin";
   attribute navn of J51303 : Label is "JST 3pin";
   attribute navn of J51300 : Label is "JST 2pin";
   attribute navn of J51100 : Label is "PCIeX1-GF-2D-1000-1K-O36";
   attribute navn of D51303 : Label is "1N5819";
   attribute navn of D51302 : Label is "1N5819";
   attribute navn of D51301 : Label is "1N5819";
   attribute navn of D51300 : Label is "1N5819";
   attribute navn of C51303 : Label is "10uF";
   attribute navn of C51302 : Label is "100nF";
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
